gitberthe/BertheVario213/CompZoneAerienne/zones_gnuplot/000.png

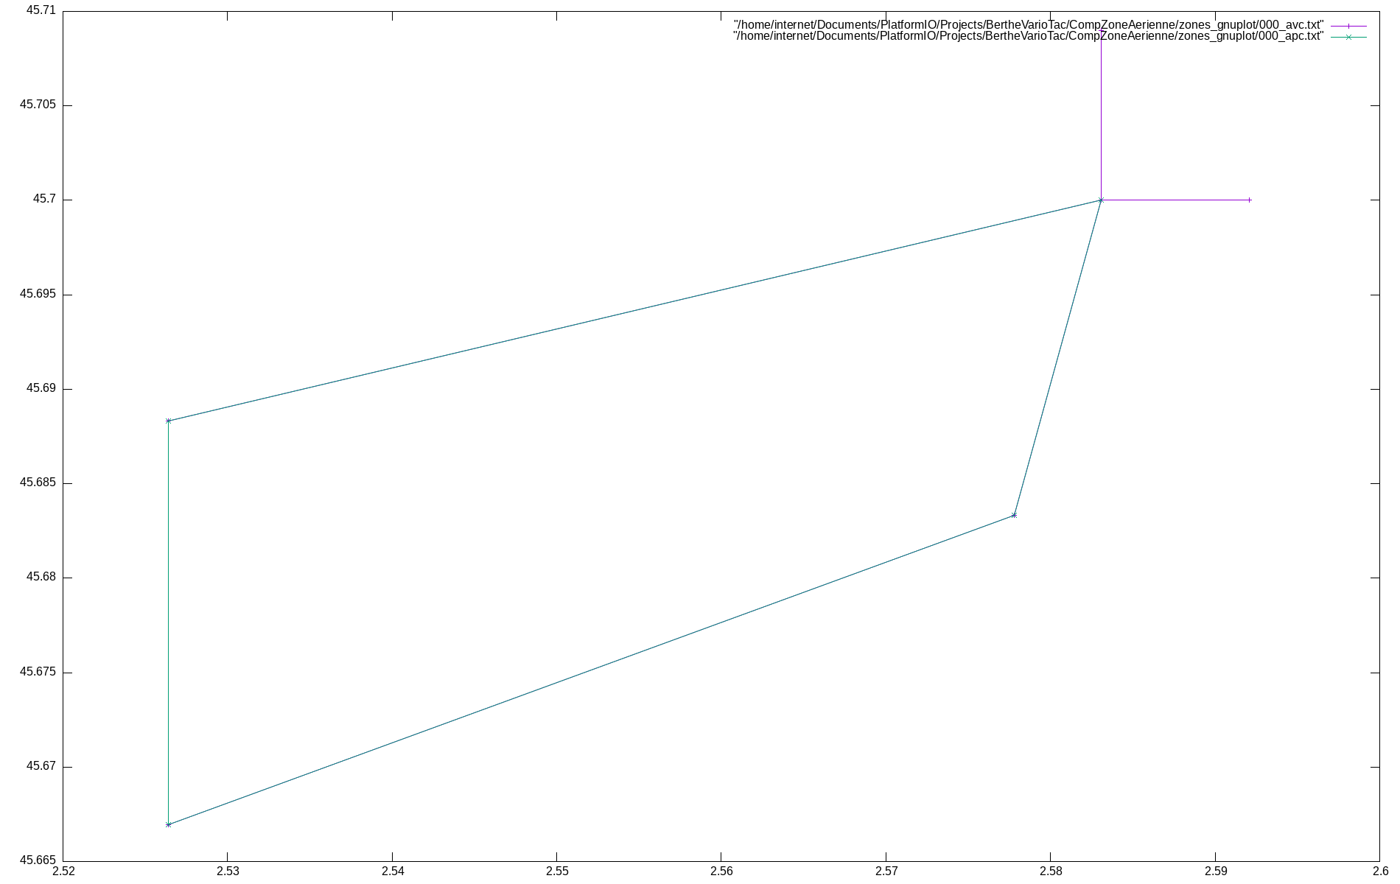
CompZoneAerienne/zones_gnuplot/000.png
