gitberthe/BertheVario213/CompZoneAerienne/zones_gnuplot/001.png

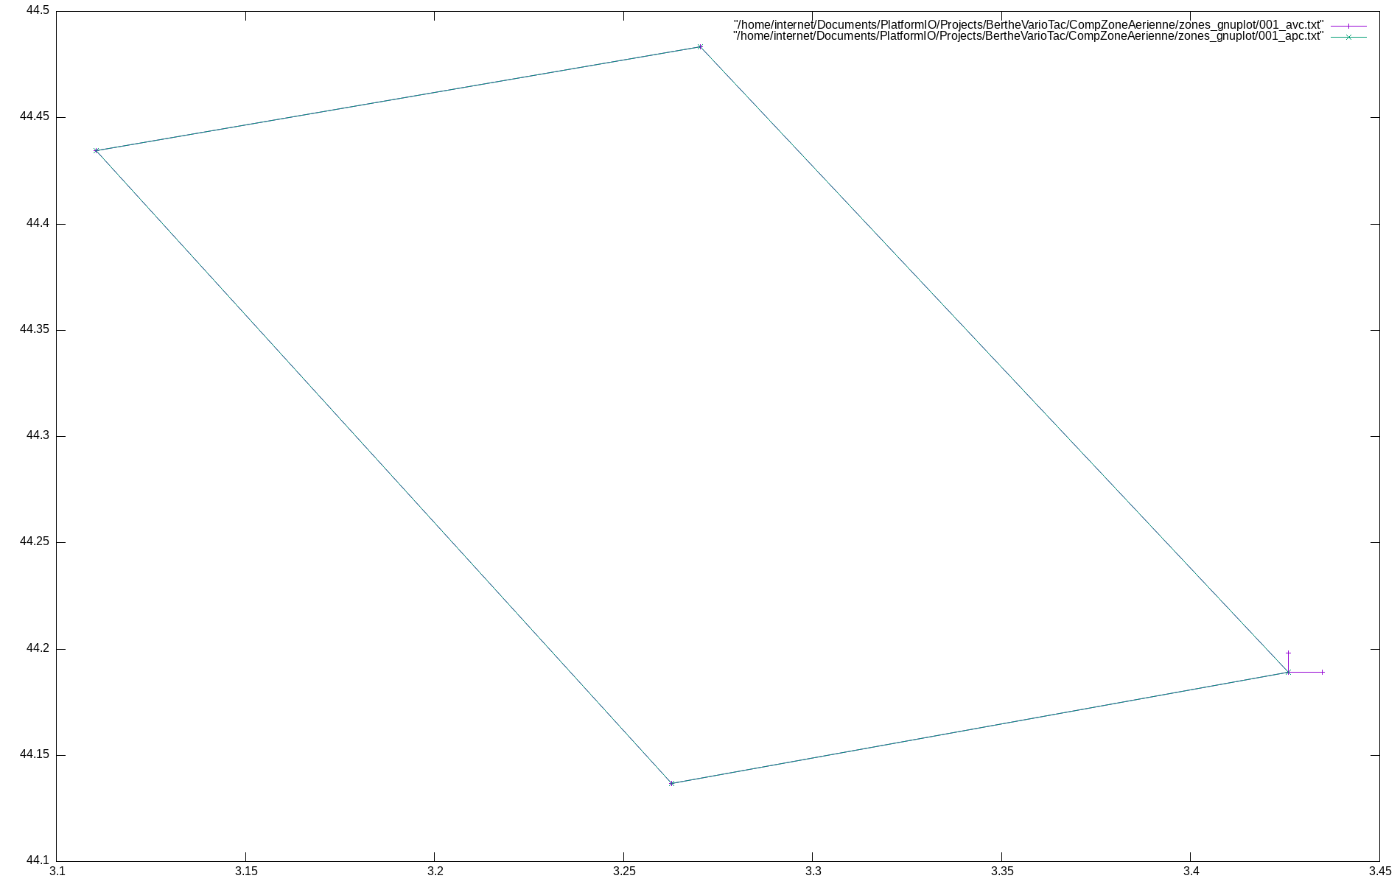
CompZoneAerienne/zones_gnuplot/001.png
