gitberthe/BertheVario213/CompZoneAerienne/zones_gnuplot/002.png

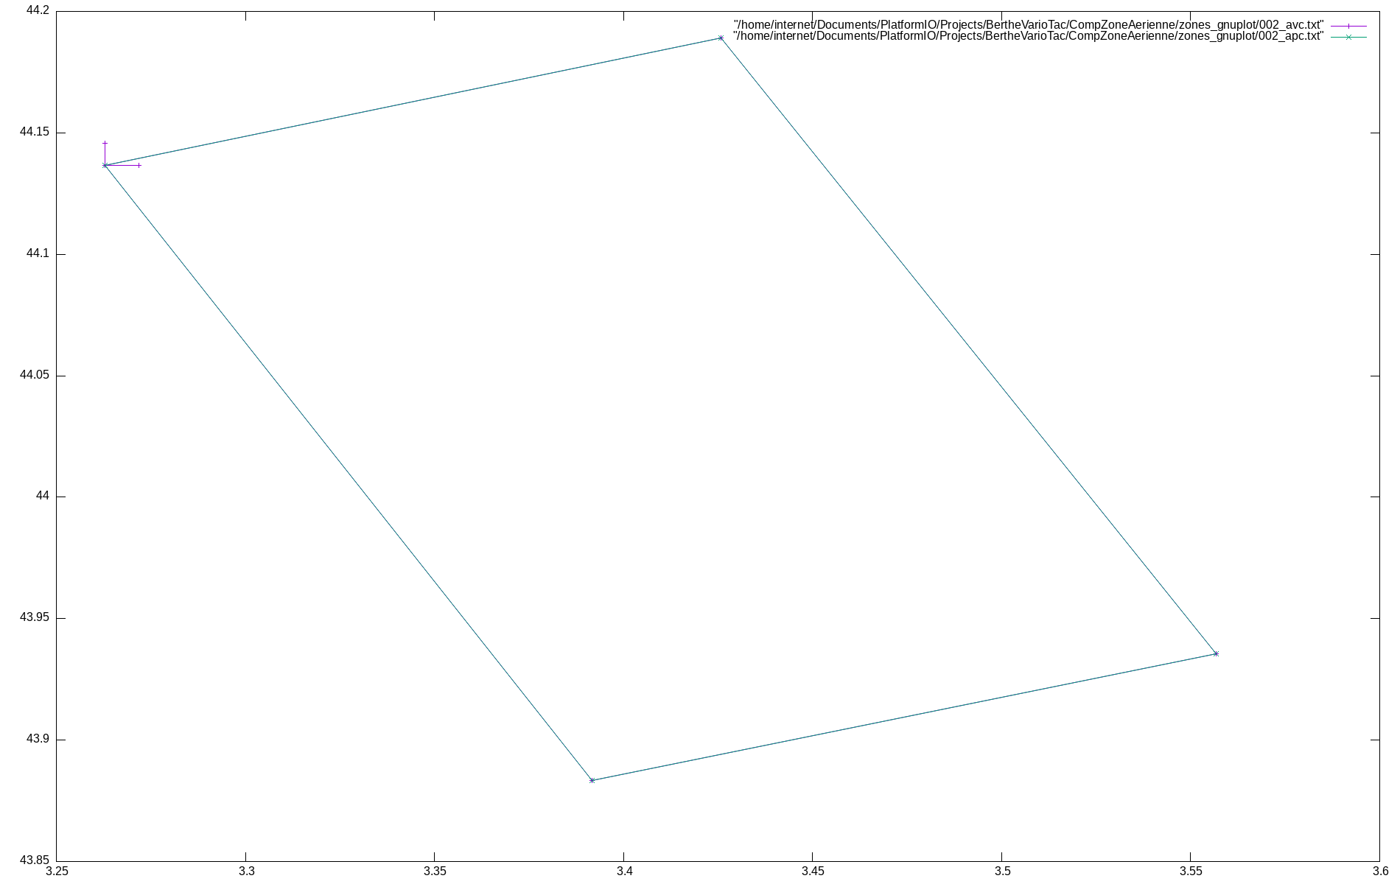
CompZoneAerienne/zones_gnuplot/002.png
