gitberthe/BertheVario213/CompZoneAerienne/zones_gnuplot/004.png

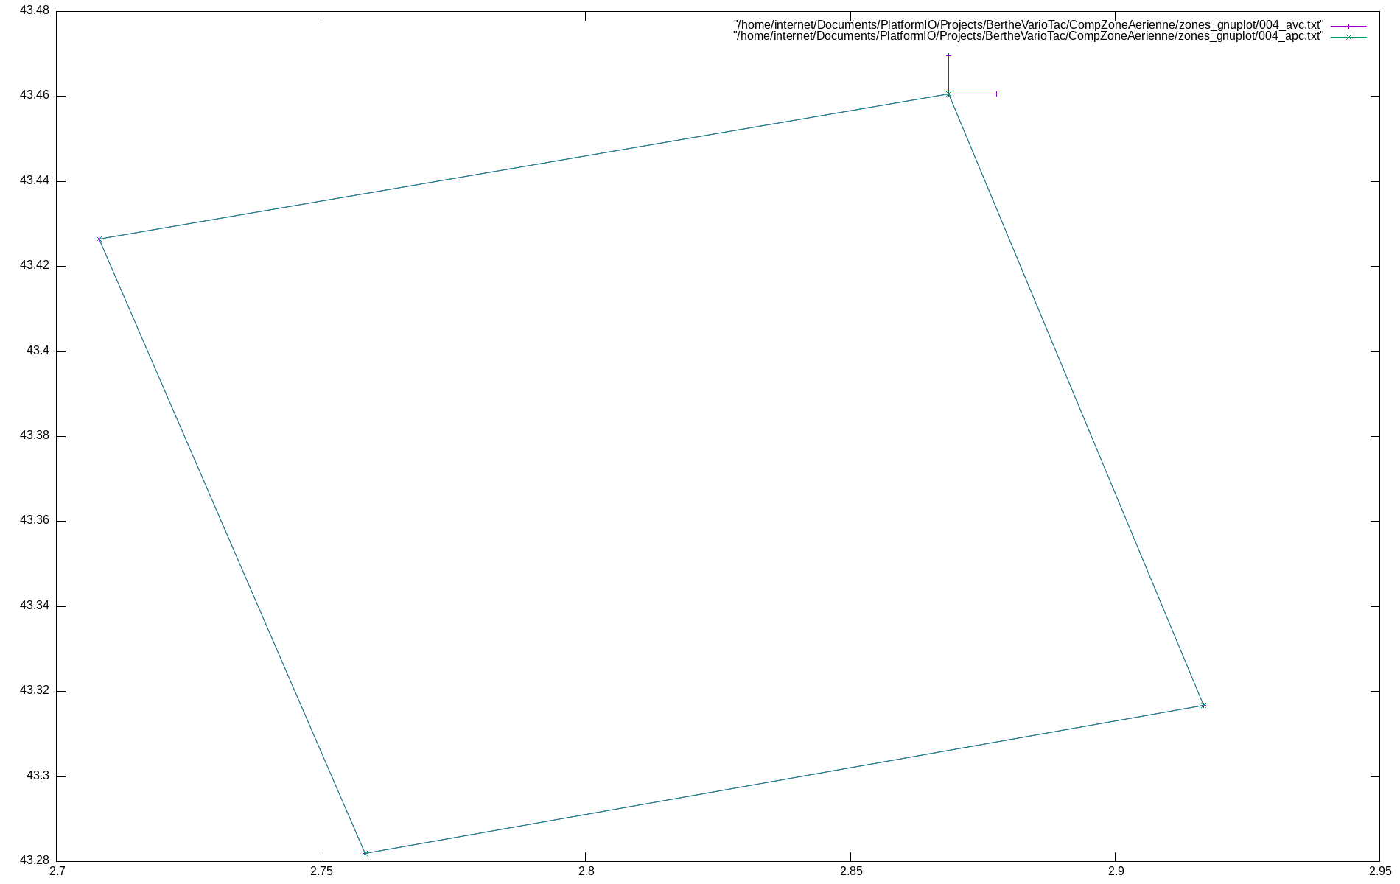
CompZoneAerienne/zones_gnuplot/004.png
