gitberthe/BertheVario213/CompZoneAerienne/zones_gnuplot/006.png

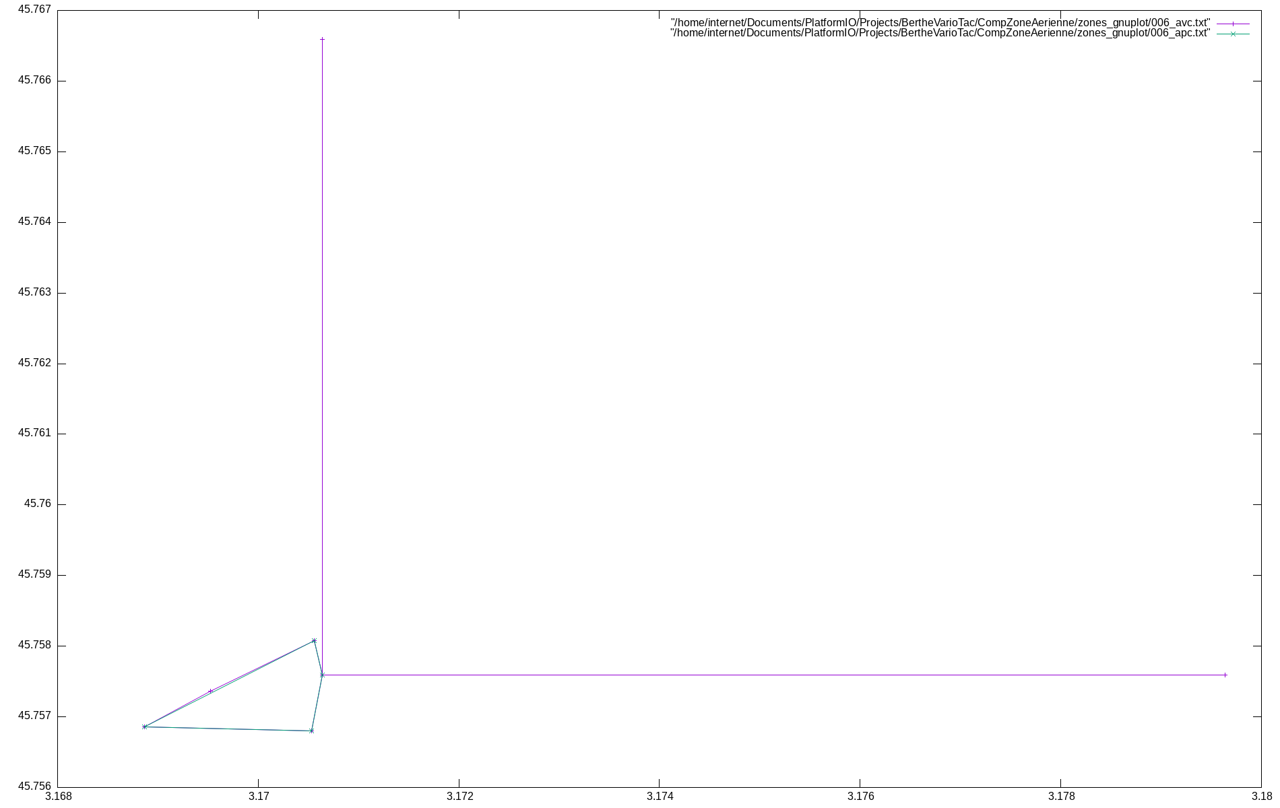
CompZoneAerienne/zones_gnuplot/006.png
