gitberthe/BertheVario213/CompZoneAerienne/zones_gnuplot/007.png

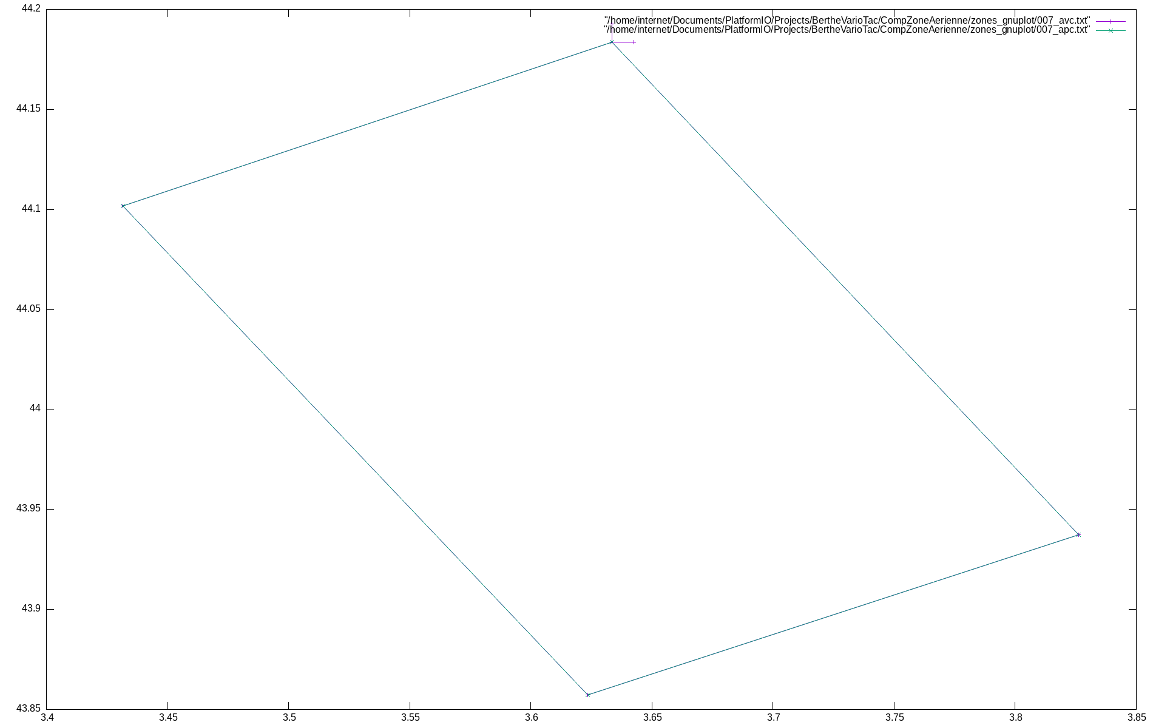
CompZoneAerienne/zones_gnuplot/007.png
