gitberthe/BertheVario213/CompZoneAerienne/zones_gnuplot/009.png

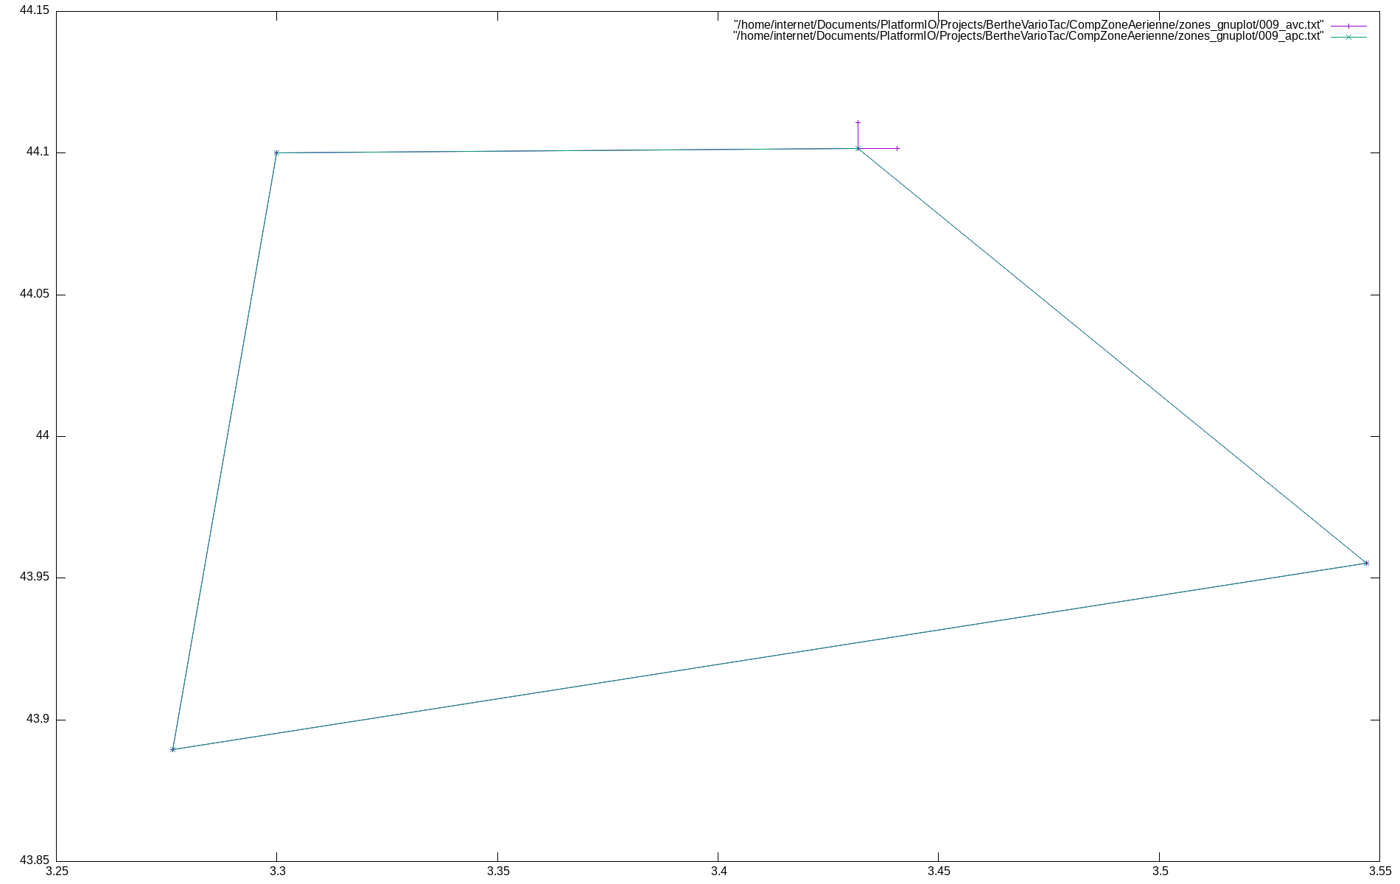
CompZoneAerienne/zones_gnuplot/009.png
