gitberthe/BertheVario213/CompZoneAerienne/zones_gnuplot/010.png

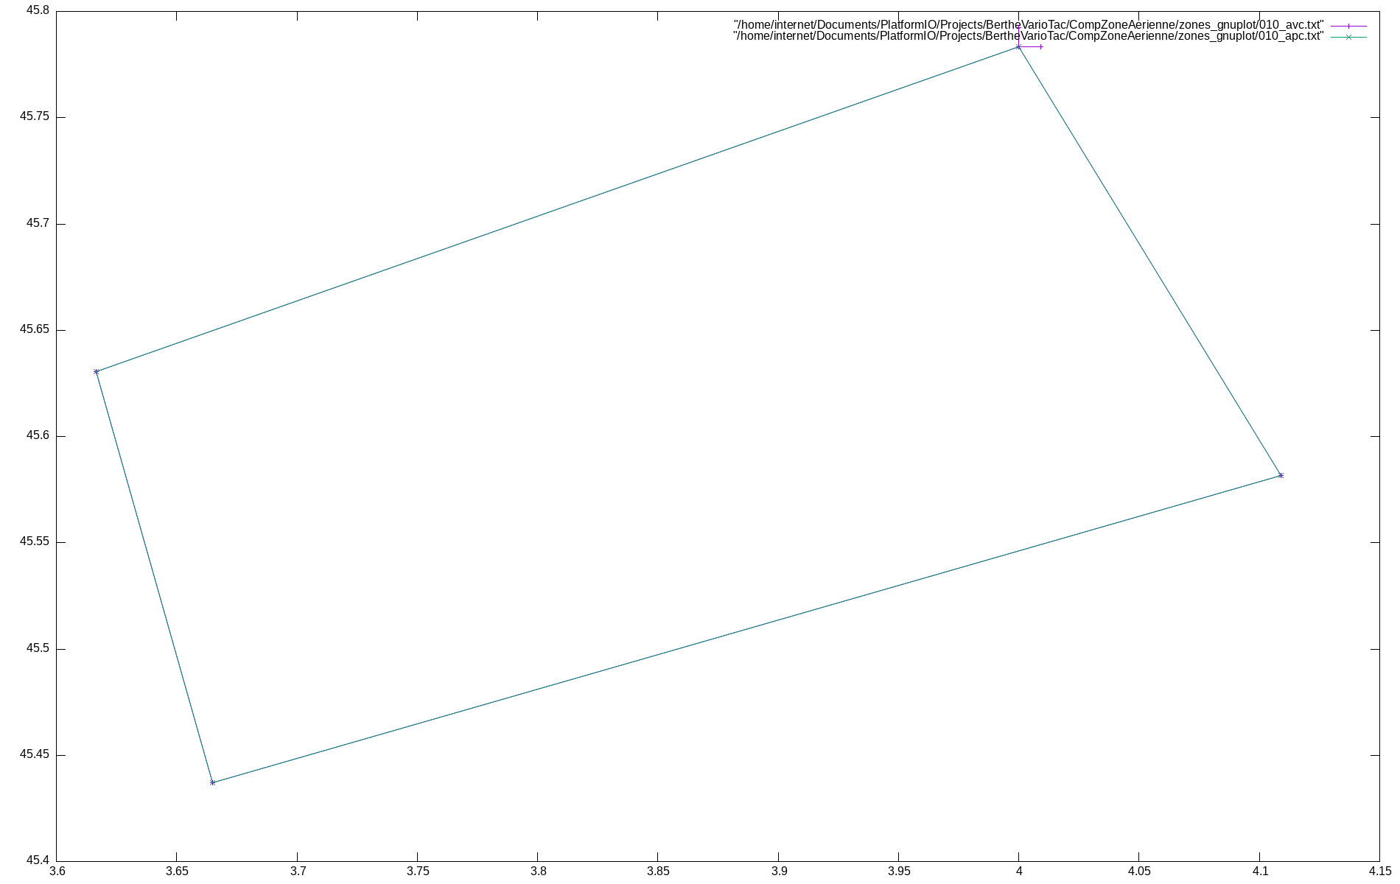
CompZoneAerienne/zones_gnuplot/010.png
