gitberthe/BertheVario213/CompZoneAerienne/zones_gnuplot/012.png

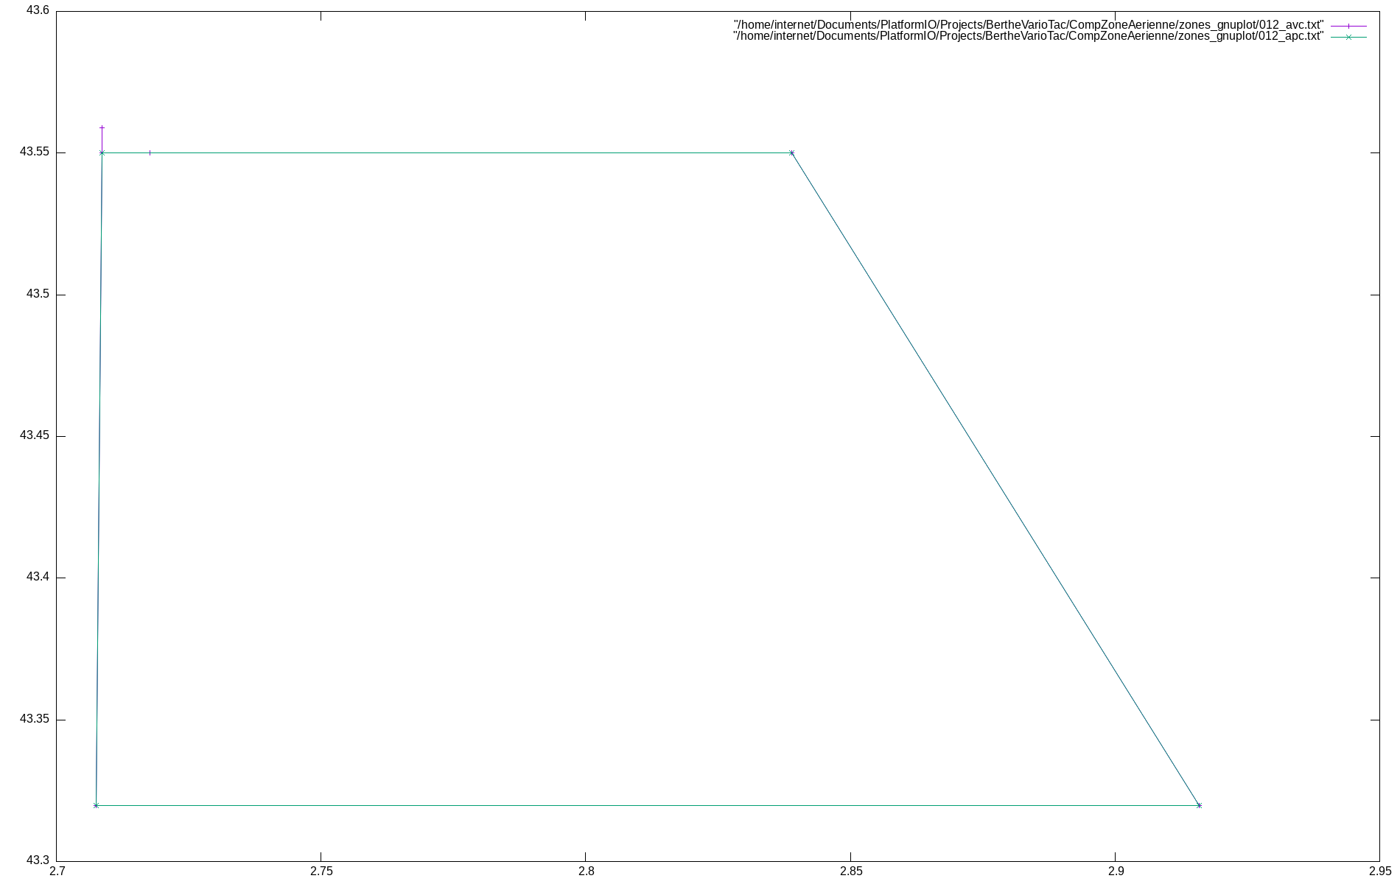
CompZoneAerienne/zones_gnuplot/012.png
