gitberthe/BertheVario213/CompZoneAerienne/zones_gnuplot/013.png

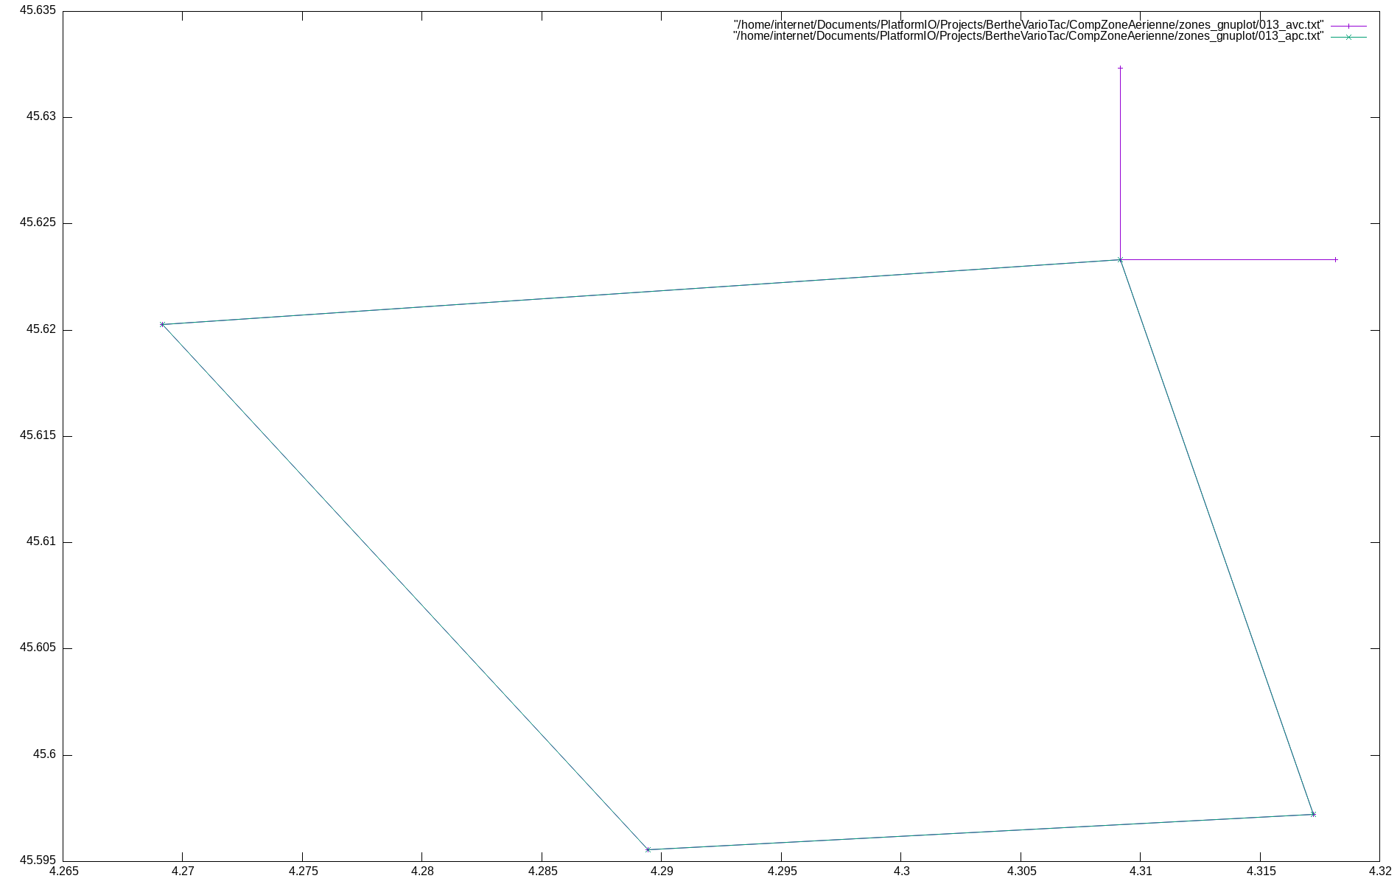
CompZoneAerienne/zones_gnuplot/013.png
