gitberthe/BertheVario213/CompZoneAerienne/zones_gnuplot/014.png

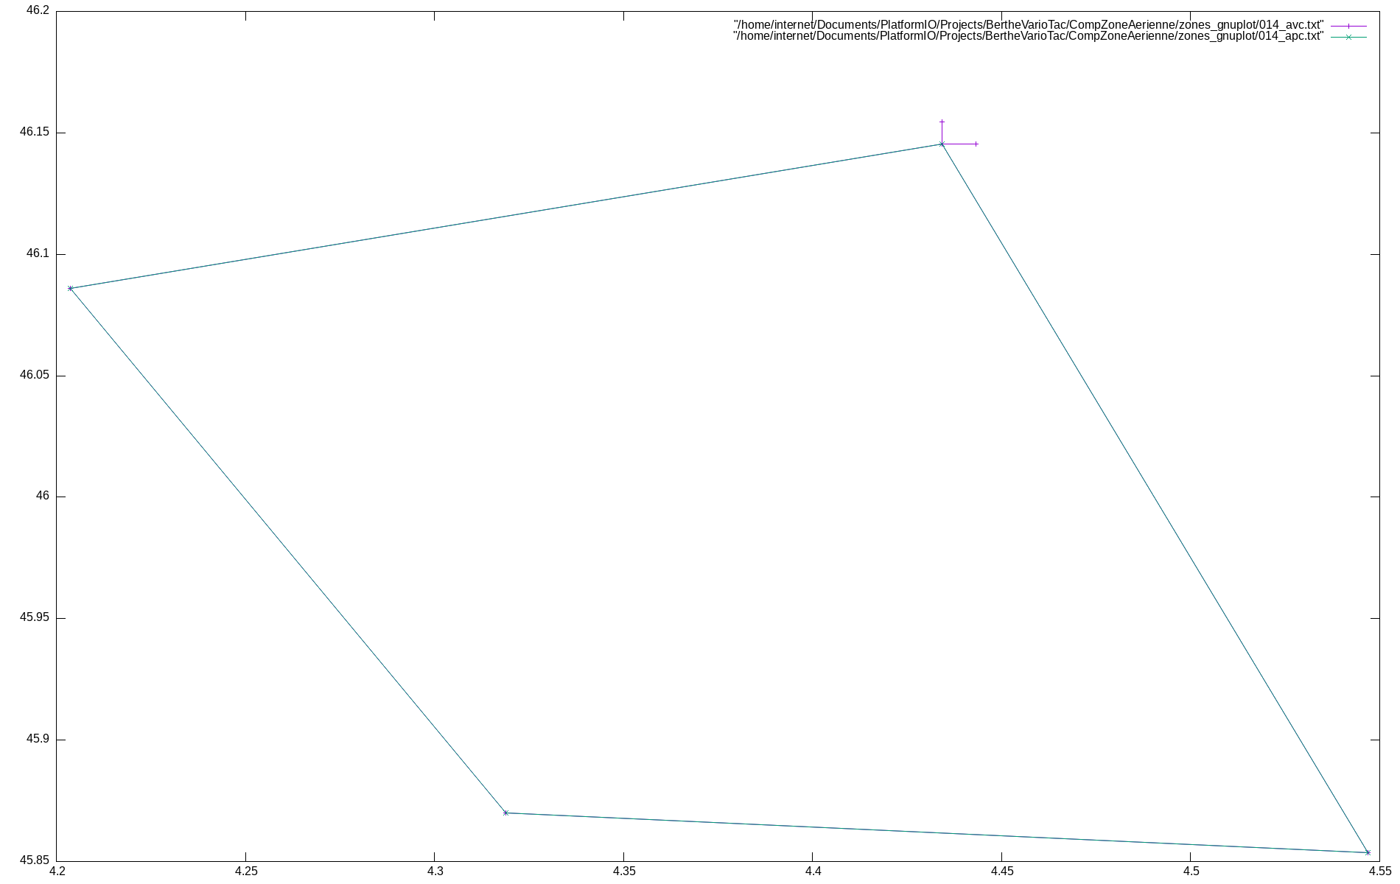
CompZoneAerienne/zones_gnuplot/014.png
