gitberthe/BertheVario213/CompZoneAerienne/zones_gnuplot/015.png

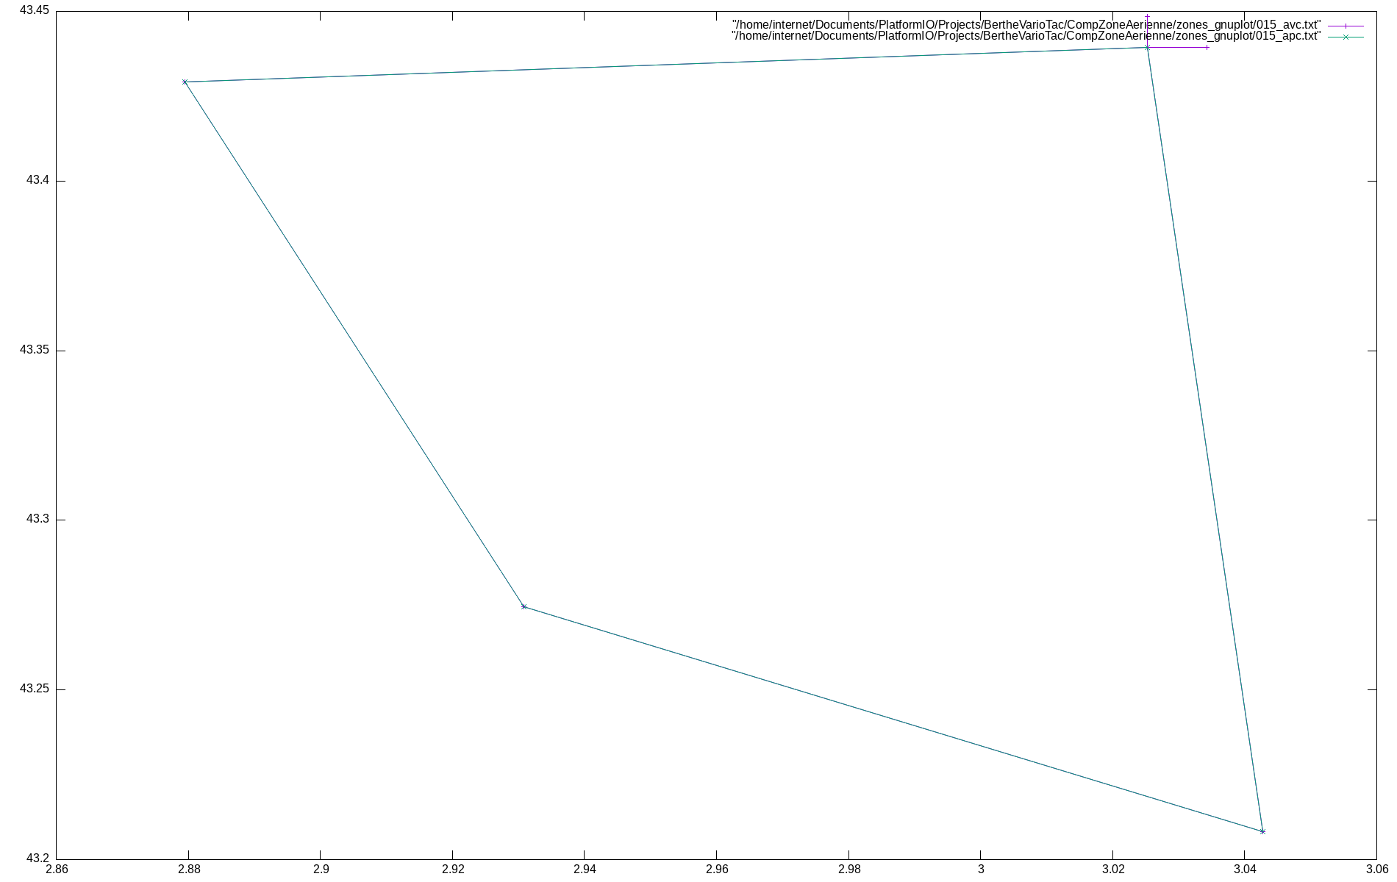
CompZoneAerienne/zones_gnuplot/015.png
