gitberthe/BertheVario213/CompZoneAerienne/zones_gnuplot/016.png

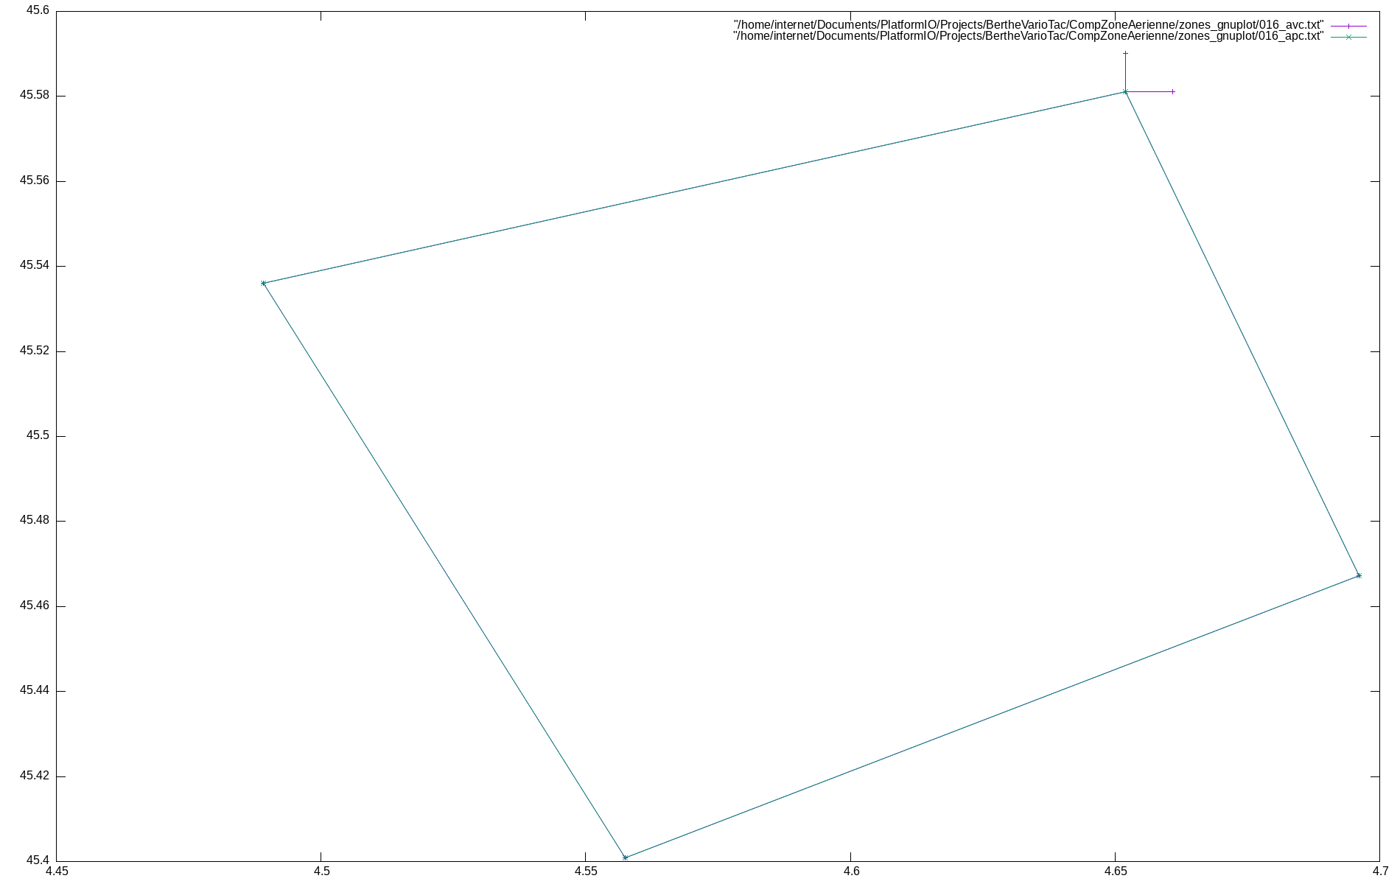
CompZoneAerienne/zones_gnuplot/016.png
