gitberthe/BertheVario213/CompZoneAerienne/zones_gnuplot/017.png

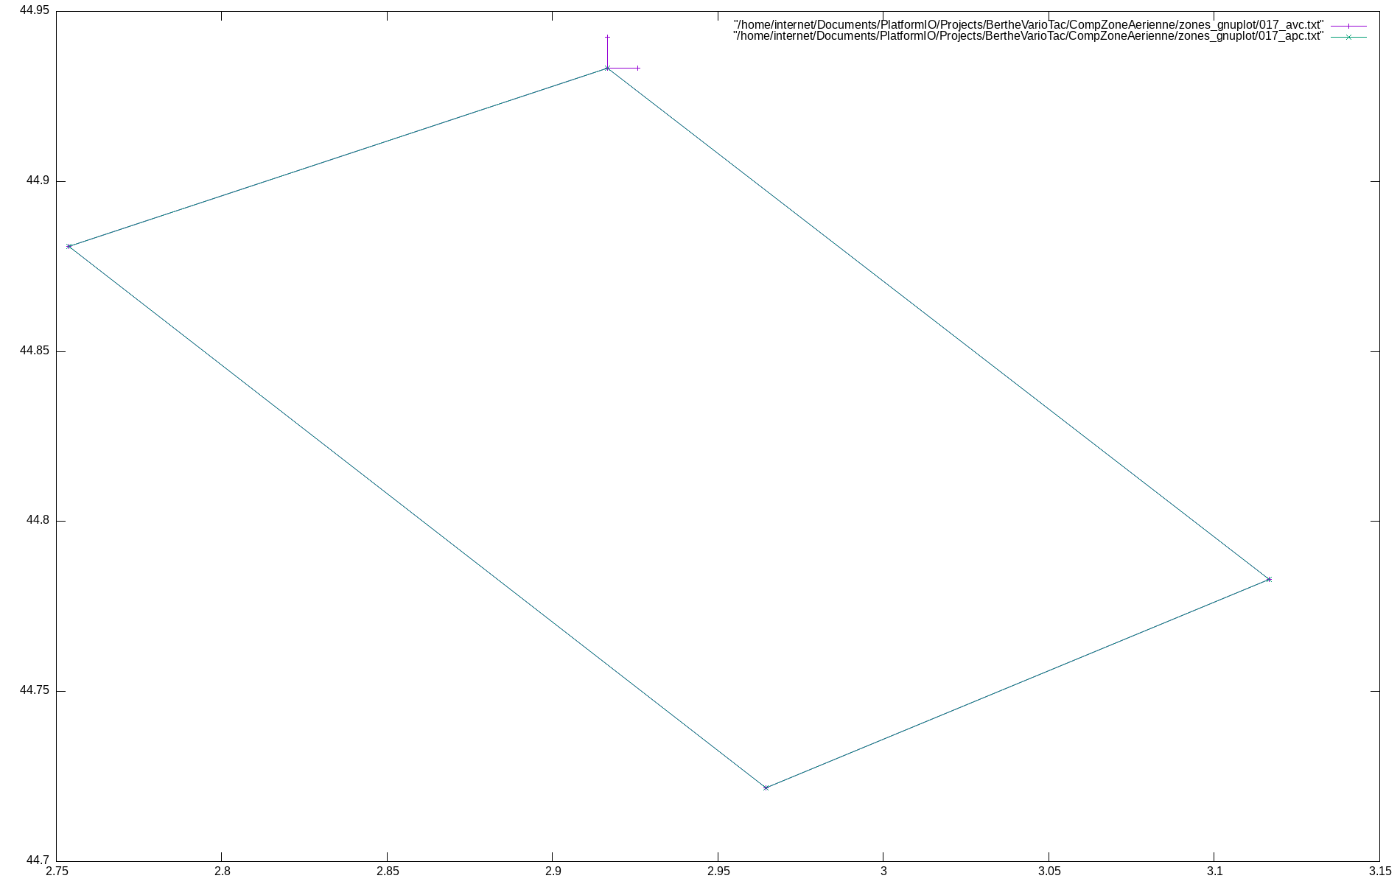
CompZoneAerienne/zones_gnuplot/017.png
