gitberthe/BertheVario213/CompZoneAerienne/zones_gnuplot/019.png

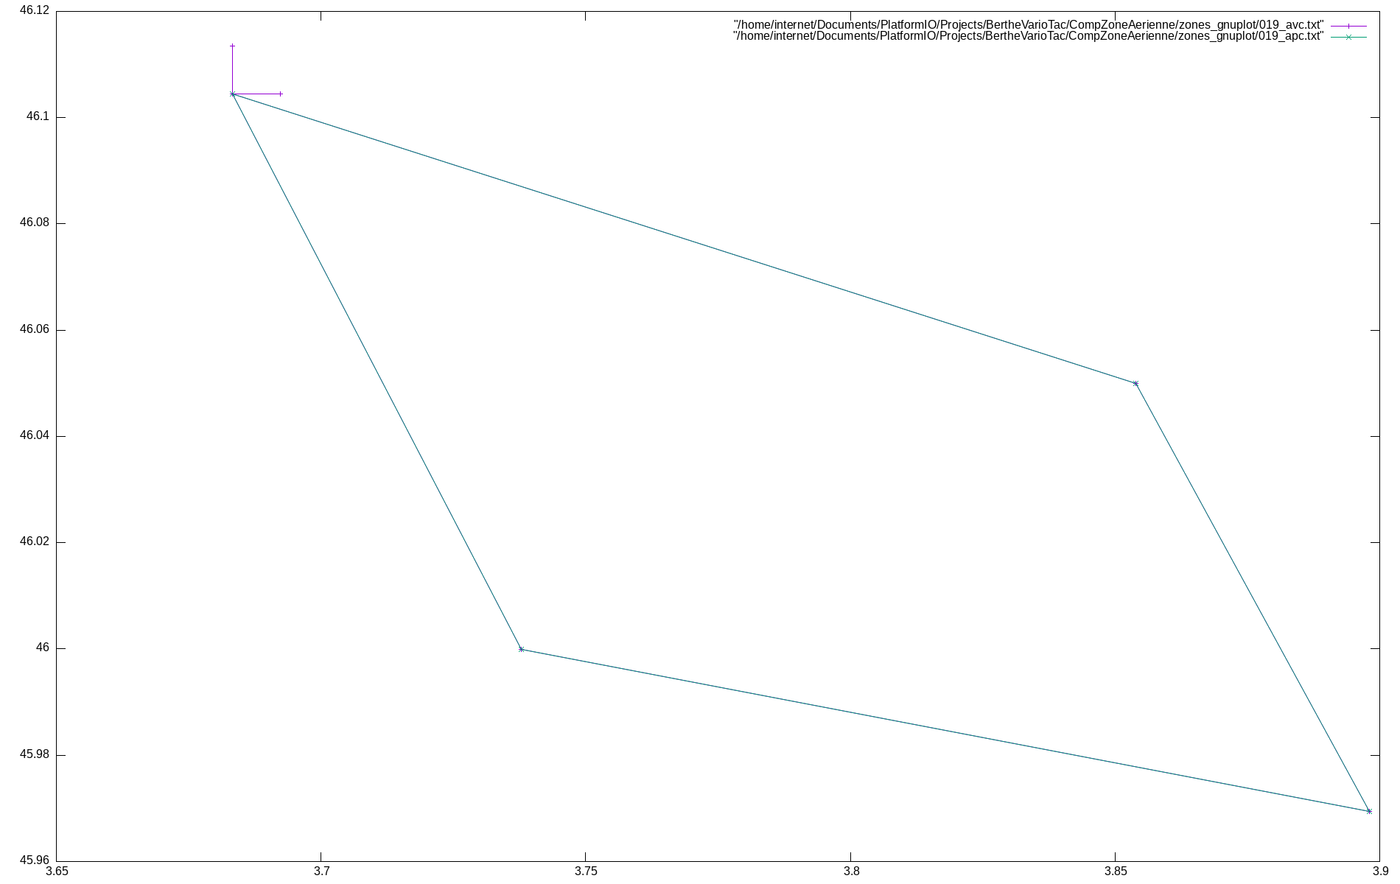
CompZoneAerienne/zones_gnuplot/019.png
