gitberthe/BertheVario213/CompZoneAerienne/zones_gnuplot/020.png

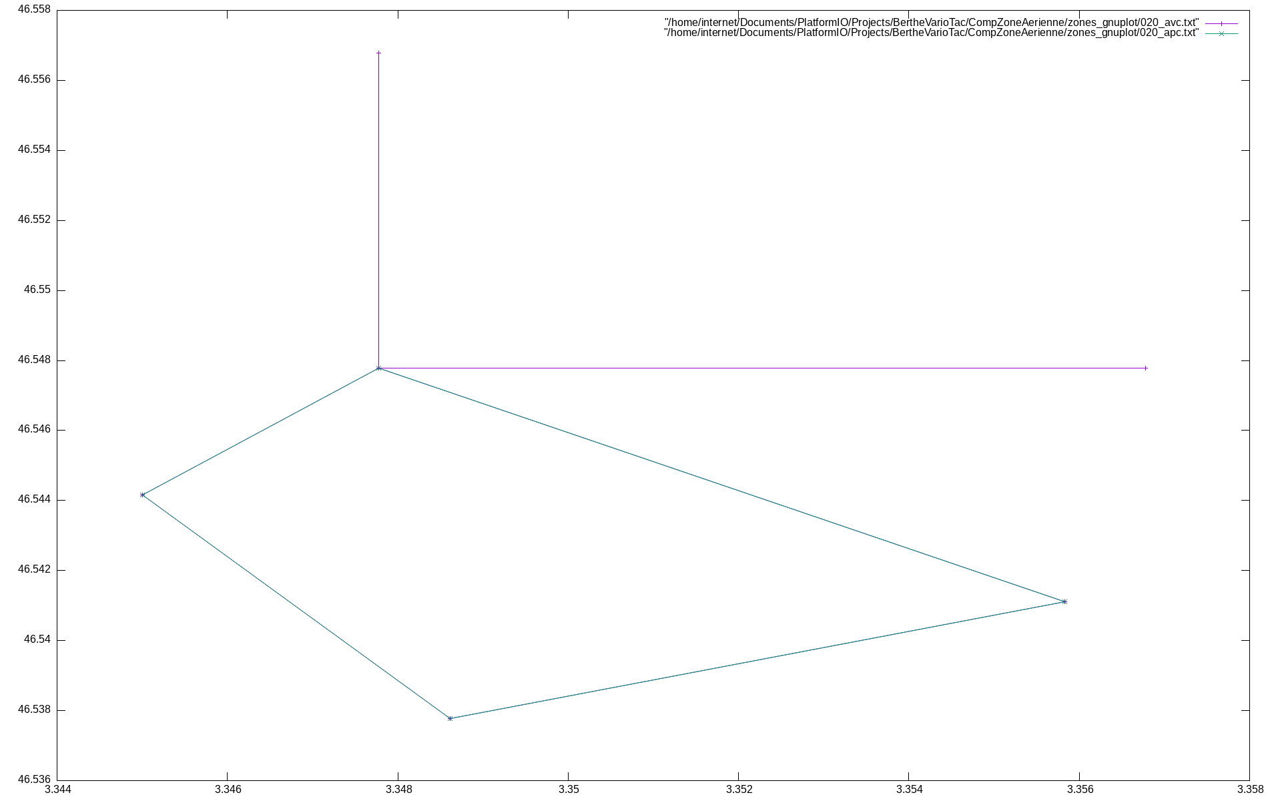
CompZoneAerienne/zones_gnuplot/020.png
