gitberthe/BertheVario213/CompZoneAerienne/zones_gnuplot/022.png

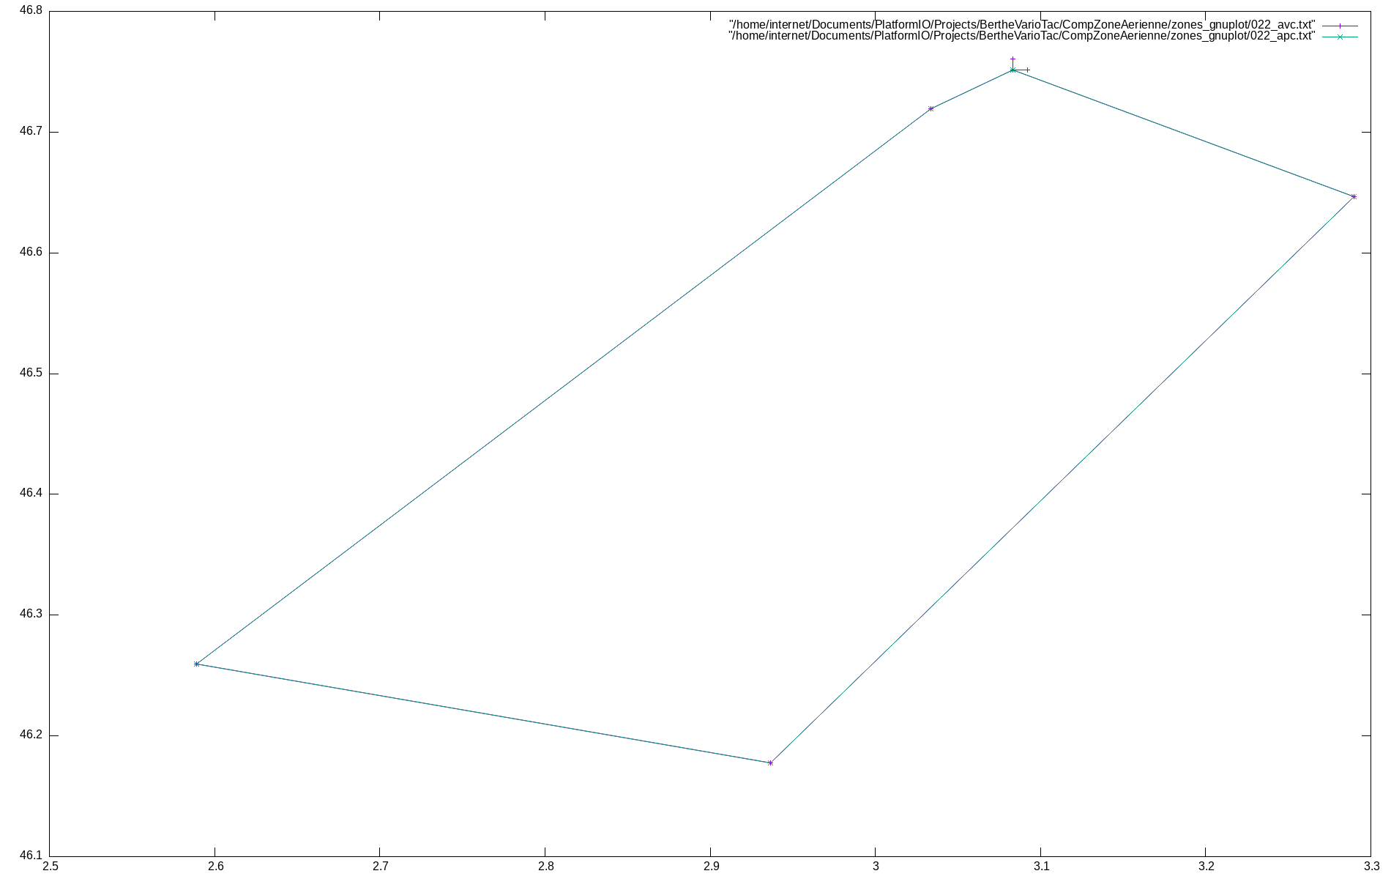
CompZoneAerienne/zones_gnuplot/022.png
