gitberthe/BertheVario213/CompZoneAerienne/zones_gnuplot/023.png

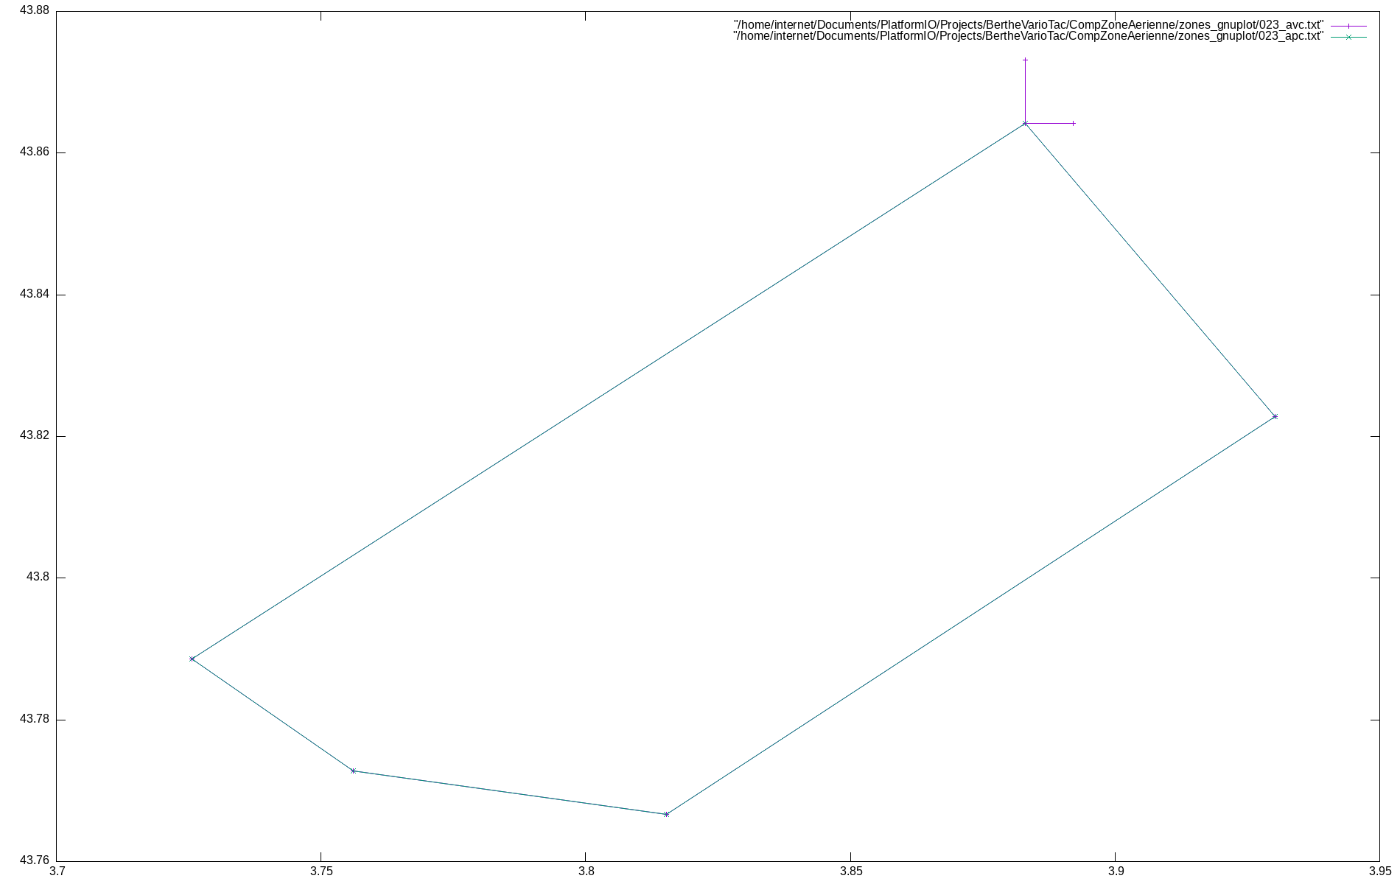
CompZoneAerienne/zones_gnuplot/023.png
