gitberthe/BertheVario213/CompZoneAerienne/zones_gnuplot/025.png

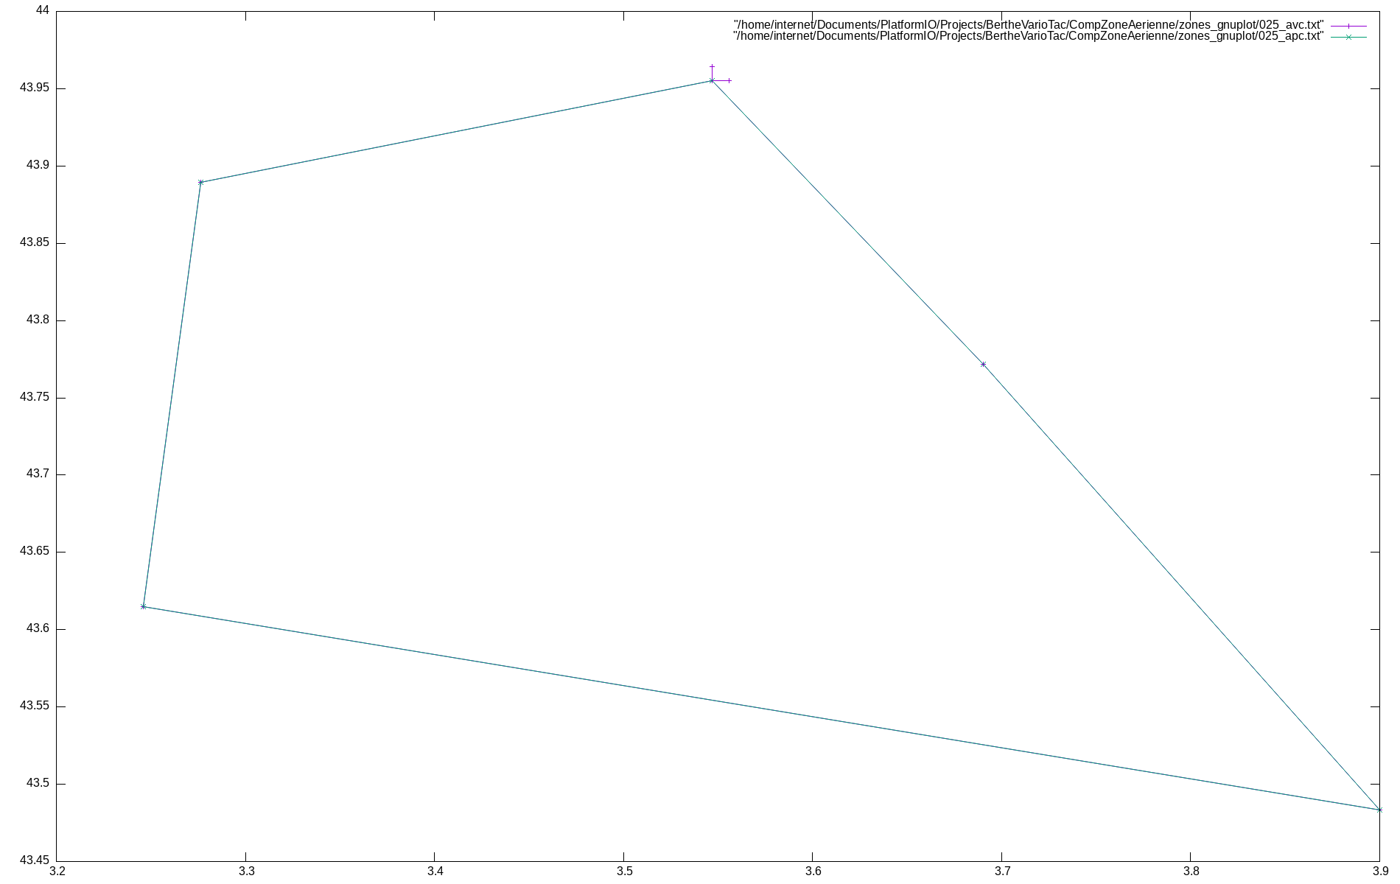
CompZoneAerienne/zones_gnuplot/025.png
