gitberthe/BertheVario213/CompZoneAerienne/zones_gnuplot/026.png

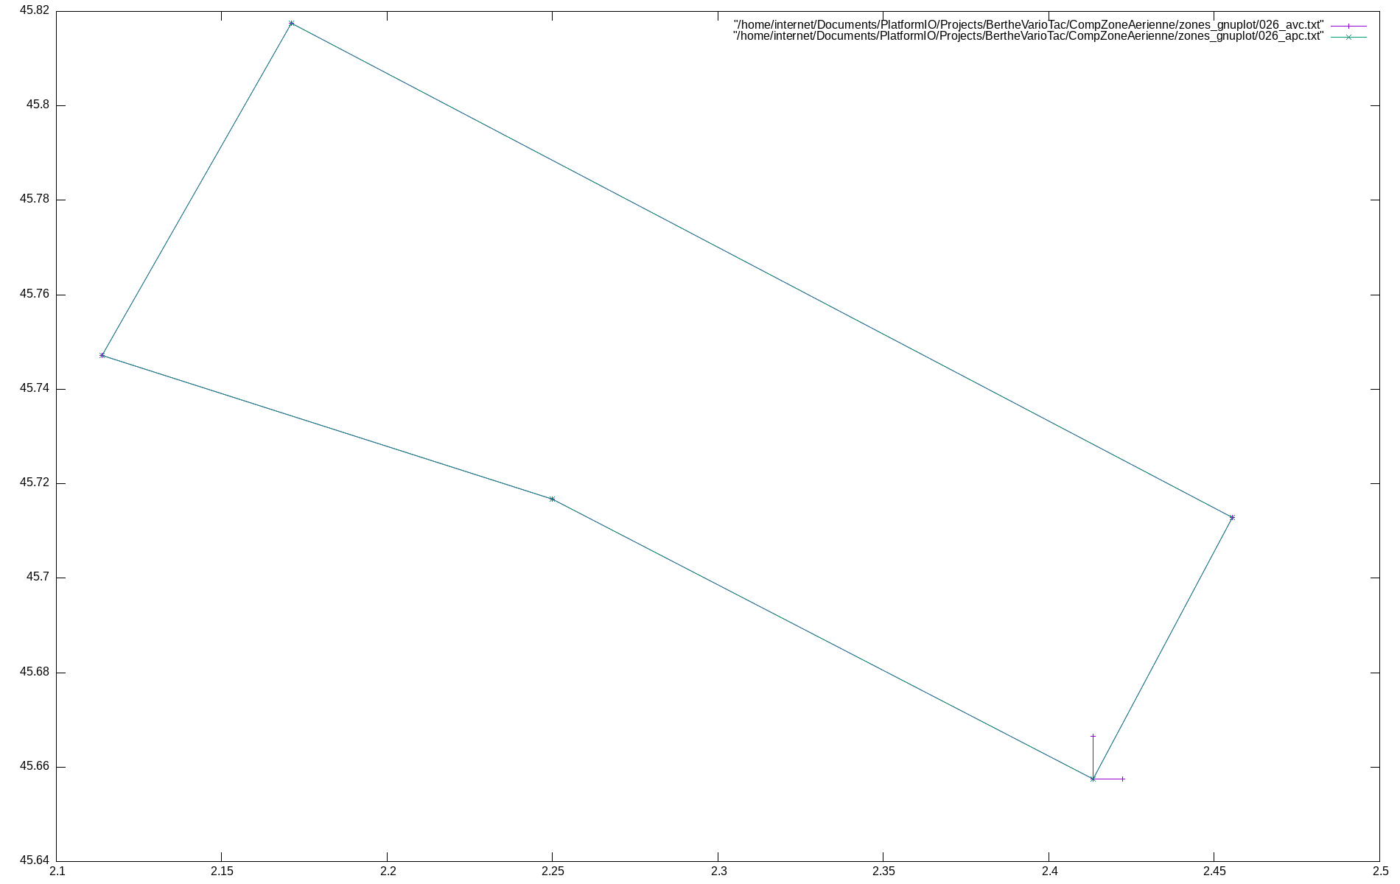
CompZoneAerienne/zones_gnuplot/026.png
