gitberthe/BertheVario213/CompZoneAerienne/zones_gnuplot/030.png

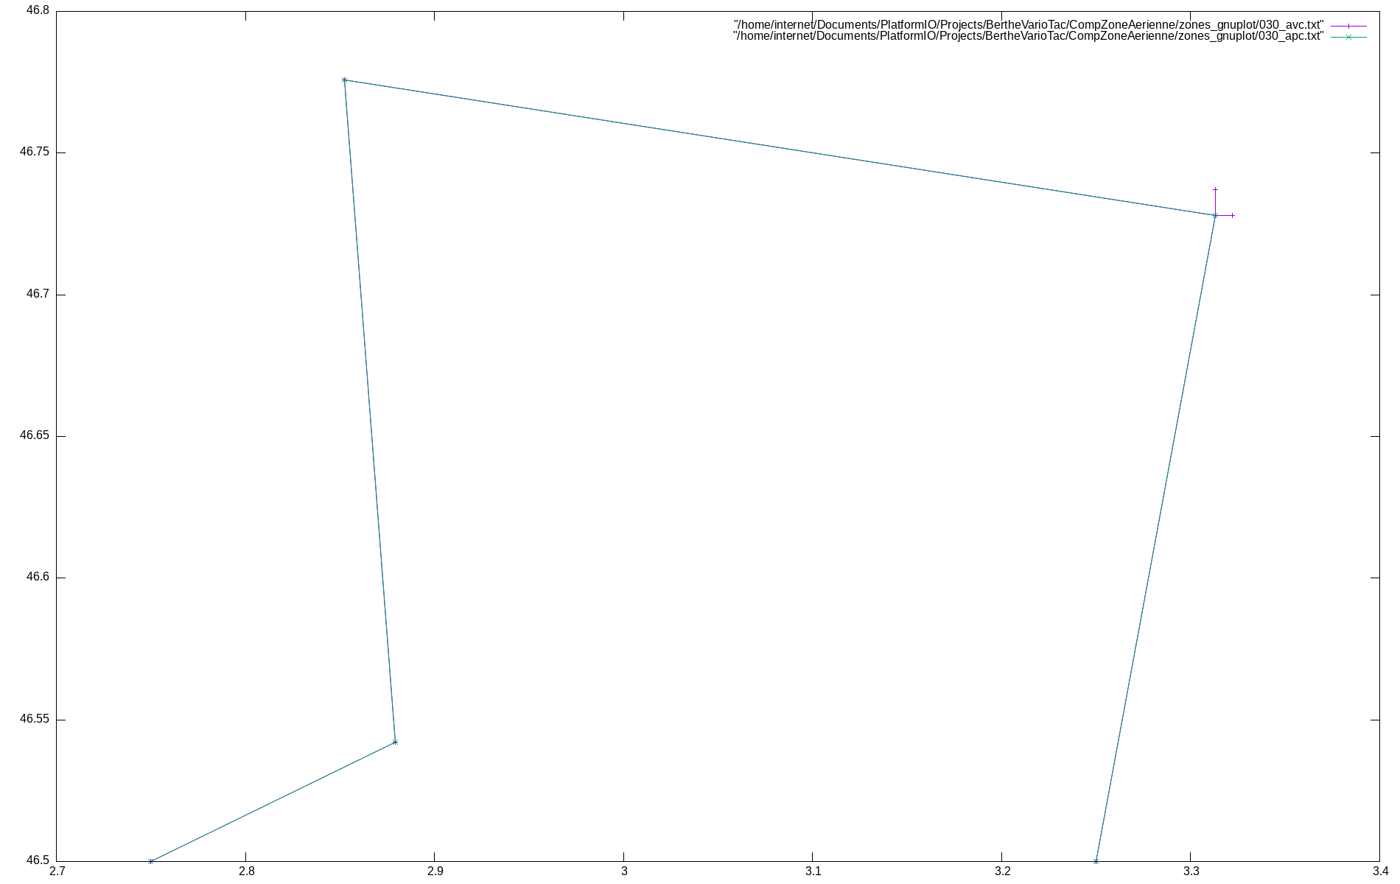
CompZoneAerienne/zones_gnuplot/030.png
