gitberthe/BertheVario213/CompZoneAerienne/zones_gnuplot/033.png

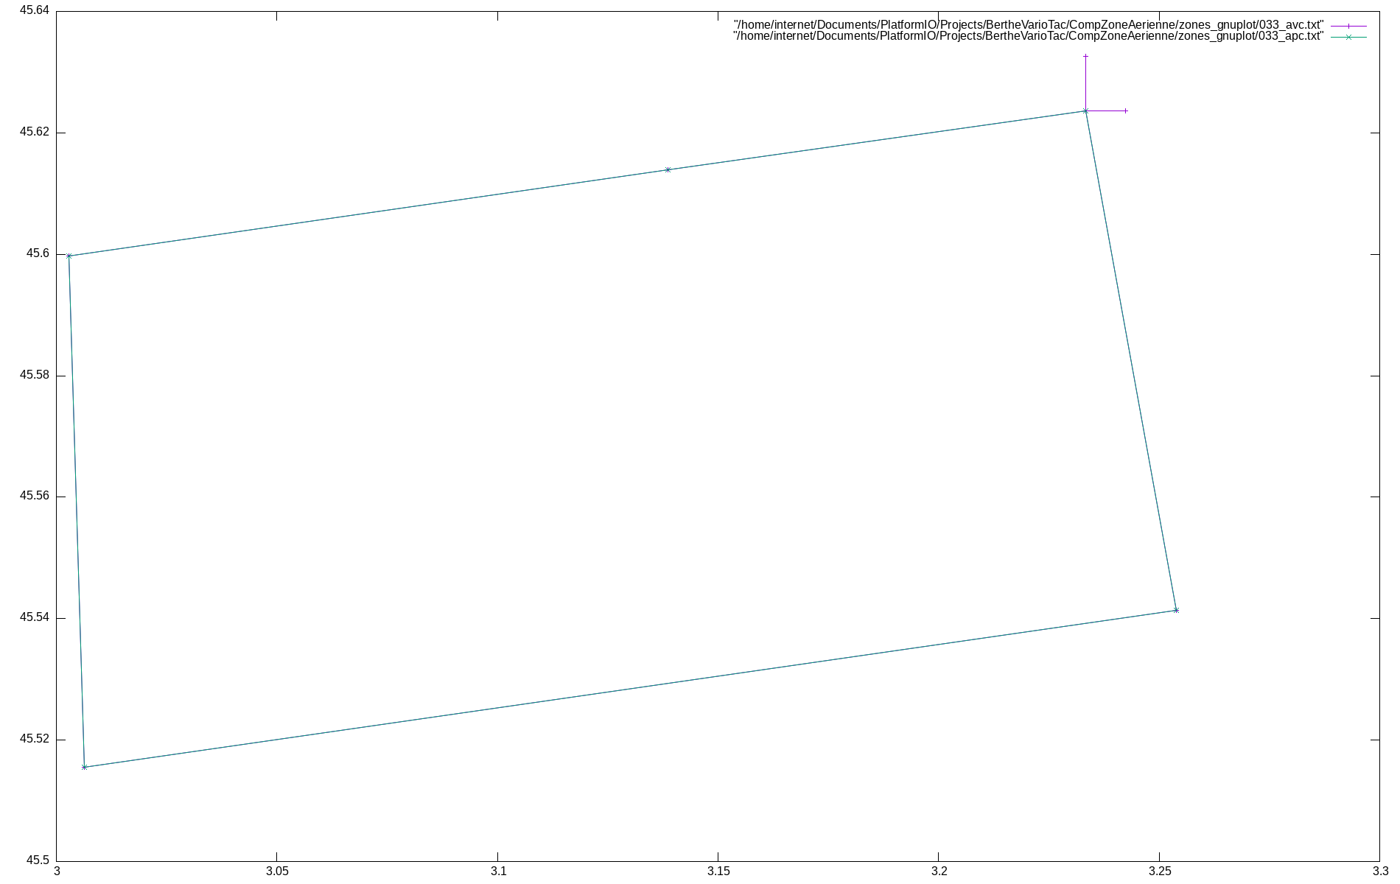
CompZoneAerienne/zones_gnuplot/033.png
