gitberthe/BertheVario213/CompZoneAerienne/zones_gnuplot/034.png

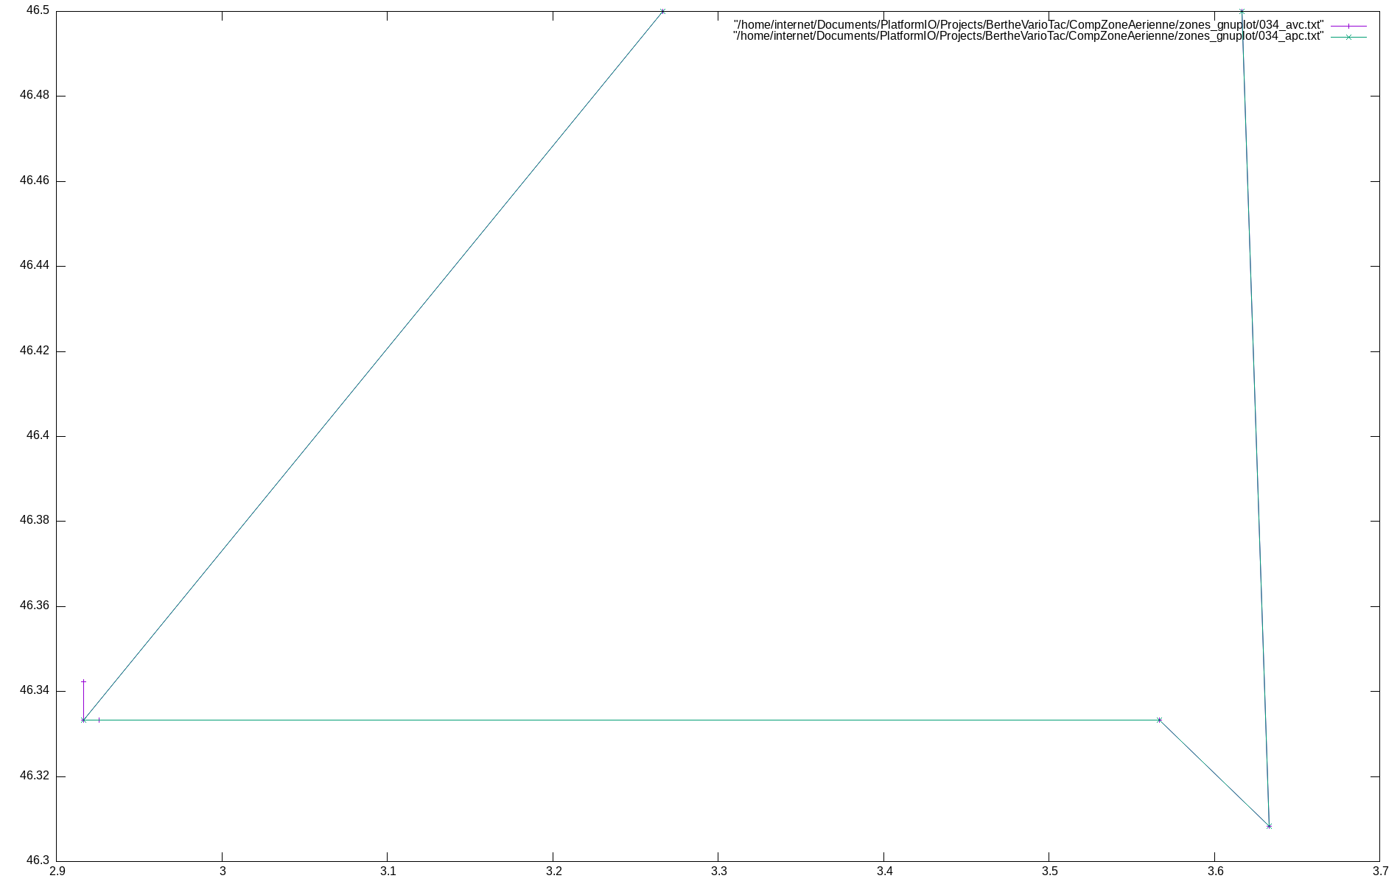
CompZoneAerienne/zones_gnuplot/034.png
