gitberthe/BertheVario213/CompZoneAerienne/zones_gnuplot/036.png

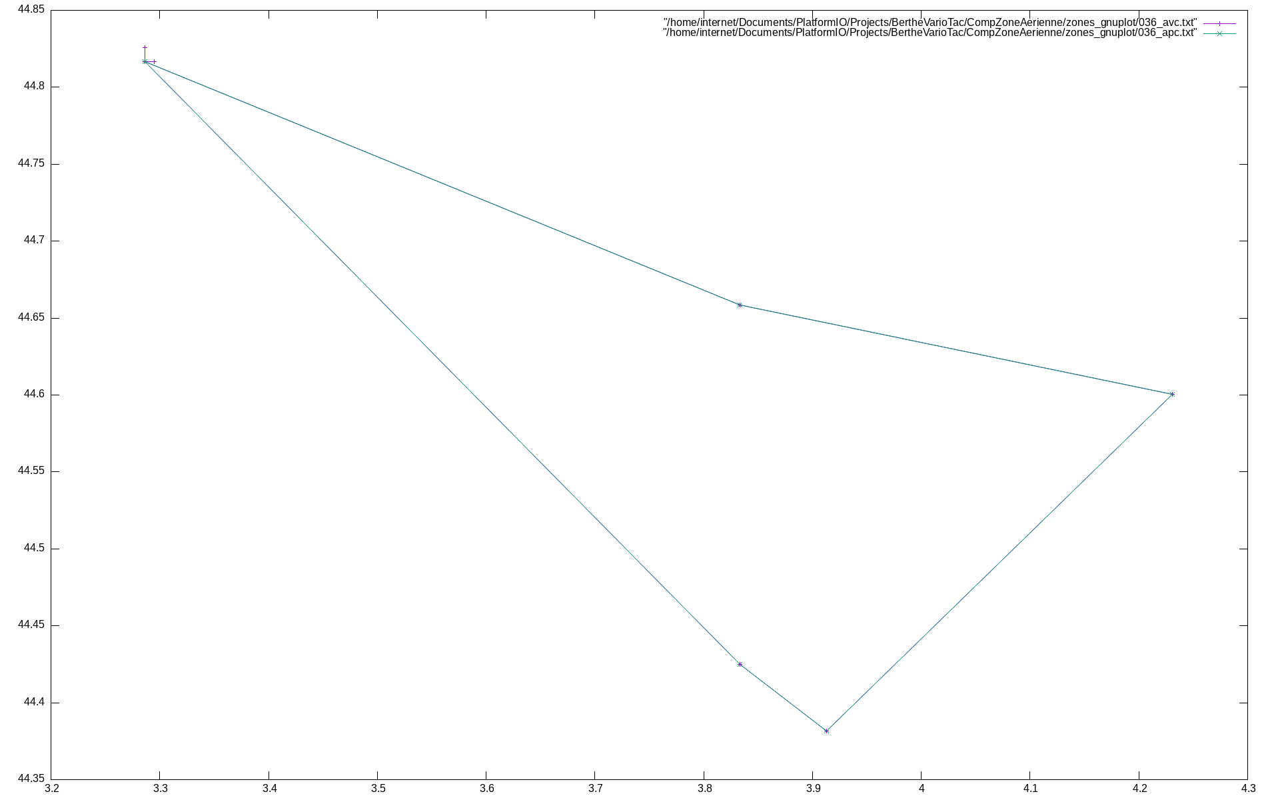
CompZoneAerienne/zones_gnuplot/036.png
