gitberthe/BertheVario213/CompZoneAerienne/zones_gnuplot/037.png

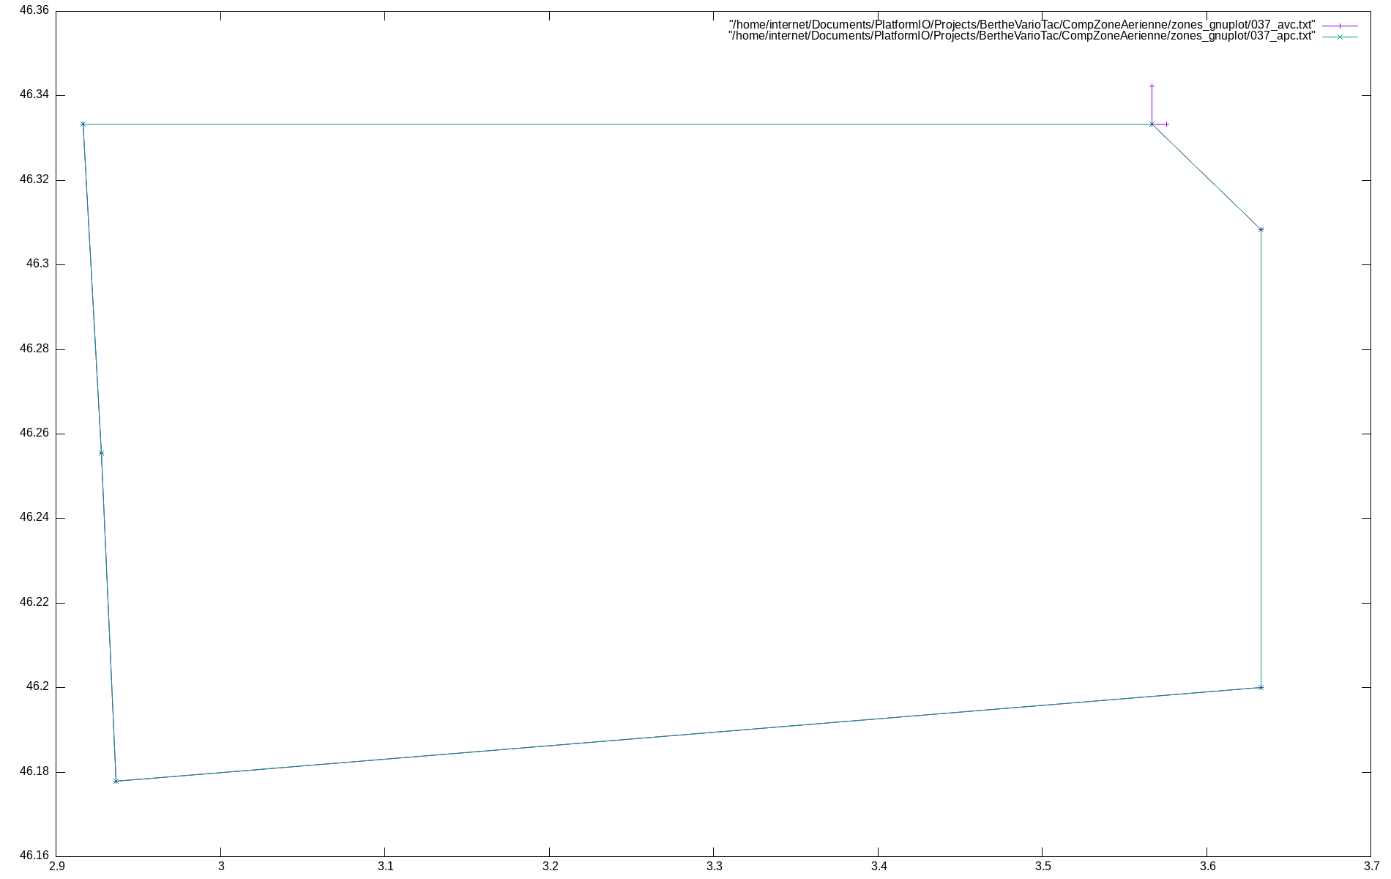
CompZoneAerienne/zones_gnuplot/037.png
