gitberthe/BertheVario213/CompZoneAerienne/zones_gnuplot/038.png

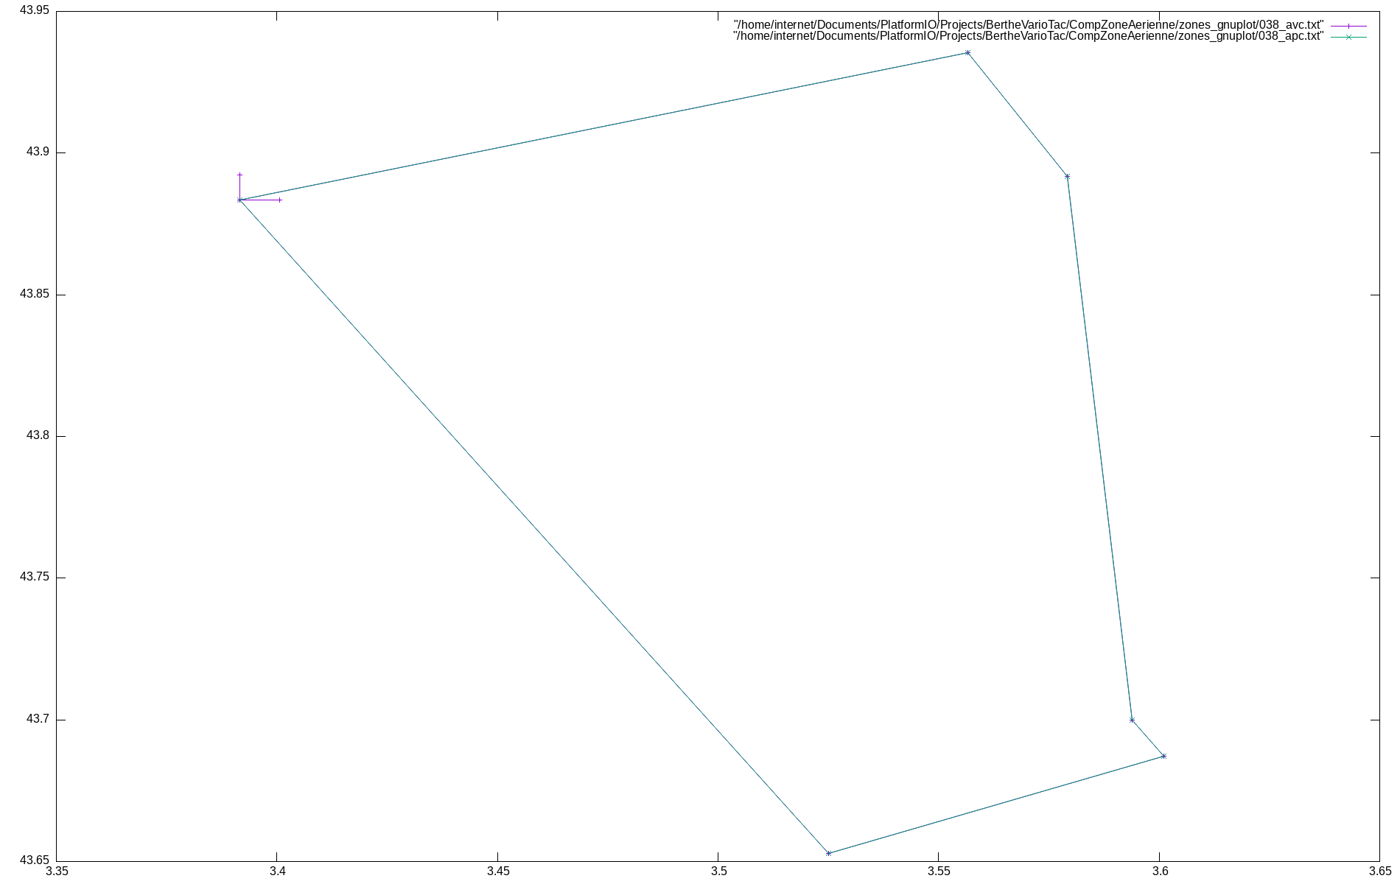
CompZoneAerienne/zones_gnuplot/038.png
