gitberthe/BertheVario213/CompZoneAerienne/zones_gnuplot/039.png

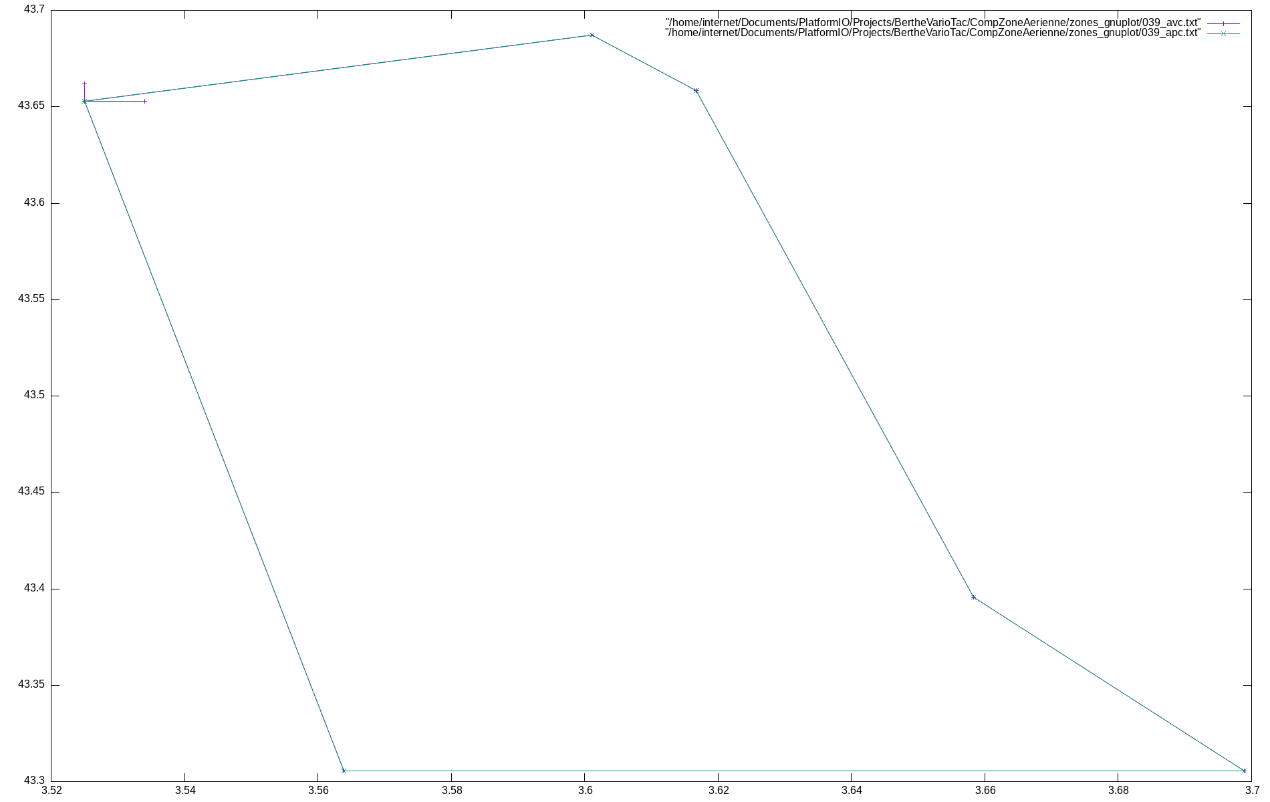
CompZoneAerienne/zones_gnuplot/039.png
