gitberthe/BertheVario213/CompZoneAerienne/zones_gnuplot/040.png

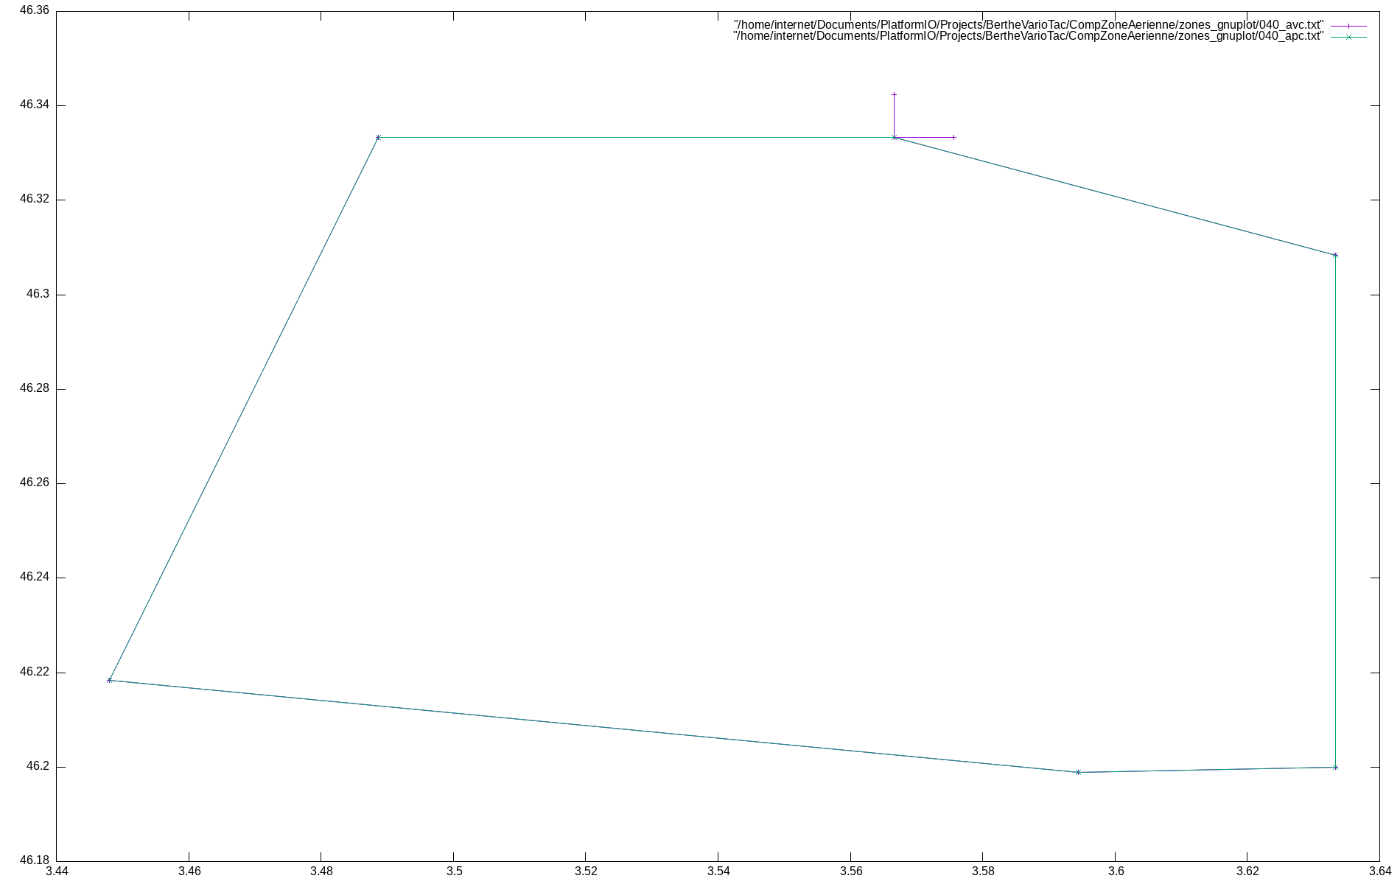
CompZoneAerienne/zones_gnuplot/040.png
