gitberthe/BertheVario213/CompZoneAerienne/zones_gnuplot/041.png

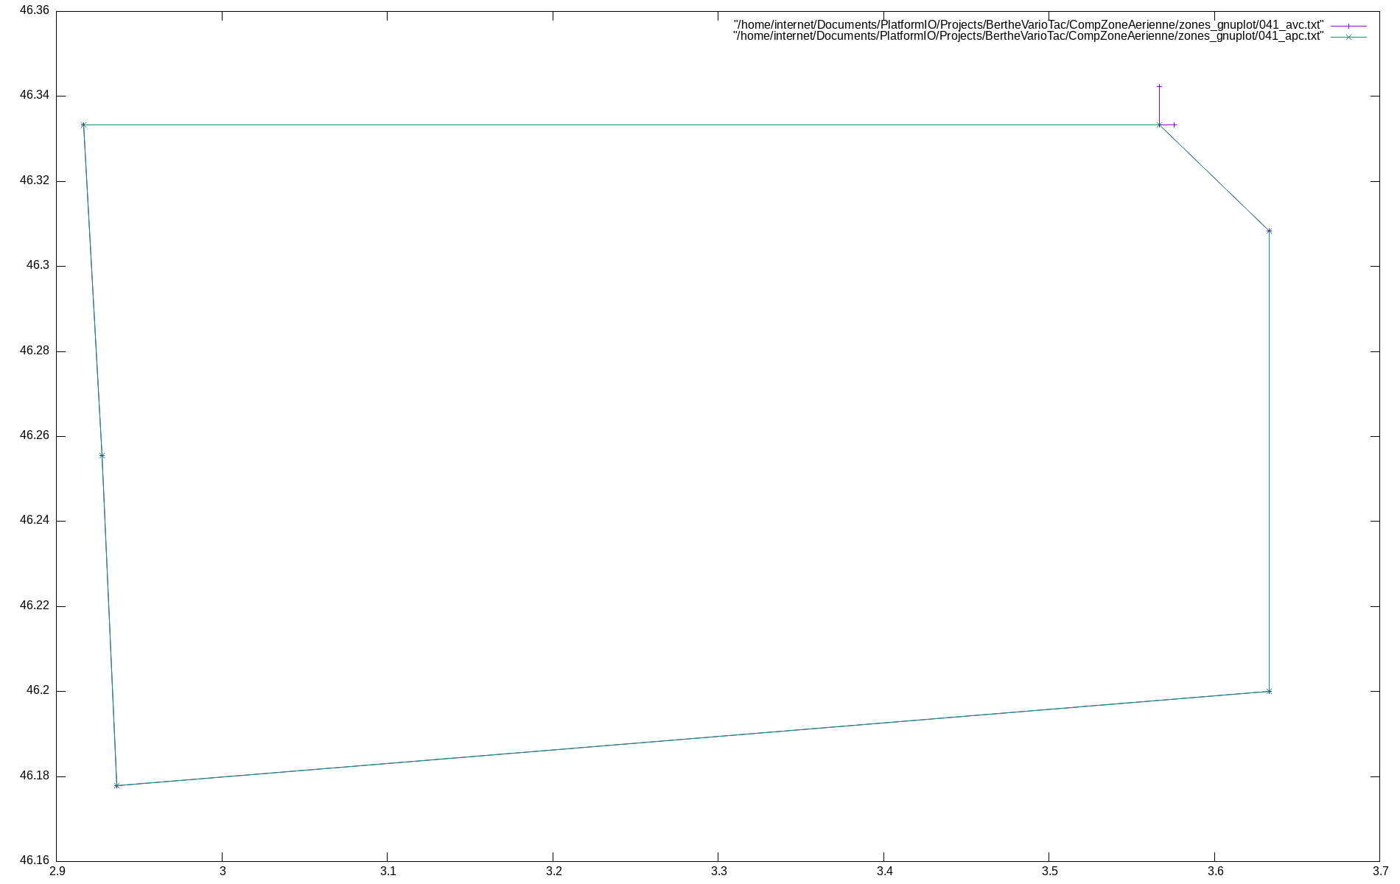
CompZoneAerienne/zones_gnuplot/041.png
