gitberthe/BertheVario213/CompZoneAerienne/zones_gnuplot/042.png

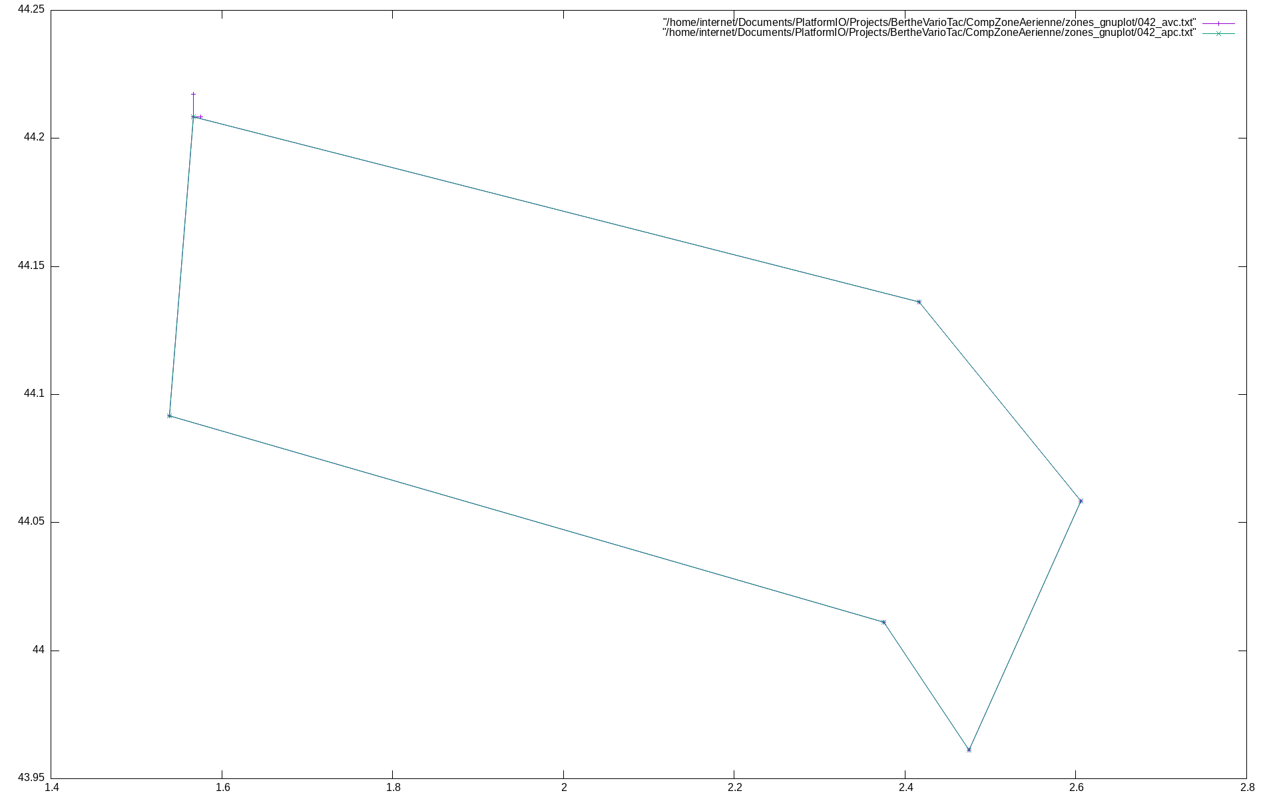
CompZoneAerienne/zones_gnuplot/042.png
