gitberthe/BertheVario213/CompZoneAerienne/zones_gnuplot/043.png

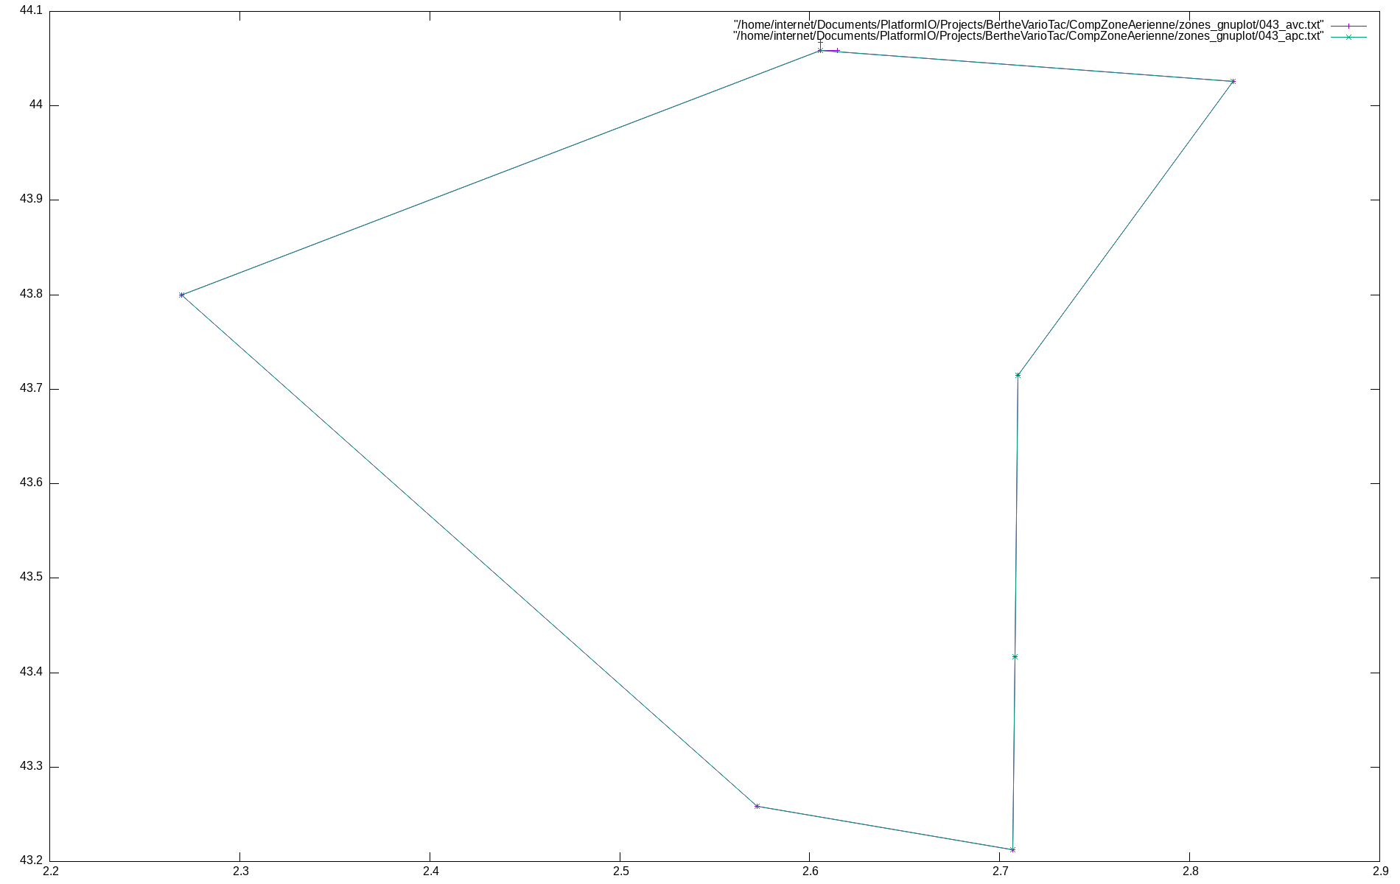
CompZoneAerienne/zones_gnuplot/043.png
