gitberthe/BertheVario213/CompZoneAerienne/zones_gnuplot/044.png

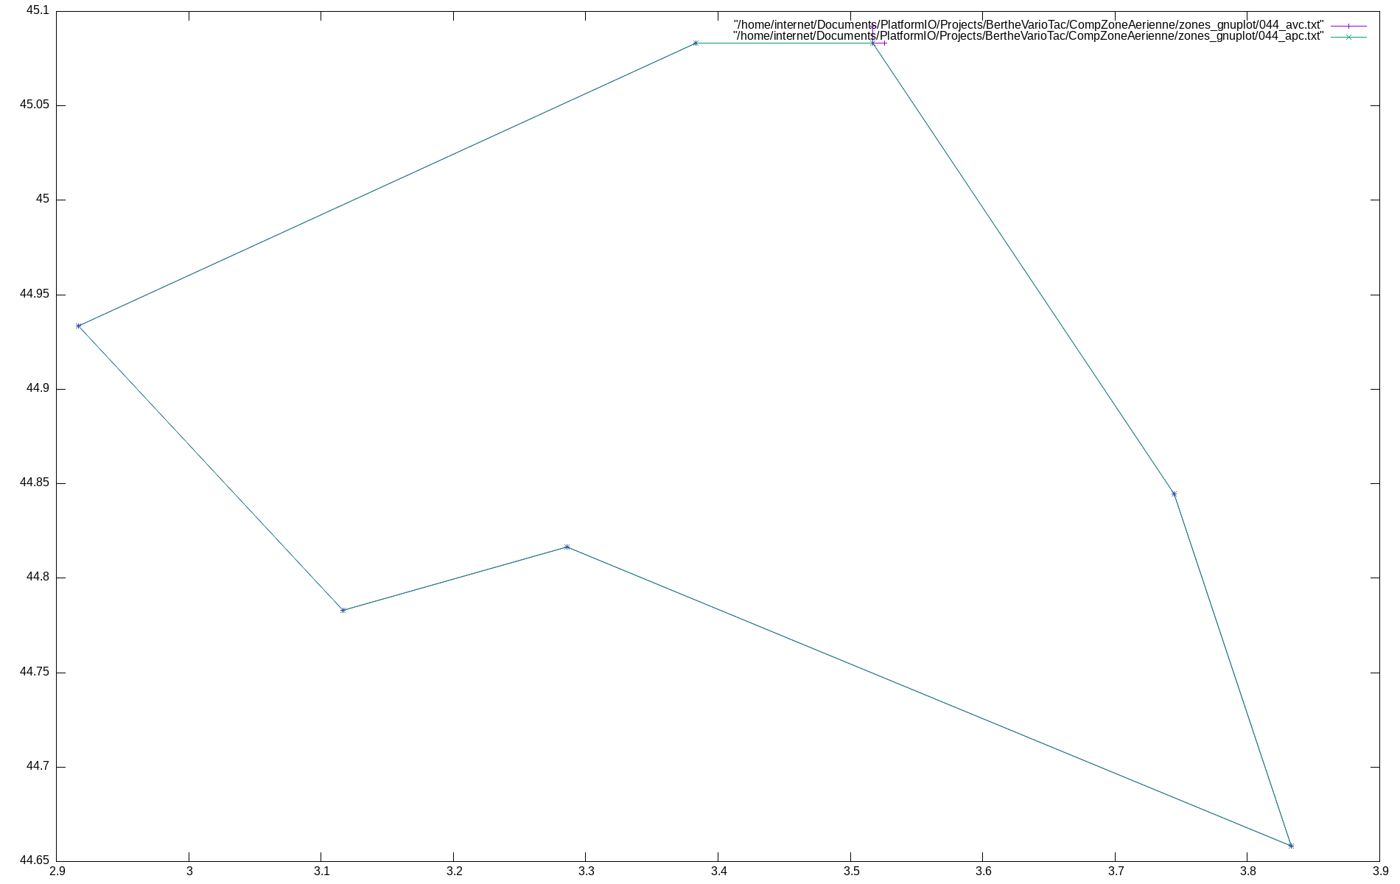
CompZoneAerienne/zones_gnuplot/044.png
