gitberthe/BertheVario213/CompZoneAerienne/zones_gnuplot/045.png

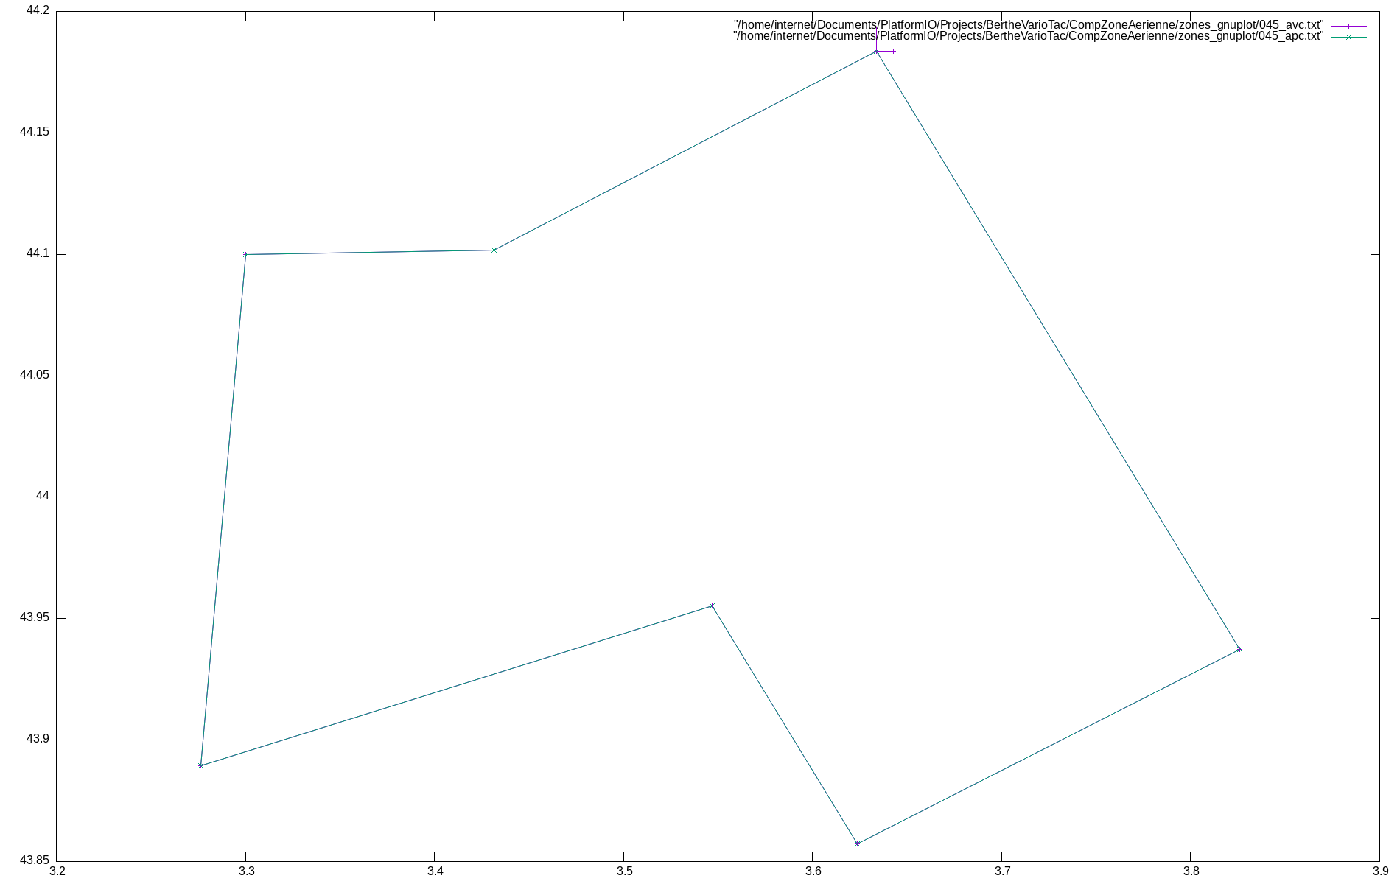
CompZoneAerienne/zones_gnuplot/045.png
