gitberthe/BertheVario213/CompZoneAerienne/zones_gnuplot/046.png

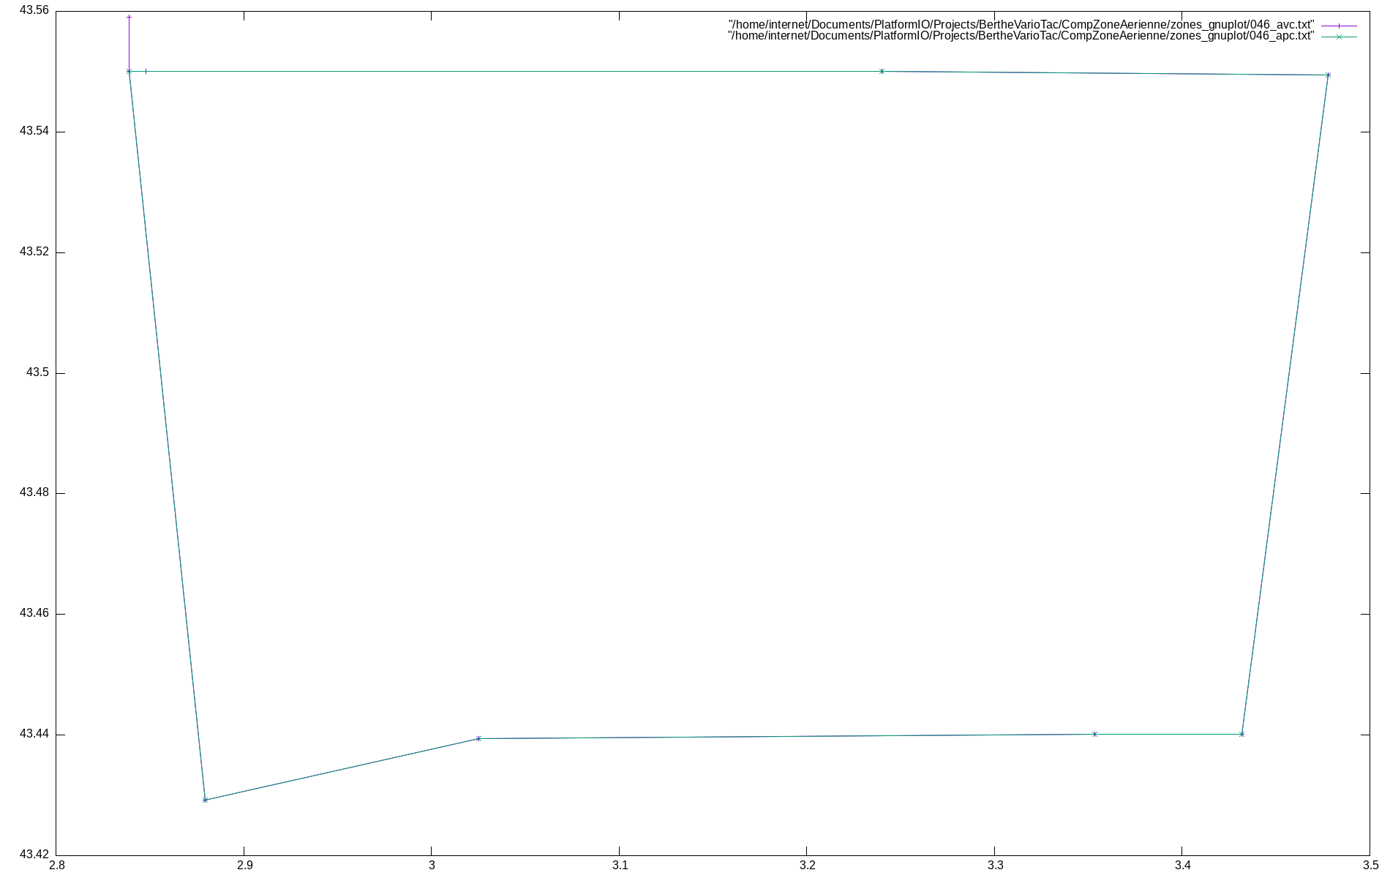
CompZoneAerienne/zones_gnuplot/046.png
