gitberthe/BertheVario213/CompZoneAerienne/zones_gnuplot/047.png

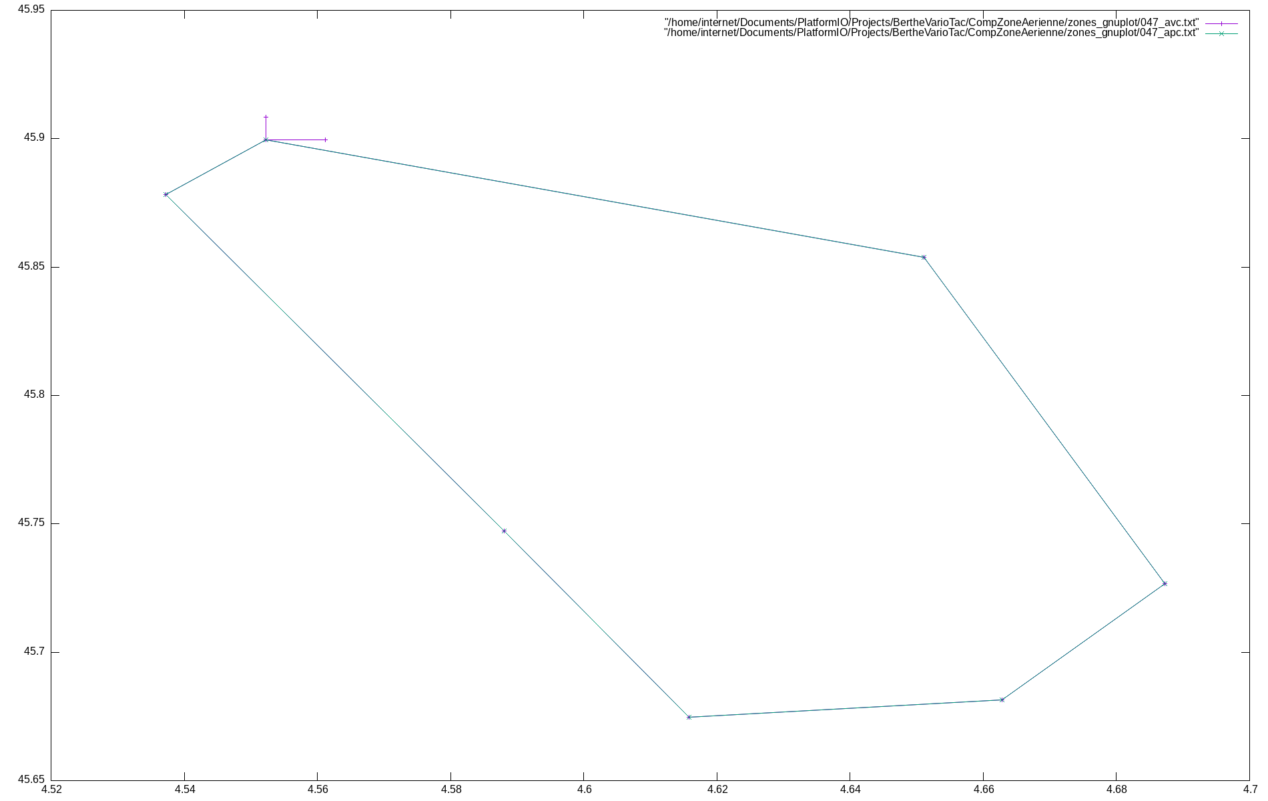
CompZoneAerienne/zones_gnuplot/047.png
