gitberthe/BertheVario213/CompZoneAerienne/zones_gnuplot/048.png

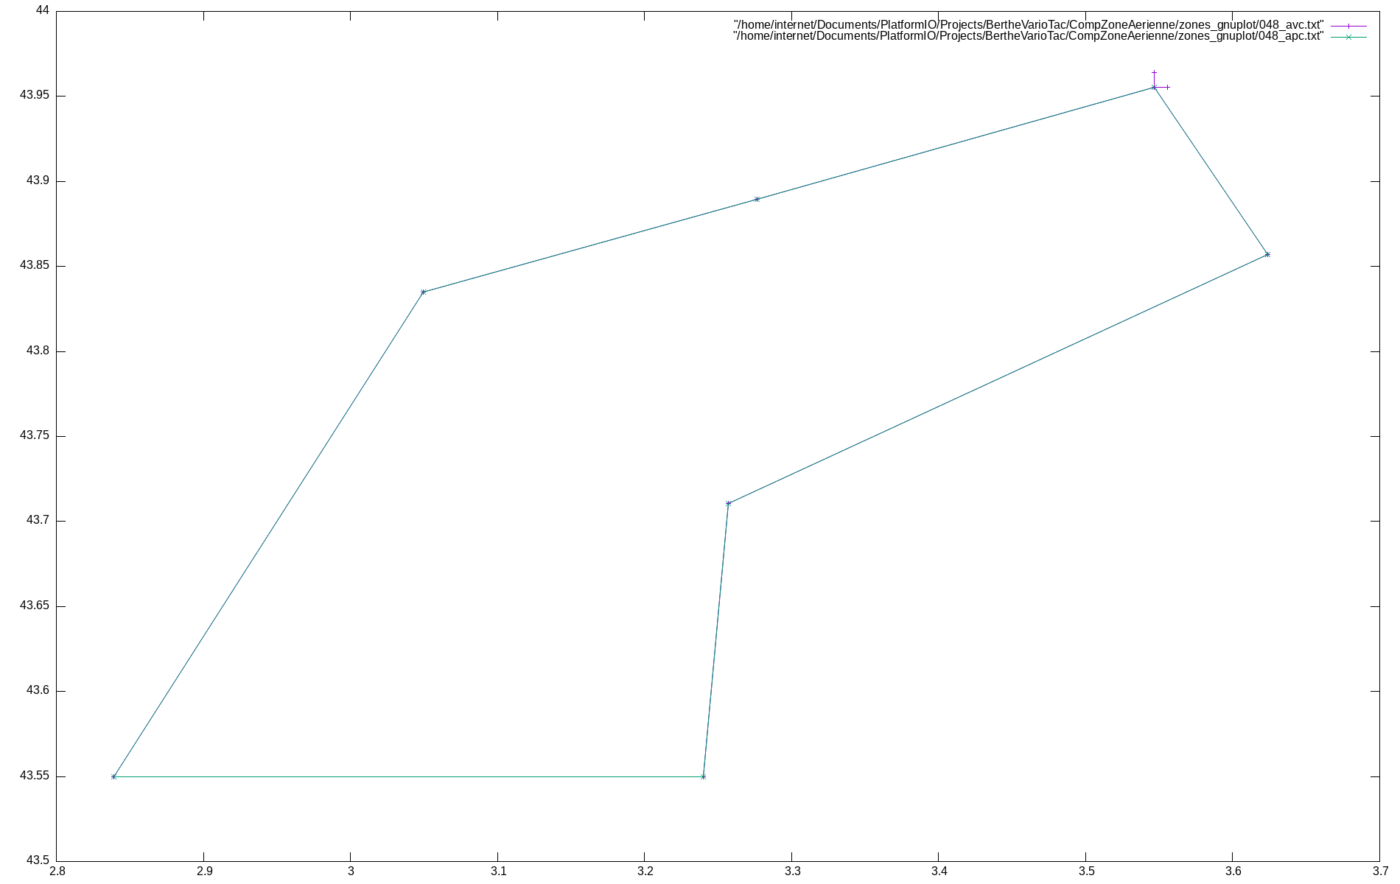
CompZoneAerienne/zones_gnuplot/048.png
