gitberthe/BertheVario213/CompZoneAerienne/zones_gnuplot/049.png

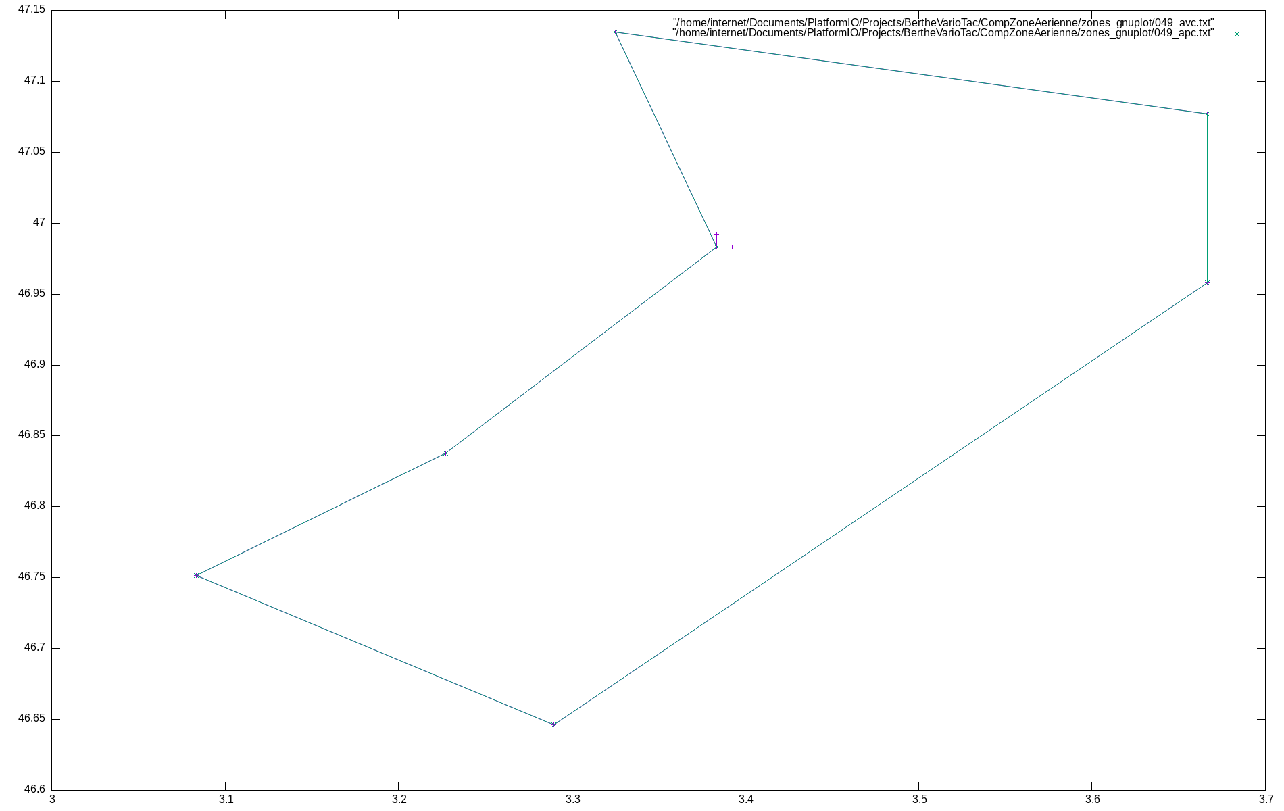
CompZoneAerienne/zones_gnuplot/049.png
