gitberthe/BertheVario213/CompZoneAerienne/zones_gnuplot/050.png

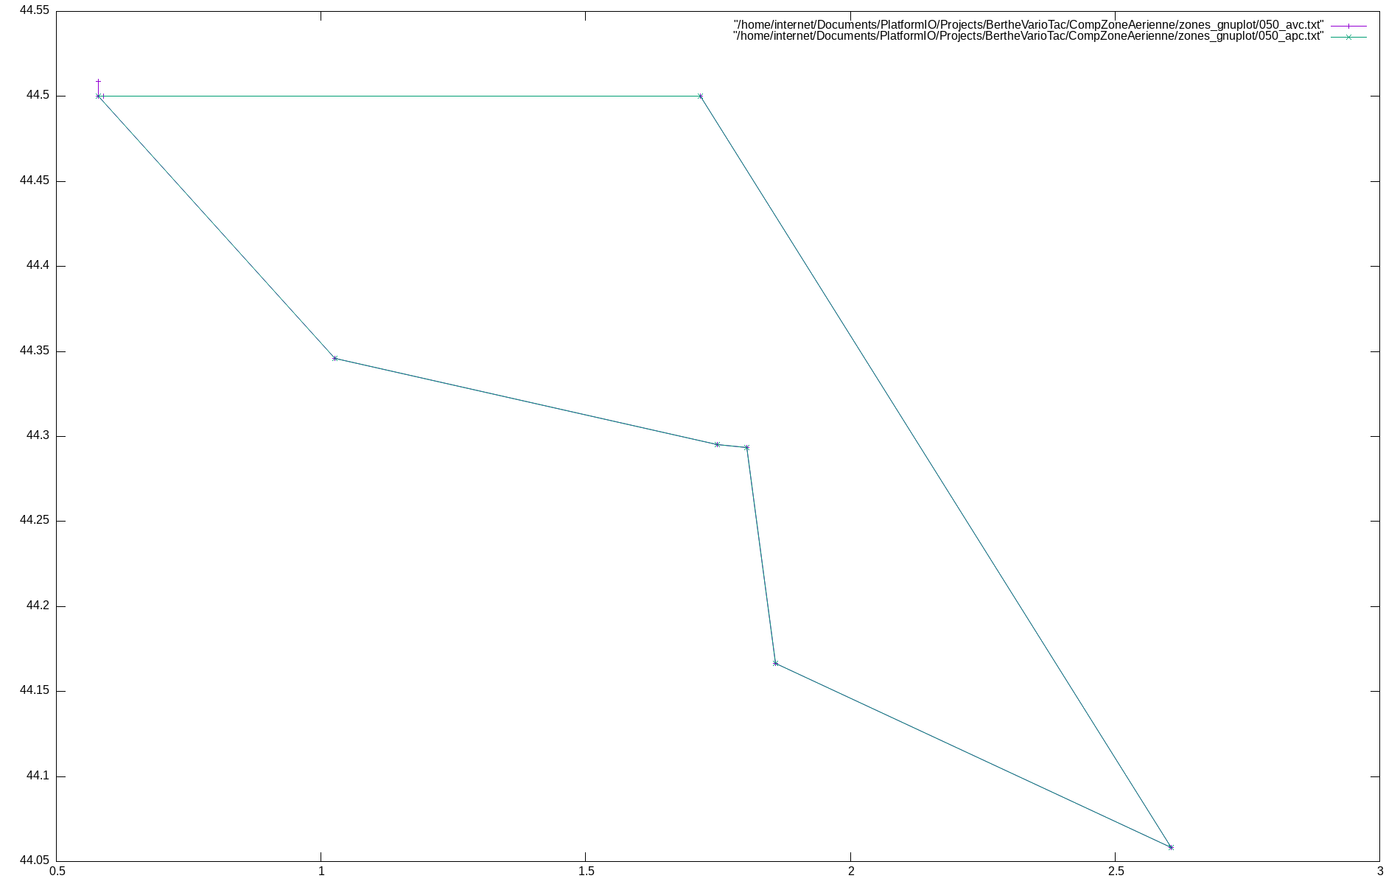
CompZoneAerienne/zones_gnuplot/050.png
