gitberthe/BertheVario213/CompZoneAerienne/zones_gnuplot/051.png

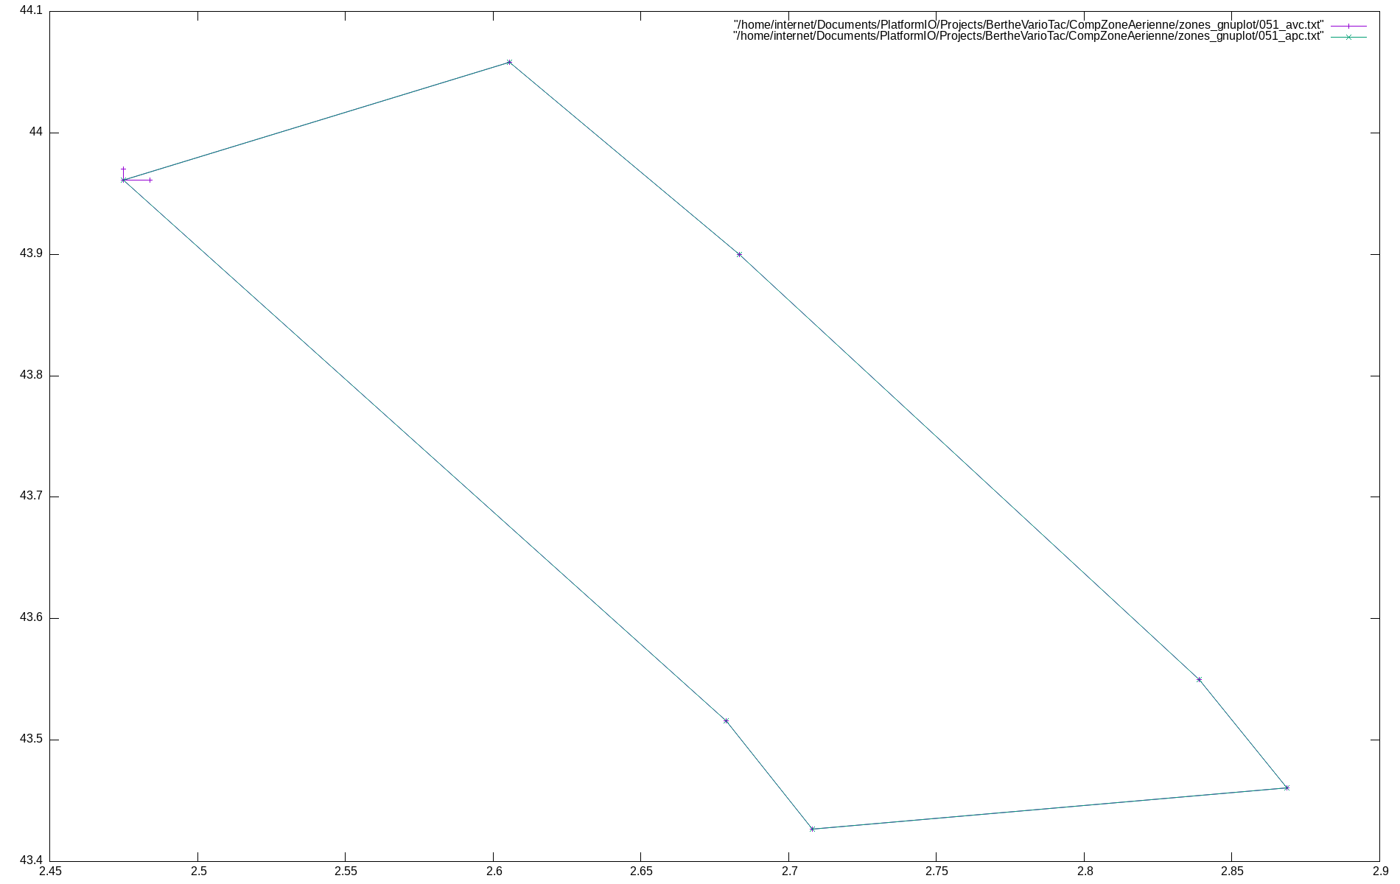
CompZoneAerienne/zones_gnuplot/051.png
