gitberthe/BertheVario213/CompZoneAerienne/zones_gnuplot/052.png

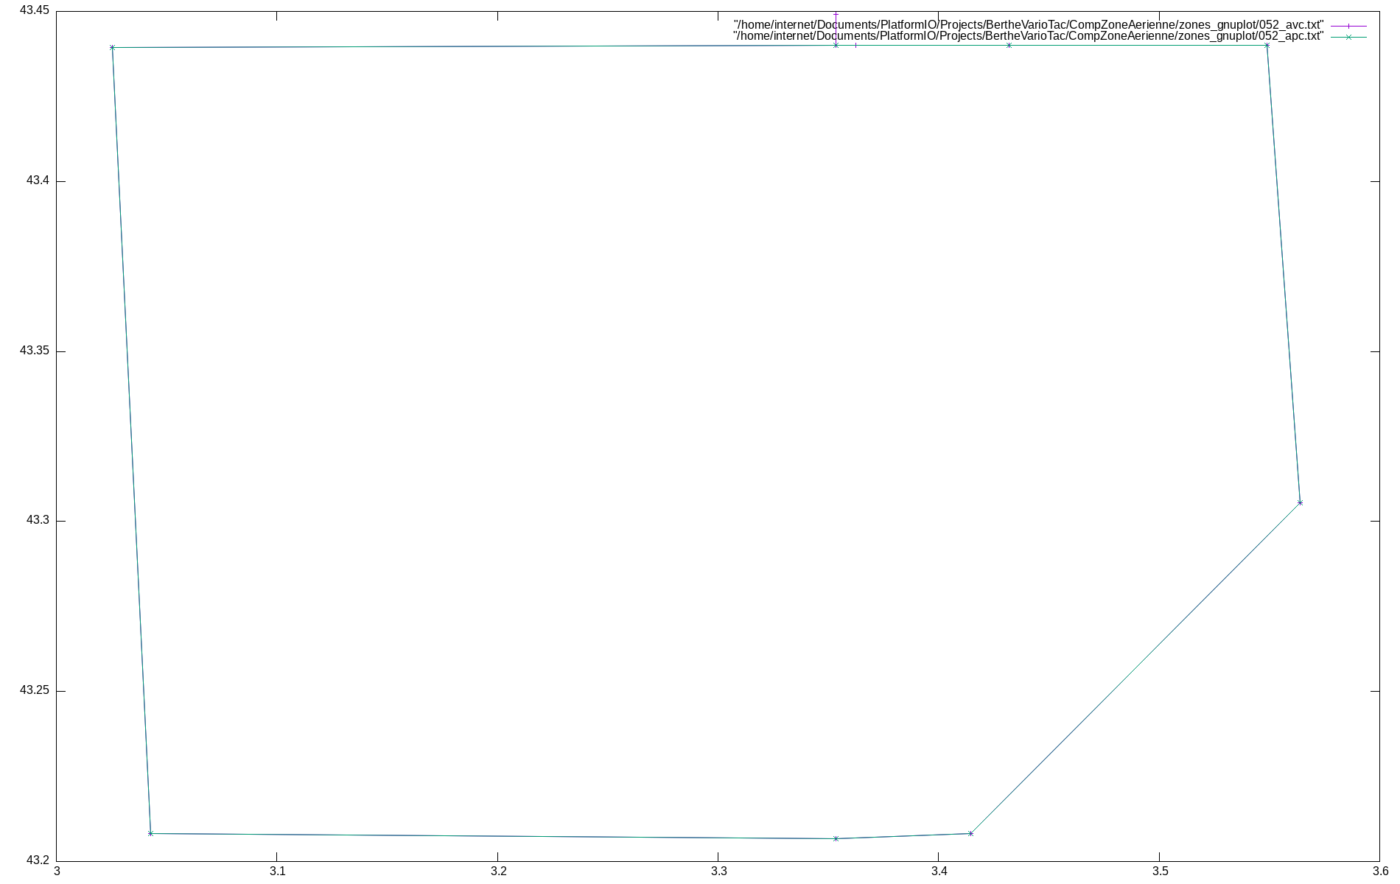
CompZoneAerienne/zones_gnuplot/052.png
