gitberthe/BertheVario213/CompZoneAerienne/zones_gnuplot/053.png

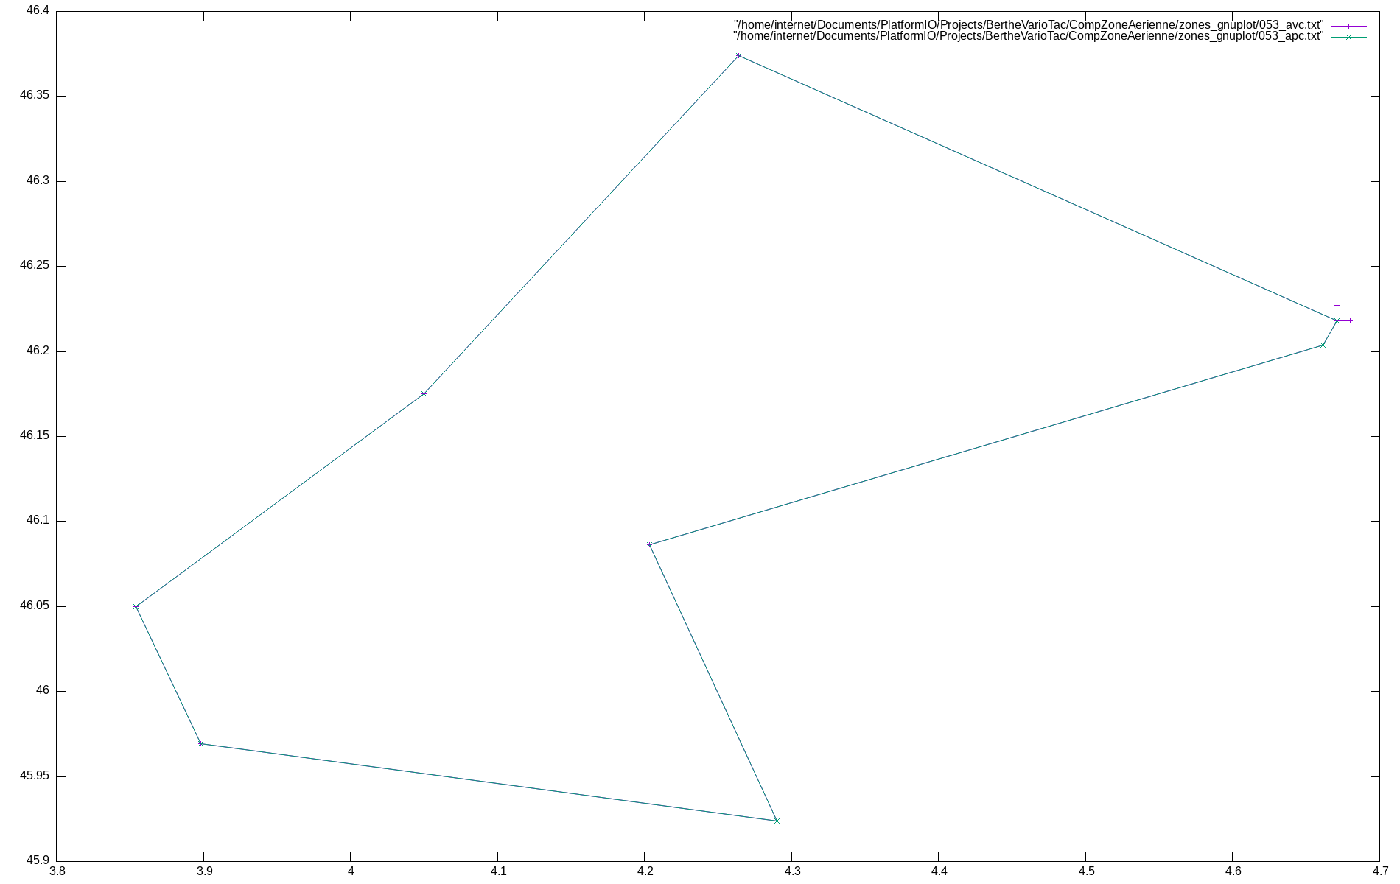
CompZoneAerienne/zones_gnuplot/053.png
