gitberthe/BertheVario213/CompZoneAerienne/zones_gnuplot/054.png

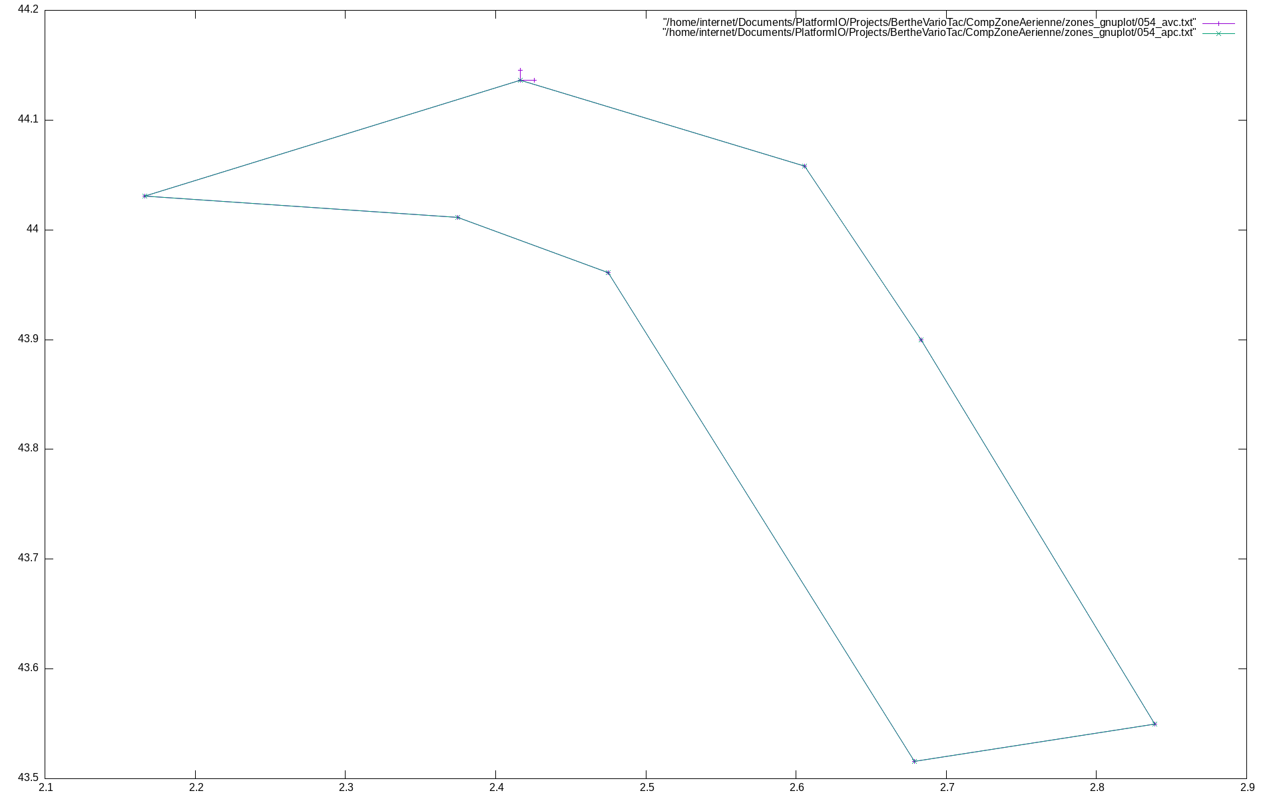
CompZoneAerienne/zones_gnuplot/054.png
