gitberthe/BertheVario213/CompZoneAerienne/zones_gnuplot/055.png

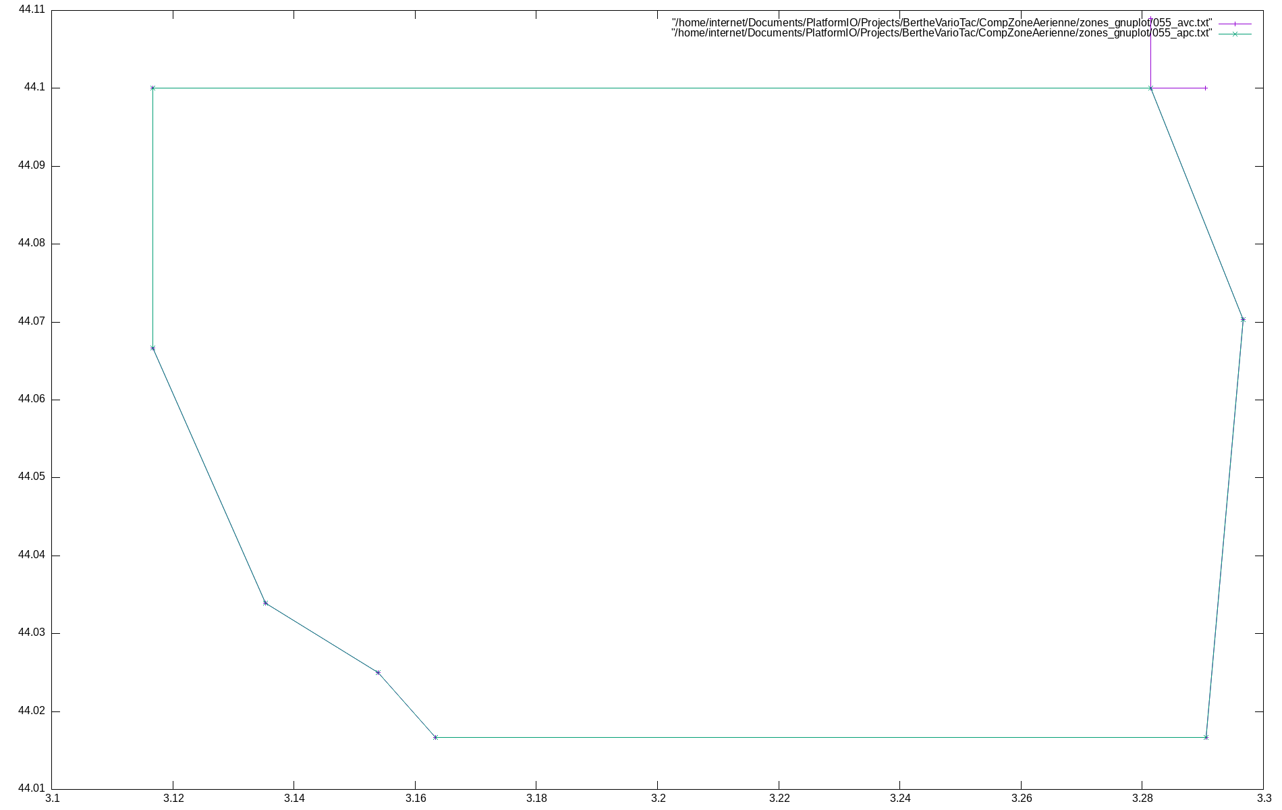
CompZoneAerienne/zones_gnuplot/055.png
