gitberthe/BertheVario213/CompZoneAerienne/zones_gnuplot/056.png

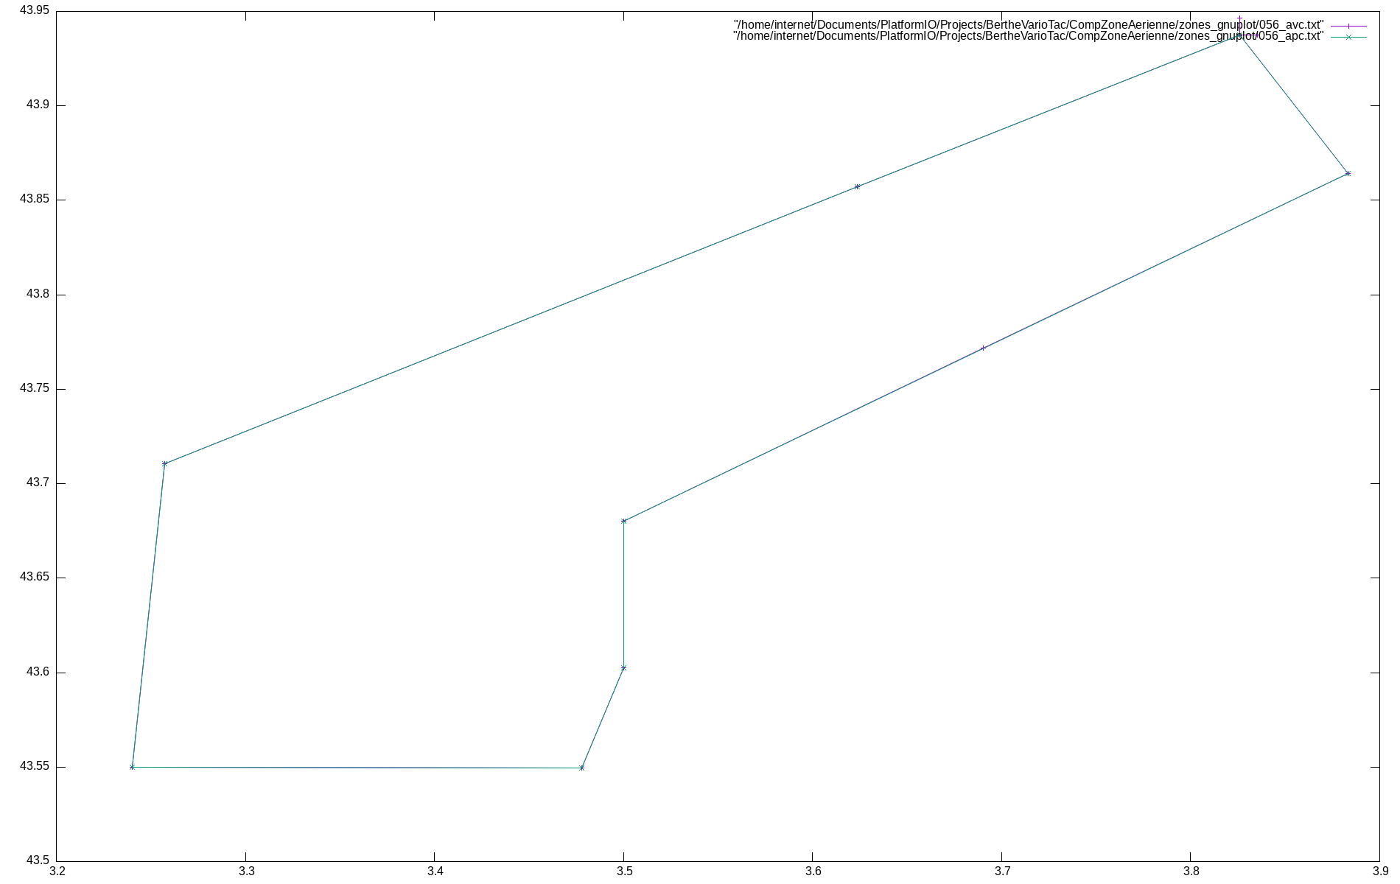
CompZoneAerienne/zones_gnuplot/056.png
