gitberthe/BertheVario213/CompZoneAerienne/zones_gnuplot/058.png

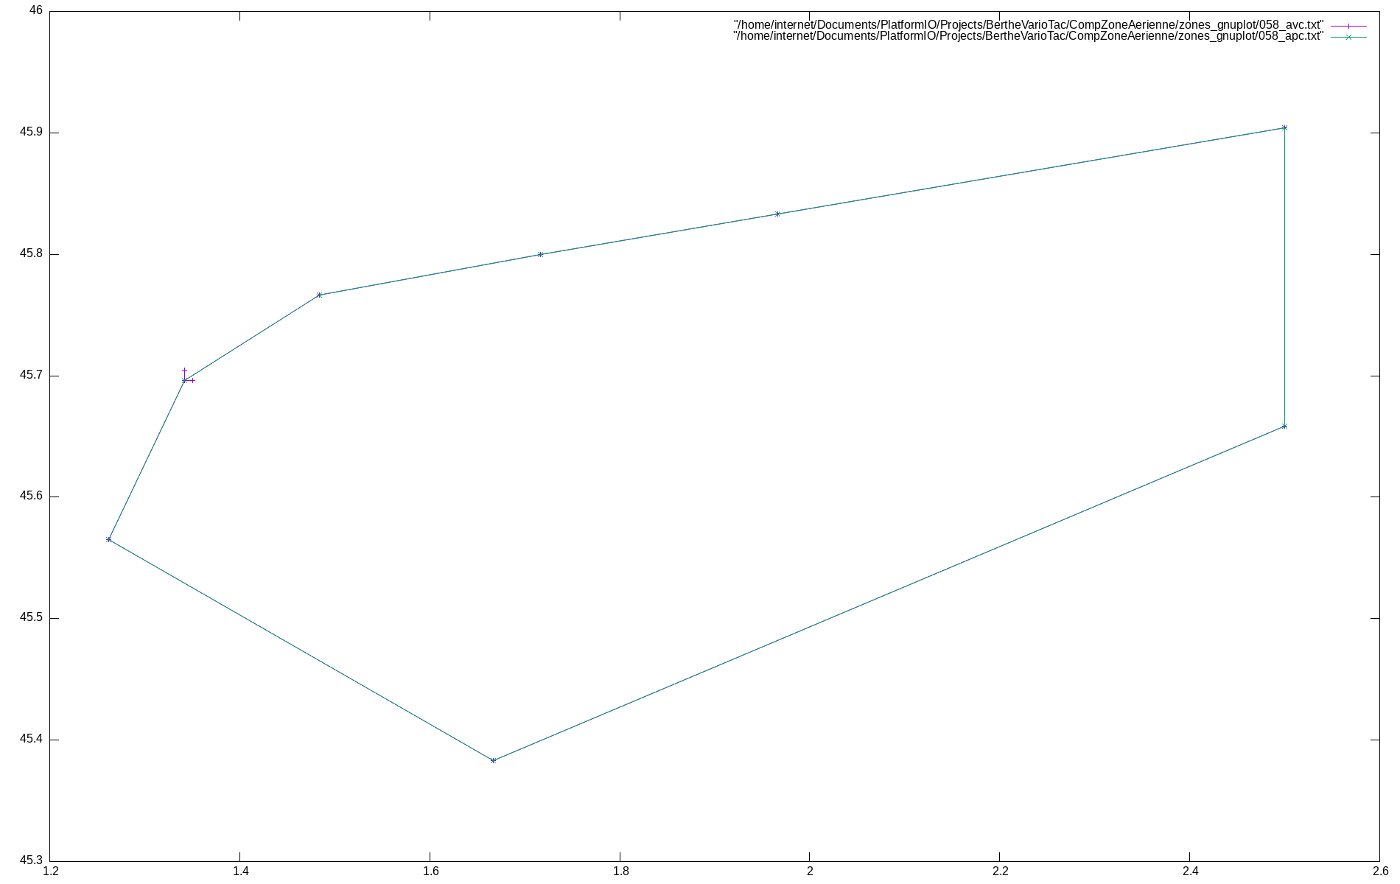
CompZoneAerienne/zones_gnuplot/058.png
