gitberthe/BertheVario213/CompZoneAerienne/zones_gnuplot/059.png

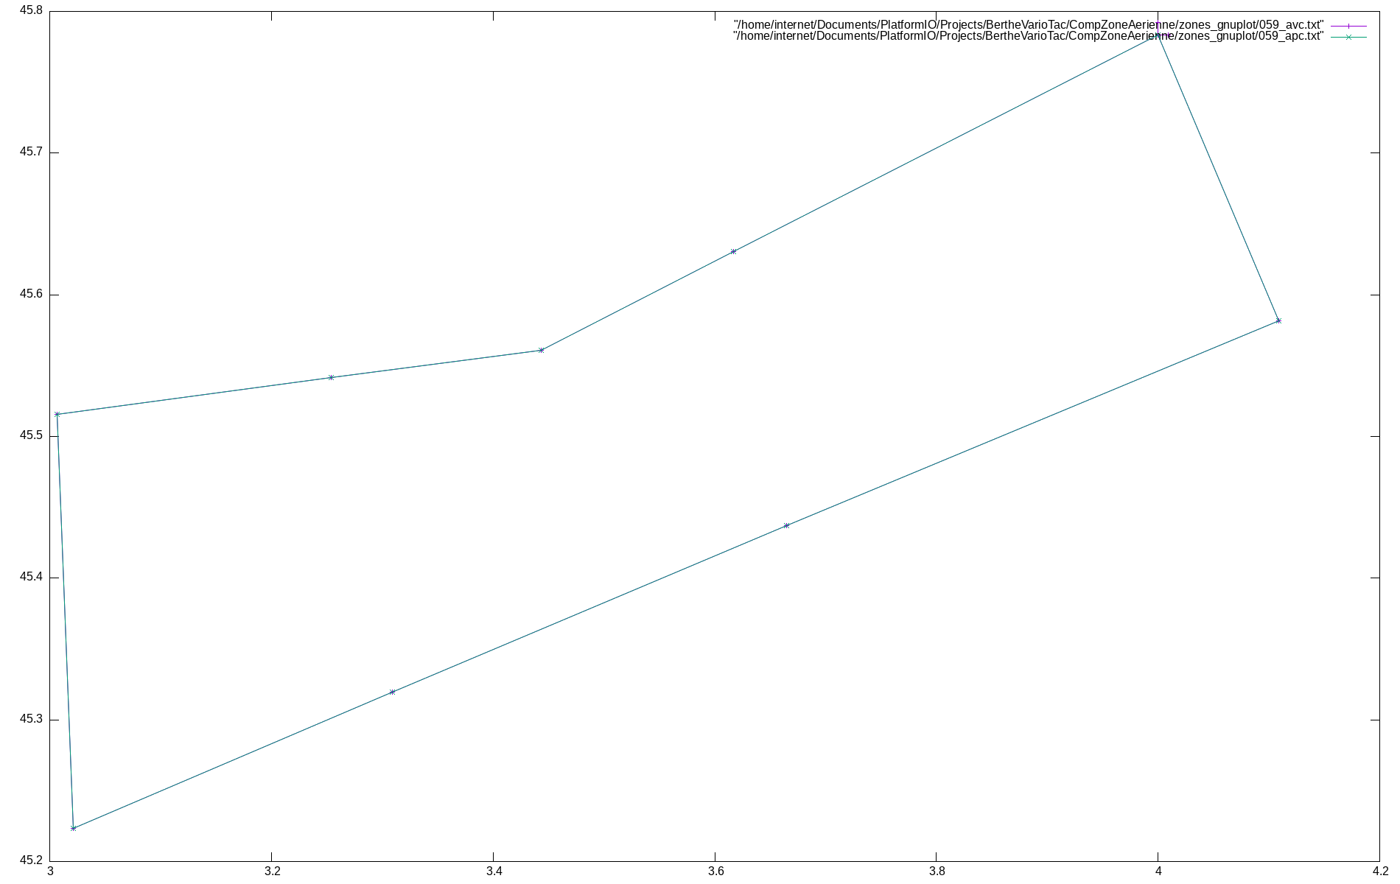
CompZoneAerienne/zones_gnuplot/059.png
