gitberthe/BertheVario213/CompZoneAerienne/zones_gnuplot/060.png

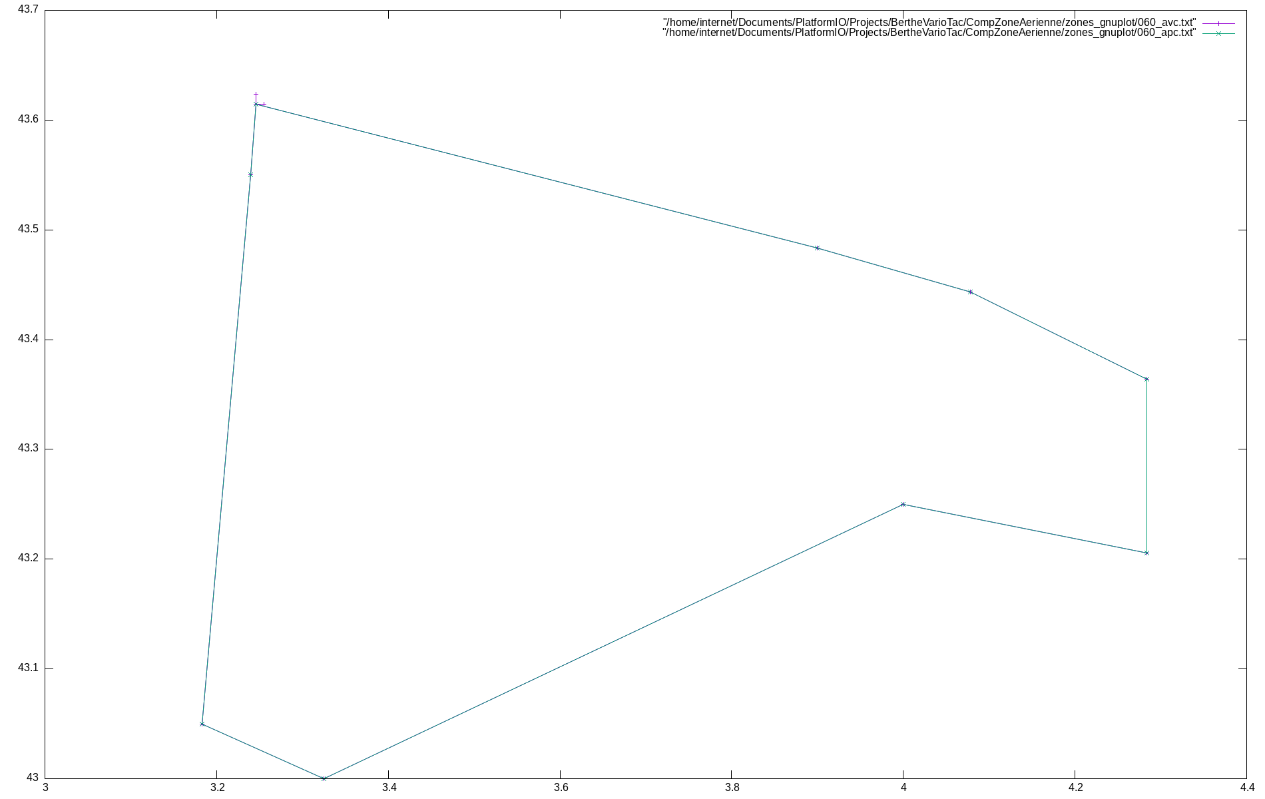
CompZoneAerienne/zones_gnuplot/060.png
