gitberthe/BertheVario213/CompZoneAerienne/zones_gnuplot/062.png

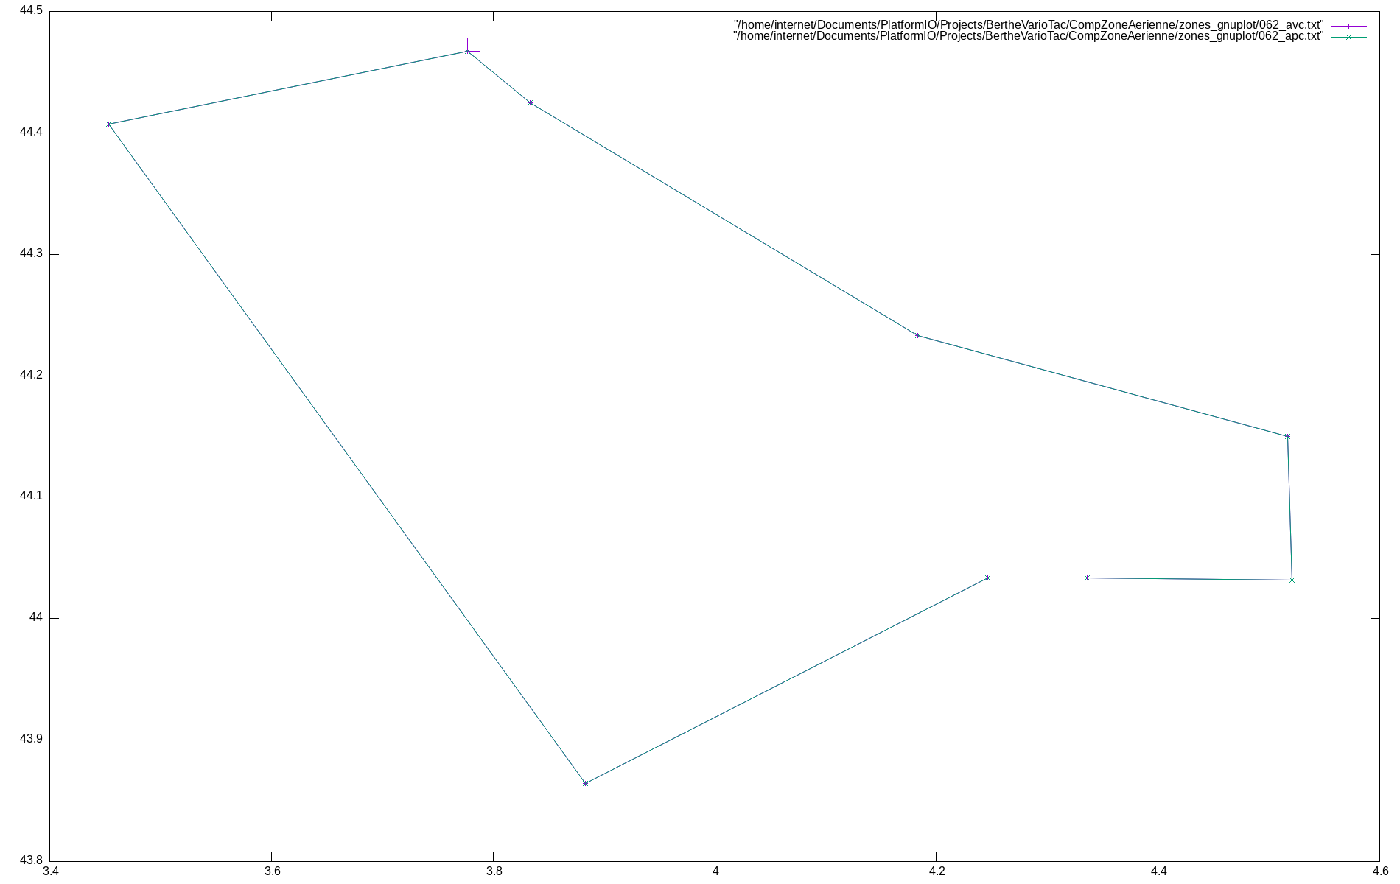
CompZoneAerienne/zones_gnuplot/062.png
