gitberthe/BertheVario213/CompZoneAerienne/zones_gnuplot/064.png

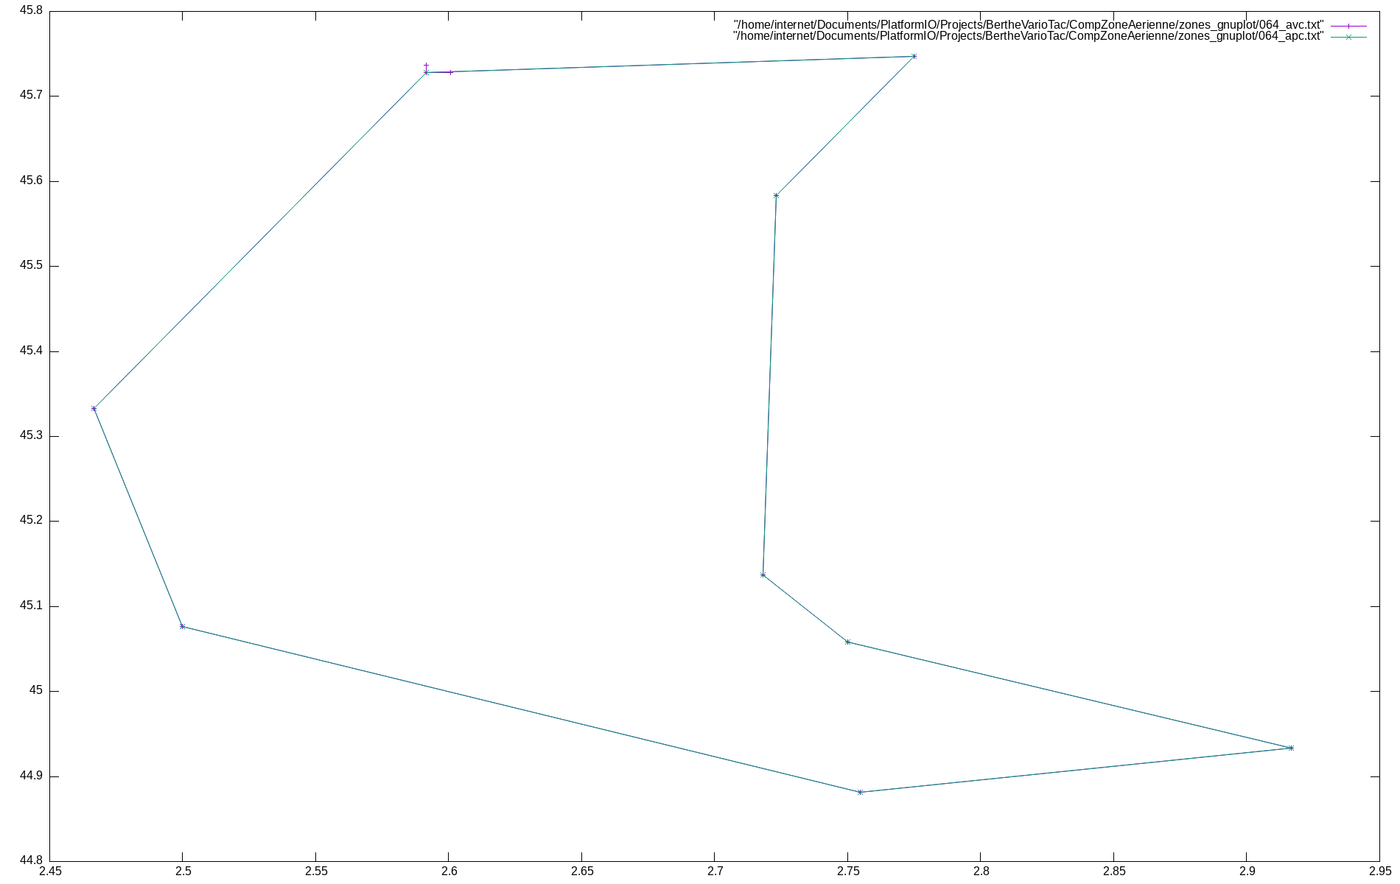
CompZoneAerienne/zones_gnuplot/064.png
