gitberthe/BertheVario213/CompZoneAerienne/zones_gnuplot/066.png

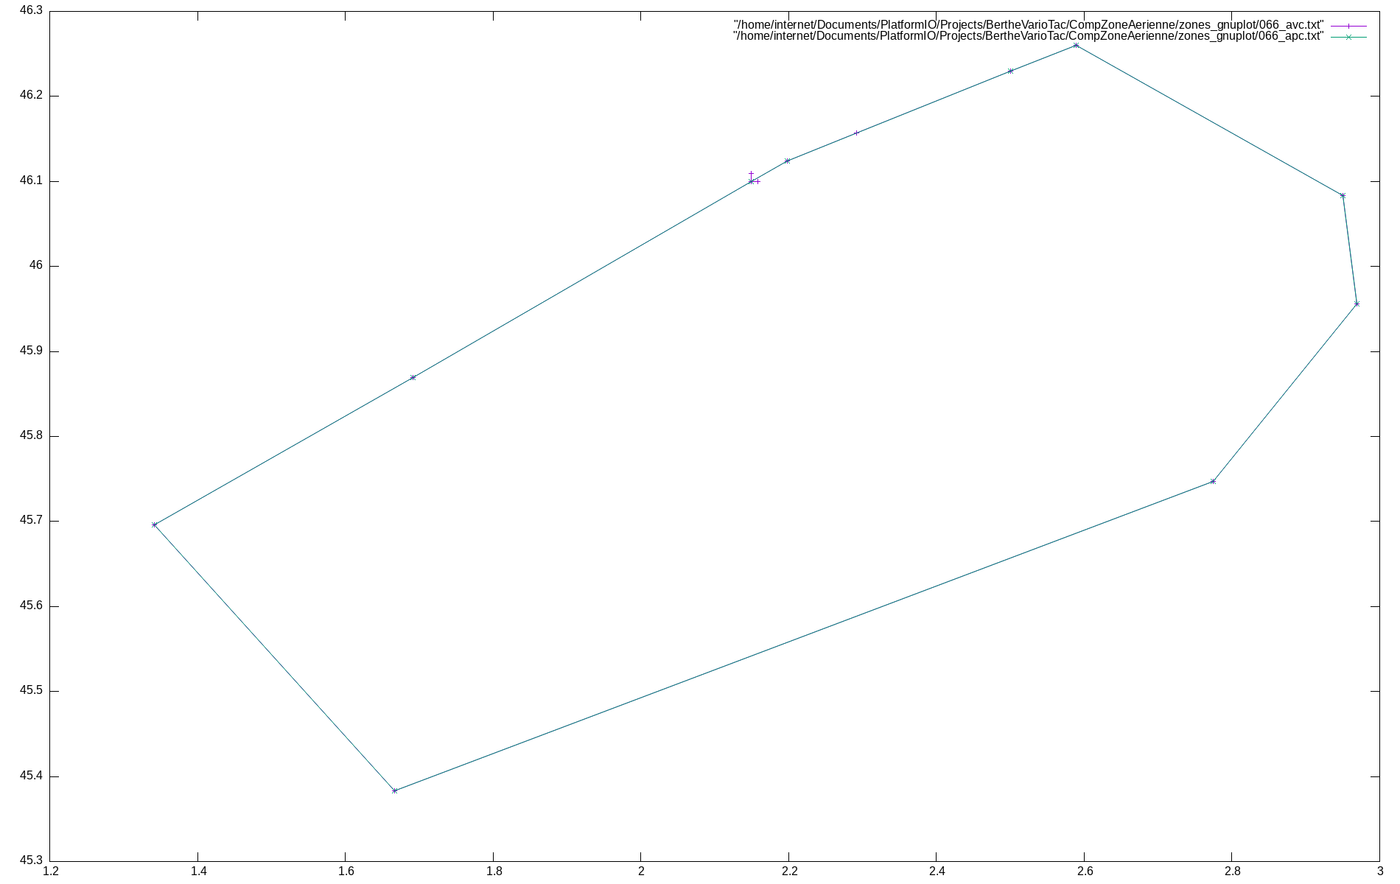
CompZoneAerienne/zones_gnuplot/066.png
