gitberthe/BertheVario213/CompZoneAerienne/zones_gnuplot/067.png

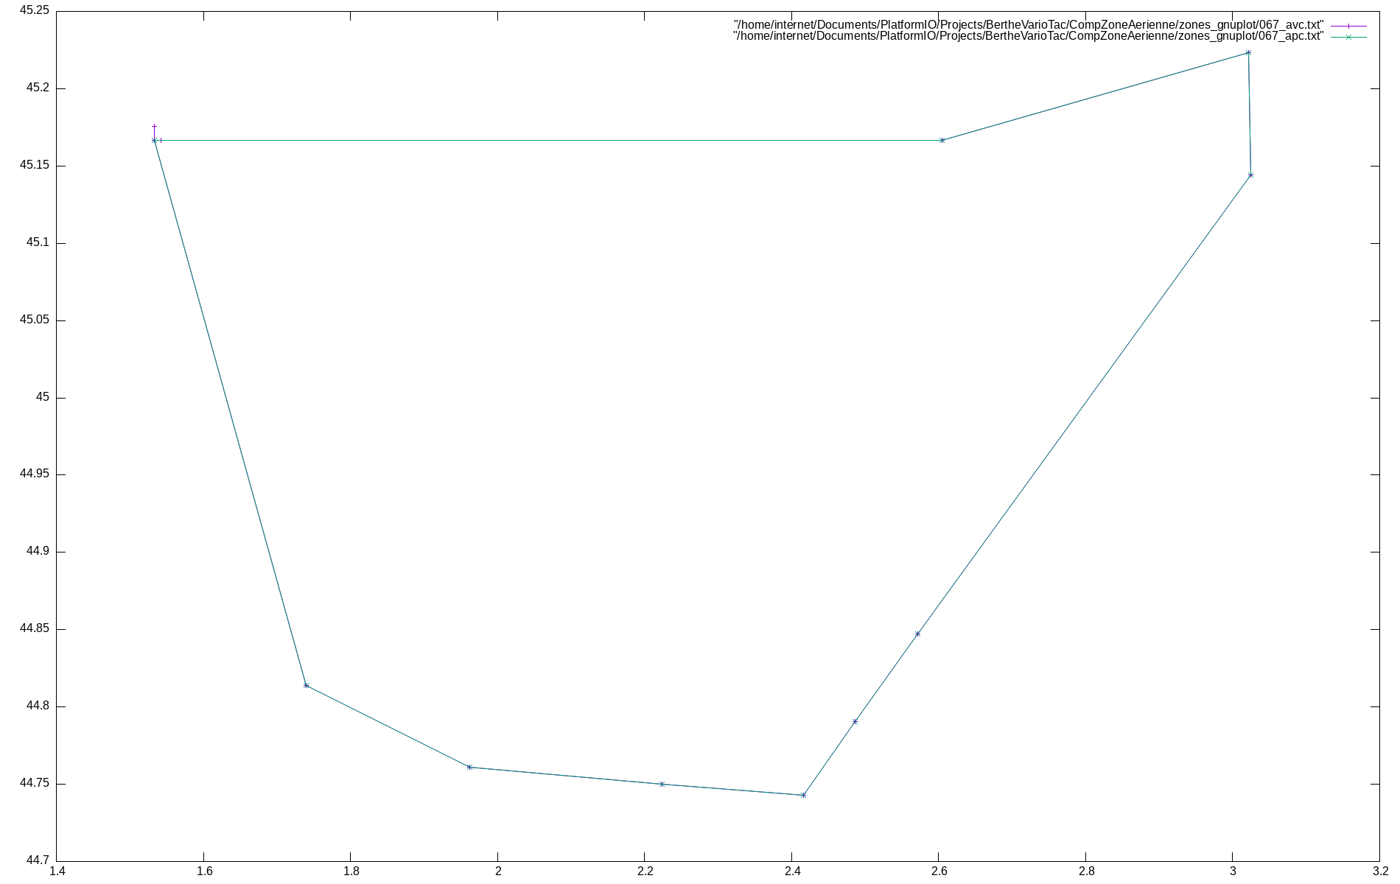
CompZoneAerienne/zones_gnuplot/067.png
