gitberthe/BertheVario213/CompZoneAerienne/zones_gnuplot/069.png

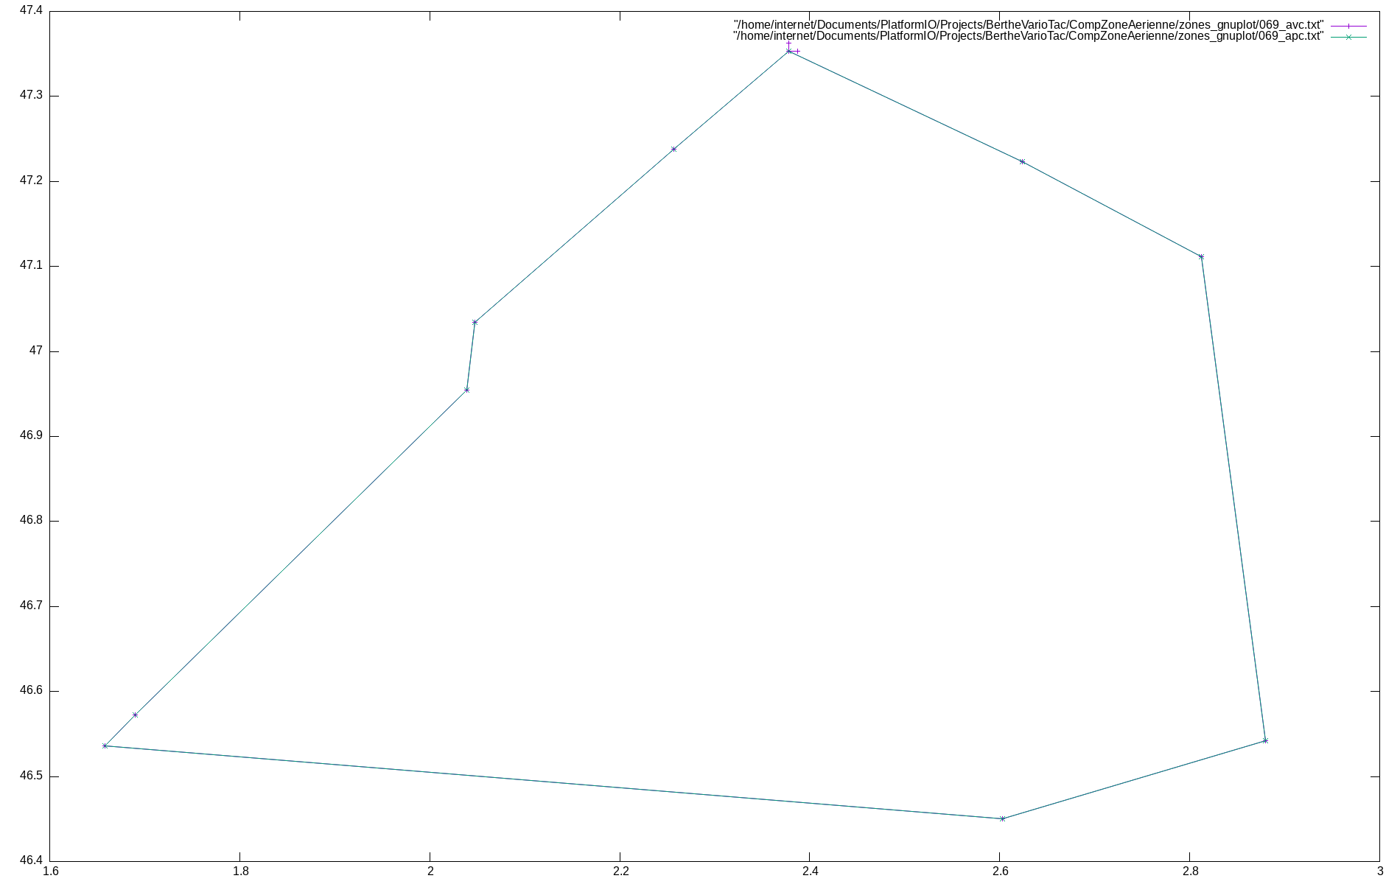
CompZoneAerienne/zones_gnuplot/069.png
