gitberthe/BertheVario213/CompZoneAerienne/zones_gnuplot/070.png

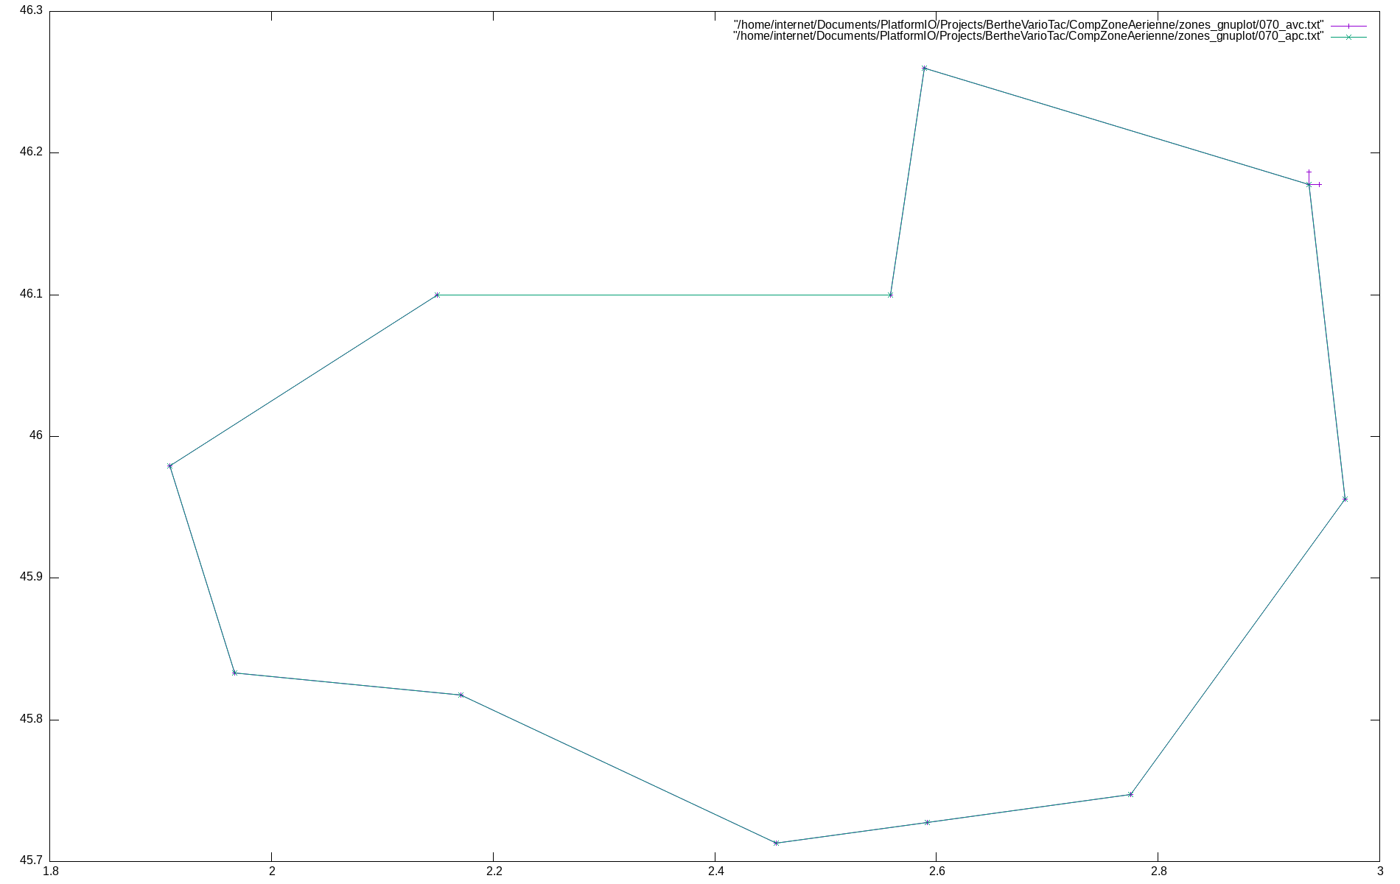
CompZoneAerienne/zones_gnuplot/070.png
