gitberthe/BertheVario213/CompZoneAerienne/zones_gnuplot/071.png

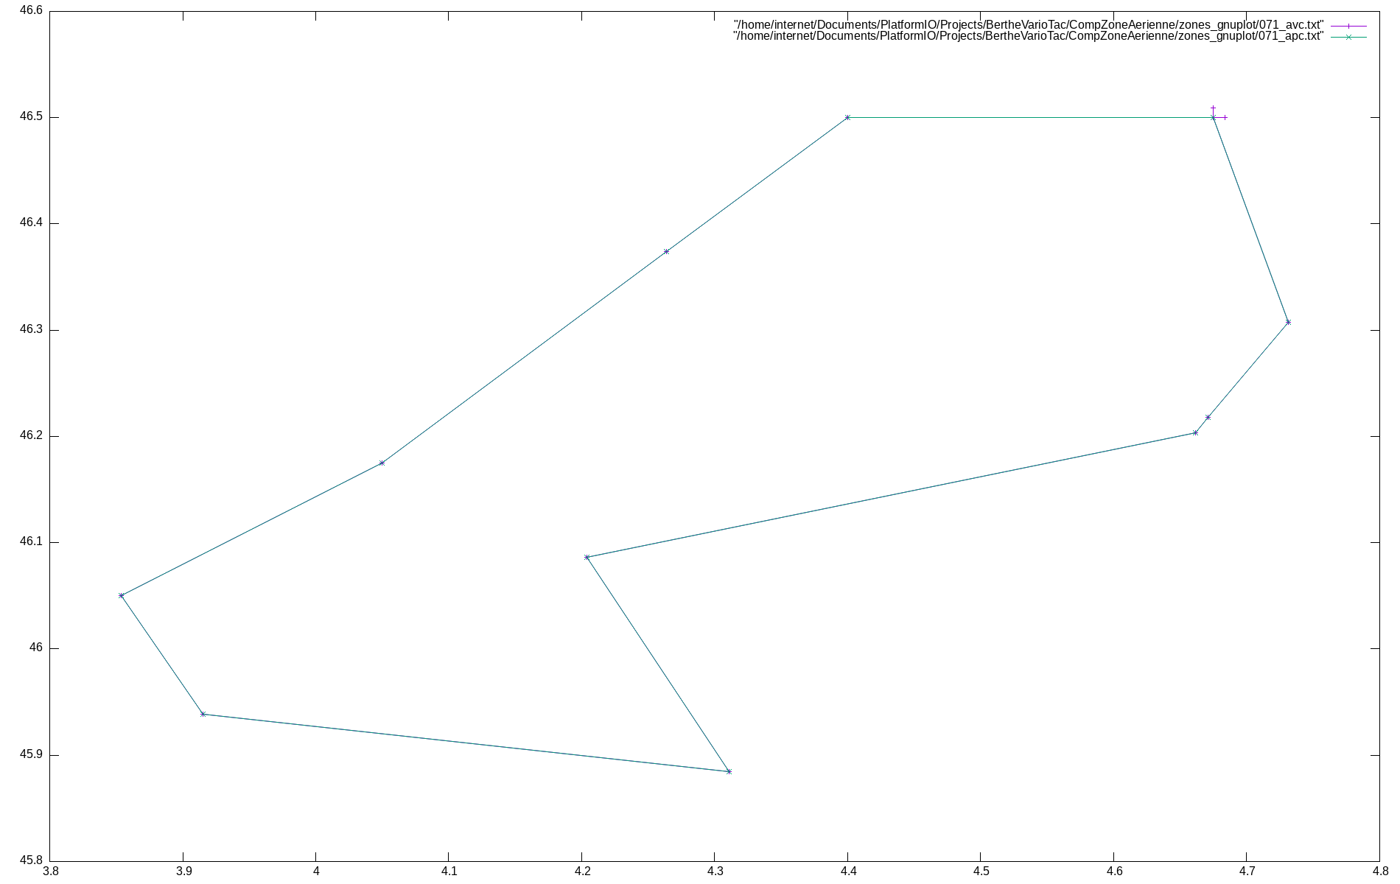
CompZoneAerienne/zones_gnuplot/071.png
