gitberthe/BertheVario213/CompZoneAerienne/zones_gnuplot/072.png

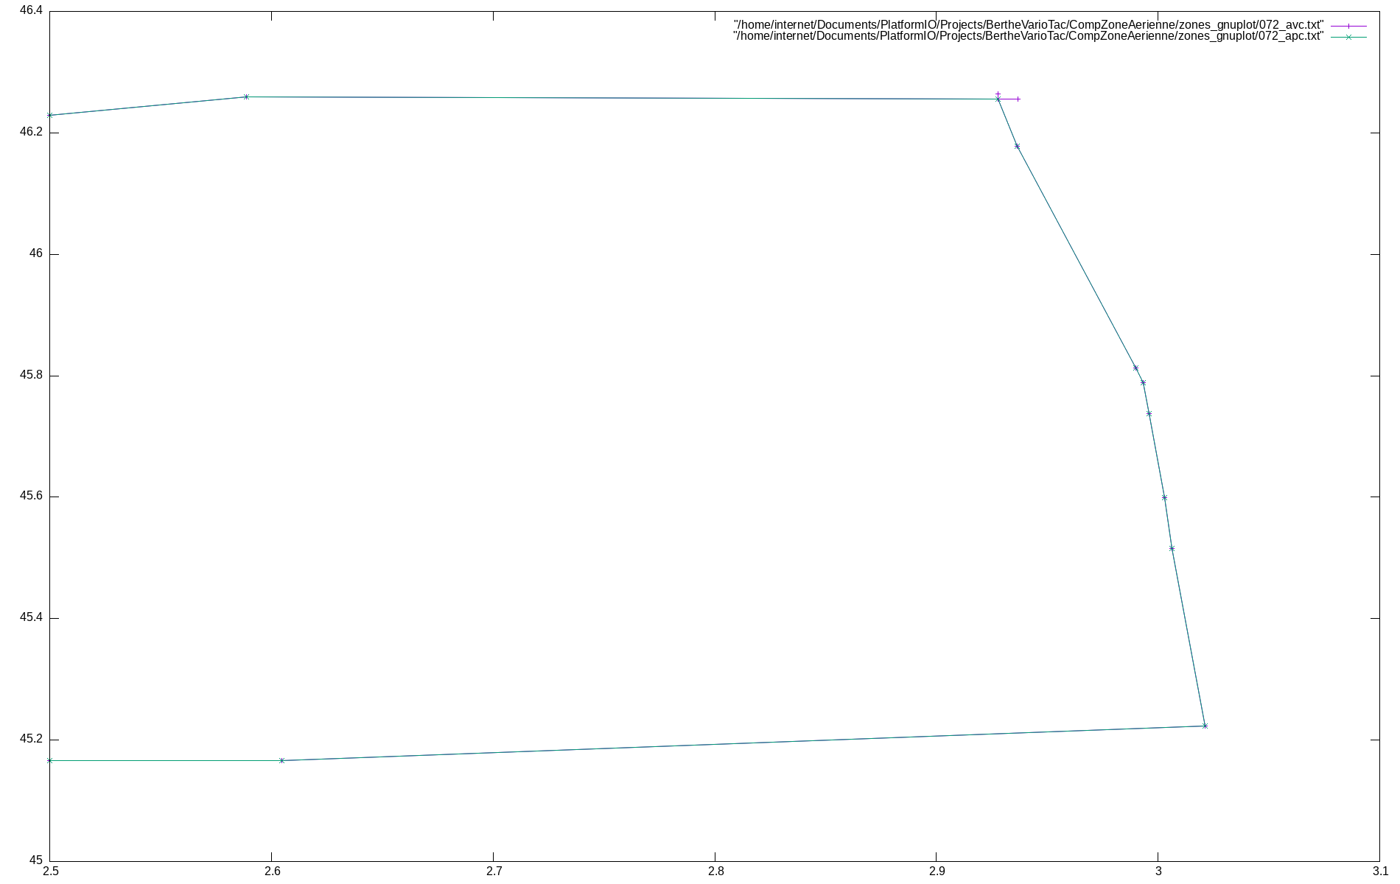
CompZoneAerienne/zones_gnuplot/072.png
