gitberthe/BertheVario213/CompZoneAerienne/zones_gnuplot/074.png

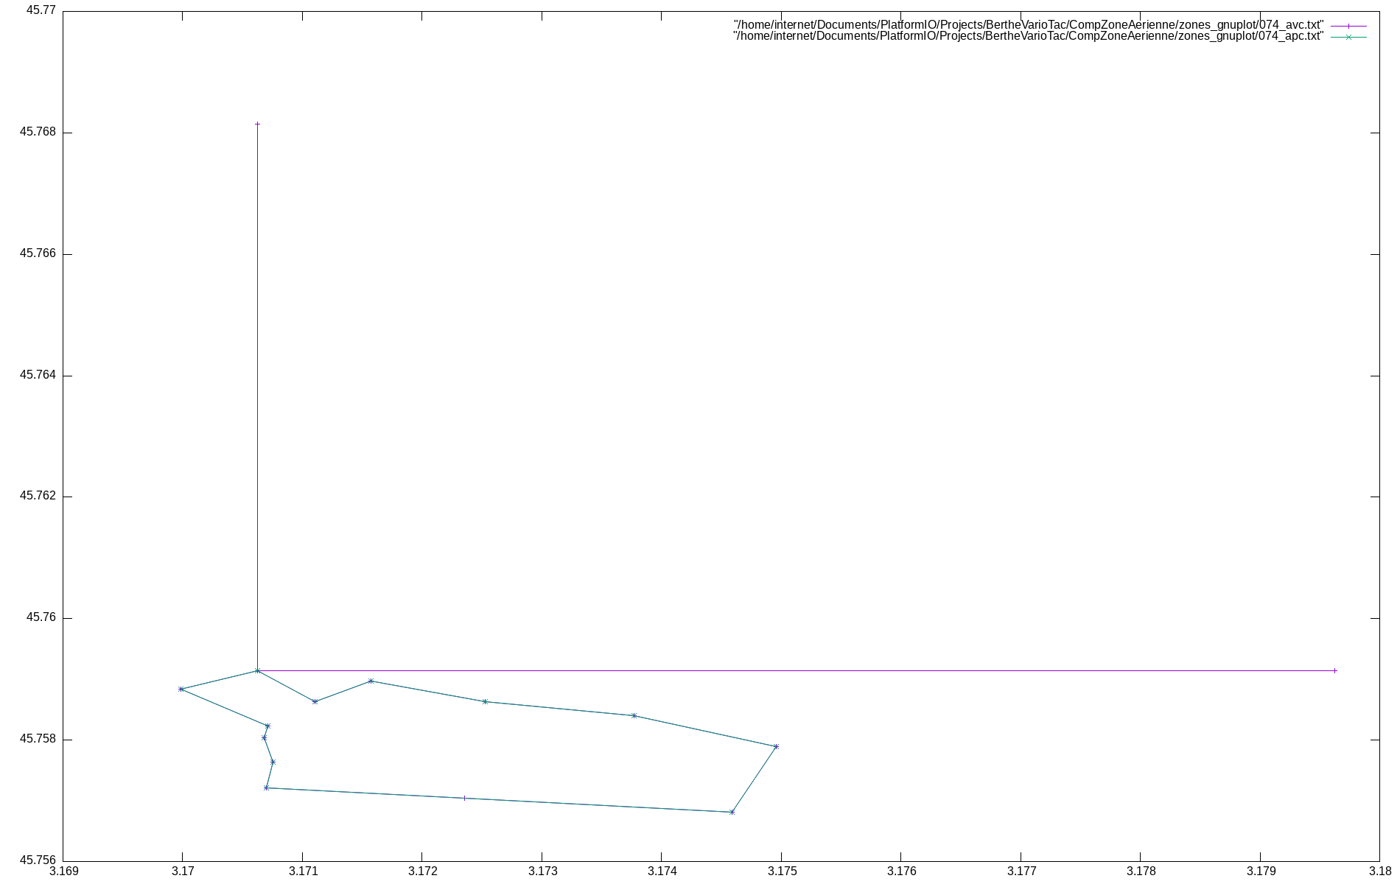
CompZoneAerienne/zones_gnuplot/074.png
