gitberthe/BertheVario213/CompZoneAerienne/zones_gnuplot/076.png

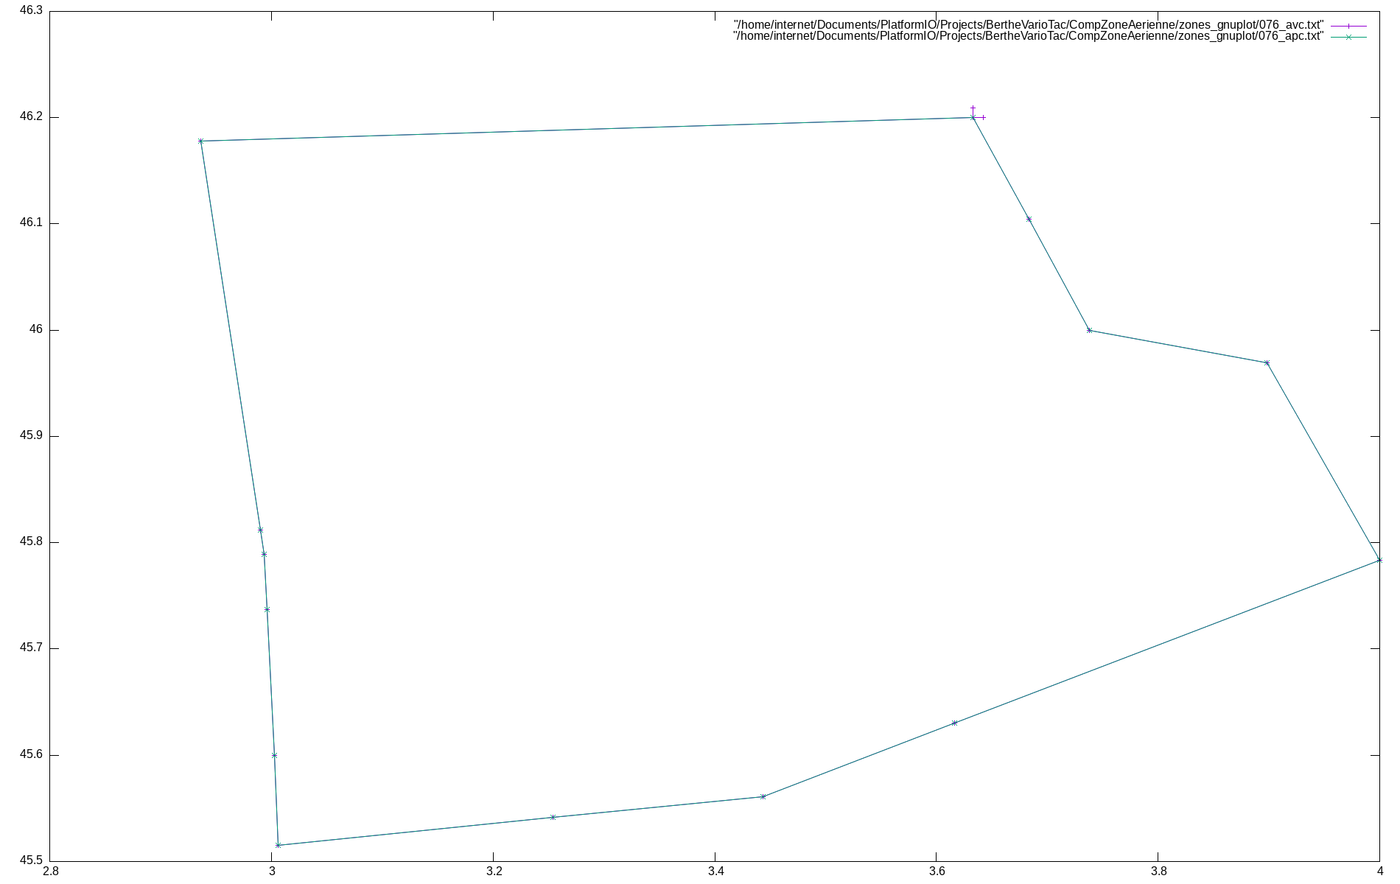
CompZoneAerienne/zones_gnuplot/076.png
