gitberthe/BertheVario213/CompZoneAerienne/zones_gnuplot/079.png

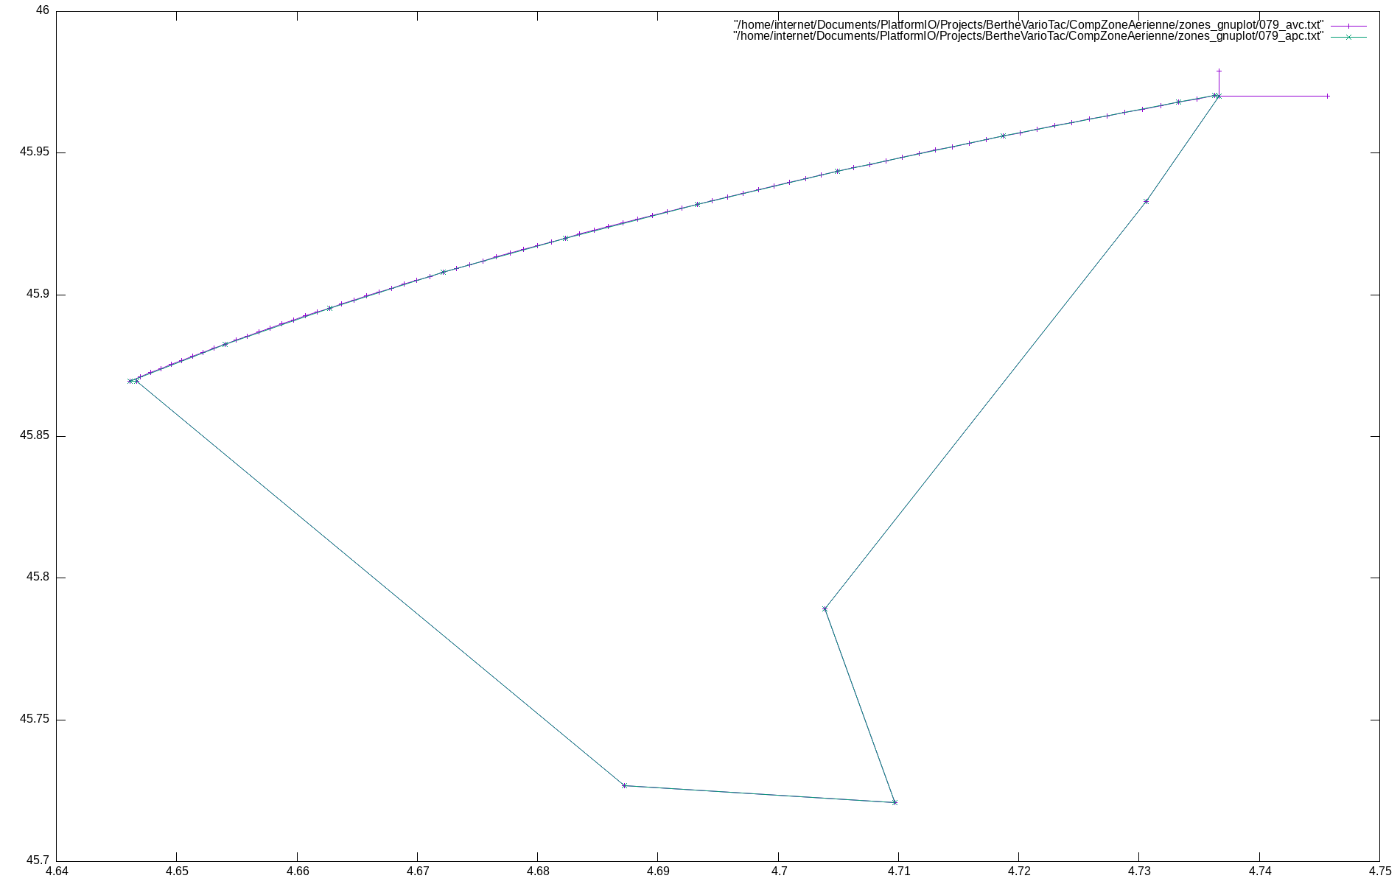
CompZoneAerienne/zones_gnuplot/079.png
