gitberthe/BertheVario213/CompZoneAerienne/zones_gnuplot/080.png

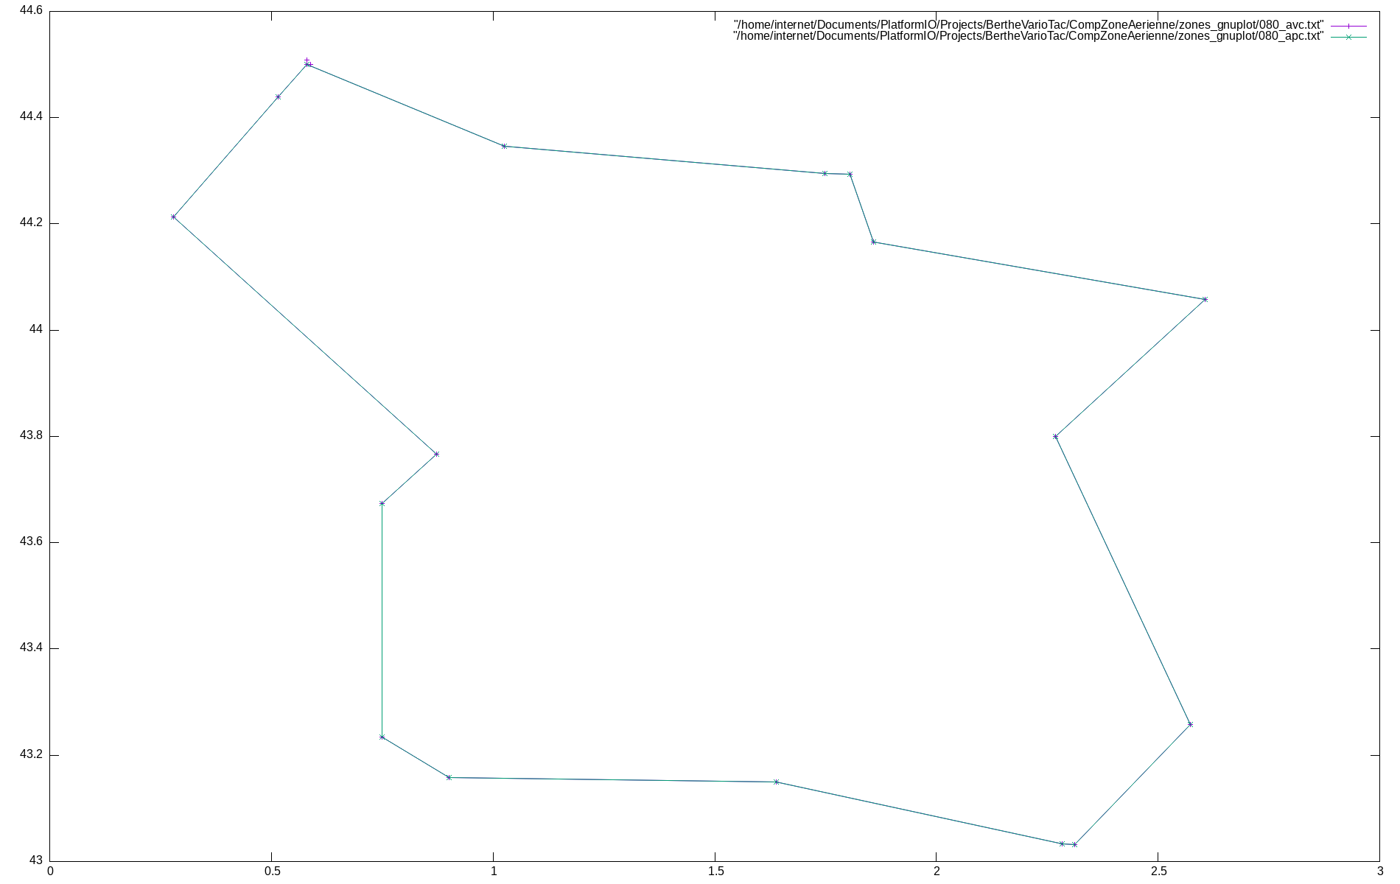
CompZoneAerienne/zones_gnuplot/080.png
