gitberthe/BertheVario213/CompZoneAerienne/zones_gnuplot/082.png

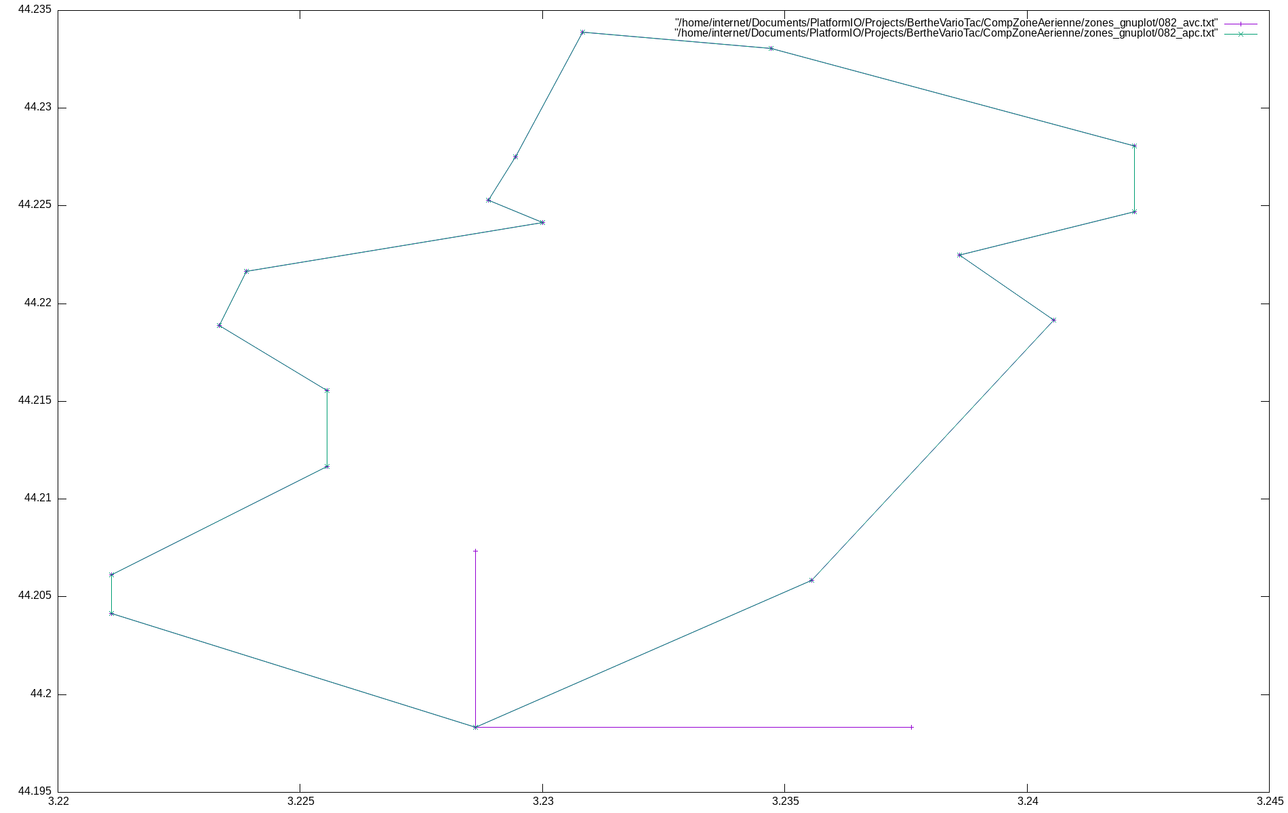
CompZoneAerienne/zones_gnuplot/082.png
