gitberthe/BertheVario213/CompZoneAerienne/zones_gnuplot/083.png

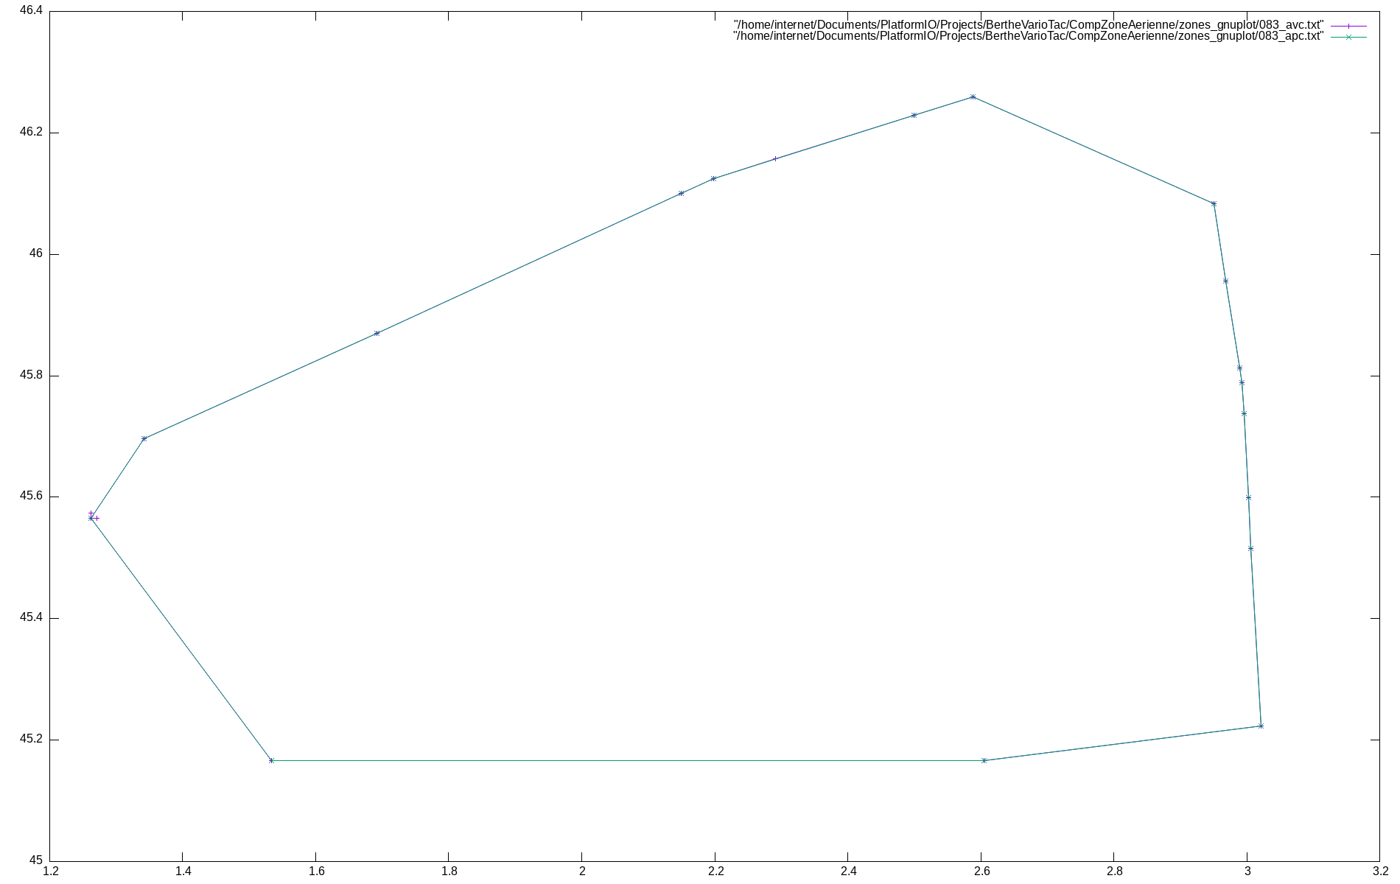
CompZoneAerienne/zones_gnuplot/083.png
