gitberthe/BertheVario213/CompZoneAerienne/zones_gnuplot/085.png

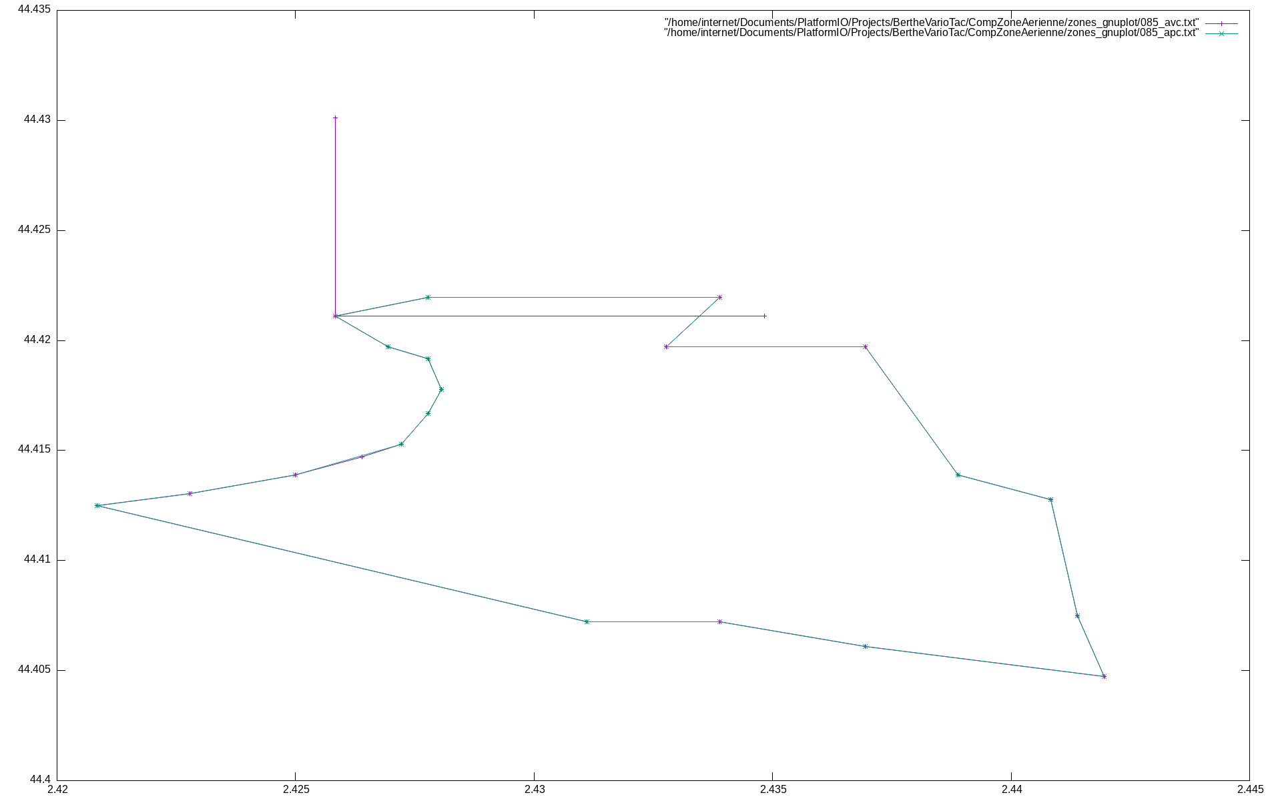
CompZoneAerienne/zones_gnuplot/085.png
