gitberthe/BertheVario213/CompZoneAerienne/zones_gnuplot/086.png

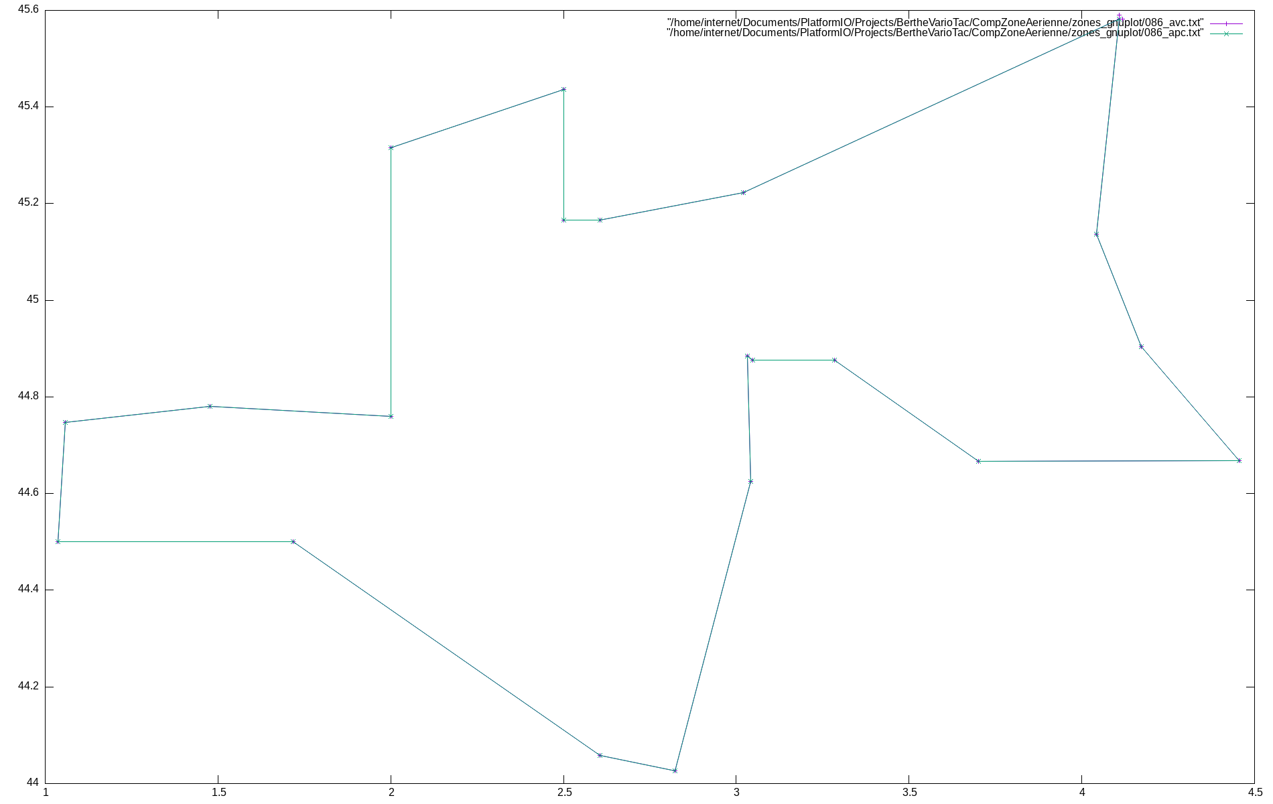
CompZoneAerienne/zones_gnuplot/086.png
