gitberthe/BertheVario213/CompZoneAerienne/zones_gnuplot/088.png

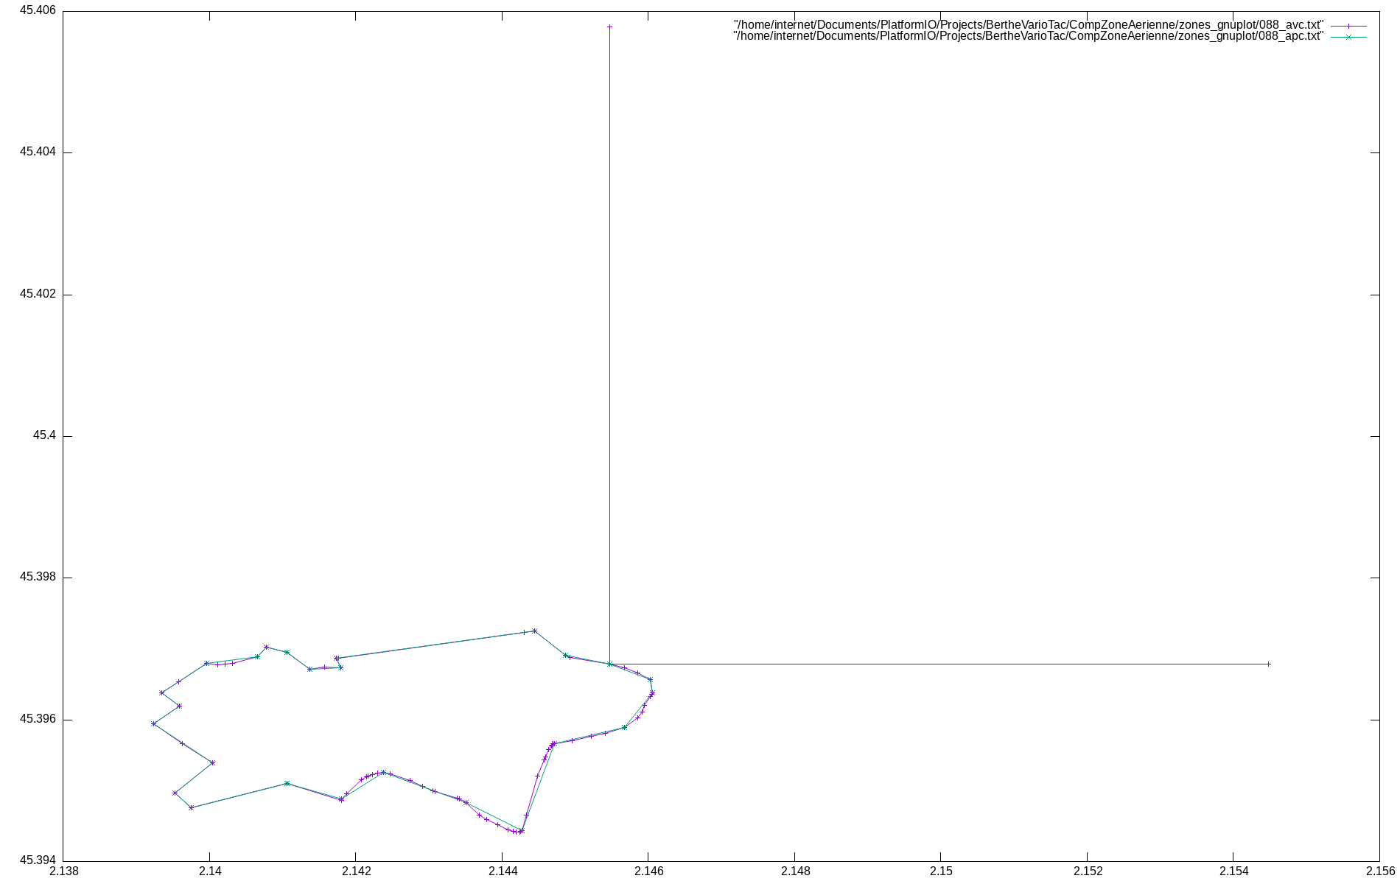
CompZoneAerienne/zones_gnuplot/088.png
