gitberthe/BertheVario213/CompZoneAerienne/zones_gnuplot/089.png

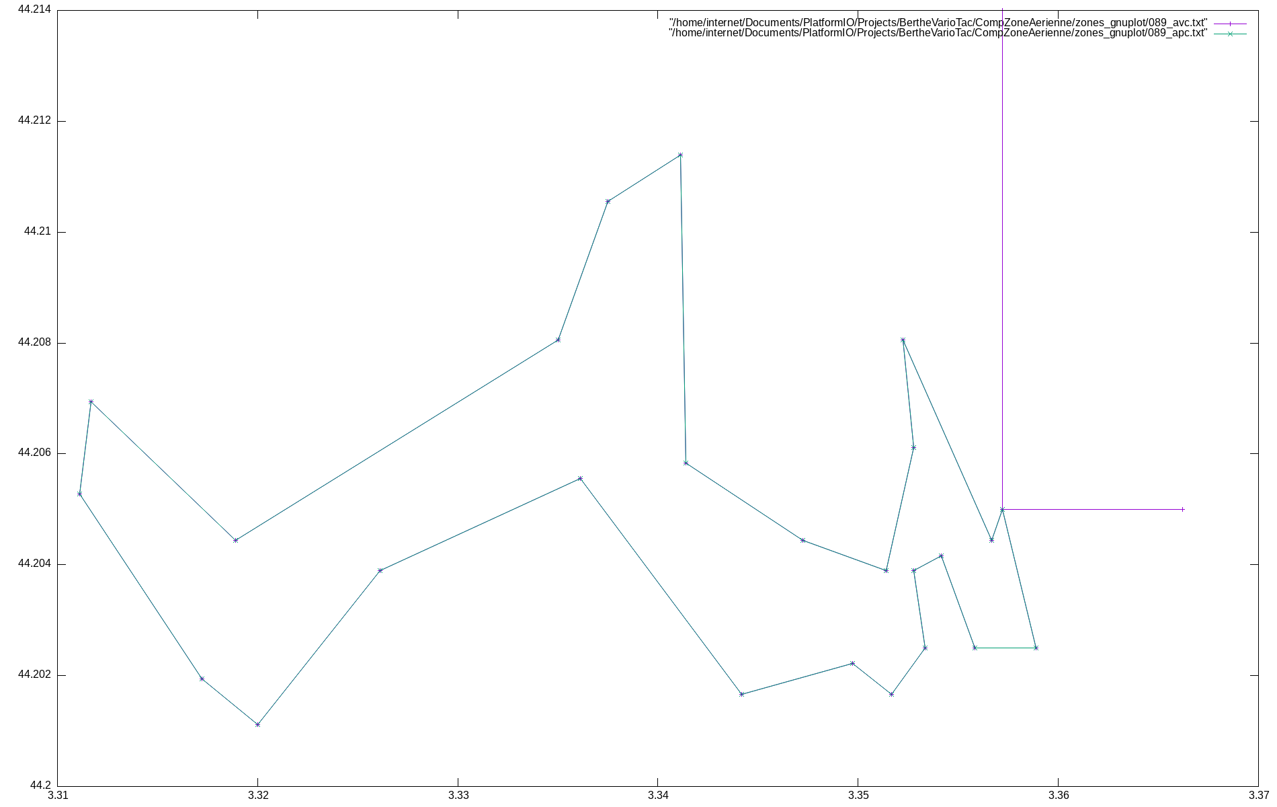
CompZoneAerienne/zones_gnuplot/089.png
