gitberthe/BertheVario213/CompZoneAerienne/zones_gnuplot/091.png

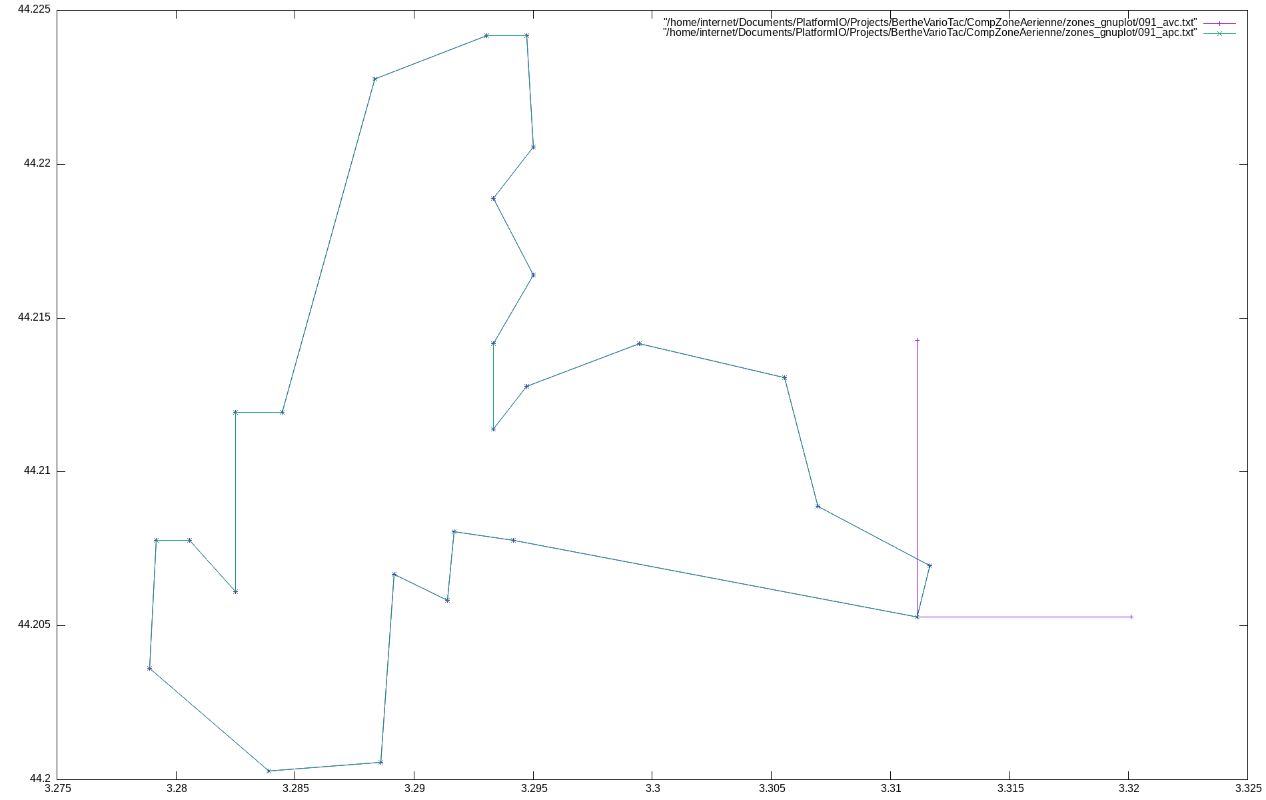
CompZoneAerienne/zones_gnuplot/091.png
