gitberthe/BertheVario213/CompZoneAerienne/zones_gnuplot/093.png

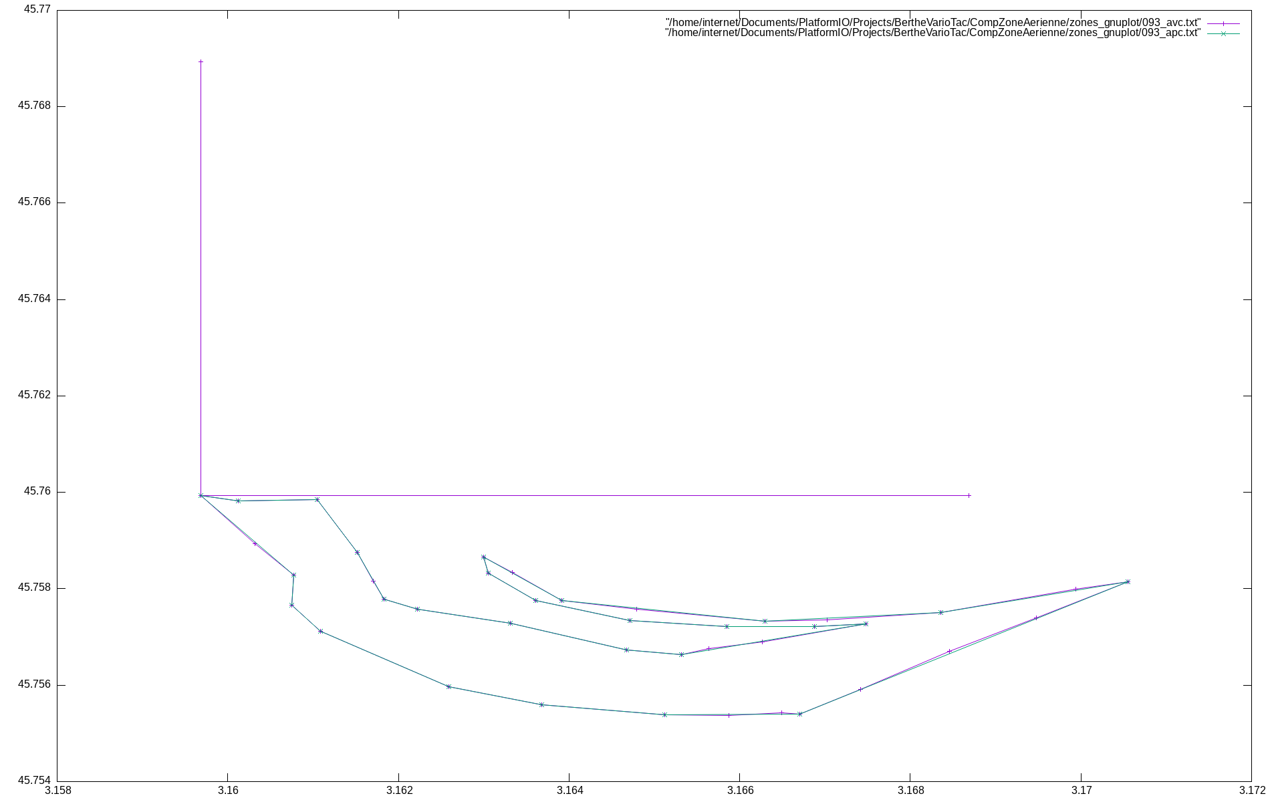
CompZoneAerienne/zones_gnuplot/093.png
