gitberthe/BertheVario213/CompZoneAerienne/zones_gnuplot/094.png

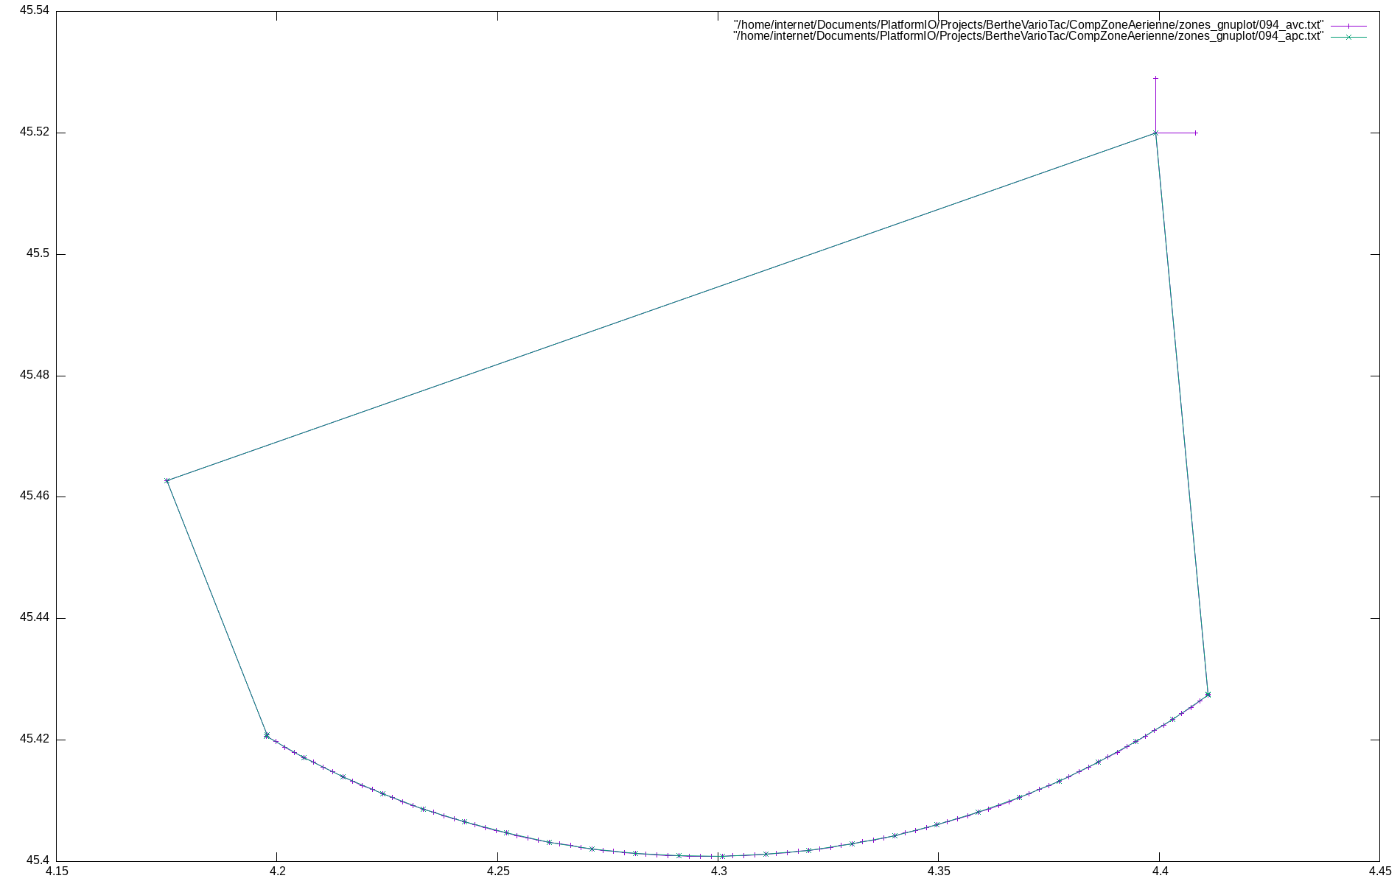
CompZoneAerienne/zones_gnuplot/094.png
