gitberthe/BertheVario213/CompZoneAerienne/zones_gnuplot/095.png

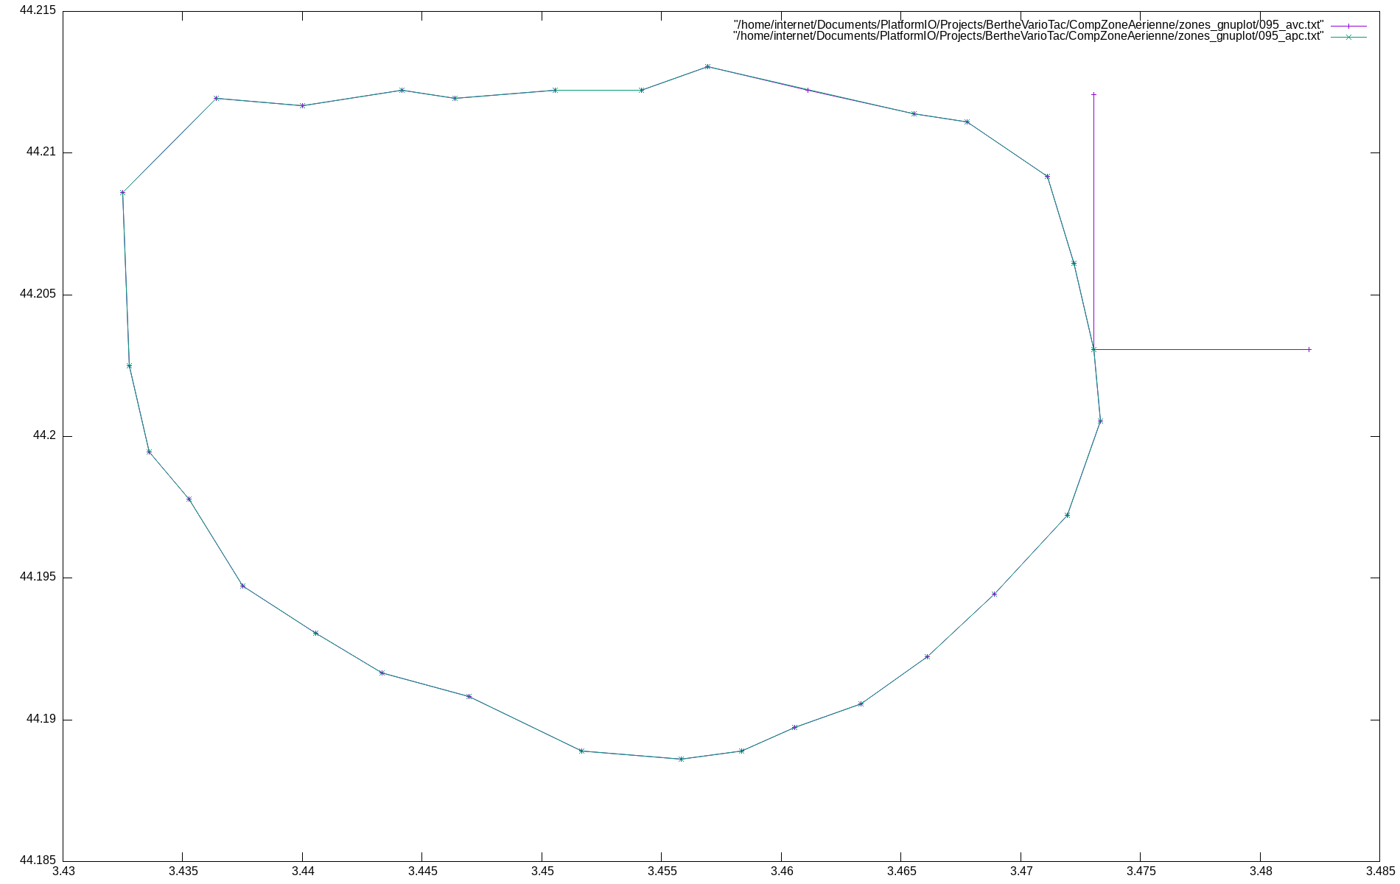
CompZoneAerienne/zones_gnuplot/095.png
