gitberthe/BertheVario213/CompZoneAerienne/zones_gnuplot/096.png

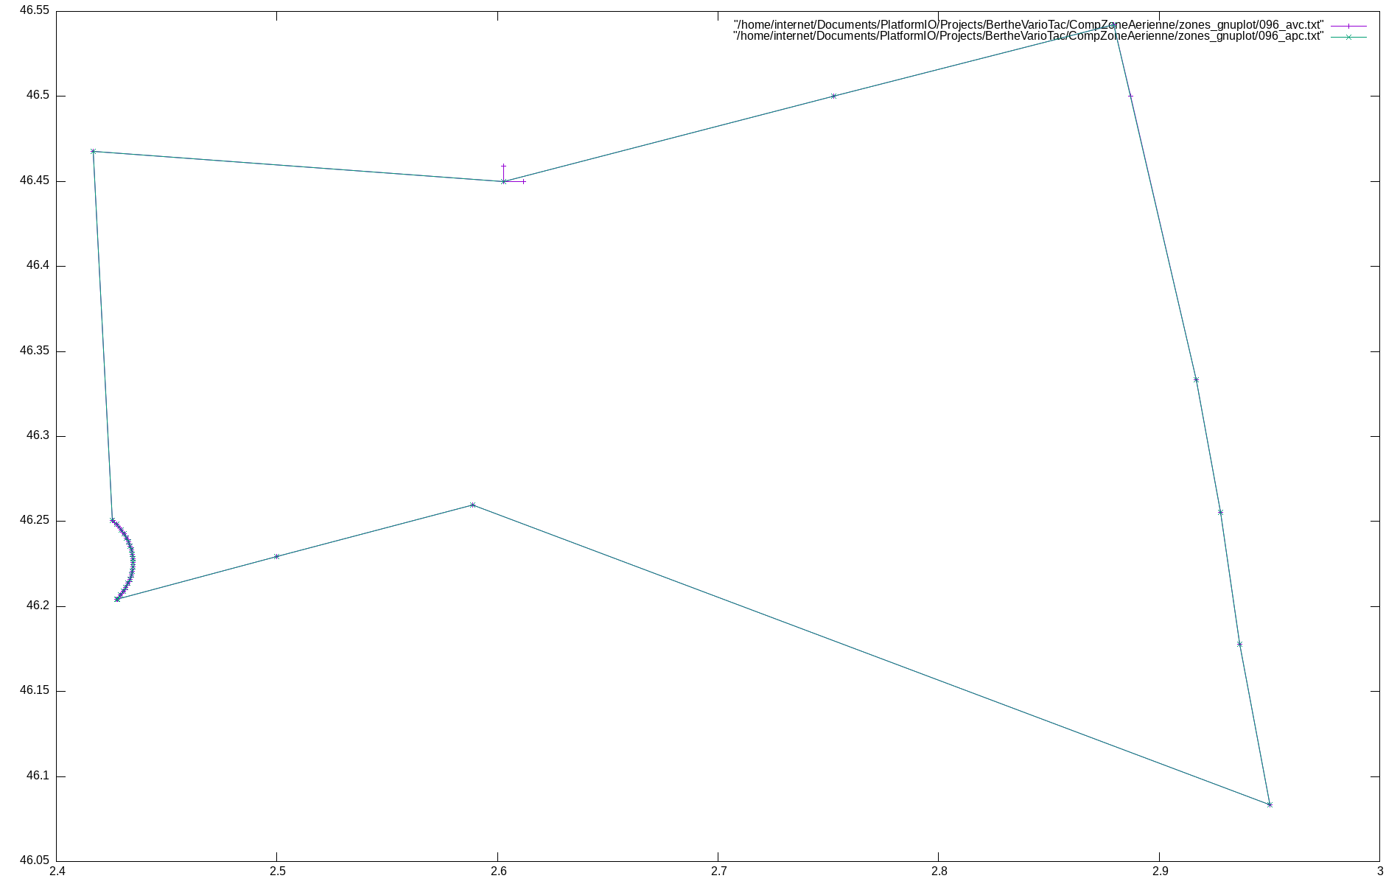
CompZoneAerienne/zones_gnuplot/096.png
