gitberthe/BertheVario213/CompZoneAerienne/zones_gnuplot/097.png

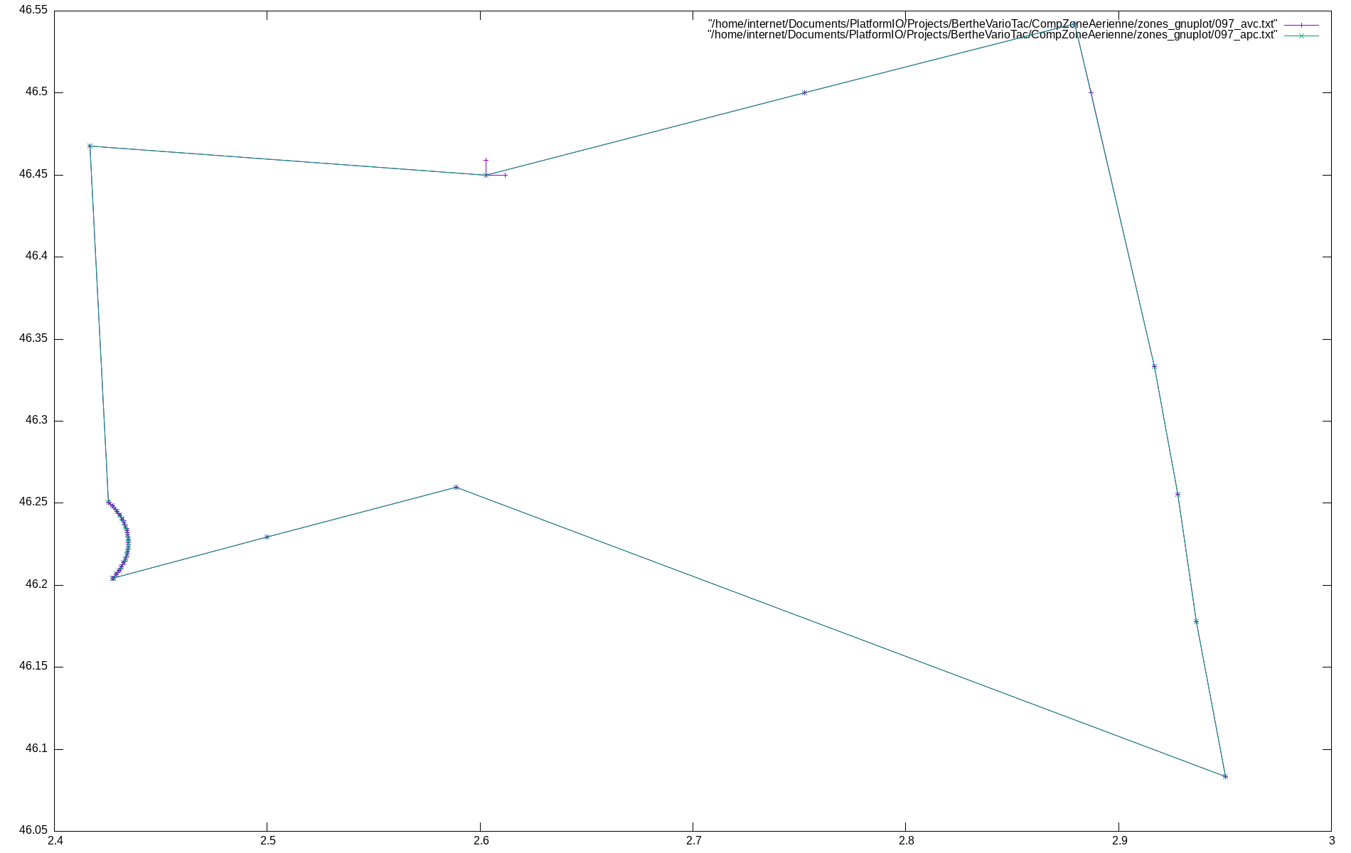
CompZoneAerienne/zones_gnuplot/097.png
