gitberthe/BertheVario213/CompZoneAerienne/zones_gnuplot/098.png

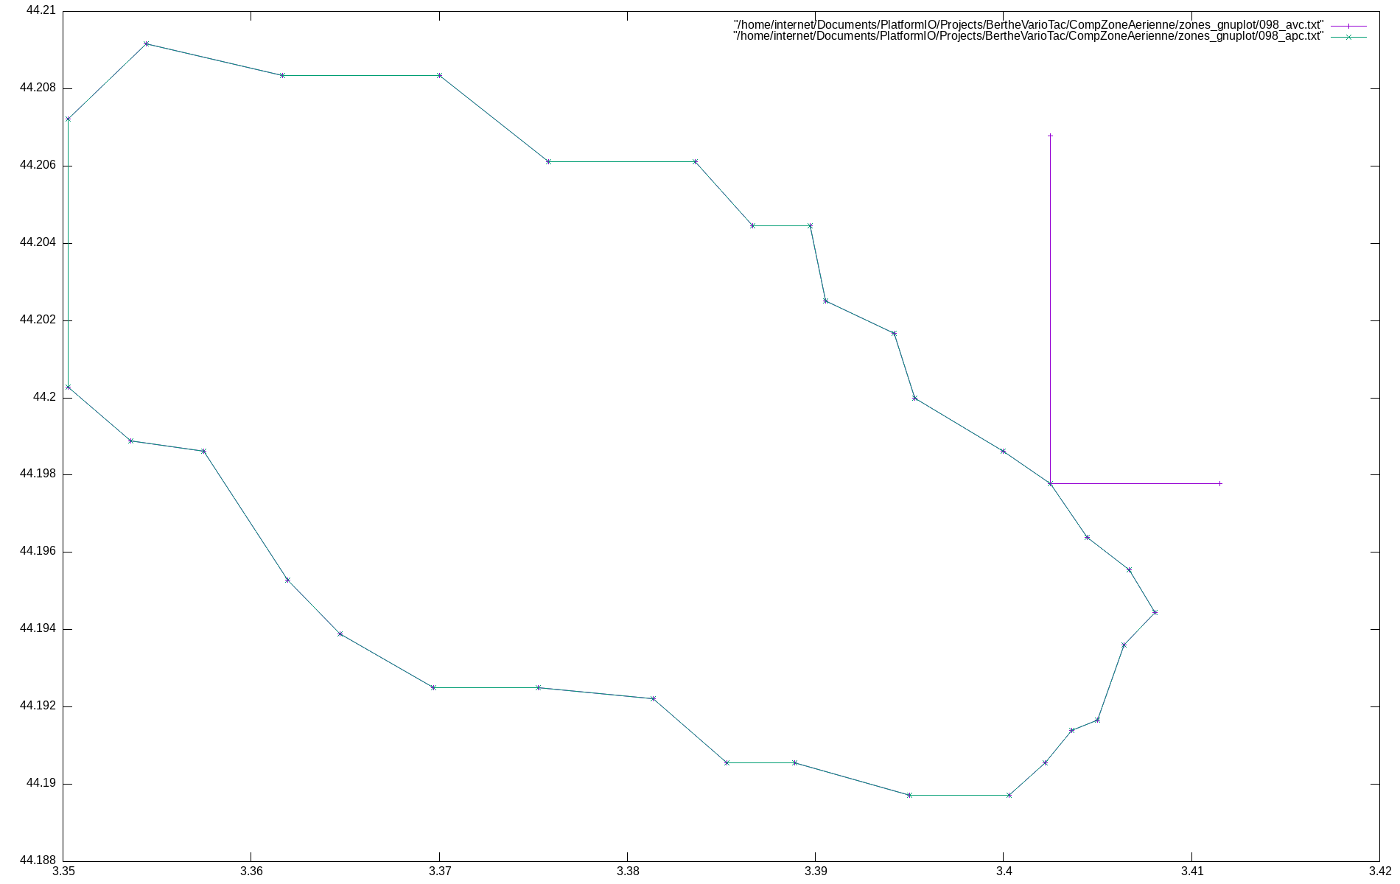
CompZoneAerienne/zones_gnuplot/098.png
