gitberthe/BertheVario213/CompZoneAerienne/zones_gnuplot/099.png

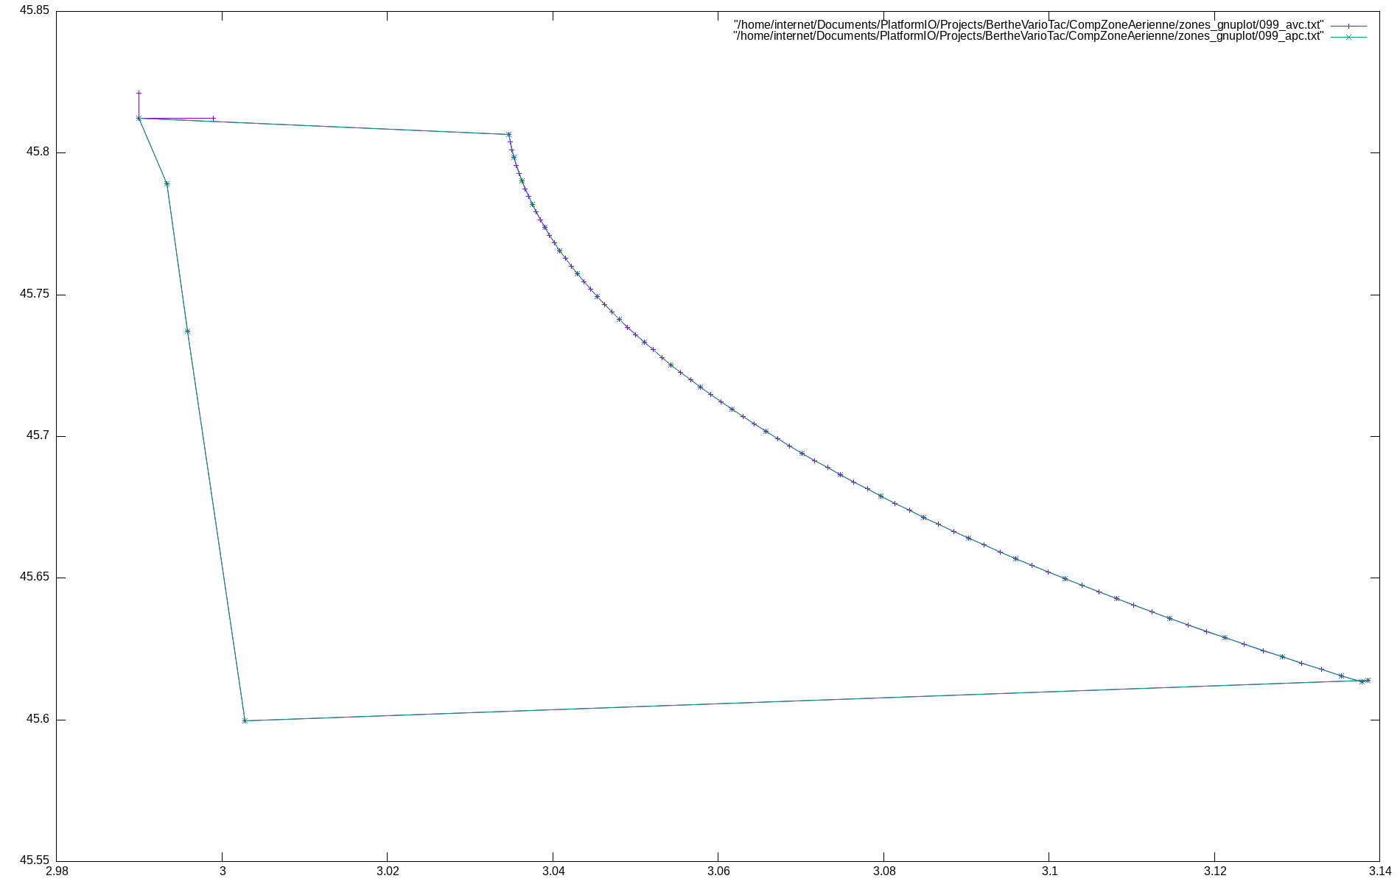
CompZoneAerienne/zones_gnuplot/099.png
