gitberthe/BertheVario213/CompZoneAerienne/zones_gnuplot/100.png

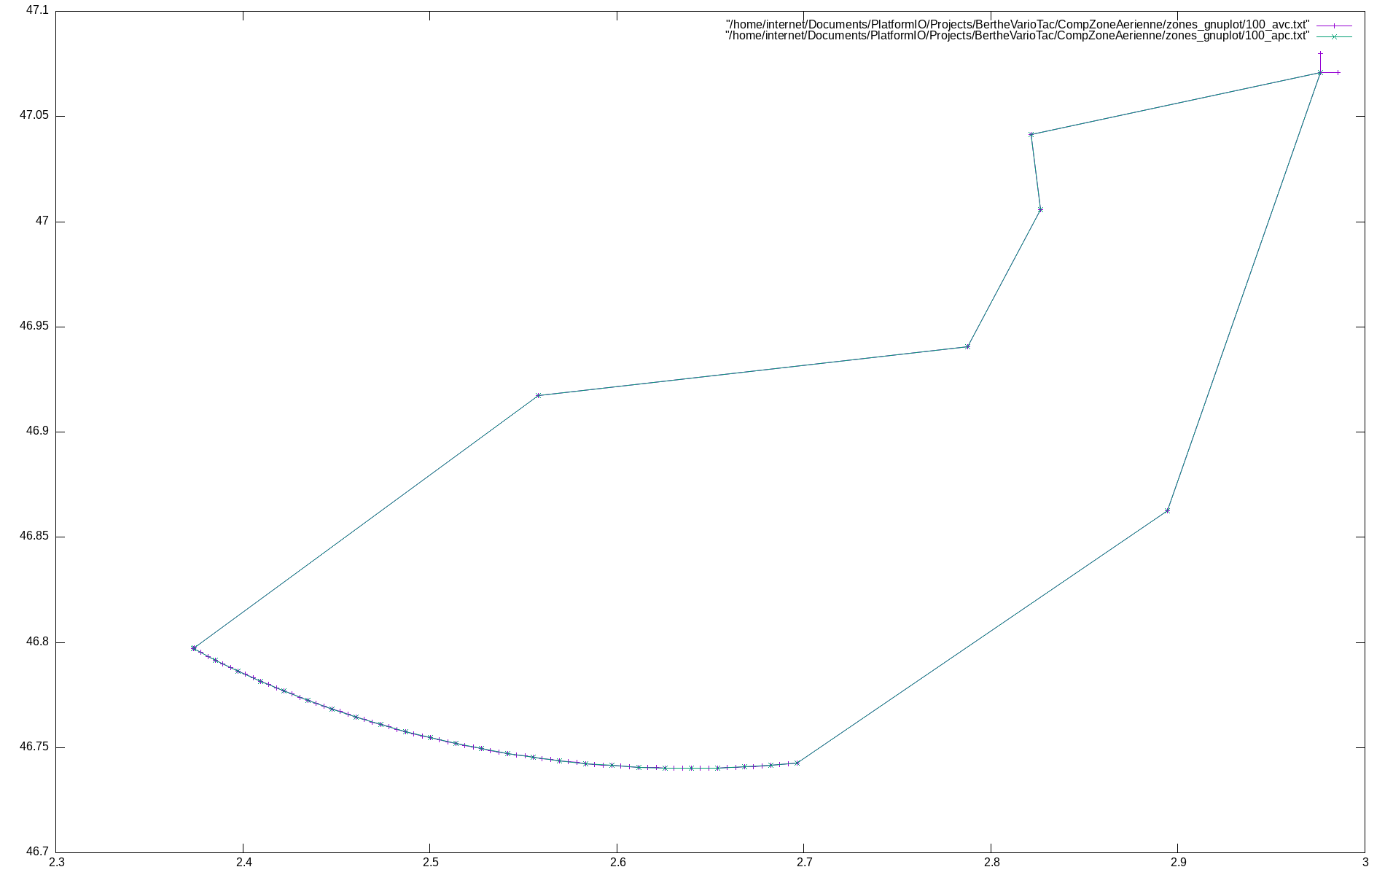
CompZoneAerienne/zones_gnuplot/100.png
