gitberthe/BertheVario213/CompZoneAerienne/zones_gnuplot/101.png

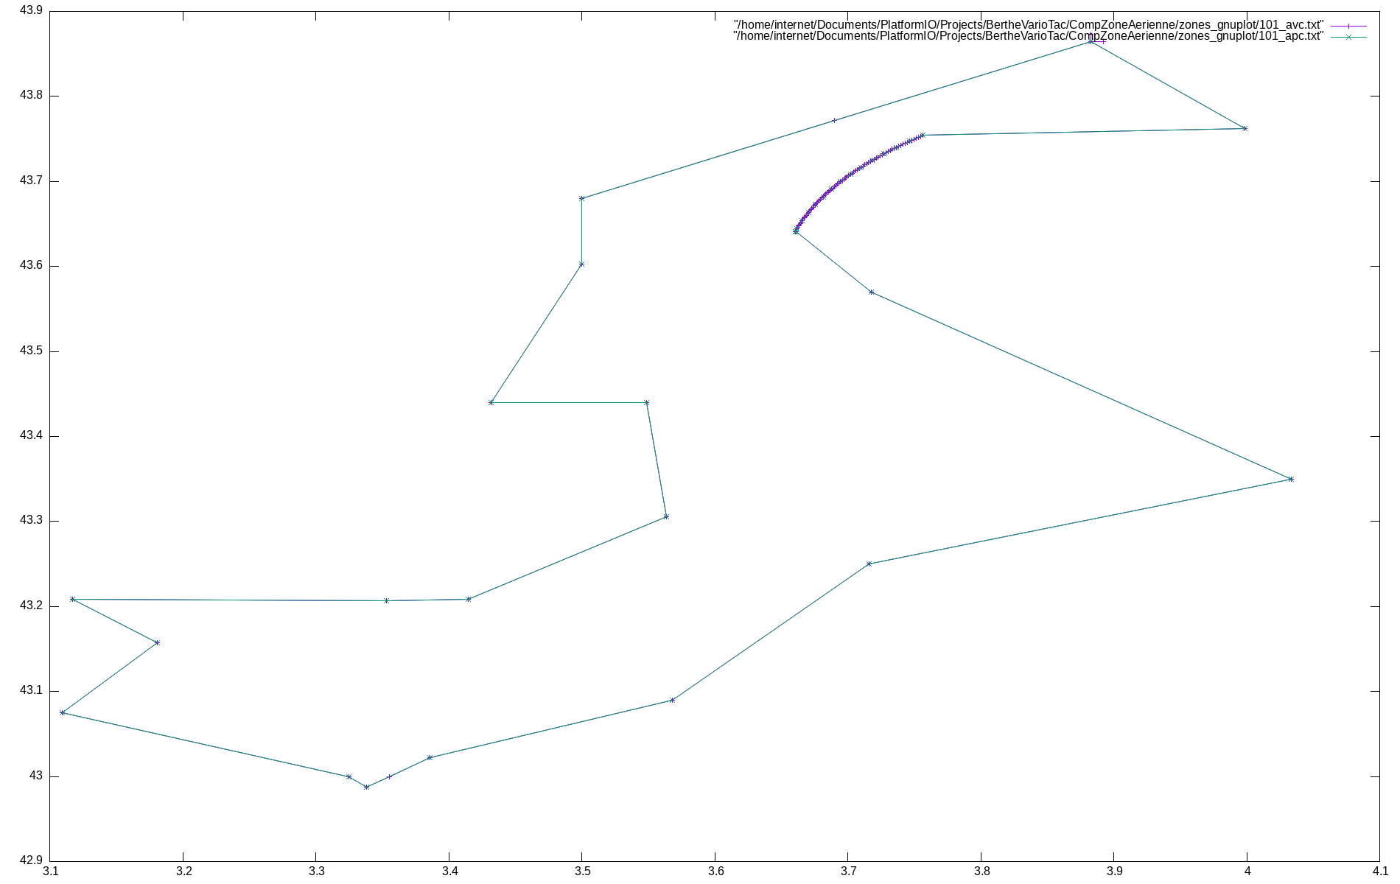
CompZoneAerienne/zones_gnuplot/101.png
