gitberthe/BertheVario213/CompZoneAerienne/zones_gnuplot/102.png

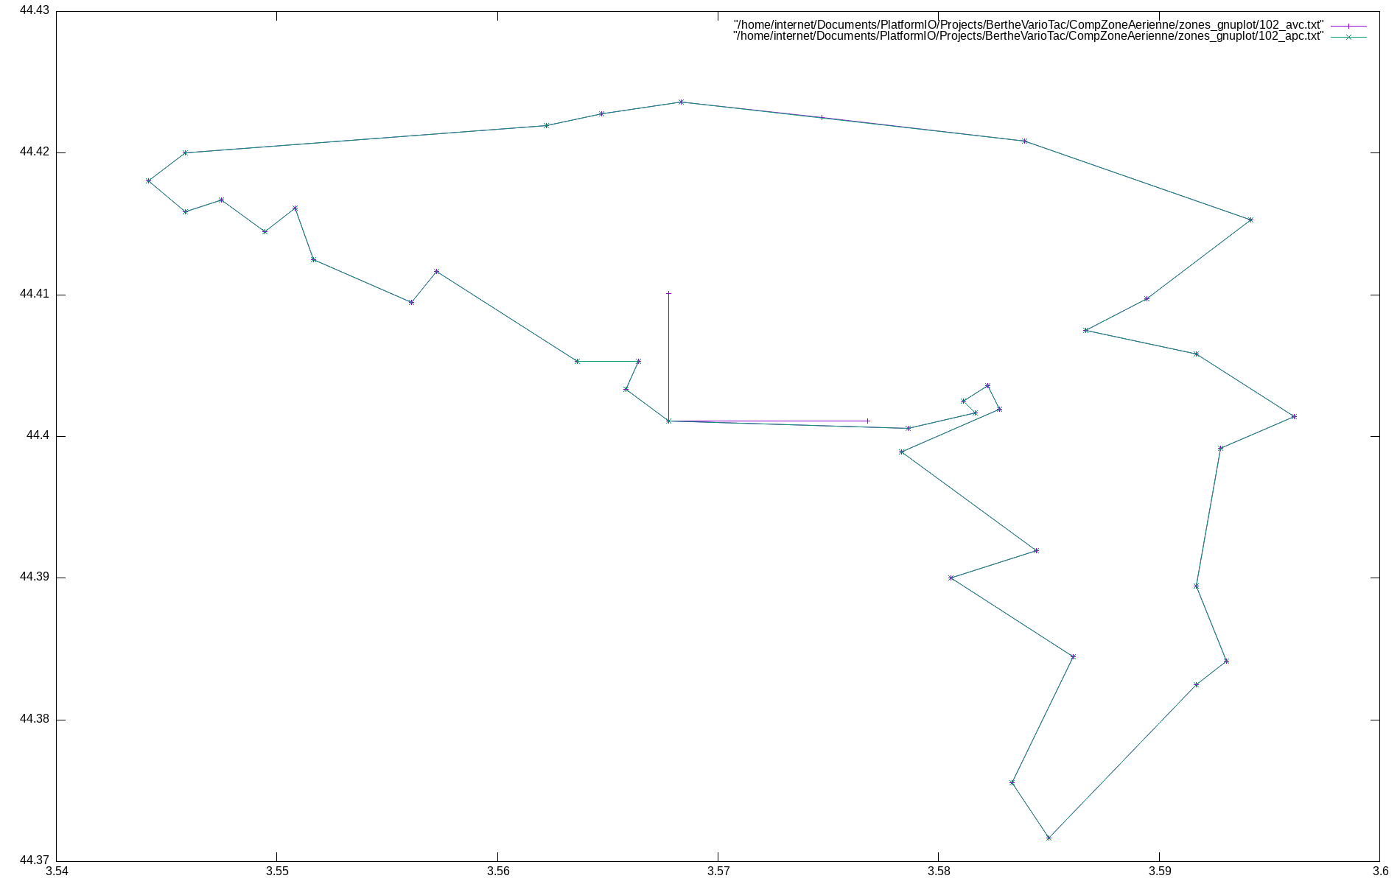
CompZoneAerienne/zones_gnuplot/102.png
