gitberthe/BertheVario213/CompZoneAerienne/zones_gnuplot/103.png

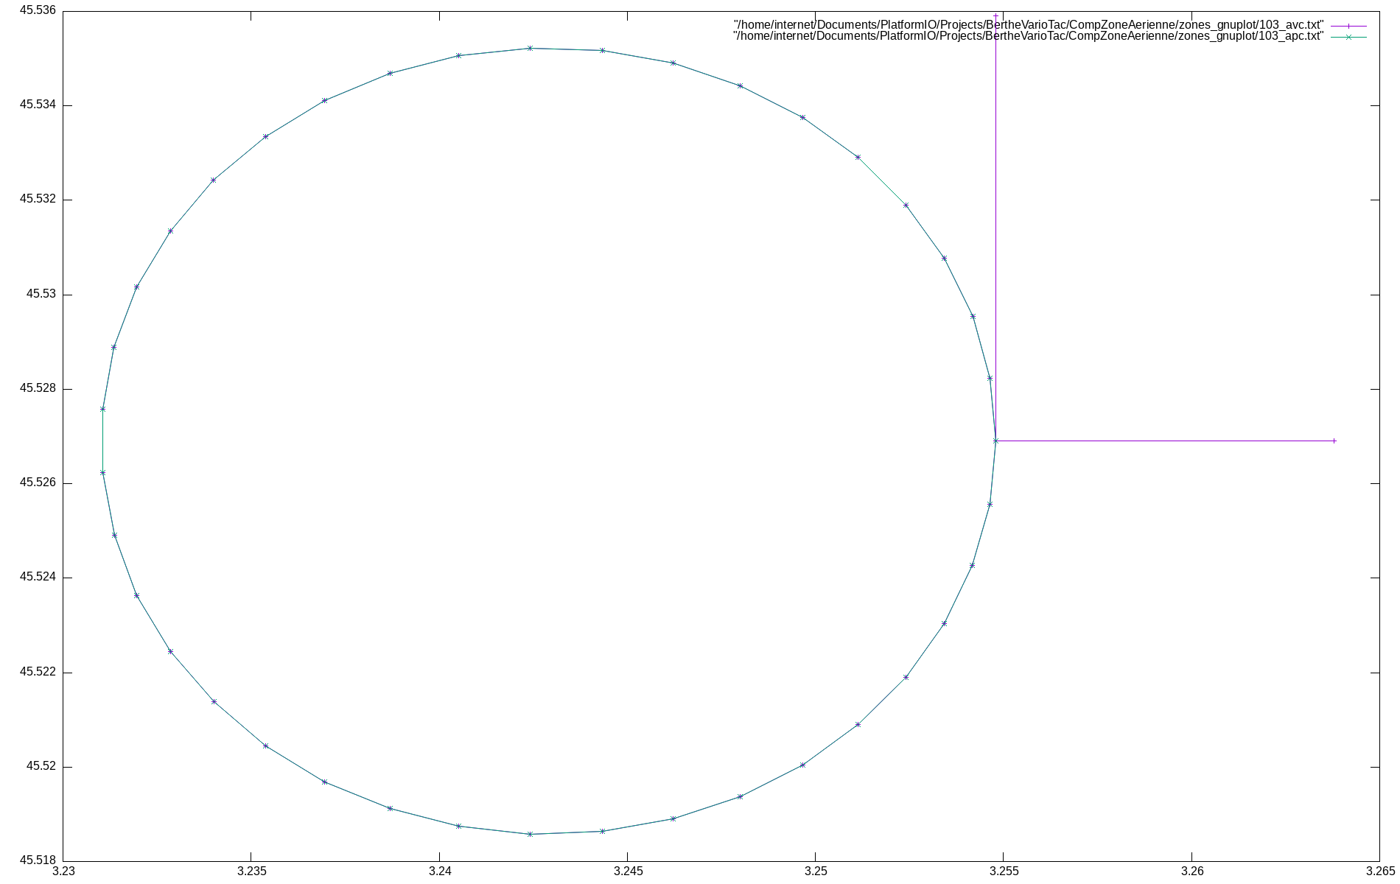
CompZoneAerienne/zones_gnuplot/103.png
