gitberthe/BertheVario213/CompZoneAerienne/zones_gnuplot/104.png

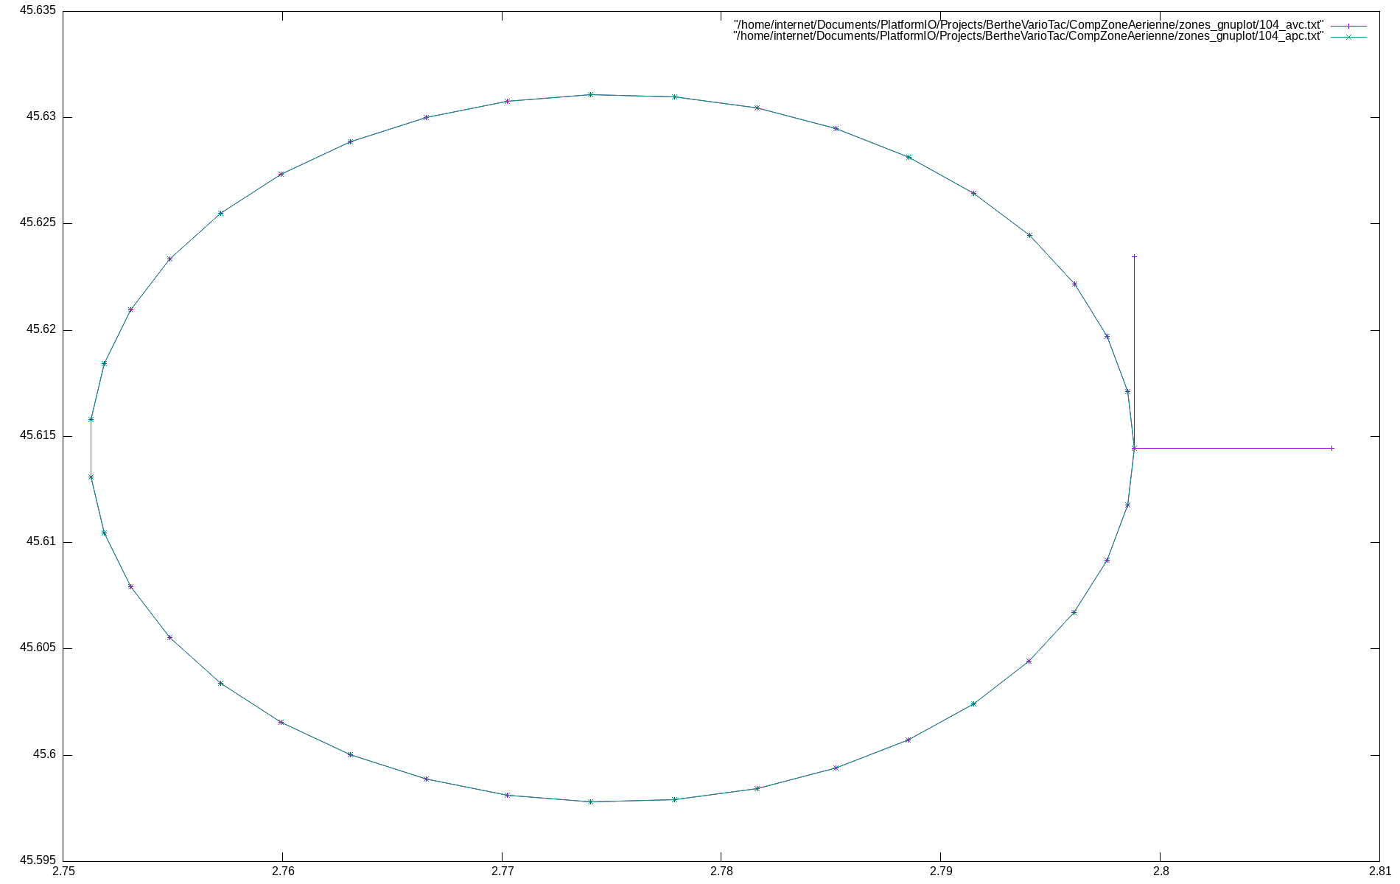
CompZoneAerienne/zones_gnuplot/104.png
