gitberthe/BertheVario213/CompZoneAerienne/zones_gnuplot/106.png

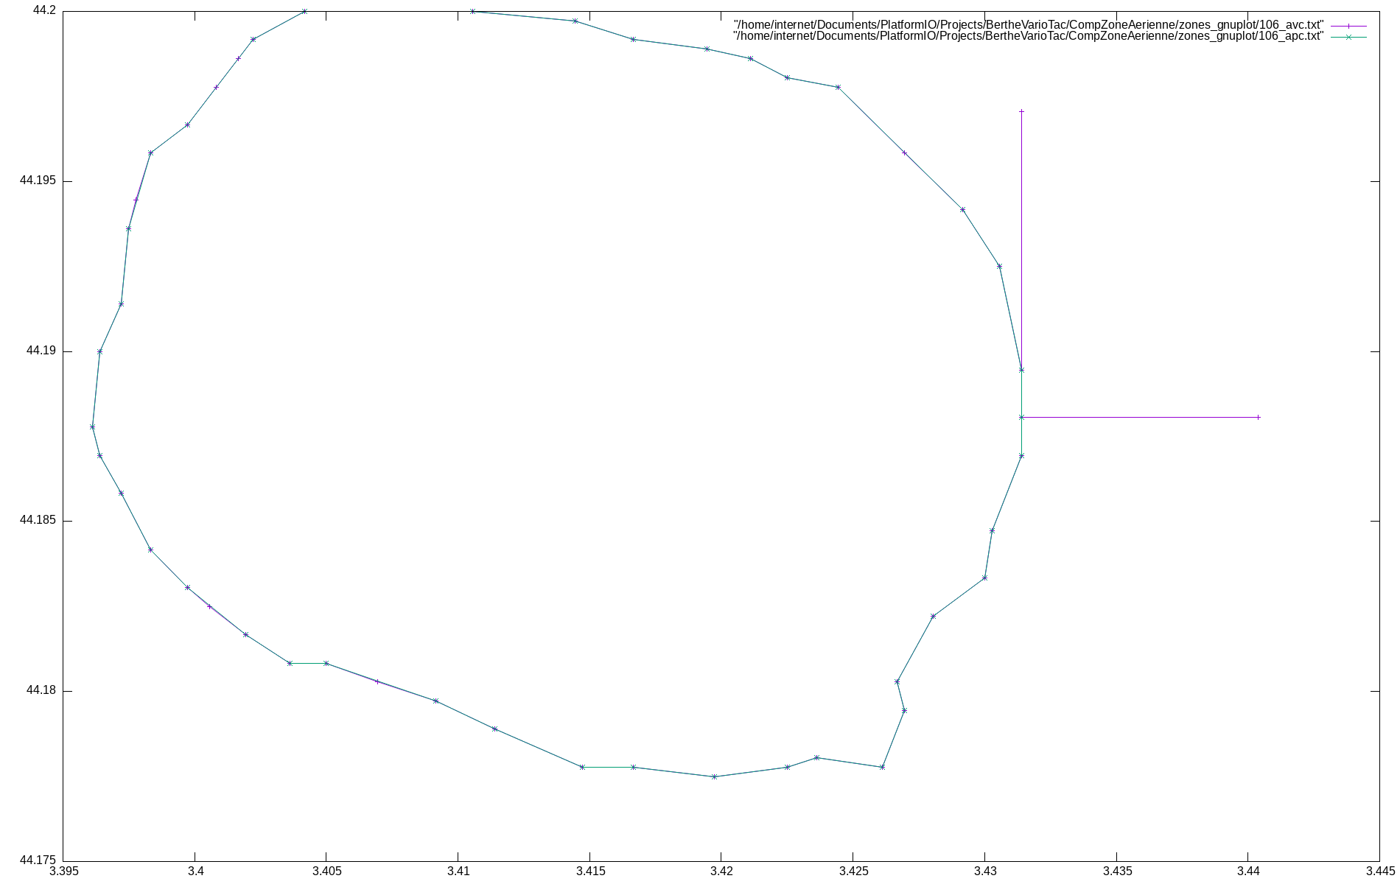
CompZoneAerienne/zones_gnuplot/106.png
