gitberthe/BertheVario213/CompZoneAerienne/zones_gnuplot/107.png

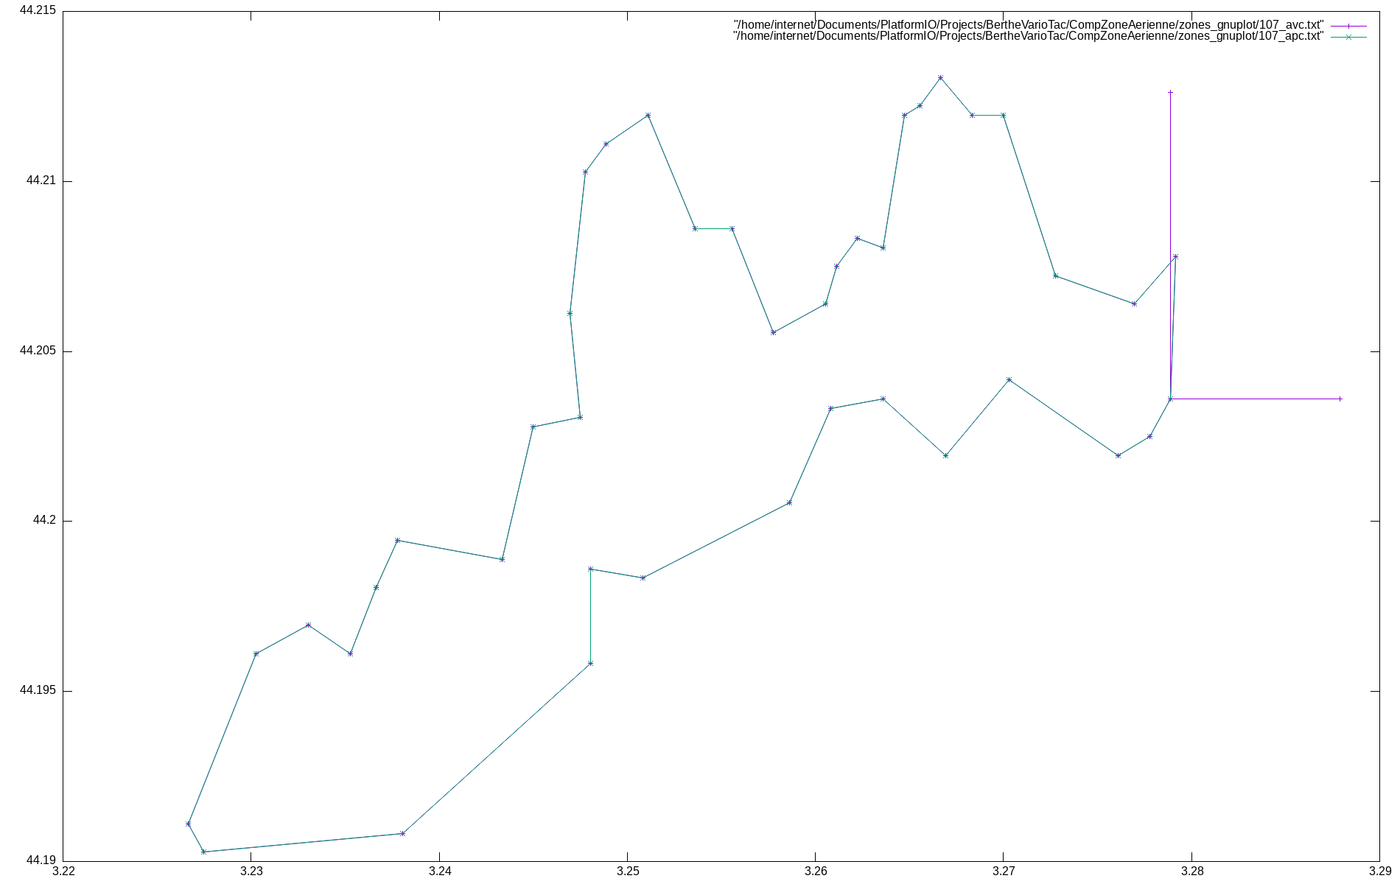
CompZoneAerienne/zones_gnuplot/107.png
