gitberthe/BertheVario213/CompZoneAerienne/zones_gnuplot/108.png

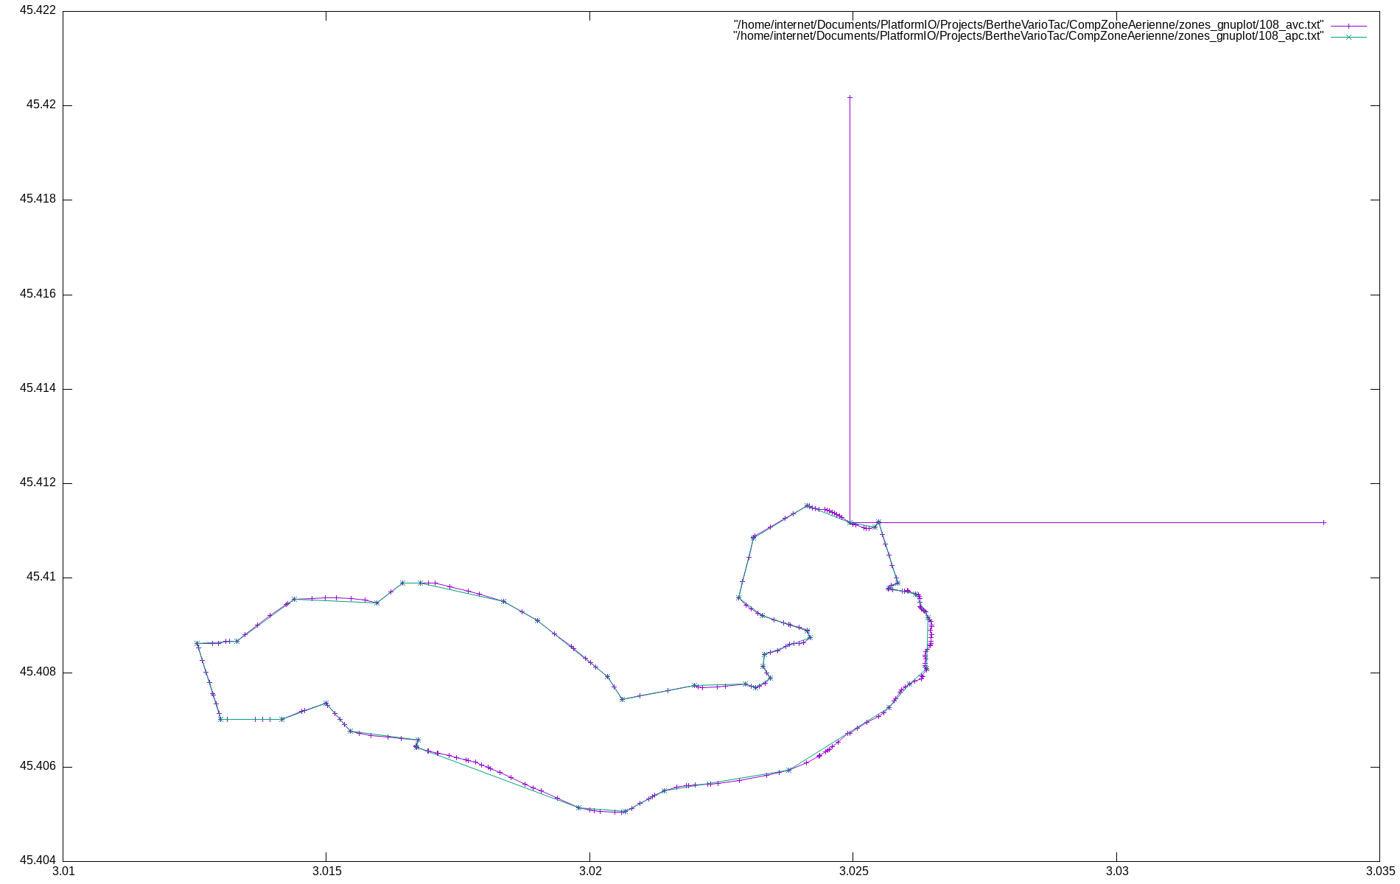
CompZoneAerienne/zones_gnuplot/108.png
