gitberthe/BertheVario213/CompZoneAerienne/zones_gnuplot/110.png

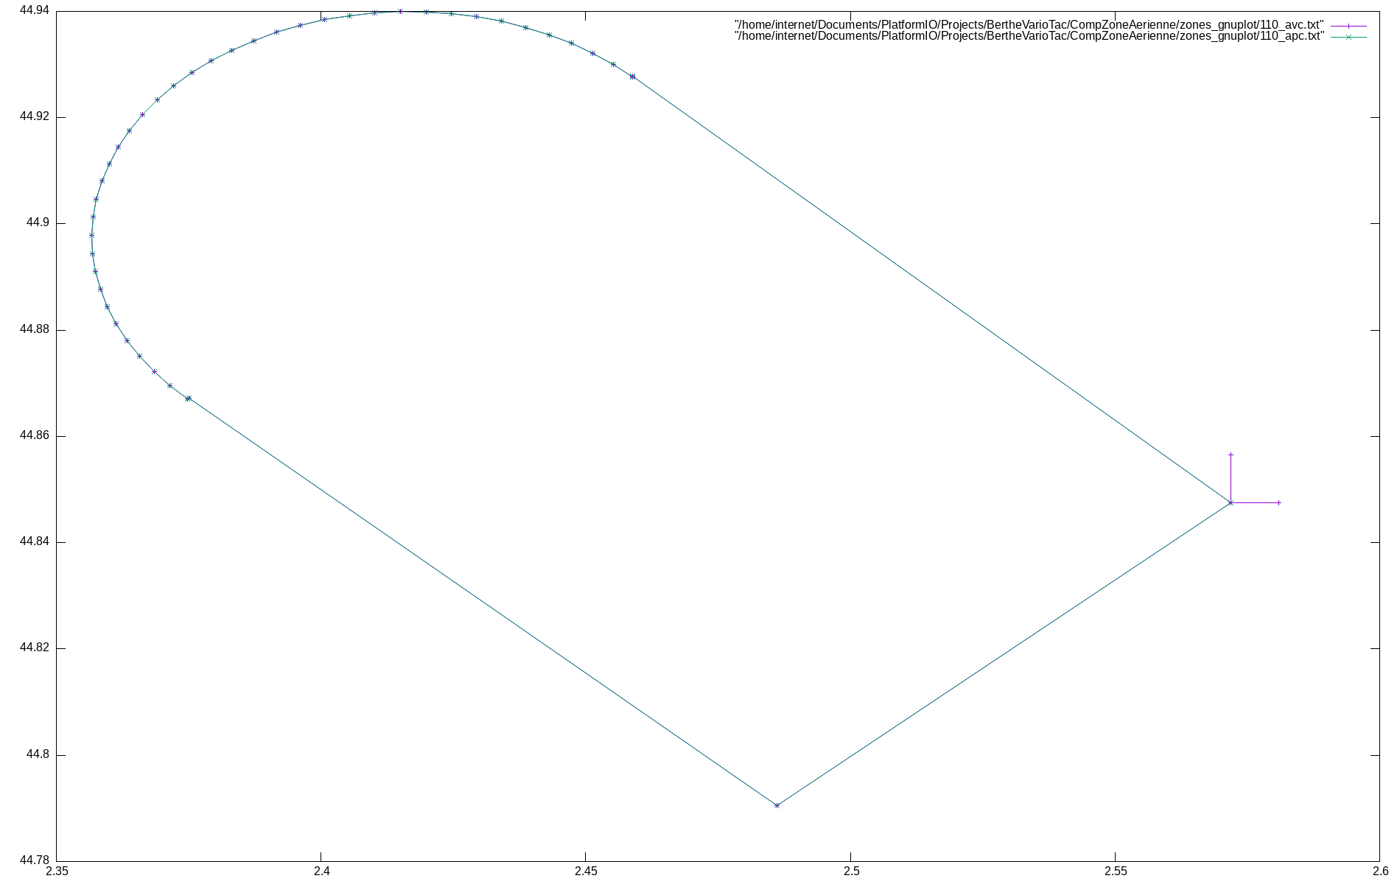
CompZoneAerienne/zones_gnuplot/110.png
