gitberthe/BertheVario213/CompZoneAerienne/zones_gnuplot/111.png

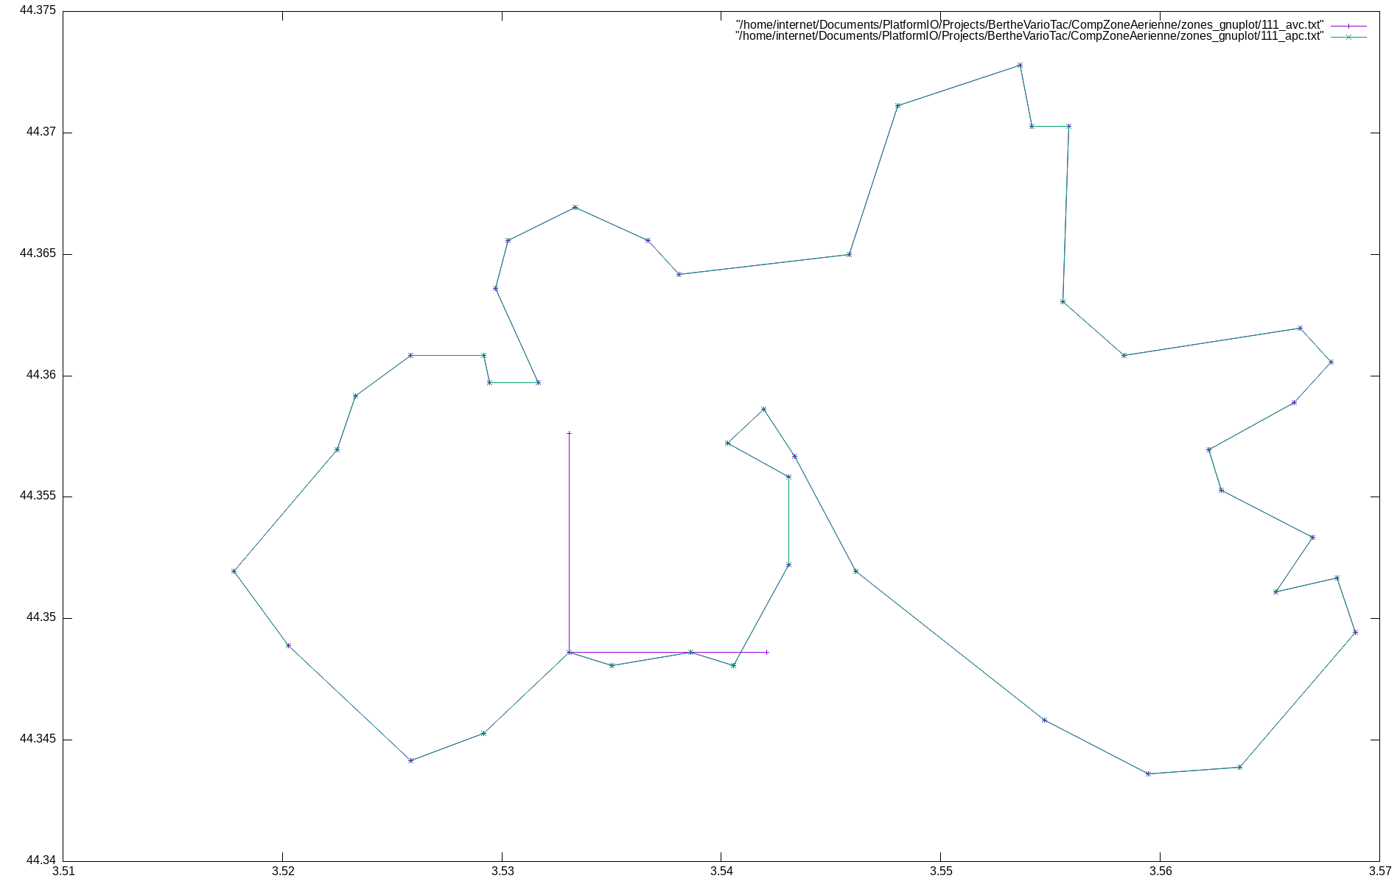
CompZoneAerienne/zones_gnuplot/111.png
