gitberthe/BertheVario213/CompZoneAerienne/zones_gnuplot/112.png

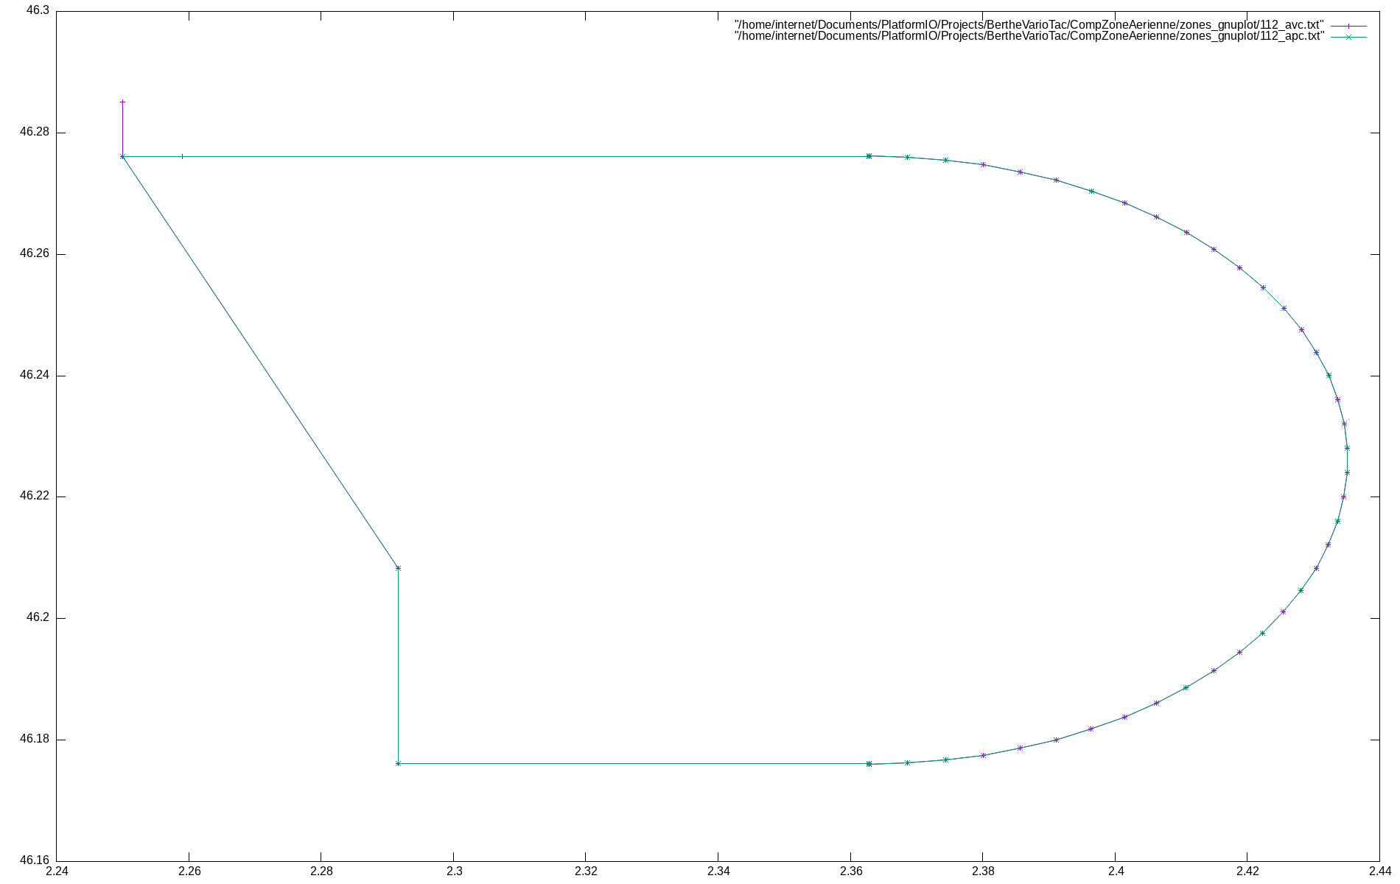
CompZoneAerienne/zones_gnuplot/112.png
