gitberthe/BertheVario213/CompZoneAerienne/zones_gnuplot/113.png

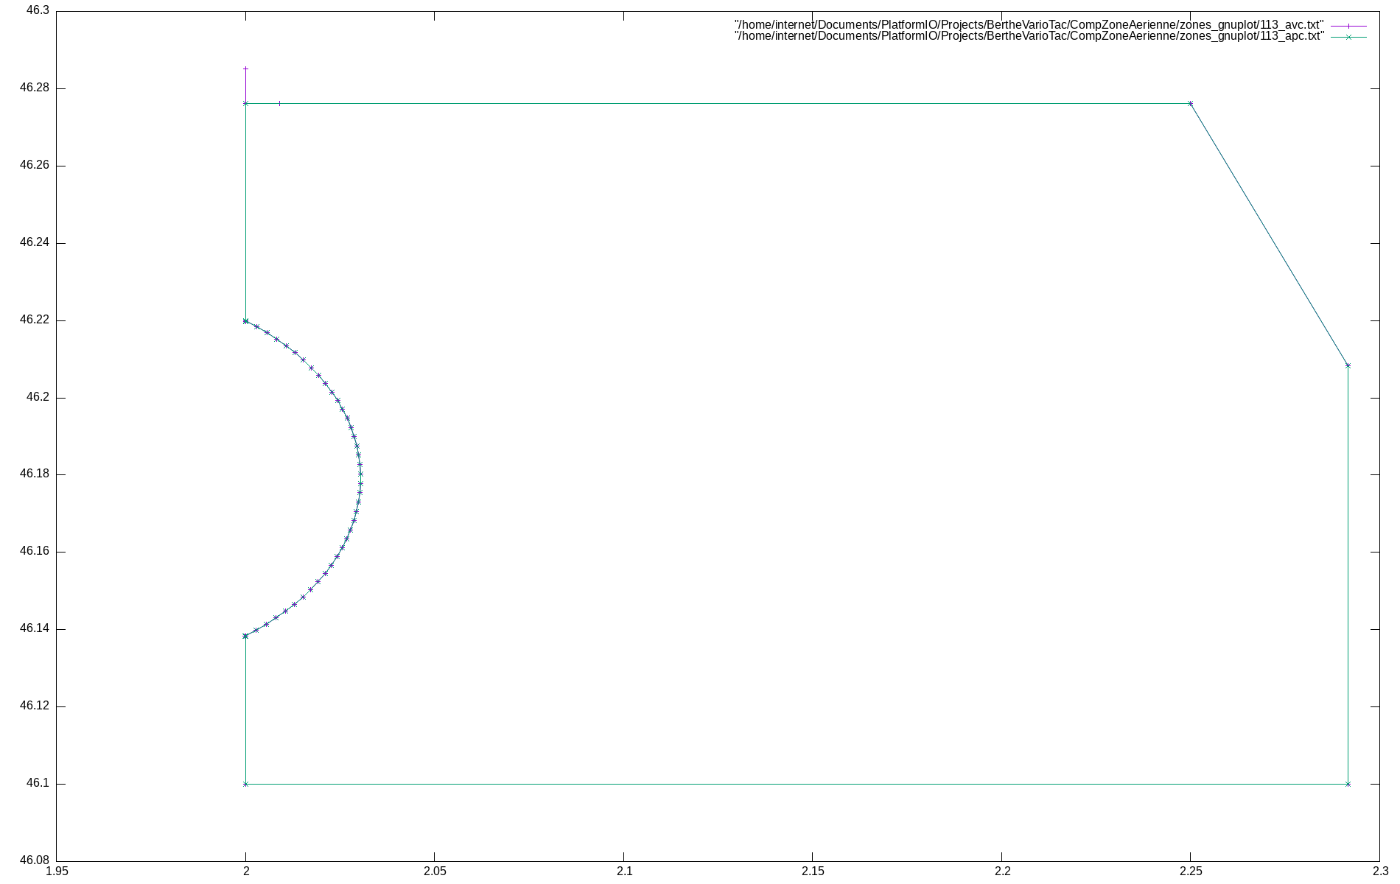
CompZoneAerienne/zones_gnuplot/113.png
