gitberthe/BertheVario213/CompZoneAerienne/zones_gnuplot/114.png

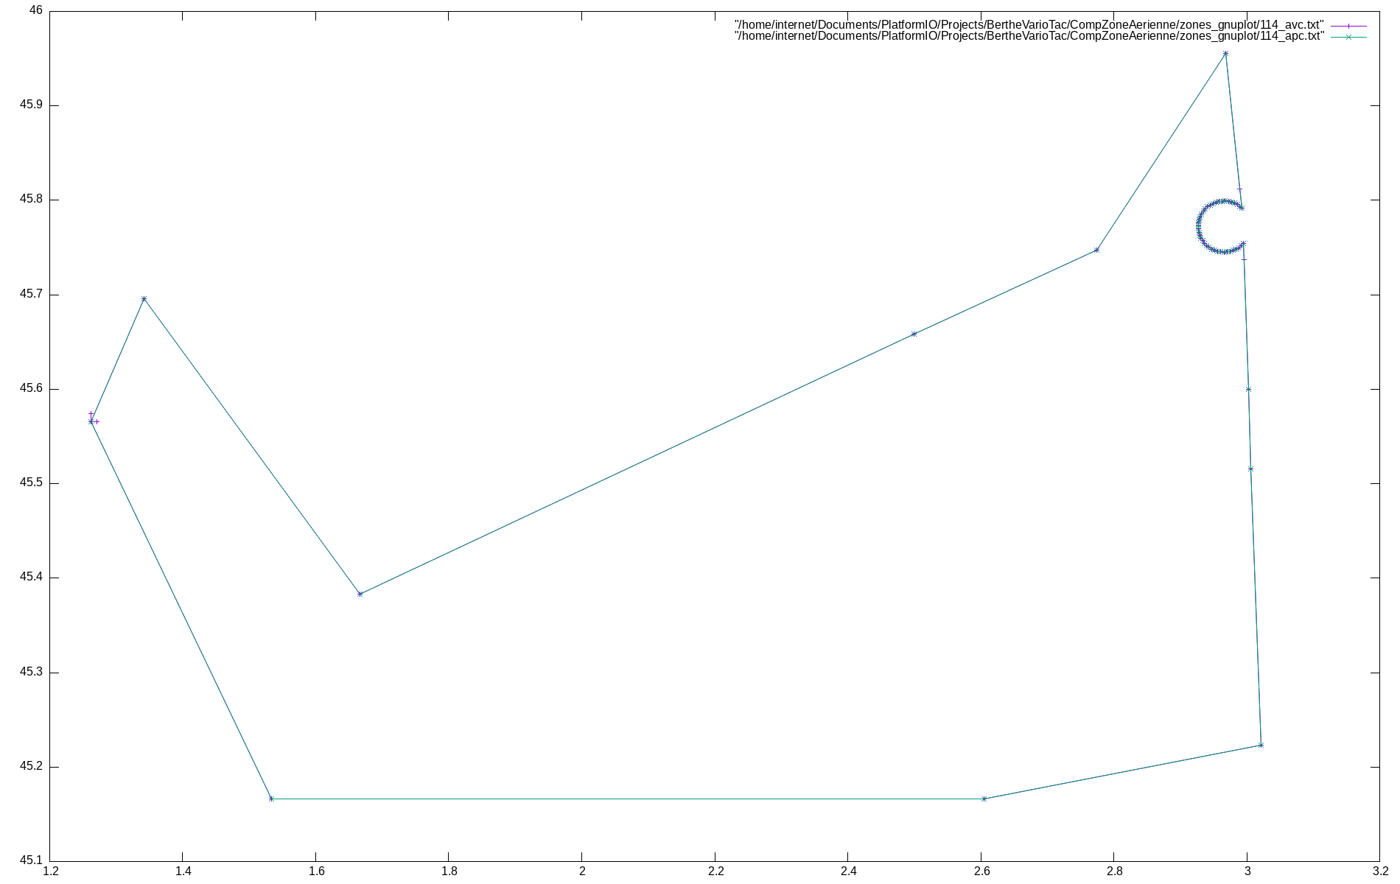
CompZoneAerienne/zones_gnuplot/114.png
