gitberthe/BertheVario213/CompZoneAerienne/zones_gnuplot/116.png

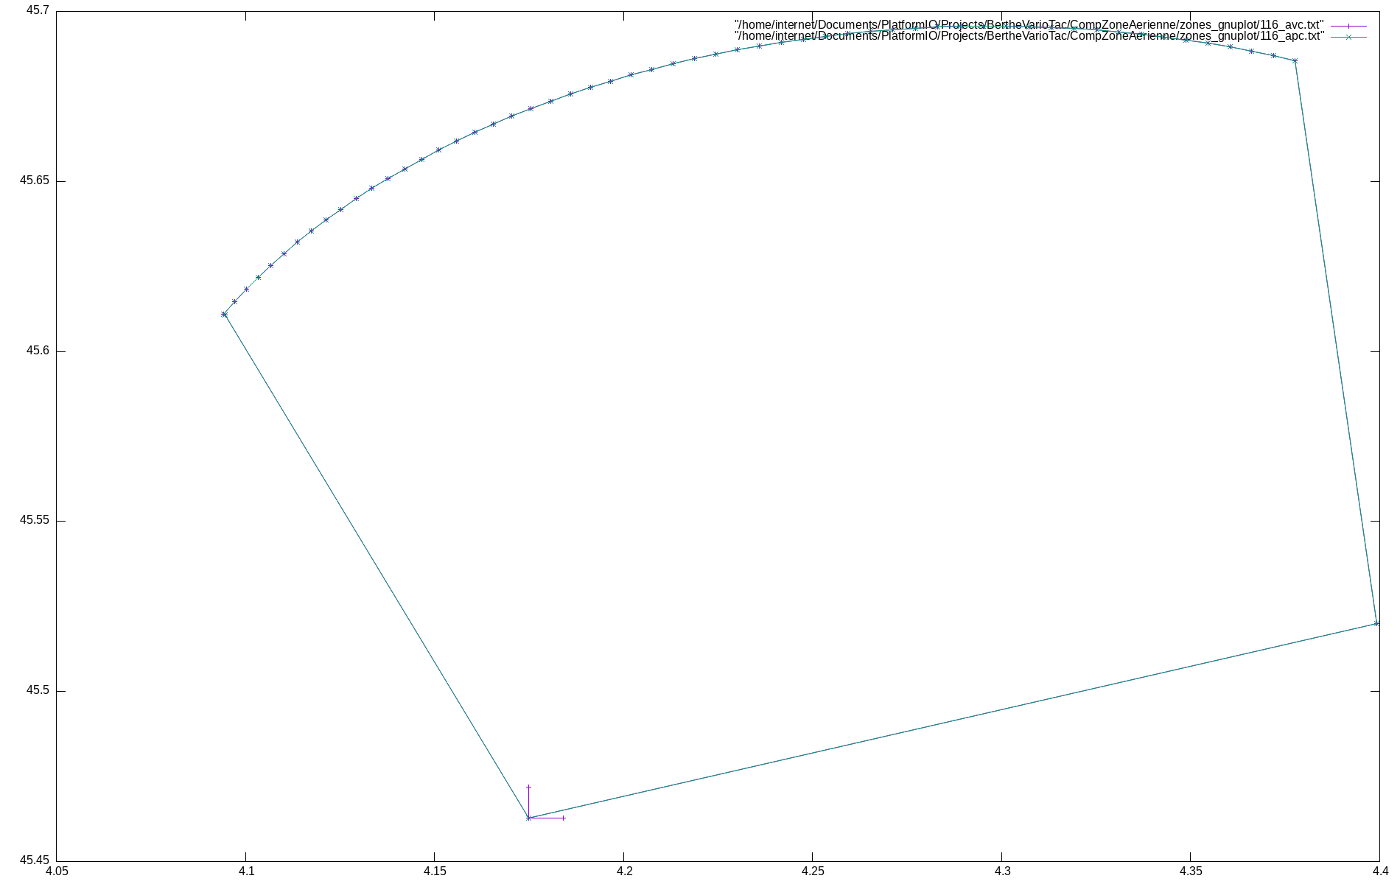
CompZoneAerienne/zones_gnuplot/116.png
