gitberthe/BertheVario213/CompZoneAerienne/zones_gnuplot/118.png

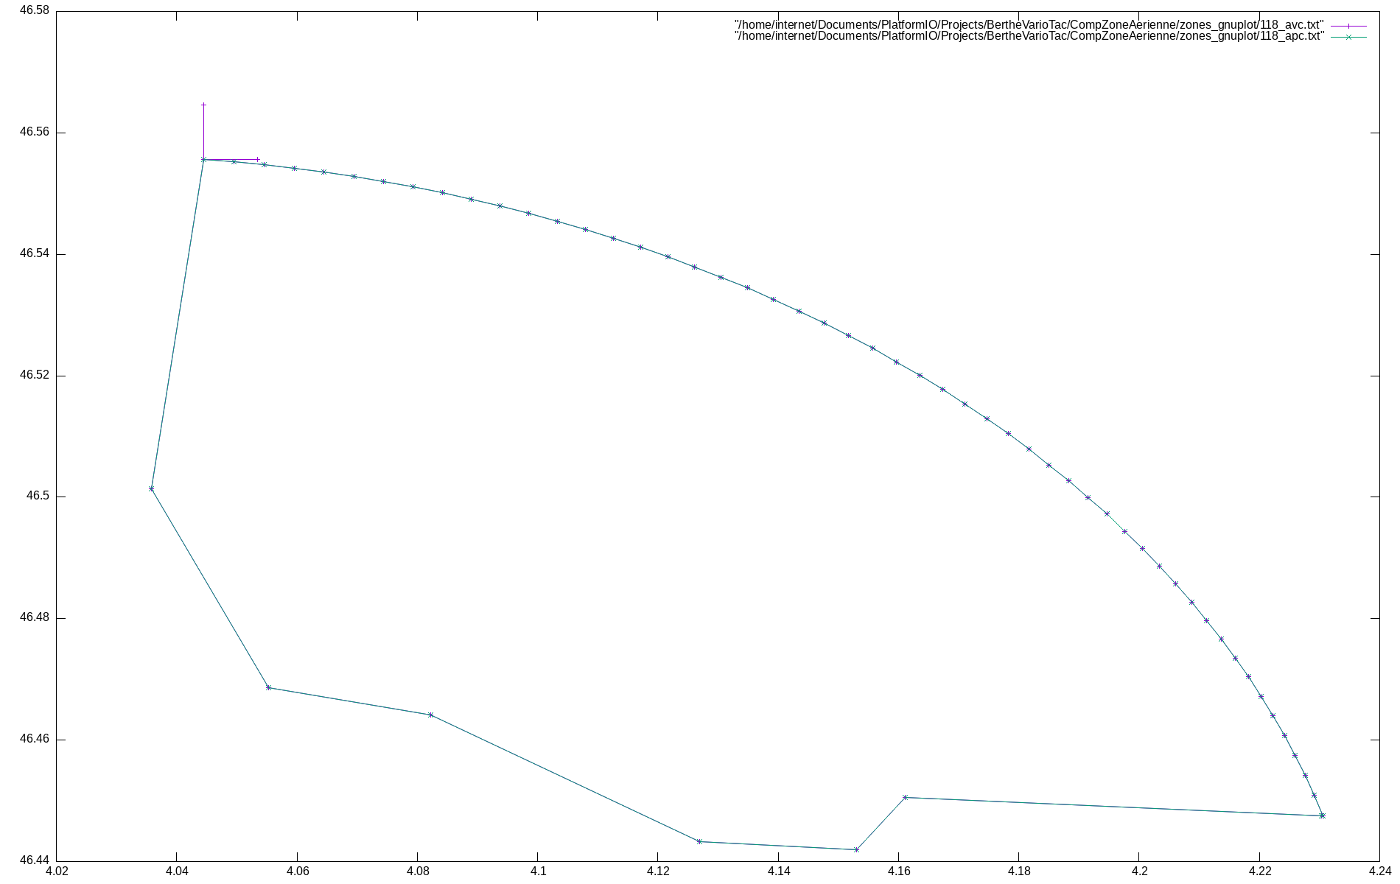
CompZoneAerienne/zones_gnuplot/118.png
