gitberthe/BertheVario213/CompZoneAerienne/zones_gnuplot/119.png

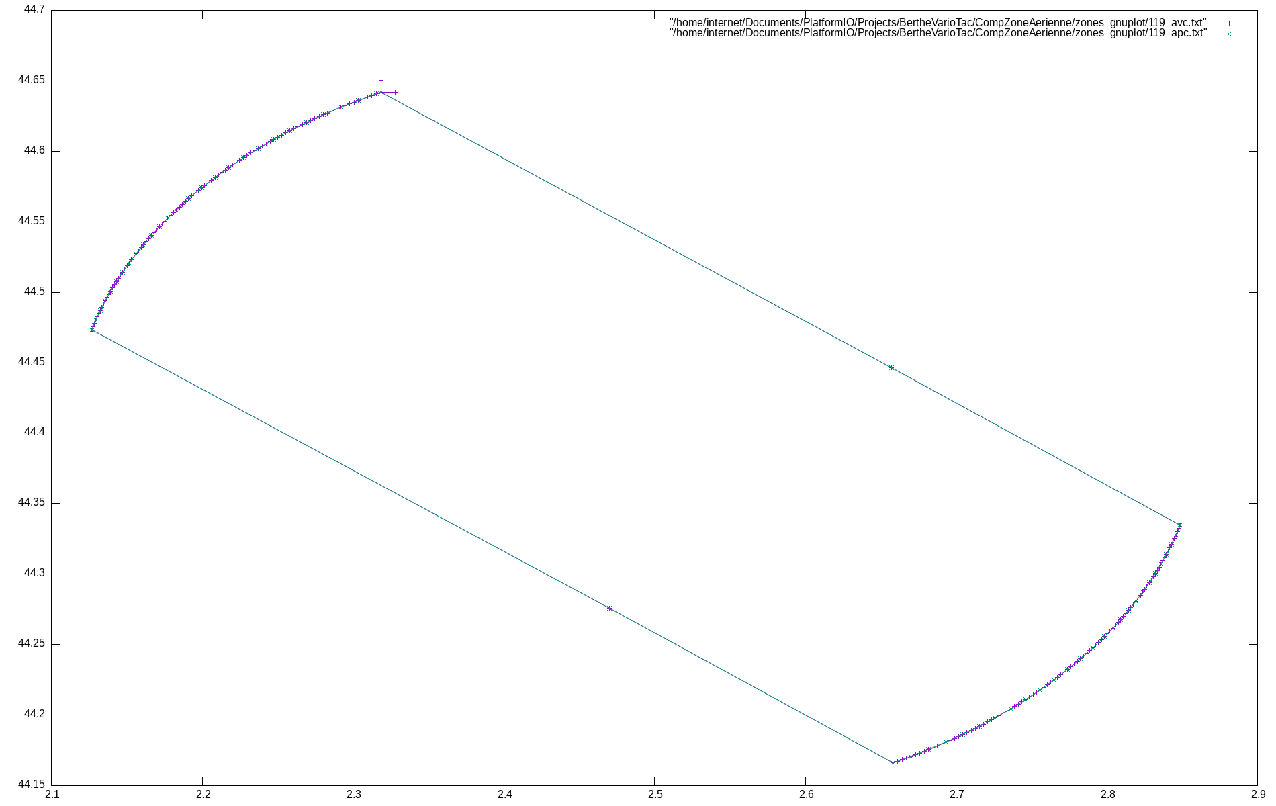
CompZoneAerienne/zones_gnuplot/119.png
