gitberthe/BertheVario213/CompZoneAerienne/zones_gnuplot/120.png

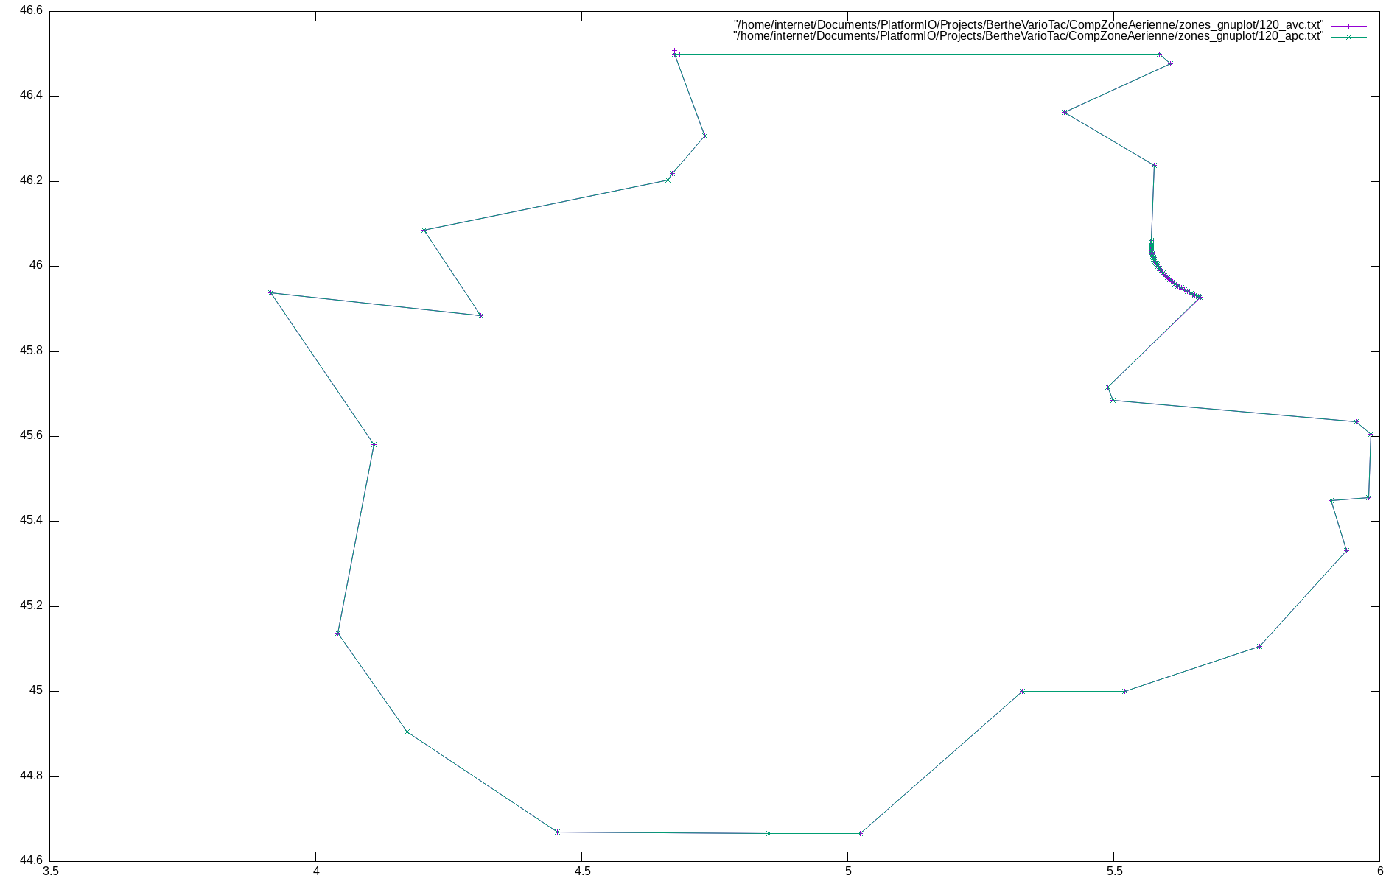
CompZoneAerienne/zones_gnuplot/120.png
