gitberthe/BertheVario213/CompZoneAerienne/zones_gnuplot/121.png

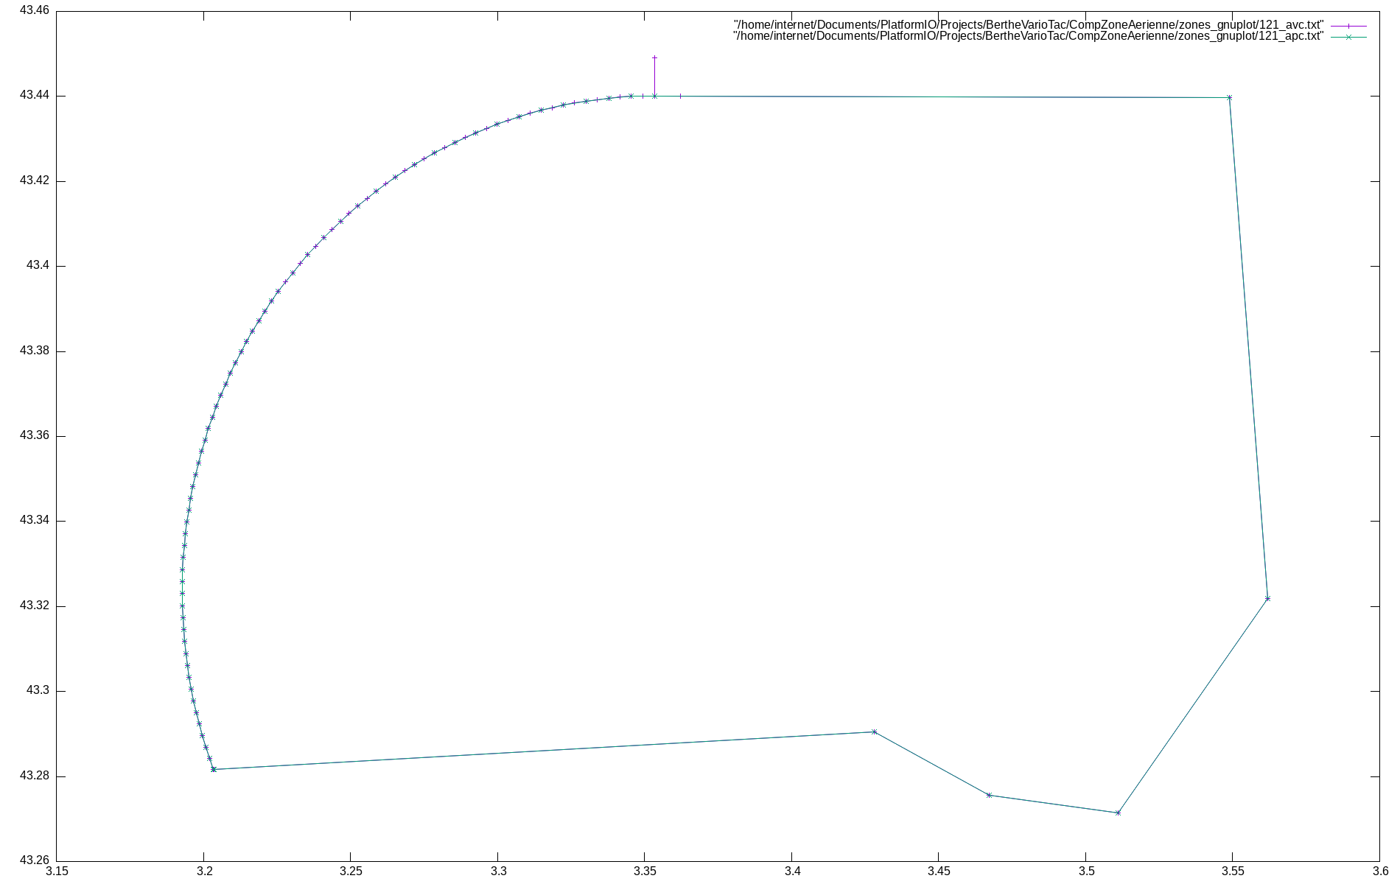
CompZoneAerienne/zones_gnuplot/121.png
