gitberthe/BertheVario213/CompZoneAerienne/zones_gnuplot/122.png

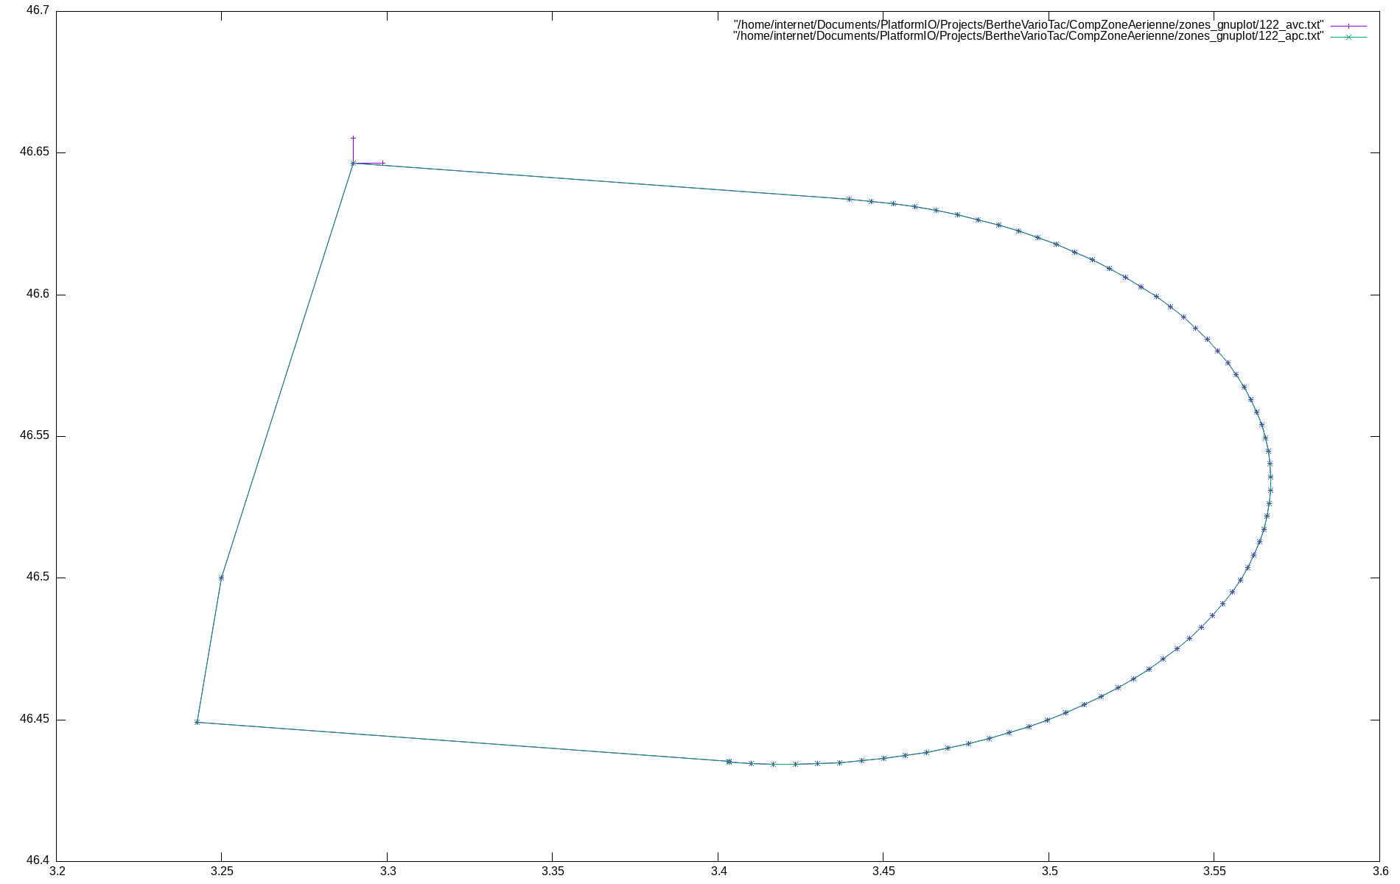
CompZoneAerienne/zones_gnuplot/122.png
