gitberthe/BertheVario213/CompZoneAerienne/zones_gnuplot/123.png

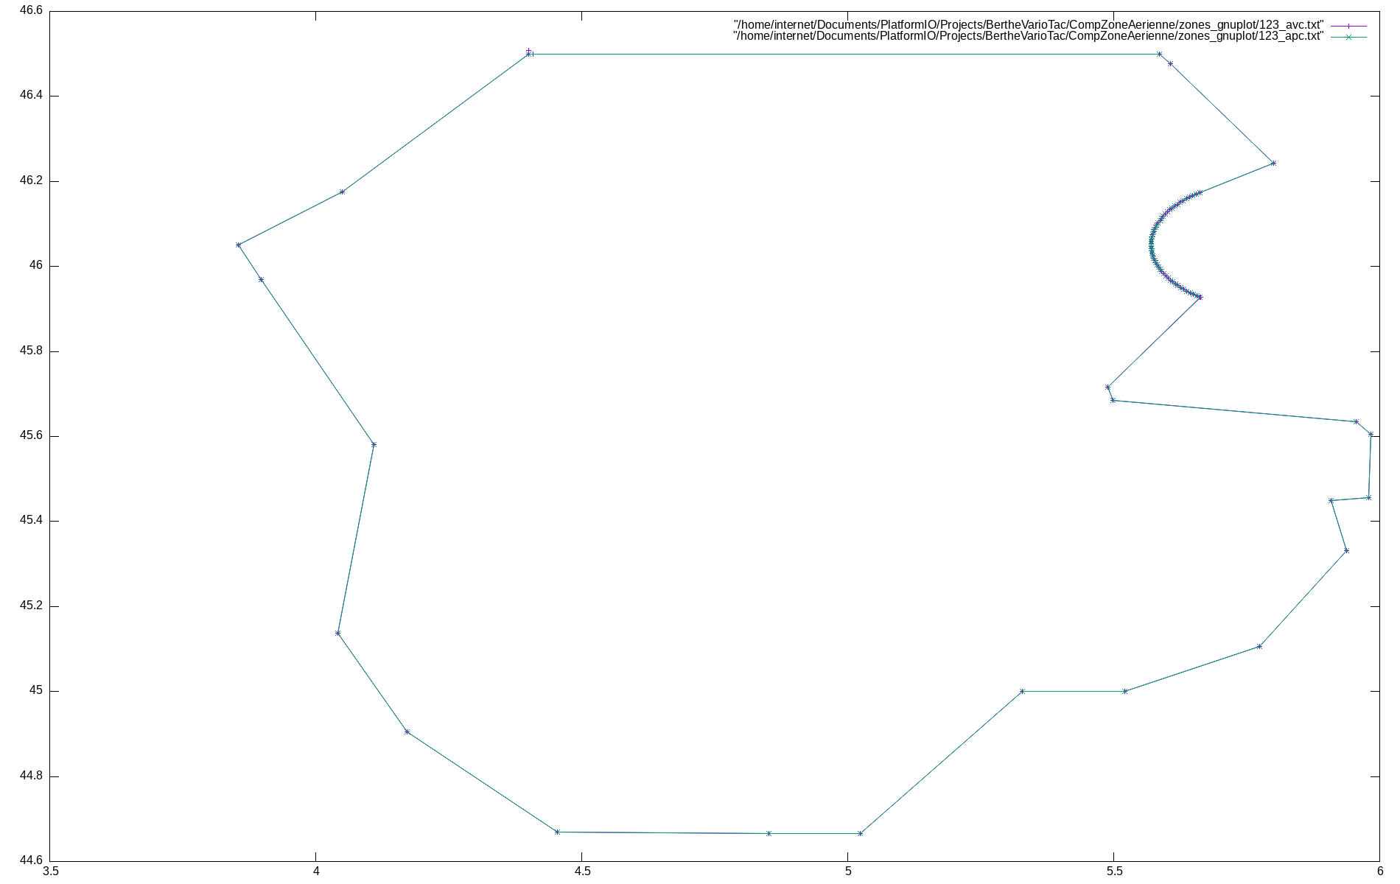
CompZoneAerienne/zones_gnuplot/123.png
