gitberthe/BertheVario213/CompZoneAerienne/zones_gnuplot/124.png

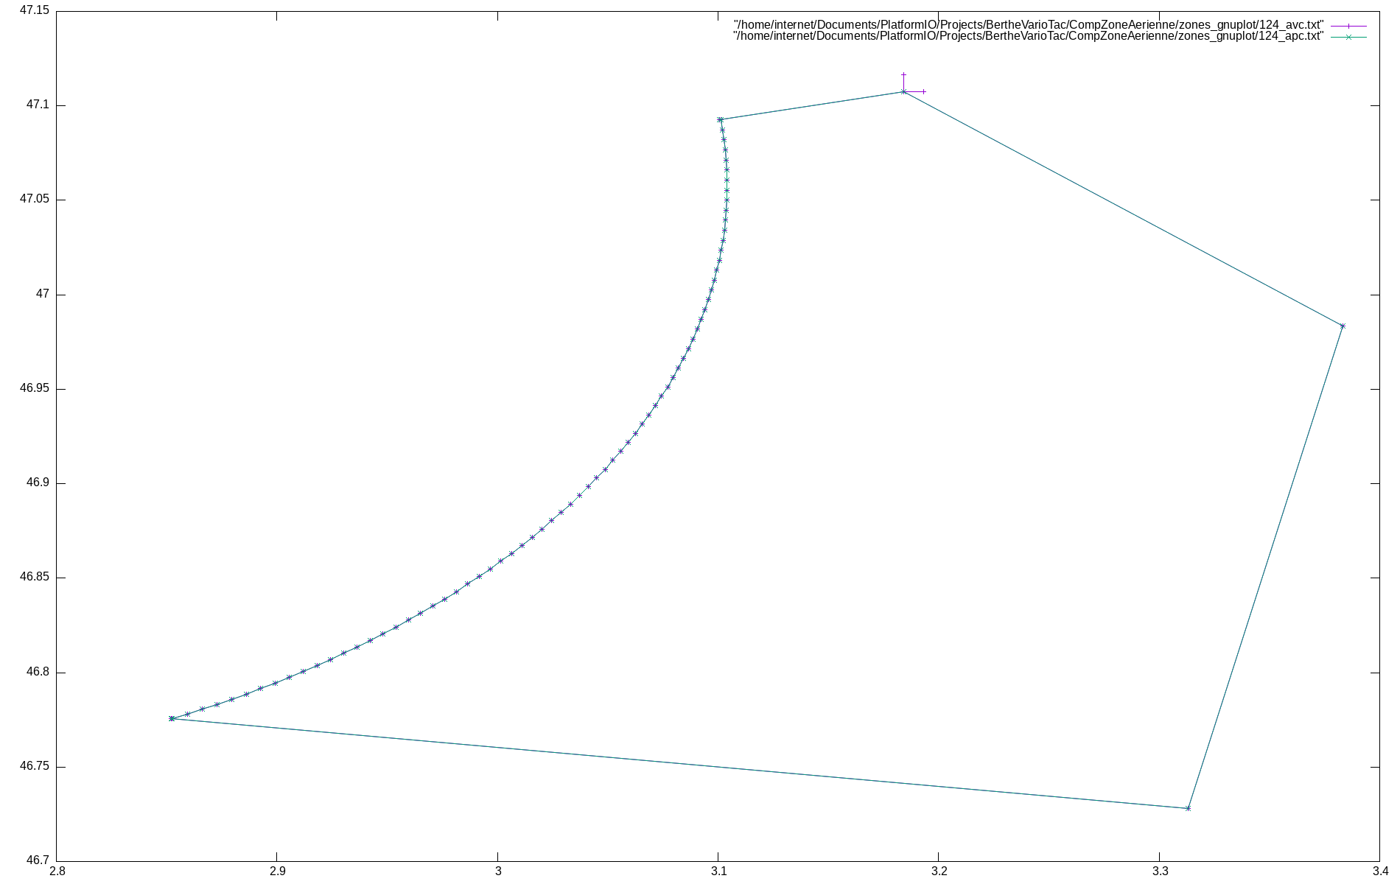
CompZoneAerienne/zones_gnuplot/124.png
