gitberthe/BertheVario213/CompZoneAerienne/zones_gnuplot/125.png

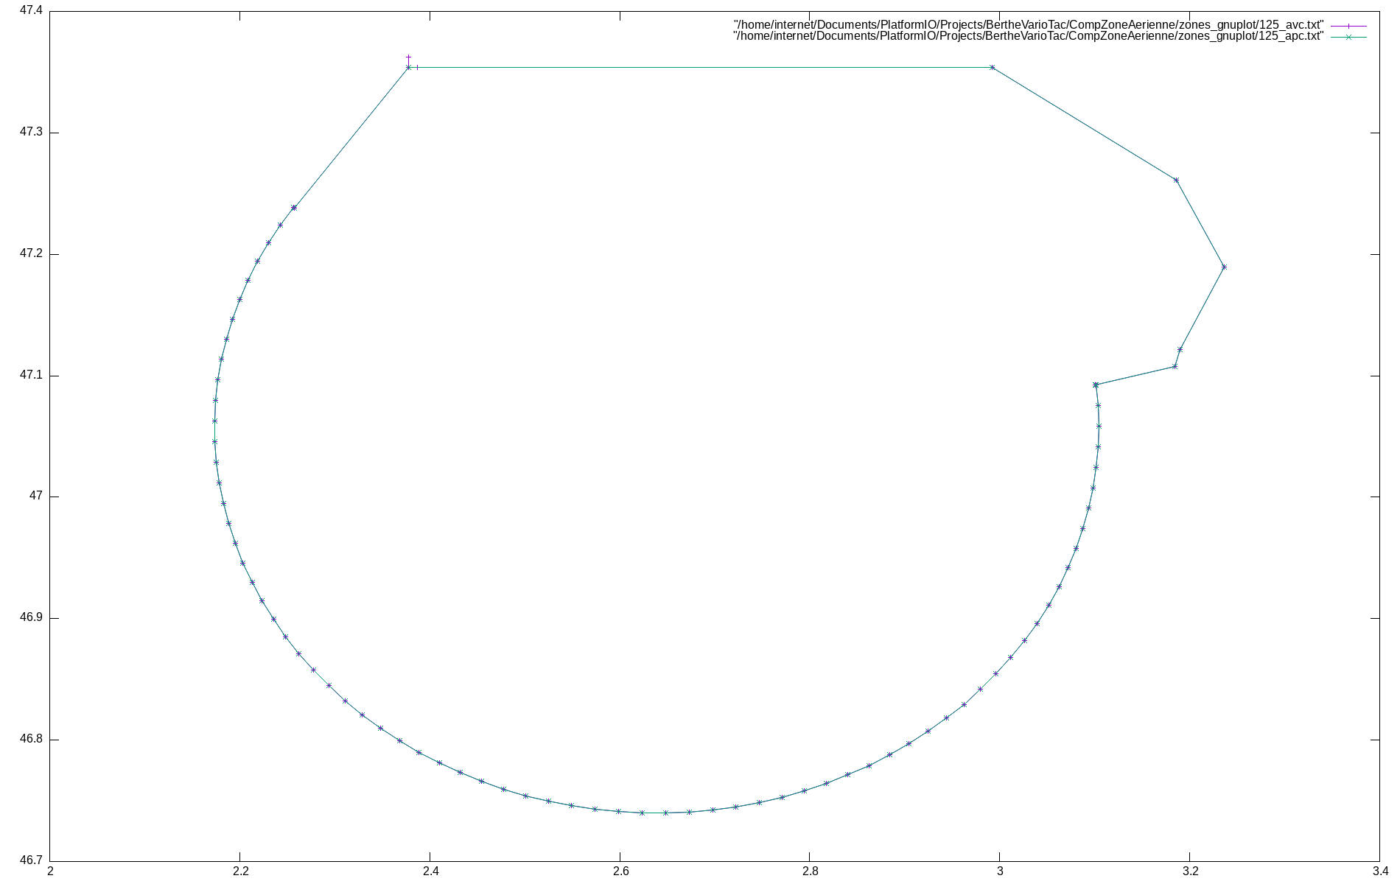
CompZoneAerienne/zones_gnuplot/125.png
