gitberthe/BertheVario213/CompZoneAerienne/zones_gnuplot/126.png

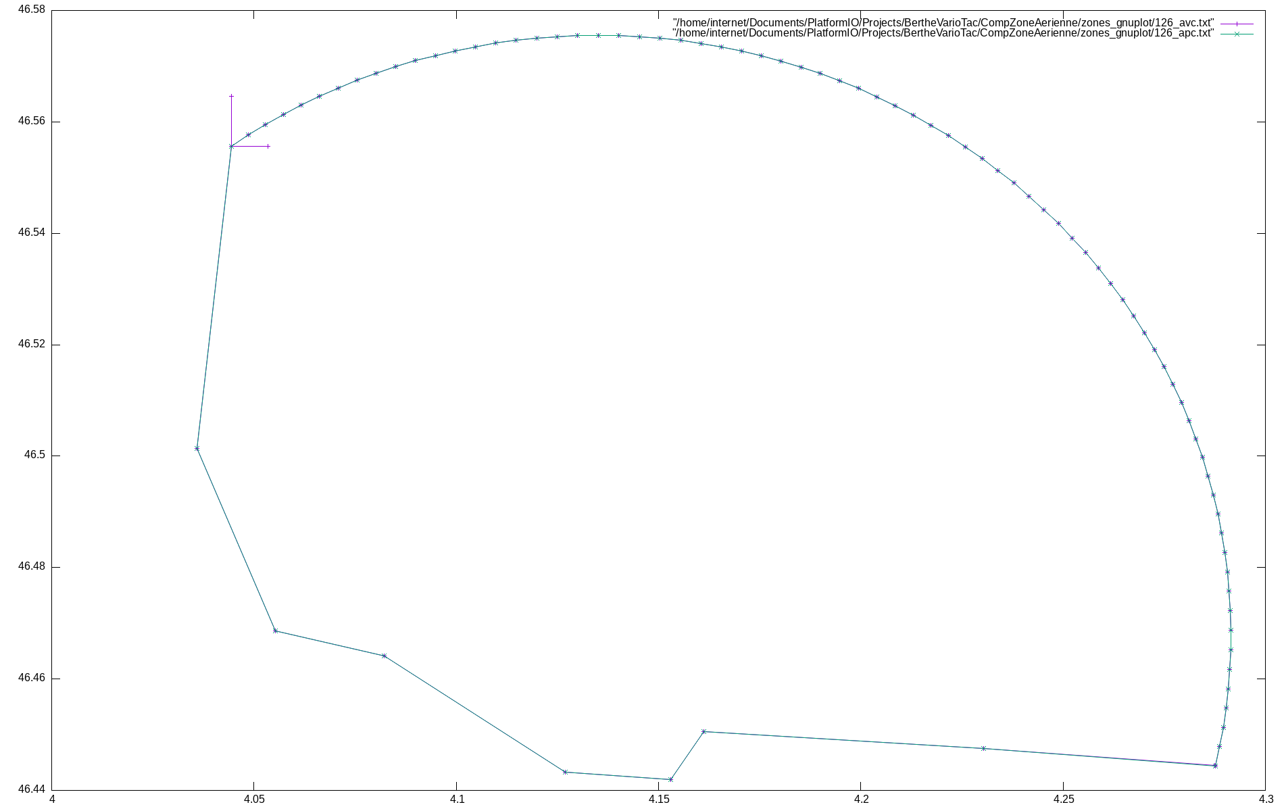
CompZoneAerienne/zones_gnuplot/126.png
