gitberthe/BertheVario213/CompZoneAerienne/zones_gnuplot/127.png

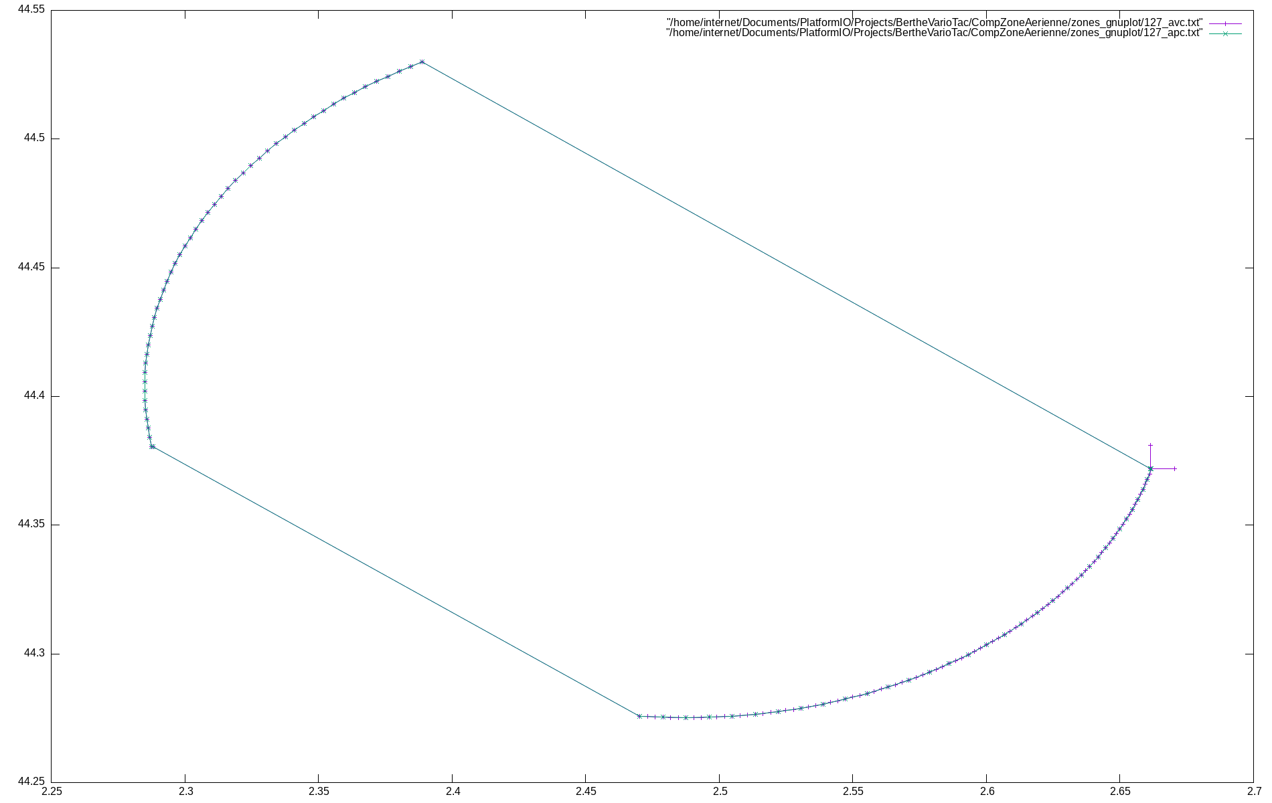
CompZoneAerienne/zones_gnuplot/127.png
