gitberthe/BertheVario213/CompZoneAerienne/zones_gnuplot/128.png

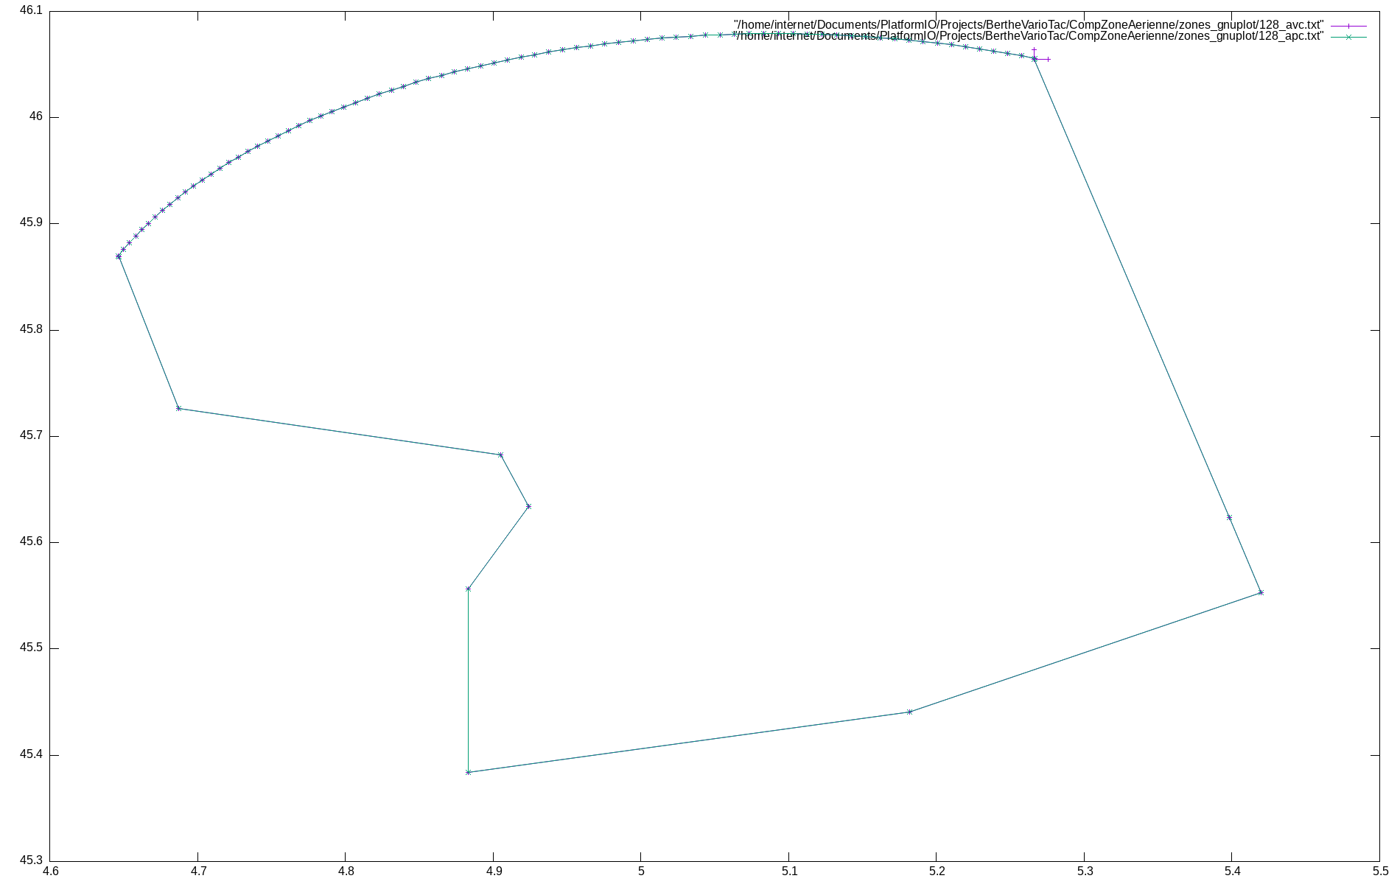
CompZoneAerienne/zones_gnuplot/128.png
