gitberthe/BertheVario213/CompZoneAerienne/zones_gnuplot/129.png

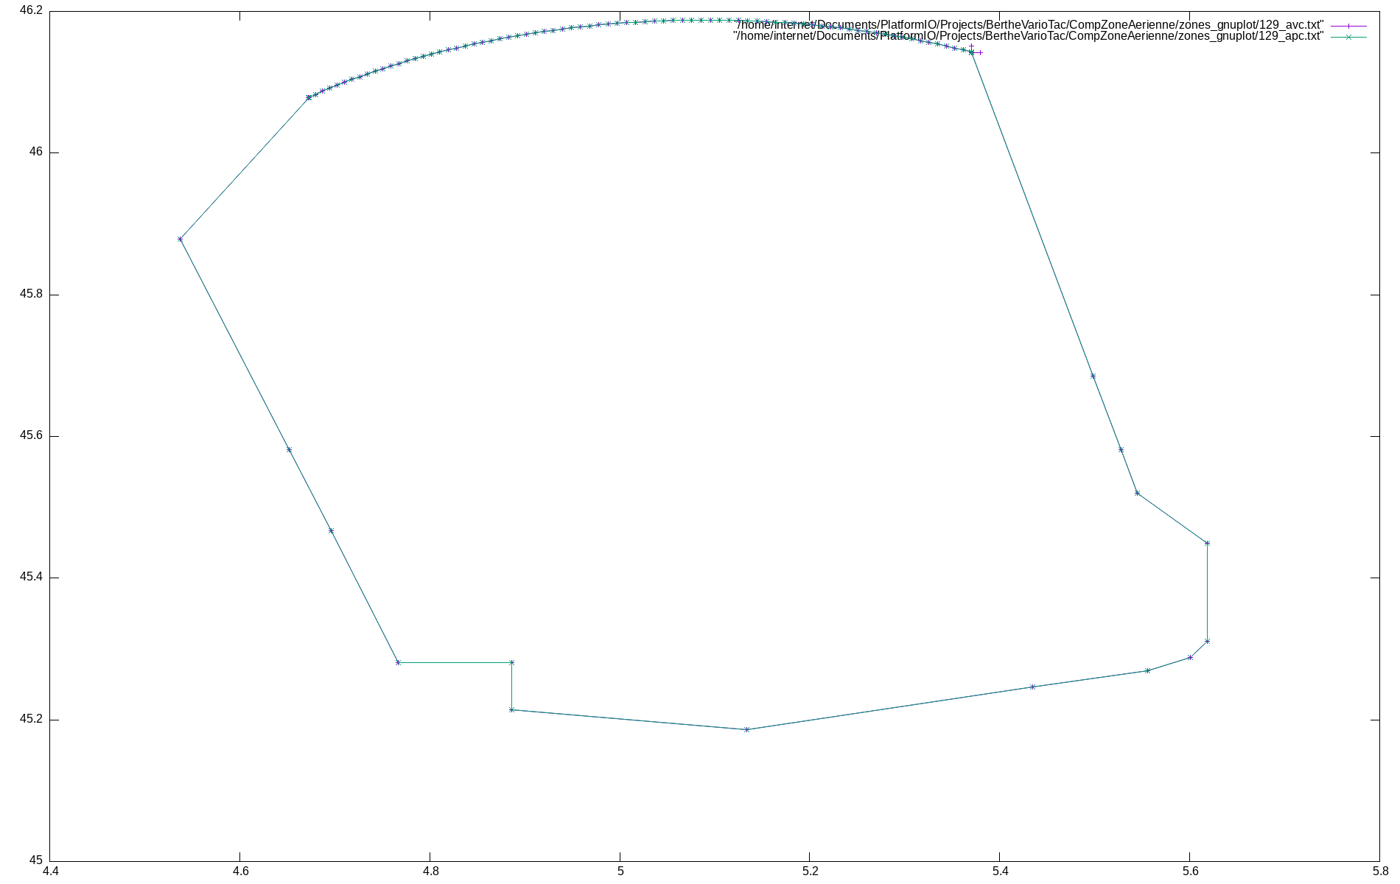
CompZoneAerienne/zones_gnuplot/129.png
