gitberthe/BertheVario213/CompZoneAerienne/zones_gnuplot/130.png

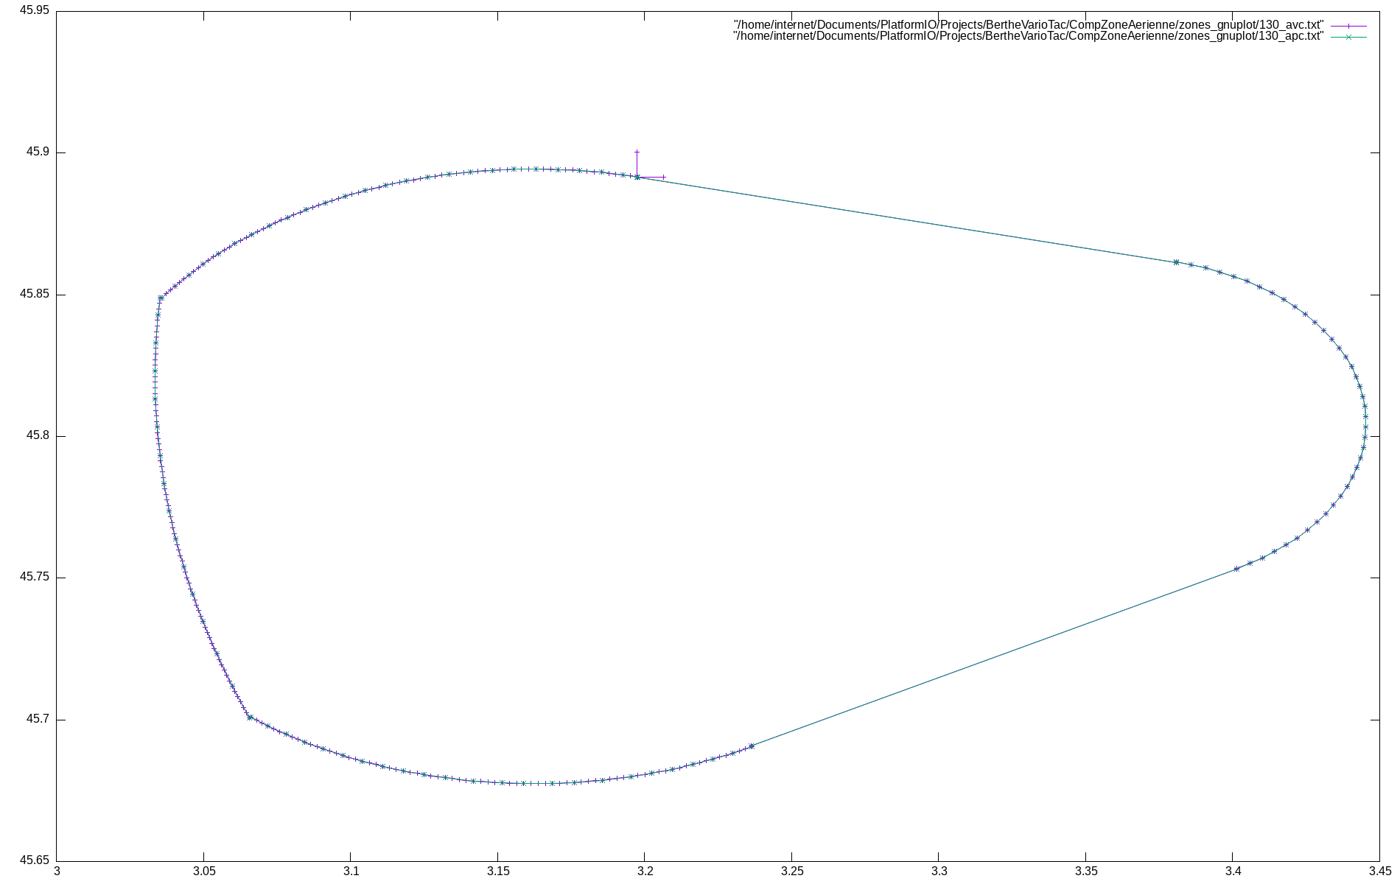
CompZoneAerienne/zones_gnuplot/130.png
