gitberthe/BertheVario213/CompZoneAerienne/zones_gnuplot/132.png

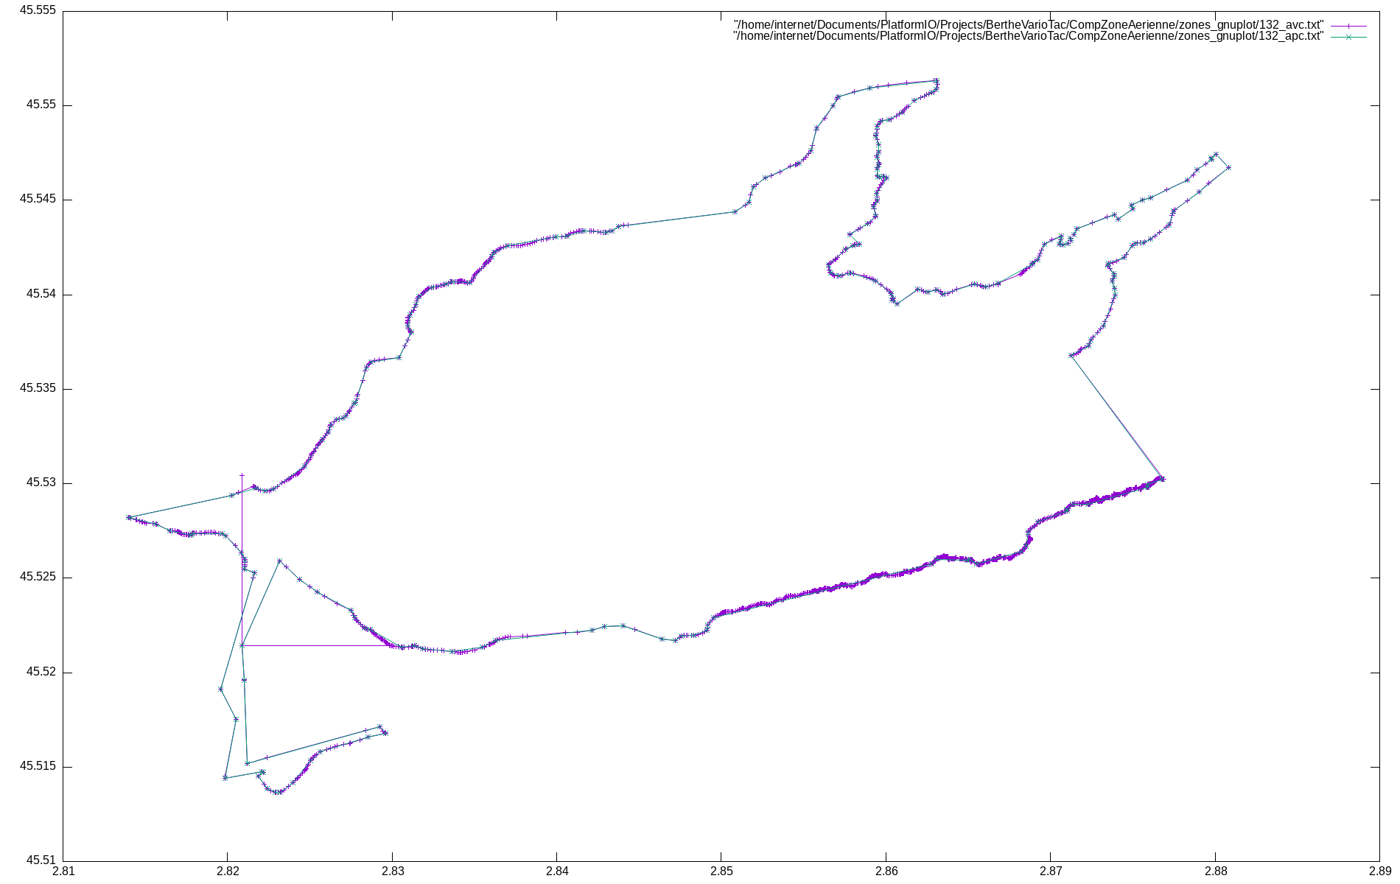
CompZoneAerienne/zones_gnuplot/132.png
