gitberthe/BertheVario213/CompZoneAerienne/zones_gnuplot/133.png

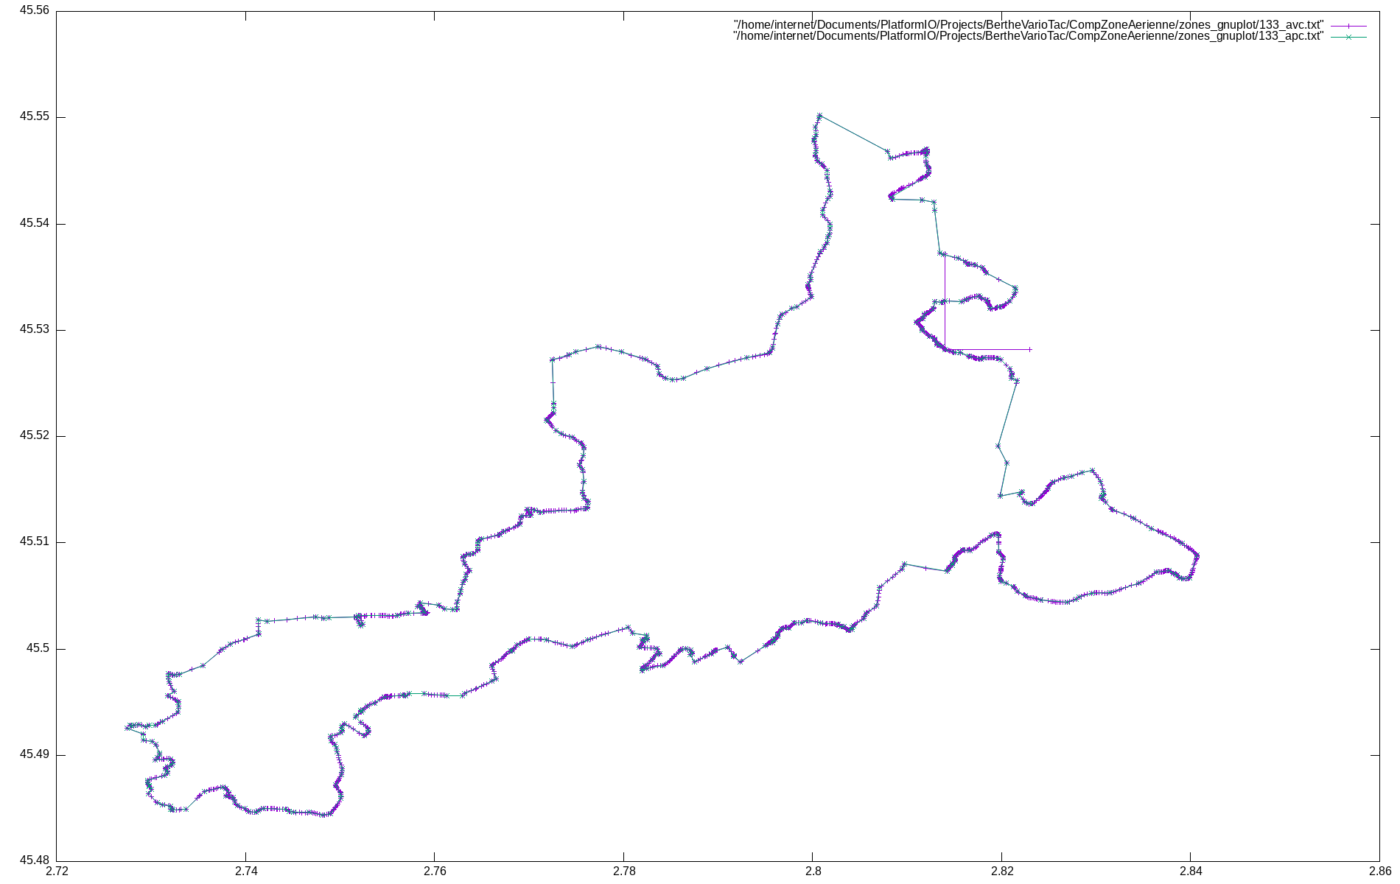
CompZoneAerienne/zones_gnuplot/133.png
