gitberthe/BertheVario213/CompZoneAerienne/zones_gnuplot/134.png

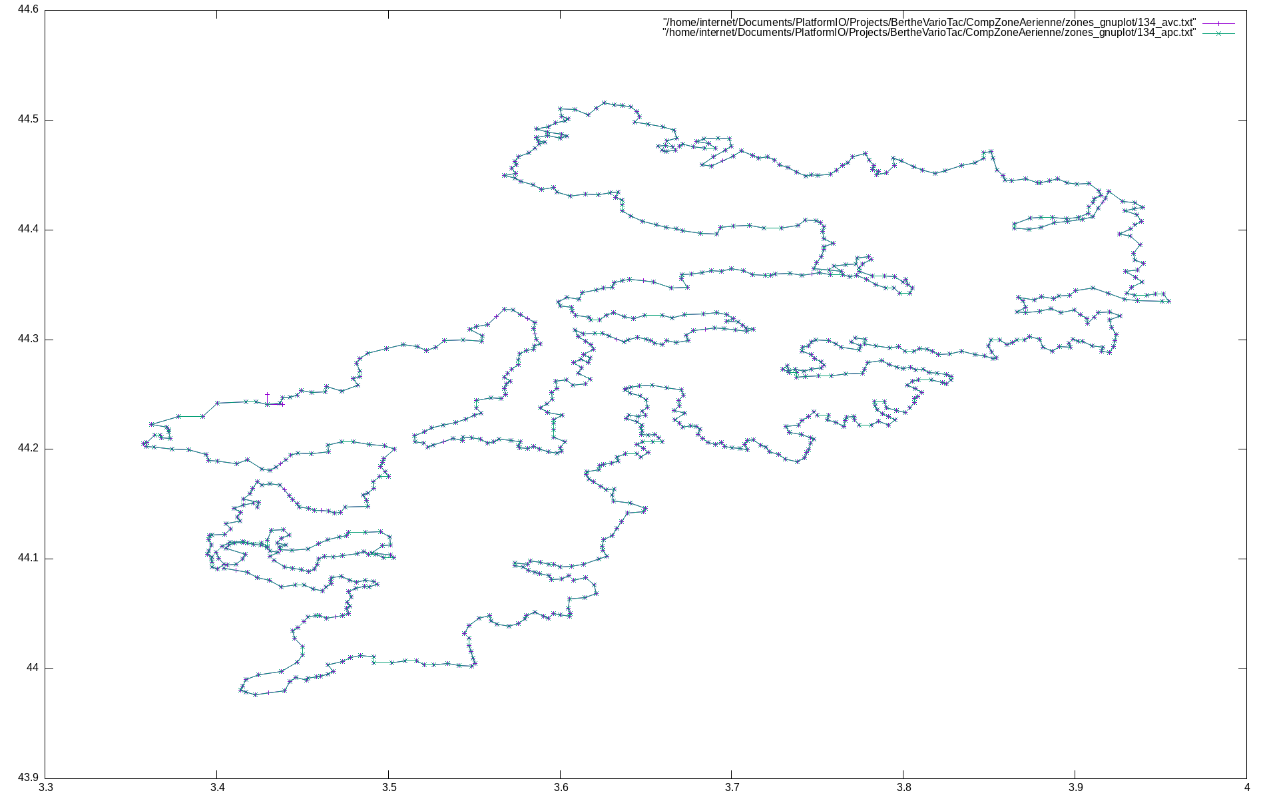
CompZoneAerienne/zones_gnuplot/134.png
