gitberthe/BertheVario213/Documentation/00-photo/T5-V2_18_4g.jpg

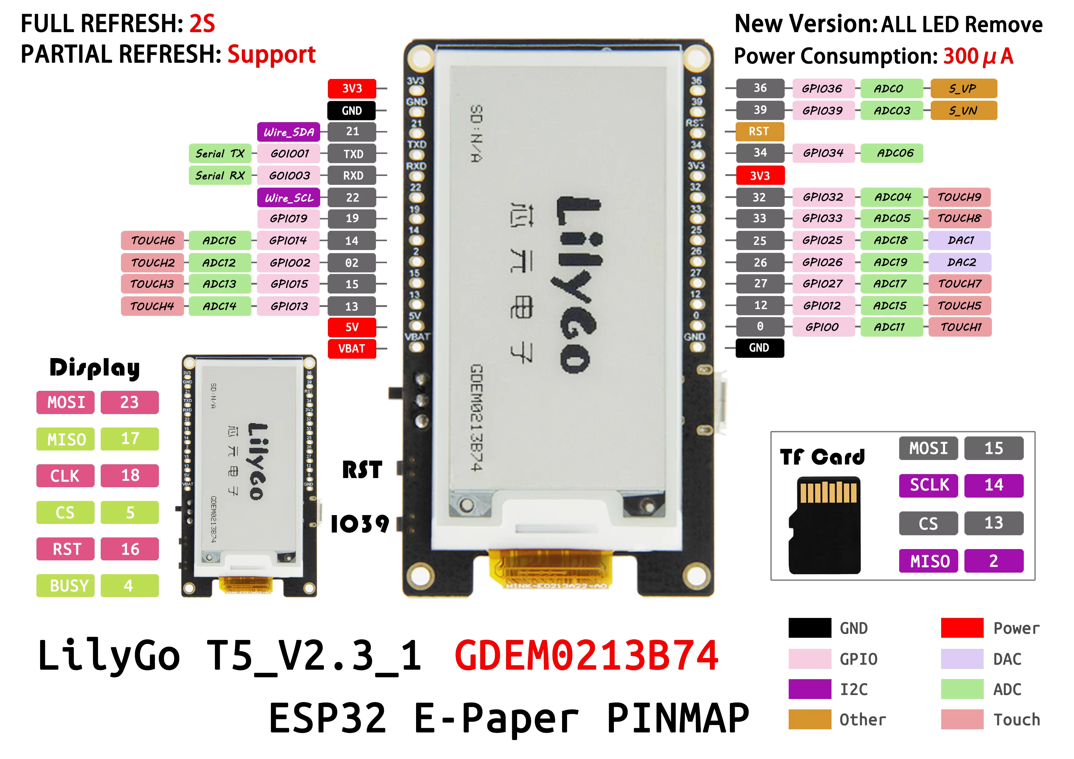
Documentation/00-photo/T5-V2_18_4g.jpg
