gitberthe/BertheVario213/BertheVario213PlatformIO/src/Screen/GxEPD2_display_selection.h

// Display Library example for SPI e-paper panels from Dalian Good Display and boards from Waveshare.
// Requires HW SPI and Adafruit_GFX. Caution: the e-paper panels require 3.3V supply AND data lines!
//
// Display Library based on Demo Example from Good Display: http://www.e-paper-display.com/download_list/downloadcategoryid=34&isMode=false.html
//
// Author: Jean-Marc Zingg
//
// Version: see library.properties
//
// Library: https://github.com/ZinggJM/GxEPD2

// Supporting Arduino Forum Topics:
// Waveshare e-paper displays with SPI: http://forum.arduino.cc/index.php?topic=487007.0
// Good Display ePaper for Arduino: https://forum.arduino.cc/index.php?topic=436411.0

#if defined (ESP8266)
// select one and adapt to your mapping, can use full buffer size (full HEIGHT)
//GxEPD2_BW<GxEPD2_102, GxEPD2_102::HEIGHT> display(GxEPD2_102(/*CS=D8*/ SS, /*DC=D3*/ 0, /*RST=D4*/ 2, /*BUSY=D2*/ 4)); // GDEW0102T4 80x128, UC8175
//GxEPD2_BW<GxEPD2_150_BN, GxEPD2_150_BN::HEIGHT> display(GxEPD2_150_BN(/*CS=D8*/ SS, /*DC=D3*/ 0, /*RST=D4*/ 2, /*BUSY=D2*/ 4)); // DEPG0150BN 200x200, SSD1681, TTGO T5 V2.4.1
//GxEPD2_BW<GxEPD2_154, GxEPD2_154::HEIGHT> display(GxEPD2_154(/*CS=D8*/ SS, /*DC=D3*/ 0, /*RST=D4*/ 2, /*BUSY=D2*/ 4)); // GDEP015OC1 200x200, IL3829, no longer available
//GxEPD2_BW<GxEPD2_154_D67, GxEPD2_154_D67::HEIGHT> display(GxEPD2_154_D67(/*CS=D8*/ SS, /*DC=D3*/ 0, /*RST=D4*/ 2, /*BUSY=D2*/ 4)); // GDEH0154D67 200x200, SSD1681
//GxEPD2_BW<GxEPD2_154_T8, GxEPD2_154_T8::HEIGHT> display(GxEPD2_154_T8(/*CS=D8*/ SS, /*DC=D3*/ 0, /*RST=D4*/ 2, /*BUSY=D2*/ 4)); // GDEW0154T8  152x152, UC8151 (IL0373)
//GxEPD2_BW<GxEPD2_154_M09, GxEPD2_154_M09::HEIGHT> display(GxEPD2_154_M09(/*CS=D8*/ SS, /*DC=D3*/ 0, /*RST=D4*/ 2, /*BUSY=D2*/ 4)); // GDEW0154M09 200x200, JD79653A
//GxEPD2_BW<GxEPD2_154_M10, GxEPD2_154_M10::HEIGHT> display(GxEPD2_154_M10(/*CS=D8*/ SS, /*DC=D3*/ 0, /*RST=D4*/ 2, /*BUSY=D2*/ 4)); // GDEW0154M10 152x152, UC8151D
//GxEPD2_BW<GxEPD2_154_GDEY0154D67, GxEPD2_154_GDEY0154D67::HEIGHT> display(GxEPD2_154_GDEY0154D67(/*CS=D8*/ SS, /*DC=D3*/ 0, /*RST=D4*/ 2, /*BUSY=D2*/ 4)); // GDEY0154D67 200x200, SSD1681, (FPC-B001 20.05.21)
//GxEPD2_BW<GxEPD2_213, GxEPD2_213::HEIGHT> display(GxEPD2_213(/*CS=D8*/ SS, /*DC=D3*/ 0, /*RST=D4*/ 2, /*BUSY=D2*/ 4)); // GDE0213B1 122x250, IL3895, phased out
//GxEPD2_BW<GxEPD2_213_B72, GxEPD2_213_B72::HEIGHT> display(GxEPD2_213_B72(/*CS=D8*/ SS, /*DC=D3*/ 0, /*RST=D4*/ 2, /*BUSY=D2*/ 4)); // GDEH0213B72 122x250, SSD1675A (IL3897)
//GxEPD2_BW<GxEPD2_213_B73, GxEPD2_213_B73::HEIGHT> display(GxEPD2_213_B73(/*CS=D8*/ SS, /*DC=D3*/ 0, /*RST=D4*/ 2, /*BUSY=D2*/ 4)); // GDEH0213B73 122x250, SSD1675B
//GxEPD2_BW<GxEPD2_213_B74, GxEPD2_213_B74::HEIGHT> display(GxEPD2_213_B74(/*CS=D8*/ SS, /*DC=D3*/ 0, /*RST=D4*/ 2, /*BUSY=D2*/ 4)); // GDEM0213B74 122x250, SSD1680
//GxEPD2_BW<GxEPD2_213_flex, GxEPD2_213_flex::HEIGHT> display(GxEPD2_213_flex(/*CS=D8*/ SS, /*DC=D3*/ 0, /*RST=D4*/ 2, /*BUSY=D2*/ 4)); // GDEW0213I5F 104x212, UC8151 (IL0373)
//GxEPD2_BW<GxEPD2_213_M21, GxEPD2_213_M21::HEIGHT> display(GxEPD2_213_M21(/*CS=D8*/ SS, /*DC=D3*/ 0, /*RST=D4*/ 2, /*BUSY=D2*/ 4)); // GDEW0213M21 104x212, UC8151 (IL0373)
//GxEPD2_BW<GxEPD2_213_T5D, GxEPD2_213_T5D::HEIGHT> display(GxEPD2_213_T5D(/*CS=D8*/ SS, /*DC=D3*/ 0, /*RST=D4*/ 2, /*BUSY=D2*/ 4)); // GDEW0213T5D 104x212, UC8151D
//GxEPD2_BW<GxEPD2_213_BN, GxEPD2_213_BN::HEIGHT> display(GxEPD2_213_BN(/*CS=D8*/ SS, /*DC=D3*/ 0, /*RST=D4*/ 2, /*BUSY=D2*/ 4)); // DEPG0213BN 122x250, SSD1680, TTGO T5 V2.4.1, V2.3.1
//GxEPD2_BW<GxEPD2_213_GDEY0213B74, GxEPD2_213_GDEY0213B74::HEIGHT> display(GxEPD2_213_GDEY0213B74(/*CS=D8*/ SS, /*DC=D3*/ 0, /*RST=D4*/ 2, /*BUSY=D2*/ 4)); // GDEY0213B74 122x250, SSD1680, (FPC-A002 20.04.08)
//GxEPD2_BW<GxEPD2_260, GxEPD2_260::HEIGHT> display(GxEPD2_260(/*CS=D8*/ SS, /*DC=D3*/ 0, /*RST=D4*/ 2, /*BUSY=D2*/ 4)); // GDEW026T0 152x296, UC8151 (IL0373)
//GxEPD2_BW<GxEPD2_260_M01, GxEPD2_260_M01::HEIGHT> display(GxEPD2_260_M01(/*CS=D8*/ SS, /*DC=D3*/ 0, /*RST=D4*/ 2, /*BUSY=D2*/ 4)); // GDEW026M01 152x296, UC8151 (IL0373)
//GxEPD2_BW<GxEPD2_266_BN, GxEPD2_266_BN::HEIGHT> display(GxEPD2_266_BN(/*CS=D8*/ SS, /*DC=D3*/ 0, /*RST=D4*/ 2, /*BUSY=D2*/ 4)); // DEPG0266BN 152x296, SSD1680, TTGO T5 V2.66 / T92_V1.0
//GxEPD2_BW<GxEPD2_270, GxEPD2_270::HEIGHT> display(GxEPD2_270(/*CS=D8*/ SS, /*DC=D3*/ 0, /*RST=D4*/ 2, /*BUSY=D2*/ 4)); // GDEW027W3 176x264, EK79652 (IL91874)
//GxEPD2_BW<GxEPD2_270_GDEY027T91, GxEPD2_270_GDEY027T91::HEIGHT> display(GxEPD2_270_GDEY027T91(/*CS=D8*/ SS, /*DC=D3*/ 0, /*RST=D4*/ 2, /*BUSY=D2*/ 4)); // GDEY027T91 176x264, SSD1680
//GxEPD2_BW<GxEPD2_290, GxEPD2_290::HEIGHT> display(GxEPD2_290(/*CS=D8*/ SS, /*DC=D3*/ 0, /*RST=D4*/ 2, /*BUSY=D2*/ 4)); // GDEH029A1 128x296, SSD1608 (IL3820)
//GxEPD2_BW<GxEPD2_290_T5, GxEPD2_290_T5::HEIGHT> display(GxEPD2_290_T5(/*CS=D8*/ SS, /*DC=D3*/ 0, /*RST=D4*/ 2, /*BUSY=D2*/ 4)); // GDEW029T5 128x296, UC8151 (IL0373)
//GxEPD2_BW<GxEPD2_290_T5D, GxEPD2_290_T5D::HEIGHT> display(GxEPD2_290_T5D(/*CS=D8*/ SS, /*DC=D3*/ 0, /*RST=D4*/ 2, /*BUSY=D2*/ 4)); // GDEW029T5D 128x296, UC8151D
//GxEPD2_BW<GxEPD2_290_I6FD, GxEPD2_290_I6FD::HEIGHT> display(GxEPD2_290_I6FD(/*CS=D8*/ SS, /*DC=D3*/ 0, /*RST=D4*/ 2, /*BUSY=D2*/ 4)); // GDEW029I6FD 128x296, UC8151D
//GxEPD2_BW<GxEPD2_290_T94, GxEPD2_290_T94::HEIGHT> display(GxEPD2_290_T94(/*CS=D8*/ SS, /*DC=D3*/ 0, /*RST=D4*/ 2, /*BUSY=D2*/ 4)); // GDEM029T94 128x296, SSD1680
//GxEPD2_BW<GxEPD2_290_T94_V2, GxEPD2_290_T94_V2::HEIGHT> display(GxEPD2_290_T94_V2(/*CS=D8*/ SS, /*DC=D3*/ 0, /*RST=D4*/ 2, /*BUSY=D2*/ 4)); // GDEM029T94 128x296, SSD1680, Waveshare 2.9" V2 variant
//GxEPD2_BW<GxEPD2_290_BS, GxEPD2_290_BS::HEIGHT> display(GxEPD2_290_BS(/*CS=D8*/ SS, /*DC=D3*/ 0, /*RST=D4*/ 2, /*BUSY=D2*/ 4)); // DEPG0290BS 128x296, SSD1680
//GxEPD2_BW<GxEPD2_290_M06, GxEPD2_290_M06::HEIGHT> display(GxEPD2_290_M06(/*CS=D8*/ SS, /*DC=D3*/ 0, /*RST=D4*/ 2, /*BUSY=D2*/ 4)); // GDEW029M06  128x296, UC8151D
//GxEPD2_BW<GxEPD2_290_GDEY029T94, GxEPD2_290_GDEY029T94::HEIGHT> display(GxEPD2_290_GDEY029T94(/*CS=D8*/ SS, /*DC=D3*/ 0, /*RST=D4*/ 2, /*BUSY=D2*/ 4)); // GDEY029T94  128x296, SSD1680, (FPC-A005 20.06.15)
//GxEPD2_BW<GxEPD2_371, GxEPD2_371::HEIGHT> display(GxEPD2_371(/*CS=D8*/ SS, /*DC=D3*/ 0, /*RST=D4*/ 2, /*BUSY=D2*/ 4)); // GDEW0371W7 240x416, UC8171 (IL0324)
//GxEPD2_BW<GxEPD2_370_TC1, GxEPD2_370_TC1::HEIGHT> display(GxEPD2_370_TC1(/*CS=D8*/ SS, /*DC=D3*/ 0, /*RST=D4*/ 2, /*BUSY=D2*/ 4)); // ED037TC1 280x480, SSD1677, Waveshare 3.7"
//GxEPD2_BW<GxEPD2_420, GxEPD2_420::HEIGHT> display(GxEPD2_420(/*CS=D8*/ SS, /*DC=D3*/ 0, /*RST=D4*/ 2, /*BUSY=D2*/ 4)); // GDEW042T2 400x300, UC8176 (IL0398)
//GxEPD2_BW<GxEPD2_420_M01, GxEPD2_420_M01::HEIGHT> display(GxEPD2_420_M01(/*CS=D8*/ SS, /*DC=D3*/ 0, /*RST=D4*/ 2, /*BUSY=D2*/ 4)); // GDEW042M01 400x300, UC8176 (IL0398)
//GxEPD2_BW<GxEPD2_420_GDEY042T81, GxEPD2_420_GDEY042T81::HEIGHT> display(GxEPD2_420_GDEY042T81(/*CS=D8*/ SS, /*DC=D3*/ 0, /*RST=D4*/ 2, /*BUSY=D2*/ 4)); // GDEY042T81, 400x300, SSD1683 (no inking)
//GxEPD2_BW<GxEPD2_426_GDEQ0426T82, GxEPD2_426_GDEQ0426T82::HEIGHT> display(GxEPD2_426_GDEQ0426T82(/*CS=D8*/ SS, /*DC=D3*/ 0, /*RST=D4*/ 2, /*BUSY=D2*/ 4)); // GDEQ0426T82 480x800, SSD1677 (P426010-MF1-A)
// can use only half buffer size
//GxEPD2_BW < GxEPD2_583, GxEPD2_583::HEIGHT / 2 > display(GxEPD2_583(/*CS=D8*/ SS, /*DC=D3*/ 0, /*RST=D4*/ 2, /*BUSY=D2*/ 4)); // GDEW0583T7 600x448, UC8159c (IL0371)
//GxEPD2_BW < GxEPD2_583_T8, GxEPD2_583_T8::HEIGHT / 2 > display(GxEPD2_583_T8(/*CS=D8*/ SS, /*DC=D3*/ 0, /*RST=D4*/ 2, /*BUSY=D2*/ 4)); // GDEW0583T8 648x480, EK79655 (GD7965)
//GxEPD2_BW < GxEPD2_583_GDEQ0583T31, GxEPD2_583_GDEQ0583T31::HEIGHT / 2 > display(GxEPD2_583_GDEQ0583T31(/*CS=D8*/ SS, /*DC=D3*/ 0, /*RST=D4*/ 2, /*BUSY=D2*/ 4)); // GDEQ0583T31 648x480, UC8179, (P583010-MF1-B)
//GxEPD2_BW < GxEPD2_750, GxEPD2_750::HEIGHT / 2 > display(GxEPD2_750(/*CS=D8*/ SS, /*DC=D3*/ 0, /*RST=D4*/ 2, /*BUSY=D2*/ 4)); // GDEW075T8 640x384, UC8159c (IL0371)
//GxEPD2_BW < GxEPD2_750_T7, GxEPD2_750_T7::HEIGHT / 2 > display(GxEPD2_750_T7(/*CS=D8*/ SS, /*DC=D3*/ 0, /*RST=D4*/ 2, /*BUSY=D2*/ 4)); // GDEW075T7 800x480, EK79655 (GD7965)
//GxEPD2_BW < GxEPD2_750_YT7, GxEPD2_750_YT7::HEIGHT / 2 > display(GxEPD2_750_YT7(/*CS=D8*/ SS, /*DC=D3*/ 0, /*RST=D4*/ 2, /*BUSY=D2*/ 4)); // GDEY075T7 800x480, UC8179 (GD7965)
//GxEPD2_BW < GxEPD2_1160_T91, GxEPD2_1160_T91::HEIGHT / 2 > display(GxEPD2_1160_T91(/*CS=D8*/ SS, /*DC=D3*/ 0, /*RST=D4*/ 2, /*BUSY=D2*/ 4)); // GDEH116T91 960x640, SSD1677
// 3-color e-papers
//GxEPD2_3C<GxEPD2_154c, GxEPD2_154c::HEIGHT> display(GxEPD2_154c(/*CS=D8*/ SS, /*DC=D3*/ 0, /*RST=D4*/ 2, /*BUSY=D2*/ 4)); // GDEW0154Z04 200x200, IL0376F, no longer available
//GxEPD2_3C<GxEPD2_154_Z90c, GxEPD2_154_Z90c::HEIGHT> display(GxEPD2_154_Z90c(/*CS=D8*/ SS, /*DC=D3*/ 0, /*RST=D4*/ 2, /*BUSY=D2*/ 4)); // GDEH0154Z90 200x200, SSD1681
//GxEPD2_3C<GxEPD2_213c, GxEPD2_213c::HEIGHT> display(GxEPD2_213c(/*CS=D8*/ SS, /*DC=D3*/ 0, /*RST=D4*/ 2, /*BUSY=D2*/ 4)); // GDEW0213Z16 104x212, UC8151 (IL0373)
//GxEPD2_3C<GxEPD2_213_Z19c, GxEPD2_213_Z19c::HEIGHT> display(GxEPD2_213_Z19c(/*CS=D8*/ SS, /*DC=D3*/ 0, /*RST=D4*/ 2, /*BUSY=D2*/ 4)); // GDEH0213Z19 104x212, UC8151D
//GxEPD2_3C<GxEPD2_213_Z98c, GxEPD2_213_Z98c::HEIGHT> display(GxEPD2_213_Z98c(/*CS=D8*/ SS, /*DC=D3*/ 0, /*RST=D4*/ 2, /*BUSY=D2*/ 4)); // GDEY0213Z98 122x250, SSD1680
//GxEPD2_3C<GxEPD2_266c, GxEPD2_266c::HEIGHT> display(GxEPD2_266c(/*CS=D8*/ SS, /*DC=D3*/ 0, /*RST=D4*/ 2, /*BUSY=D2*/ 4)); // GDEY0266Z90 152x296, SSD1680
//GxEPD2_3C<GxEPD2_270c, GxEPD2_270c::HEIGHT> display(GxEPD2_270c(/*CS=D8*/ SS, /*DC=D3*/ 0, /*RST=D4*/ 2, /*BUSY=D2*/ 4)); // GDEW027C44 176x264, IL91874
//GxEPD2_3C<GxEPD2_290c, GxEPD2_290c::HEIGHT> display(GxEPD2_290c(/*CS=D8*/ SS, /*DC=D3*/ 0, /*RST=D4*/ 2, /*BUSY=D2*/ 4)); // GDEW029Z10 128x296, UC8151 (IL0373)
//GxEPD2_3C<GxEPD2_290_Z13c, GxEPD2_290_Z13c::HEIGHT> display(GxEPD2_290_Z13c(/*CS=D8*/ SS, /*DC=D3*/ 0, /*RST=D4*/ 2, /*BUSY=D2*/ 4)); // GDEH029Z13 128x296, UC8151D
//GxEPD2_3C<GxEPD2_290_C90c, GxEPD2_290_C90c::HEIGHT> display(GxEPD2_290_C90c(/*CS=D8*/ SS, /*DC=D3*/ 0, /*RST=D4*/ 2, /*BUSY=D2*/ 4)); // GDEM029C90 128x296, SSD1680
// can use only half buffer size
//GxEPD2_3C<GxEPD2_420c, GxEPD2_420c::HEIGHT / 2> display(GxEPD2_420c(/*CS=D8*/ SS, /*DC=D3*/ 0, /*RST=D4*/ 2, /*BUSY=D2*/ 4)); // GDEW042Z15 400x300, UC8176 (IL0398)
//GxEPD2_3C<GxEPD2_420c_Z21, GxEPD2_420c_Z21::HEIGHT / 2> display(GxEPD2_420c_Z21(/*CS=D8*/ SS, /*DC=D3*/ 0, /*RST=D4*/ 2, /*BUSY=D2*/ 4)); // GDEQ042Z21 400x300, UC8276
// can use only quarter buffer size
//GxEPD2_3C < GxEPD2_583c, GxEPD2_583c::HEIGHT / 4 > display(GxEPD2_583c(/*CS=D8*/ SS, /*DC=D3*/ 0, /*RST=D4*/ 2, /*BUSY=D2*/ 4)); // GDEW0583Z21 600x448, UC8179 (IL0371)
//GxEPD2_3C < GxEPD2_583c_Z83, GxEPD2_583c_Z83::HEIGHT / 4 > display(GxEPD2_583c_Z83(/*CS=D8*/ SS, /*DC=D3*/ 0, /*RST=D4*/ 2, /*BUSY=D2*/ 4)); // GDEW0583Z83 648x480, GD7965
//GxEPD2_3C<GxEPD2_750c, GxEPD2_750c::HEIGHT / 4> display(GxEPD2_750c(/*CS=D8*/ SS, /*DC=D3*/ 0, /*RST=D4*/ 2, /*BUSY=D2*/ 4)); // GDEW075Z09 640x384, UC8179 (IL0371)
//GxEPD2_3C < GxEPD2_750c_Z08, GxEPD2_750c_Z08::HEIGHT / 4 > display(GxEPD2_750c_Z08(/*CS=D8*/ SS, /*DC=D3*/ 0, /*RST=D4*/ 2, /*BUSY=D2*/ 4)); // GDEW075Z08 800x480, GD7965
//GxEPD2_3C < GxEPD2_750c_Z90, GxEPD2_750c_Z90::HEIGHT / 4 > display(GxEPD2_750c_Z90(/*CS=D8*/ SS, /*DC=D3*/ 0, /*RST=D4*/ 2, /*BUSY=D2*/ 4)); // GDEH075Z90 880x528, SSD1677
// 4-color e-paper
//GxEPD2_4C<GxEPD2_266c_GDEY0266F51H, GxEPD2_266c_GDEY0266F51H::HEIGHT> display(GxEPD2_266c_GDEY0266F51H(/*CS=D8*/ SS, /*DC=D3*/ 0, /*RST=D4*/ 2, /*BUSY=D2*/ 4)); // GDEY0266F51H 184x360, JD79667 (FPC-H006 22.04.02)
//GxEPD2_4C<GxEPD2_290c_GDEY029F51H, GxEPD2_290c_GDEY029F51H::HEIGHT> display(GxEPD2_290c_GDEY029F51H(/*CS=D8*/ SS, /*DC=D3*/ 0, /*RST=D4*/ 2, /*BUSY=D2*/ 4)); // GDEY029F51H 168x384, JD79667 (FPC-H004 22.03.24)
//GxEPD2_4C<GxEPD2_300c, GxEPD2_300c::HEIGHT> display(GxEPD2_300c(/*CS=D8*/ SS, /*DC=D3*/ 0, /*RST=D4*/ 2, /*BUSY=D2*/ 4)); // Waveshare 3.00" 4-color
//GxEPD2_4C<GxEPD2_420c_GDEY0420F51, GxEPD2_420c_GDEY0420F51::HEIGHT> display(GxEPD2_420c_GDEY0420F51(/*CS=D8*/ SS, /*DC=D3*/ 0, /*RST=D4*/ 2, /*BUSY=D2*/ 4)); // GDEY0420F51 400x300, HX8717 (no inking)
//GxEPD2_4C < GxEPD2_437c, GxEPD2_437c::HEIGHT / 4 > display(GxEPD2_437c(/*CS=D8*/ SS, /*DC=D3*/ 0, /*RST=D4*/ 2, /*BUSY=D2*/ 4)); // Waveshare 4.37" 4-color
// 7-color e-paper
//GxEPD2_3C < GxEPD2_565c, GxEPD2_565c::HEIGHT / 4 > display(GxEPD2_565c(/*CS=D8*/ SS, /*DC=D3*/ 0, /*RST=D4*/ 2, /*BUSY=D2*/ 4)); // Waveshare 5.65" 7-color (3C graphics)
//GxEPD2_7C < GxEPD2_565c, GxEPD2_565c::HEIGHT / 4 > display(GxEPD2_565c(/*CS=D8*/ SS, /*DC=D3*/ 0, /*RST=D4*/ 2, /*BUSY=D2*/ 4)); // Waveshare 5.65" 7-color
//GxEPD2_7C < GxEPD2_730c_GDEY073D46, GxEPD2_730c_GDEY073D46::HEIGHT / 6 > display(GxEPD2_730c_GDEY073D46(/*CS=D8*/ SS, /*DC=D3*/ 0, /*RST=D4*/ 2, /*BUSY=D2*/ 4)); // GDEY073D46 800x480 7-color, (N-FPC-001 2021.11.26)
// grey levels parallel IF e-papers on Waveshare e-Paper IT8951 Driver HAT
// HRDY -> 4, RST -> 2, CS -> SS(15), SCK -> SCK(14), MOSI -> MOSI(D7(13)), MISO -> MISO(D6(12)), GND -> GND, 5V -> 5V
// note: 5V supply needs to be exact and strong; 5V pin of USB powered Wemos D1 mini doesn't work!
//GxEPD2_BW<GxEPD2_it60, GxEPD2_it60::HEIGHT / 8> display(GxEPD2_it60(/*CS=5*/ SS, /*DC=*/ 0, /*RST=*/ 2, /*BUSY=*/ 4));
//GxEPD2_BW < GxEPD2_it60_1448x1072, GxEPD2_it60_1448x1072::HEIGHT / 8 > display(GxEPD2_it60_1448x1072(/*CS=5*/ SS, /*DC=*/ 0, /*RST=*/ 2, /*BUSY=*/ 4));
//GxEPD2_BW < GxEPD2_it78_1872x1404, GxEPD2_it78_1872x1404::HEIGHT / 8 > display(GxEPD2_it78_1872x1404(/*CS=5*/ SS, /*DC=*/ 0, /*RST=*/ 2, /*BUSY=*/ 4));
//GxEPD2_BW < GxEPD2_it103_1872x1404, GxEPD2_it103_1872x1404::HEIGHT / 8 > display(GxEPD2_it103_1872x1404(/*CS=5*/ SS, /*DC=*/ 0, /*RST=*/ 2, /*BUSY=*/ 4));

// ***** for mapping of Waveshare e-Paper ESP8266 Driver Board *****
// select one , can use full buffer size (full HEIGHT)
//GxEPD2_BW<GxEPD2_150_BN, GxEPD2_150_BN::HEIGHT> display(GxEPD2_150_BN(/*CS=15*/ SS, /*DC=4*/ 4, /*RST=2*/ 2, /*BUSY=5*/ 5)); // DEPG0150BN 200x200, SSD1681, TTGO T5 V2.4.1
//GxEPD2_BW<GxEPD2_154, GxEPD2_154::HEIGHT> display(GxEPD2_154(/*CS=15*/ SS, /*DC=4*/ 4, /*RST=2*/ 2, /*BUSY=5*/ 5)); // GDEP015OC1 200x200, IL3829, no longer available
//GxEPD2_BW<GxEPD2_154_D67, GxEPD2_154_D67::HEIGHT> display(GxEPD2_154_D67(/*CS=15*/ SS, /*DC=4*/ 4, /*RST=2*/ 2, /*BUSY=5*/ 5)); // GDEH0154D67 200x200, SSD1681
//GxEPD2_BW<GxEPD2_154_T8, GxEPD2_154_T8::HEIGHT> display(GxEPD2_154_T8(/*CS=15*/ SS, /*DC=4*/ 4, /*RST=2*/ 2, /*BUSY=5*/ 5)); // GDEW0154T8  152x152, UC8151 (IL0373)
//GxEPD2_BW<GxEPD2_154_M09, GxEPD2_154_M09::HEIGHT> display(GxEPD2_154_M09(/*CS=15*/ SS, /*DC=4*/ 4, /*RST=2*/ 2, /*BUSY=5*/ 5)); // GDEW0154M09 200x200, JD79653A
//GxEPD2_BW<GxEPD2_154_M10, GxEPD2_154_M10::HEIGHT> display(GxEPD2_154_M10(/*CS=15*/ SS, /*DC=4*/ 4, /*RST=2*/ 2, /*BUSY=5*/ 5)); // GDEW0154M10 152x152, UC8151D
//GxEPD2_BW<GxEPD2_154_GDEY0154D67, GxEPD2_154_GDEY0154D67::HEIGHT> display(GxEPD2_154_GDEY0154D67(/*CS=15*/ SS, /*DC=4*/ 4, /*RST=2*/ 2, /*BUSY=5*/ 5)); // GDEY0154D67 200x200, SSD1681, (FPC-B001 20.05.21)
//GxEPD2_BW<GxEPD2_213, GxEPD2_213::HEIGHT> display(GxEPD2_213(/*CS=15*/ SS, /*DC=4*/ 4, /*RST=2*/ 2, /*BUSY=5*/ 5)); // GDE0213B1 122x250, IL3895, phased out
//GxEPD2_BW<GxEPD2_213_B72, GxEPD2_213_B72::HEIGHT> display(GxEPD2_213_B72(/*CS=15*/ SS, /*DC=4*/ 4, /*RST=2*/ 2, /*BUSY=5*/ 5)); // GDEH0213B72 122x250, SSD1675A (IL3897)
//GxEPD2_BW<GxEPD2_213_B73, GxEPD2_213_B73::HEIGHT> display(GxEPD2_213_B73(/*CS=15*/ SS, /*DC=4*/ 4, /*RST=2*/ 2, /*BUSY=5*/ 5)); // GDEH0213B73 122x250, SSD1675B
//GxEPD2_BW<GxEPD2_213_B74, GxEPD2_213_B74::HEIGHT> display(GxEPD2_213_B74(/*CS=15*/ SS, /*DC=4*/ 4, /*RST=2*/ 2, /*BUSY=5*/ 5)); // GDEM0213B74 122x250, SSD1680
//GxEPD2_BW<GxEPD2_213_flex, GxEPD2_213_flex::HEIGHT> display(GxEPD2_213_flex(/*CS=15*/ SS, /*DC=4*/ 4, /*RST=2*/ 2, /*BUSY=5*/ 5)); // GDEW0213I5F 104x212, UC8151 (IL0373)
//GxEPD2_BW<GxEPD2_213_M21, GxEPD2_213_M21::HEIGHT> display(GxEPD2_213_M21(/*CS=15*/ SS, /*DC=4*/ 4, /*RST=2*/ 2, /*BUSY=5*/ 5)); // GDEW0213M21 104x212, UC8151 (IL0373)
//GxEPD2_BW<GxEPD2_213_T5D, GxEPD2_213_T5D::HEIGHT> display(GxEPD2_213_T5D(/*CS=15*/ SS, /*DC=4*/ 4, /*RST=2*/ 2, /*BUSY=5*/ 5)); // GDEW0213T5D 104x212, UC8151D
//GxEPD2_BW<GxEPD2_213_BN, GxEPD2_213_BN::HEIGHT> display(GxEPD2_213_BN(/*CS=15*/ SS, /*DC=4*/ 4, /*RST=2*/ 2, /*BUSY=5*/ 5)); // DEPG0213BN 122x250, SSD1680, TTGO T5 V2.4.1, V2.3.1
//GxEPD2_BW<GxEPD2_213_GDEY0213B74, GxEPD2_213_GDEY0213B74::HEIGHT> display(GxEPD2_213_GDEY0213B74(/*CS=15*/ SS, /*DC=4*/ 4, /*RST=2*/ 2, /*BUSY=5*/ 5)); // GDEY0213B74 122x250, SSD1680, (FPC-A002 20.04.08)
//GxEPD2_BW<GxEPD2_260, GxEPD2_260::HEIGHT> display(GxEPD2_260(/*CS=15*/ SS, /*DC=4*/ 4, /*RST=2*/ 2, /*BUSY=5*/ 5)); // GDEW026T0 152x296, UC8151 (IL0373)
//GxEPD2_BW<GxEPD2_260_M01, GxEPD2_260_M01::HEIGHT> display(GxEPD2_260_M01(/*CS=15*/ SS, /*DC=4*/ 4, /*RST=2*/ 2, /*BUSY=5*/ 5)); // GDEW026M01 152x296, UC8151 (IL0373)
//GxEPD2_BW<GxEPD2_266_BN, GxEPD2_266_BN::HEIGHT> display(GxEPD2_266_BN(/*CS=15*/ SS, /*DC=4*/ 4, /*RST=2*/ 2, /*BUSY=5*/ 5)); // DEPG0266BN 152x296, SSD1680, TTGO T5 V2.66 / T92_V1.0
//GxEPD2_BW<GxEPD2_270, GxEPD2_270::HEIGHT> display(GxEPD2_270(/*CS=15*/ SS, /*DC=4*/ 4, /*RST=2*/ 2, /*BUSY=5*/ 5)); // GDEW027W3 176x264, EK79652 (IL91874)
//GxEPD2_BW<GxEPD2_270_GDEY027T91, GxEPD2_270_GDEY027T91::HEIGHT> display(GxEPD2_270_GDEY027T91(/*CS=15*/ SS, /*DC=4*/ 4, /*RST=2*/ 2, /*BUSY=5*/ 5)); // GDEY027T91 176x264, SSD1680
//GxEPD2_BW<GxEPD2_290, GxEPD2_290::HEIGHT> display(GxEPD2_290(/*CS=15*/ SS, /*DC=4*/ 4, /*RST=2*/ 2, /*BUSY=5*/ 5)); // GDEH029A1 128x296, SSD1608 (IL3820)
//GxEPD2_BW<GxEPD2_290_T5, GxEPD2_290_T5::HEIGHT> display(GxEPD2_290_T5(/*CS=15*/ SS, /*DC=4*/ 4, /*RST=2*/ 2, /*BUSY=5*/ 5)); // GDEW029T5 128x296, UC8151 (IL0373)
//GxEPD2_BW<GxEPD2_290_T5D, GxEPD2_290_T5D::HEIGHT> display(GxEPD2_290_T5D(/*CS=15*/ SS, /*DC=4*/ 4, /*RST=2*/ 2, /*BUSY=5*/ 5)); // GDEW029T5D 128x296, UC8151D
//GxEPD2_BW<GxEPD2_290_I6FD, GxEPD2_290_I6FD::HEIGHT> display(GxEPD2_290_I6FD(/*CS=15*/ SS, /*DC=4*/ 4, /*RST=2*/ 2, /*BUSY=5*/ 5)); // GDEW029I6FD 128x296, UC8151D
//GxEPD2_BW<GxEPD2_290_T94, GxEPD2_290_T94::HEIGHT> display(GxEPD2_290_T94(/*CS=15*/ SS, /*DC=4*/ 4, /*RST=2*/ 2, /*BUSY=5*/ 5)); // GDEM029T94 128x296, SSD1680
//GxEPD2_BW<GxEPD2_290_T94_V2, GxEPD2_290_T94_V2::HEIGHT> display(GxEPD2_290_T94_V2(/*CS=15*/ SS, /*DC=4*/ 4, /*RST=2*/ 2, /*BUSY=5*/ 5)); // GDEM029T94 128x296, SSD1680, Waveshare 2.9" V2 variant
//GxEPD2_BW<GxEPD2_290_BS, GxEPD2_290_BS::HEIGHT> display(GxEPD2_290_BS(/*CS=15*/ SS, /*DC=4*/ 4, /*RST=2*/ 2, /*BUSY=5*/ 5)); // DEPG0290BS 128x296, SSD1680
//GxEPD2_BW<GxEPD2_290_M06, GxEPD2_290_M06::HEIGHT> display(GxEPD2_290_M06(/*CS=15*/ SS, /*DC=4*/ 4, /*RST=2*/ 2, /*BUSY=5*/ 5)); // GDEW029M06  128x296, UC8151D
//GxEPD2_BW<GxEPD2_290_GDEY029T94, GxEPD2_290_GDEY029T94::HEIGHT> display(GxEPD2_290_GDEY029T94(/*CS=15*/ SS, /*DC=4*/ 4, /*RST=2*/ 2, /*BUSY=5*/ 5)); // GDEY029T94  128x296, SSD1680, (FPC-A005 20.06.15)
//GxEPD2_BW<GxEPD2_371, GxEPD2_371::HEIGHT> display(GxEPD2_371(/*CS=15*/ SS, /*DC=4*/ 4, /*RST=2*/ 2, /*BUSY=5*/ 5)); // GDEW0371W7 240x416, UC8171 (IL0324)
//GxEPD2_BW<GxEPD2_370_TC1, GxEPD2_370_TC1::HEIGHT> display(GxEPD2_370_TC1(/*CS=15*/ SS, /*DC=4*/ 4, /*RST=2*/ 2, /*BUSY=5*/ 5)); // ED037TC1 280x480, SSD1677, Waveshare 3.7"
//GxEPD2_BW<GxEPD2_420, GxEPD2_420::HEIGHT> display(GxEPD2_420(/*CS=15*/ SS, /*DC=4*/ 4, /*RST=2*/ 2, /*BUSY=5*/ 5)); // GDEW042T2 400x300, UC8176 (IL0398)
//GxEPD2_BW<GxEPD2_420_M01, GxEPD2_420_M01::HEIGHT> display(GxEPD2_420_M01(/*CS=15*/ SS, /*DC=4*/ 4, /*RST=2*/ 2, /*BUSY=5*/ 5)); // GDEW042M01 400x300, UC8176 (IL0398)
//GxEPD2_BW<GxEPD2_420_GDEY042T81, GxEPD2_420_GDEY042T81::HEIGHT> display(GxEPD2_420_GDEY042T81(/*CS=15*/ SS, /*DC=4*/ 4, /*RST=2*/ 2, /*BUSY=5*/ 5)); GDEY042T81, 400x300, SSD1683 (no inking)
//GxEPD2_BW<GxEPD2_426_GDEQ0426T82, GxEPD2_426_GDEQ0426T82::HEIGHT> display(GxEPD2_426_GDEQ0426T82(/*CS=15*/ SS, /*DC=4*/ 4, /*RST=2*/ 2, /*BUSY=5*/ 5)); // GDEQ0426T82 480x800, SSD1677 (P426010-MF1-A)
// can use only half buffer size
//GxEPD2_BW < GxEPD2_583, GxEPD2_583::HEIGHT / 2 > display(GxEPD2_583(/*CS=15*/ SS, /*DC=4*/ 4, /*RST=2*/ 2, /*BUSY=5*/ 5)); // GDEW0583T7 600x448, UC8159c (IL0371)
//GxEPD2_BW < GxEPD2_583_T8, GxEPD2_583_T8::HEIGHT / 2 > display(GxEPD2_583_T8(/*CS=15*/ SS, /*DC=4*/ 4, /*RST=2*/ 2, /*BUSY=5*/ 5)); // GDEW0583T8 648x480, EK79655 (GD7965)
//GxEPD2_BW < GxEPD2_583_GDEQ0583T31, GxEPD2_583_GDEQ0583T31::HEIGHT / 2 > display(GxEPD2_583_GDEQ0583T31(/*CS=15*/ SS, /*DC=4*/ 4, /*RST=2*/ 2, /*BUSY=5*/ 5)); // GDEQ0583T31 648x480, UC8179, (P583010-MF1-B)
//GxEPD2_BW < GxEPD2_750, GxEPD2_750::HEIGHT / 2 > display(GxEPD2_750(/*CS=15*/ SS, /*DC=4*/ 4, /*RST=2*/ 2, /*BUSY=5*/ 5)); // GDEW075T8 640x384, UC8159c (IL0371)
//GxEPD2_BW < GxEPD2_750_T7, GxEPD2_750_T7::HEIGHT / 2 > display(GxEPD2_750_T7(/*CS=15*/ SS, /*DC=4*/ 4, /*RST=2*/ 2, /*BUSY=5*/ 5)); // GDEW075T7 800x480, EK79655 (GD7965)
//GxEPD2_BW < GxEPD2_750_YT7, GxEPD2_750_YT7::HEIGHT / 2 > display(GxEPD2_750_YT7(/*CS=15*/ SS, /*DC=4*/ 4, /*RST=2*/ 2, /*BUSY=5*/ 5)); // GDEY075T7 800x480, UC8179 (GD7965)
//GxEPD2_BW < GxEPD2_1160_T91, GxEPD2_1160_T91::HEIGHT / 2 > display(GxEPD2_1160_T91(/*CS=15*/ SS, /*DC=4*/ 4, /*RST=2*/ 2, /*BUSY=5*/ 5)); // GDEH116T91 960x640, SSD1677
// 3-color e-papers
//GxEPD2_3C<GxEPD2_154c, GxEPD2_154c::HEIGHT> display(GxEPD2_154c(/*CS=15*/ SS, /*DC=4*/ 4, /*RST=2*/ 2, /*BUSY=5*/ 5)); // GDEW0154Z04 200x200, IL0376F, no longer available
//GxEPD2_3C<GxEPD2_154_Z90c, GxEPD2_154_Z90c::HEIGHT> display(GxEPD2_154_Z90c(/*CS=15*/ SS, /*DC=4*/ 4, /*RST=2*/ 2, /*BUSY=5*/ 5)); // GDEH0154Z90 200x200, SSD1681
//GxEPD2_3C<GxEPD2_213c, GxEPD2_213c::HEIGHT> display(GxEPD2_213c(/*CS=15*/ SS, /*DC=4*/ 4, /*RST=2*/ 2, /*BUSY=5*/ 5)); // GDEW0213Z16 104x212, UC8151 (IL0373)
//GxEPD2_3C<GxEPD2_213_Z19c, GxEPD2_213_Z19c::HEIGHT> display(GxEPD2_213_Z19c(/*CS=15*/ SS, /*DC=4*/ 4, /*RST=2*/ 2, /*BUSY=5*/ 5)); // GDEH0213Z19 104x212, UC8151D
//GxEPD2_3C<GxEPD2_213_Z98c, GxEPD2_213_Z98c::HEIGHT> display(GxEPD2_213_Z98c(/*CS=15*/ SS, /*DC=4*/ 4, /*RST=2*/ 2, /*BUSY=5*/ 5)); // GDEY0213Z98 122x250, SSD1680
//GxEPD2_3C<GxEPD2_266c, GxEPD2_266c::HEIGHT> display(GxEPD2_266c(/*CS=15*/ SS, /*DC=4*/ 4, /*RST=2*/ 2, /*BUSY=5*/ 5)); // GDEY0266Z90 152x296, SSD1680
//GxEPD2_3C<GxEPD2_270c, GxEPD2_270c::HEIGHT> display(GxEPD2_270c(/*CS=15*/ SS, /*DC=4*/ 4, /*RST=2*/ 2, /*BUSY=5*/ 5)); // GDEW027C44 176x264, IL91874
//GxEPD2_3C<GxEPD2_290c, GxEPD2_290c::HEIGHT> display(GxEPD2_290c(/*CS=15*/ SS, /*DC=4*/ 4, /*RST=2*/ 2, /*BUSY=5*/ 5)); // GDEW029Z10 128x296, UC8151 (IL0373)
//GxEPD2_3C<GxEPD2_290_Z13c, GxEPD2_290_Z13c::HEIGHT> display(GxEPD2_290_Z13c(/*CS=15*/ SS, /*DC=4*/ 4, /*RST=2*/ 2, /*BUSY=5*/ 5)); // GDEH029Z13 128x296, UC8151D
//GxEPD2_3C<GxEPD2_290_C90c, GxEPD2_290_C90c::HEIGHT> display(GxEPD2_290_C90c(/*CS=15*/ SS, /*DC=4*/ 4, /*RST=2*/ 2, /*BUSY=5*/ 5)); // GDEM029C90 128x296, SSD1680
// can use only half buffer size
//GxEPD2_3C<GxEPD2_420c, GxEPD2_420c::HEIGHT / 2> display(GxEPD2_420c(/*CS=15*/ SS, /*DC=4*/ 4, /*RST=2*/ 2, /*BUSY=5*/ 5)); // GDEW042Z15 400x300, UC8176 (IL0398)
//GxEPD2_3C<GxEPD2_420c_Z21, GxEPD2_420c_Z21::HEIGHT / 2> display(GxEPD2_420c_Z21(/*CS=15*/ SS, /*DC=4*/ 4, /*RST=2*/ 2, /*BUSY=5*/ 5)); // GDEQ042Z21 400x300, UC8276
// can use only quarter buffer size
//GxEPD2_3C<GxEPD2_583c, GxEPD2_583c::HEIGHT / 4> display(GxEPD2_583c(/*CS=15*/ SS, /*DC=4*/ 4, /*RST=2*/ 2, /*BUSY=5*/ 5)); // GDEW0583Z21 600x448, UC8179 (IL0371)
//GxEPD2_3C<GxEPD2_583c_Z83, GxEPD2_583c_Z83::HEIGHT / 4> display(GxEPD2_583c_Z83(/*CS=15*/ SS, /*DC=4*/ 4, /*RST=2*/ 2, /*BUSY=5*/ 5)); // GDEW0583Z83 648x480, GD7965
//GxEPD2_3C<GxEPD2_750c, GxEPD2_750c::HEIGHT / 4> display(GxEPD2_750c(/*CS=15*/ SS, /*DC=4*/ 4, /*RST=2*/ 2, /*BUSY=5*/ 5)); // GDEW075Z09 640x384, UC8179 (IL0371)
//GxEPD2_3C<GxEPD2_750c_Z08, GxEPD2_750c_Z08::HEIGHT / 4> display(GxEPD2_750c_Z08(/*CS=15*/ SS, /*DC=4*/ 4, /*RST=2*/ 2, /*BUSY=5*/ 5)); // GDEW075Z08 800x480, GD7965
//GxEPD2_3C<GxEPD2_750c_Z90, GxEPD2_750c_Z90::HEIGHT / 4> display(GxEPD2_750c_Z90(/*CS=15*/ SS, /*DC=4*/ 4, /*RST=2*/ 2, /*BUSY=5*/ 5)); // GDEH075Z90 880x528, SSD1677
// 4-color e-paper
//GxEPD2_4C<GxEPD2_266c_GDEY0266F51H, GxEPD2_266c_GDEY0266F51H::HEIGHT> display(GxEPD2_266c_GDEY0266F51H(/*CS=15*/ SS, /*DC=4*/ 4, /*RST=2*/ 2, /*BUSY=5*/ 5)); // GDEY0266F51H 184x360, JD79667 (FPC-H006 22.04.02)
//GxEPD2_4C<GxEPD2_290c_GDEY029F51H, GxEPD2_290c_GDEY029F51H::HEIGHT> display(GxEPD2_290c_GDEY029F51H(/*CS=15*/ SS, /*DC=4*/ 4, /*RST=2*/ 2, /*BUSY=5*/ 5)); // GDEY029F51H 168x384, JD79667 (FPC-H004 22.03.24)
//GxEPD2_4C<GxEPD2_300c, GxEPD2_300c::HEIGHT> display(GxEPD2_300c(/*CS=15*/ SS, /*DC=4*/ 4, /*RST=2*/ 2, /*BUSY=5*/ 5)); // Waveshare 3.00" 4-color
//GxEPD2_4C<GxEPD2_420c_GDEY0420F51, GxEPD2_420c_GDEY0420F51::HEIGHT> display(GxEPD2_420c_GDEY0420F51(/*CS=15*/ SS, /*DC=4*/ 4, /*RST=2*/ 2, /*BUSY=5*/ 5)); // GDEY0420F51 400x300, HX8717 (no inking)
//GxEPD2_4C < GxEPD2_437c, GxEPD2_437c::HEIGHT / 4 > display(GxEPD2_437c(/*CS=15*/ SS, /*DC=4*/ 4, /*RST=2*/ 2, /*BUSY=5*/ 5)); // Waveshare 4.37" 4-color
// 7-color e-paper
//GxEPD2_7C < GxEPD2_565c, GxEPD2_565c::HEIGHT / 4 > display(GxEPD2_565c(/*CS=15*/ SS, /*DC=4*/ 4, /*RST=2*/ 2, /*BUSY=5*/ 5)); // Waveshare 5.65" 7-color
//GxEPD2_7C < GxEPD2_730c_GDEY073D46, GxEPD2_730c_GDEY073D46::HEIGHT / 6 > display(GxEPD2_730c_GDEY073D46(/*CS=15*/ SS, /*DC=4*/ 4, /*RST=2*/ 2, /*BUSY=5*/ 5)); // GDEY073D46 800x480 7-color, (N-FPC-001 2021.11.26)
#endif

#if defined(ESP32)
// select one and adapt to your mapping, can use full buffer size (full HEIGHT)
//GxEPD2_BW<GxEPD2_102, GxEPD2_102::HEIGHT> display(GxEPD2_102(/*CS=5*/ SS, /*DC=*/ 17, /*RST=*/ 16, /*BUSY=*/ 4)); // GDEW0102T4 80x128, UC8175
//GxEPD2_BW<GxEPD2_150_BN, GxEPD2_150_BN::HEIGHT> display(GxEPD2_150_BN(/*CS=5*/ SS, /*DC=*/ 17, /*RST=*/ 16, /*BUSY=*/ 4)); // DEPG0150BN 200x200, SSD1681, TTGO T5 V2.4.1
//GxEPD2_BW<GxEPD2_154, GxEPD2_154::HEIGHT> display(GxEPD2_154(/*CS=5*/ SS, /*DC=*/ 17, /*RST=*/ 16, /*BUSY=*/ 4)); // GDEP015OC1 200x200, IL3829, no longer available
//GxEPD2_BW<GxEPD2_154_D67, GxEPD2_154_D67::HEIGHT> display(GxEPD2_154_D67(/*CS=5*/ SS, /*DC=*/ 17, /*RST=*/ 16, /*BUSY=*/ 4)); // GDEH0154D67 200x200, SSD1681

//GxEPD2_BW<GxEPD2_154_T8, GxEPD2_154_T8::HEIGHT> display(GxEPD2_154_T8(/*CS=5*/ SS, /*DC=*/ 17, /*RST=*/ 16, /*BUSY=*/ 4)); // GDEW0154T8  152x152, UC8151 (IL0373)
//GxEPD2_BW<GxEPD2_154_M09, GxEPD2_154_M09::HEIGHT> display(GxEPD2_154_M09(/*CS=5*/ SS, /*DC=*/ 17, /*RST=*/ 16, /*BUSY=*/ 4)); // GDEW0154M09 200x200, JD79653A
//GxEPD2_BW<GxEPD2_154_M10, GxEPD2_154_M10::HEIGHT> display(GxEPD2_154_M10(/*CS=5*/ SS, /*DC=*/ 17, /*RST=*/ 16, /*BUSY=*/ 4)); // GDEW0154M10 152x152, UC8151D
//GxEPD2_BW<GxEPD2_154_GDEY0154D67, GxEPD2_154_GDEY0154D67::HEIGHT> display(GxEPD2_154_GDEY0154D67(/*CS=5*/ SS, /*DC=*/ 17, /*RST=*/ 16, /*BUSY=*/ 4)); // GDEY0154D67 200x200, SSD1681, (FPC-B001 20.05.21)
//GxEPD2_BW<GxEPD2_213, GxEPD2_213::HEIGHT> display(GxEPD2_213(/*CS=5*/ SS, /*DC=*/ 17, /*RST=*/ 16, /*BUSY=*/ 4)); // GDE0213B1 122x250, IL3895, phased out
//GxEPD2_BW<GxEPD2_213_B72, GxEPD2_213_B72::HEIGHT> display(GxEPD2_213_B72(/*CS=5*/ SS, /*DC=*/ 17, /*RST=*/ 16, /*BUSY=*/ 4)); // GDEH0213B72 122x250, SSD1675A (IL3897)
//GxEPD2_BW<GxEPD2_213_B73, GxEPD2_213_B73::HEIGHT> display(GxEPD2_213_B73(/*CS=5*/ SS, /*DC=*/ 17, /*RST=*/ 16, /*BUSY=*/ 4)); // GDEH0213B73 122x250, SSD1675B
//GxEPD2_BW<GxEPD2_213_B74, GxEPD2_213_B74::HEIGHT> display(GxEPD2_213_B74(/*CS=5*/ SS, /*DC=*/ 17, /*RST=*/ 16, /*BUSY=*/ 4)); // GDEM0213B74 122x250, SSD1680
//GxEPD2_BW<GxEPD2_213_flex, GxEPD2_213_flex::HEIGHT> display(GxEPD2_213_flex(/*CS=5*/ SS, /*DC=*/ 17, /*RST=*/ 16, /*BUSY=*/ 4)); // GDEW0213I5F 104x212, UC8151 (IL0373)
//GxEPD2_BW<GxEPD2_213_M21, GxEPD2_213_M21::HEIGHT> display(GxEPD2_213_M21(/*CS=5*/ SS, /*DC=*/ 17, /*RST=*/ 16, /*BUSY=*/ 4)); // GDEW0213M21 104x212, UC8151 (IL0373)
//GxEPD2_BW<GxEPD2_213_T5D, GxEPD2_213_T5D::HEIGHT> display(GxEPD2_213_T5D(/*CS=5*/ SS, /*DC=*/ 17, /*RST=*/ 16, /*BUSY=*/ 4)); // GDEW0213T5D 104x212, UC8151D
GxEPD2_BW<GxEPD2_213_BN, GxEPD2_213_BN::HEIGHT> display(GxEPD2_213_BN(/*CS=5*/ SS, /*DC=*/ 17, /*RST=*/ 16, /*BUSY=*/ 4)); // DEPG0213BN 122x250, SSD1680, TTGO T5 V2.4.1, V2.3.1
//GxEPD2_BW<GxEPD2_213_GDEY0213B74, GxEPD2_213_GDEY0213B74::HEIGHT> display(GxEPD2_213_GDEY0213B74(/*CS=5*/ SS, /*DC=*/ 17, /*RST=*/ 16, /*BUSY=*/ 4)); // GDEY0213B74 122x250, SSD1680, (FPC-A002 20.04.08)
//GxEPD2_BW<GxEPD2_260, GxEPD2_260::HEIGHT> display(GxEPD2_260(/*CS=5*/ SS, /*DC=*/ 17, /*RST=*/ 16, /*BUSY=*/ 4)); // GDEW026T0 152x296, UC8151 (IL0373)
//GxEPD2_BW<GxEPD2_260_M01, GxEPD2_260_M01::HEIGHT> display(GxEPD2_260_M01(/*CS=5*/ SS, /*DC=*/ 17, /*RST=*/ 16, /*BUSY=*/ 4)); // GDEW026M01 152x296, UC8151 (IL0373)
//GxEPD2_BW<GxEPD2_266_BN, GxEPD2_266_BN::HEIGHT> display(GxEPD2_266_BN(/*CS=5*/ SS, /*DC=*/ 17, /*RST=*/ 16, /*BUSY=*/ 4)); // DEPG0266BN 152x296, SSD1680, TTGO T5 V2.4.1
//GxEPD2_BW<GxEPD2_270, GxEPD2_270::HEIGHT> display(GxEPD2_270(/*CS=5*/ SS, /*DC=*/ 17, /*RST=*/ 16, /*BUSY=*/ 4)); // GDEW027W3 176x264, EK79652 (IL91874)
//GxEPD2_BW<GxEPD2_270_GDEY027T91, GxEPD2_270_GDEY027T91::HEIGHT> display(GxEPD2_270_GDEY027T91(/*CS=5*/ SS, /*DC=*/ 17, /*RST=*/ 16, /*BUSY=*/ 4)); // GDEY027T91 176x264, SSD1680
//GxEPD2_BW<GxEPD2_290, GxEPD2_290::HEIGHT> display(GxEPD2_290(/*CS=5*/ SS, /*DC=*/ 17, /*RST=*/ 16, /*BUSY=*/ 4)); // GDEH029A1 128x296, SSD1608 (IL3820)
//GxEPD2_BW<GxEPD2_290_T5, GxEPD2_290_T5::HEIGHT> display(GxEPD2_290_T5(/*CS=5*/ SS, /*DC=*/ 17, /*RST=*/ 16, /*BUSY=*/ 4)); // GDEW029T5 128x296, UC8151 (IL0373)
//GxEPD2_BW<GxEPD2_290_T5D, GxEPD2_290_T5D::HEIGHT> display(GxEPD2_290_T5D(/*CS=5*/ SS, /*DC=*/ 17, /*RST=*/ 16, /*BUSY=*/ 4)); // GDEW029T5D 128x296, UC8151D
//GxEPD2_BW<GxEPD2_290_I6FD, GxEPD2_290_I6FD::HEIGHT> display(GxEPD2_290_I6FD(/*CS=5*/ SS, /*DC=*/ 17, /*RST=*/ 16, /*BUSY=*/ 4)); // GDEW029I6FD 128x296, UC8151D
//GxEPD2_BW<GxEPD2_290_T94, GxEPD2_290_T94::HEIGHT> display(GxEPD2_290_T94(/*CS=5*/ SS, /*DC=*/ 17, /*RST=*/ 16, /*BUSY=*/ 4)); // GDEM029T94 128x296, SSD1680
//GxEPD2_BW<GxEPD2_290_T94_V2, GxEPD2_290_T94_V2::HEIGHT> display(GxEPD2_290_T94_V2(/*CS=5*/ SS, /*DC=*/ 17, /*RST=*/ 16, /*BUSY=*/ 4)); // GDEM029T94 128x296, SSD1680, Waveshare 2.9" V2 variant
//GxEPD2_BW<GxEPD2_290_BS, GxEPD2_290_BS::HEIGHT> display(GxEPD2_290_BS(/*CS=5*/ SS, /*DC=*/ 17, /*RST=*/ 16, /*BUSY=*/ 4)); // DEPG0290BS 128x296, SSD1680
//GxEPD2_BW<GxEPD2_290_M06, GxEPD2_290_M06::HEIGHT> display(GxEPD2_290_M06(/*CS=5*/ SS, /*DC=*/ 17, /*RST=*/ 16, /*BUSY=*/ 4)); // GDEW029M06  128x296, UC8151D
//GxEPD2_BW<GxEPD2_290_GDEY029T94, GxEPD2_290_GDEY029T94::HEIGHT> display(GxEPD2_290_GDEY029T94(/*CS=5*/ SS, /*DC=*/ 17, /*RST=*/ 16, /*BUSY=*/ 4)); // GDEY029T94  128x296, SSD1680, (FPC-A005 20.06.15)
//GxEPD2_BW<GxEPD2_371, GxEPD2_371::HEIGHT> display(GxEPD2_371(/*CS=5*/ SS, /*DC=*/ 17, /*RST=*/ 16, /*BUSY=*/ 4)); // GDEW0371W7 240x416, UC8171 (IL0324)
//GxEPD2_BW<GxEPD2_370_TC1, GxEPD2_370_TC1::HEIGHT> display(GxEPD2_370_TC1(/*CS=5*/ SS, /*DC=*/ 17, /*RST=*/ 16, /*BUSY=*/ 4)); // ED037TC1 280x480, SSD1677, Waveshare 3.7"
//GxEPD2_BW<GxEPD2_420, GxEPD2_420::HEIGHT> display(GxEPD2_420(/*CS=5*/ SS, /*DC=*/ 17, /*RST=*/ 16, /*BUSY=*/ 4)); // GDEW042T2 400x300, UC8176 (IL0398)
//GxEPD2_BW<GxEPD2_420_M01, GxEPD2_420_M01::HEIGHT> display(GxEPD2_420_M01(/*CS=5*/ SS, /*DC=*/ 17, /*RST=*/ 16, /*BUSY=*/ 4)); // GDEW042M01 400x300, UC8176 (IL0398)
//GxEPD2_BW<GxEPD2_420_GDEY042T81, GxEPD2_420_GDEY042T81::HEIGHT> display(GxEPD2_420_GDEY042T81(/*CS=5*/ SS, /*DC=*/ 17, /*RST=*/ 16, /*BUSY=*/ 4)); GDEY042T81, 400x300, SSD1683 (no inking)
//GxEPD2_BW<GxEPD2_426_GDEQ0426T82, GxEPD2_426_GDEQ0426T82::HEIGHT> display(GxEPD2_426_GDEQ0426T82(/*CS=5*/ SS, /*DC=*/ 17, /*RST=*/ 16, /*BUSY=*/ 4)); // GDEQ0426T82 480x800, SSD1677 (P426010-MF1-A)
//GxEPD2_BW<GxEPD2_583, GxEPD2_583::HEIGHT> display(GxEPD2_583(/*CS=5*/ SS, /*DC=*/ 17, /*RST=*/ 16, /*BUSY=*/ 4)); // GDEW0583T7 600x448, UC8159c (IL0371)
//GxEPD2_BW<GxEPD2_583_T8, GxEPD2_583_T8::HEIGHT> display(GxEPD2_583_T8(/*CS=5*/ SS, /*DC=*/ 17, /*RST=*/ 16, /*BUSY=*/ 4)); // GDEW0583T8 648x480, EK79655 (GD7965)
//GxEPD2_BW<GxEPD2_583_GDEQ0583T31, GxEPD2_583_GDEQ0583T31::HEIGHT> display(GxEPD2_583_GDEQ0583T31(/*CS=5*/ SS, /*DC=*/ 17, /*RST=*/ 16, /*BUSY=*/ 4)); // GDEQ0583T31 648x480, UC8179, (P583010-MF1-B)
//GxEPD2_BW<GxEPD2_750, GxEPD2_750::HEIGHT> display(GxEPD2_750(/*CS=5*/ SS, /*DC=*/ 17, /*RST=*/ 16, /*BUSY=*/ 4)); // GDEW075T8 640x384, UC8159c (IL0371)
//GxEPD2_BW<GxEPD2_750_T7, GxEPD2_750_T7::HEIGHT> display(GxEPD2_750_T7(/*CS=5*/ SS, /*DC=*/ 17, /*RST=*/ 16, /*BUSY=*/ 4)); // GDEW075T7 800x480, EK79655 (GD7965)
//GxEPD2_BW<GxEPD2_750_YT7, GxEPD2_750_YT7::HEIGHT> display(GxEPD2_750_YT7(/*CS=5*/ SS, /*DC=*/ 17, /*RST=*/ 16, /*BUSY=*/ 4)); // GDEY075T7 800x480, UC8179 (GD7965)
//GxEPD2_BW < GxEPD2_1160_T91, GxEPD2_1160_T91::HEIGHT / 2> display(GxEPD2_1160_T91(/*CS=5*/ SS, /*DC=*/ 17, /*RST=*/ 16, /*BUSY=*/ 4)); // GDEH116T91 960x640, SSD1677
// 3-color e-papers
//GxEPD2_3C<GxEPD2_154c, GxEPD2_154c::HEIGHT> display(GxEPD2_154c(/*CS=5*/ SS, /*DC=*/ 17, /*RST=*/ 16, /*BUSY=*/ 4)); // GDEW0154Z04 200x200, IL0376F, no longer available
//GxEPD2_3C<GxEPD2_154_Z90c, GxEPD2_154_Z90c::HEIGHT> display(GxEPD2_154_Z90c(/*CS=5*/ SS, /*DC=*/ 17, /*RST=*/ 16, /*BUSY=*/ 4)); // GDEH0154Z90 200x200, SSD1681
//GxEPD2_3C<GxEPD2_213c, GxEPD2_213c::HEIGHT> display(GxEPD2_213c(/*CS=5*/ SS, /*DC=*/ 17, /*RST=*/ 16, /*BUSY=*/ 4)); // GDEW0213Z16 104x212, UC8151 (IL0373)
//GxEPD2_3C<GxEPD2_213_Z19c, GxEPD2_213_Z19c::HEIGHT> display(GxEPD2_213_Z19c(/*CS=5*/ SS, /*DC=*/ 17, /*RST=*/ 16, /*BUSY=*/ 4)); // GDEH0213Z19 104x212, UC8151D
//GxEPD2_3C<GxEPD2_213_Z98c, GxEPD2_213_Z98c::HEIGHT> display(GxEPD2_213_Z98c(/*CS=5*/ SS, /*DC=*/ 17, /*RST=*/ 16, /*BUSY=*/ 4)); // GDEY0213Z98 122x250, SSD1680
//GxEPD2_3C<GxEPD2_266c, GxEPD2_266c::HEIGHT> display(GxEPD2_266c(/*CS=5*/ SS, /*DC=*/ 17, /*RST=*/ 16, /*BUSY=*/ 4)); // GDEY0266Z90 152x296, SSD1680
//GxEPD2_3C<GxEPD2_270c, GxEPD2_270c::HEIGHT> display(GxEPD2_270c(/*CS=5*/ SS, /*DC=*/ 17, /*RST=*/ 16, /*BUSY=*/ 4)); // GDEW027C44 176x264, IL91874
//GxEPD2_3C<GxEPD2_290c, GxEPD2_290c::HEIGHT> display(GxEPD2_290c(/*CS=5*/ SS, /*DC=*/ 17, /*RST=*/ 16, /*BUSY=*/ 4)); // GDEW029Z10 128x296, UC8151 (IL0373)
//GxEPD2_3C<GxEPD2_290_Z13c, GxEPD2_290_Z13c::HEIGHT> display(GxEPD2_290_Z13c(/*CS=5*/ SS, /*DC=*/ 17, /*RST=*/ 16, /*BUSY=*/ 4)); // GDEH029Z13 128x296, UC8151D
//GxEPD2_3C<GxEPD2_290_C90c, GxEPD2_290_C90c::HEIGHT> display(GxEPD2_290_C90c(/*CS=5*/ SS, /*DC=*/ 17, /*RST=*/ 16, /*BUSY=*/ 4)); // GDEM029C90 128x296, SSD1680
//GxEPD2_3C<GxEPD2_420c, GxEPD2_420c::HEIGHT> display(GxEPD2_420c(/*CS=5*/ SS, /*DC=*/ 17, /*RST=*/ 16, /*BUSY=*/ 4)); // GDEW042Z15 400x300, UC8176 (IL0398)
//GxEPD2_3C<GxEPD2_420c_Z21, GxEPD2_420c_Z21::HEIGHT> display(GxEPD2_420c_Z21(/*CS=5*/ SS, /*DC=*/ 17, /*RST=*/ 16, /*BUSY=*/ 4)); // GDEQ042Z21 400x300, UC8276
//GxEPD2_3C<GxEPD2_583c, GxEPD2_583c::HEIGHT> display(GxEPD2_583c(/*CS=5*/ SS, /*DC=*/ 17, /*RST=*/ 16, /*BUSY=*/ 4)); // GDEW0583Z21 600x448, UC8179 (IL0371)
//GxEPD2_3C<GxEPD2_583c_Z83, GxEPD2_583c_Z83::HEIGHT> display(GxEPD2_583c_Z83(/*CS=5*/ SS, /*DC=*/ 17, /*RST=*/ 16, /*BUSY=*/ 4)); // GDEW0583Z83 648x480, GD7965
//GxEPD2_3C<GxEPD2_750c, GxEPD2_750c::HEIGHT> display(GxEPD2_750c(/*CS=5*/ SS, /*DC=*/ 17, /*RST=*/ 16, /*BUSY=*/ 4)); // GDEW075Z09 640x384, UC8179 (IL0371)
//GxEPD2_3C<GxEPD2_750c_Z08, GxEPD2_750c_Z08::HEIGHT> display(GxEPD2_750c_Z08(/*CS=5*/ SS, /*DC=*/ 17, /*RST=*/ 16, /*BUSY=*/ 4)); // GDEW075Z08 800x480, GD7965
//GxEPD2_3C<GxEPD2_750c_Z90, GxEPD2_750c_Z90::HEIGHT / 2> display(GxEPD2_750c_Z90(/*CS=5*/ SS, /*DC=*/ 17, /*RST=*/ 16, /*BUSY=*/ 4)); // GDEH075Z90 880x528, SSD1677
// 4-color e-paper
//GxEPD2_4C<GxEPD2_266c_GDEY0266F51H, GxEPD2_266c_GDEY0266F51H::HEIGHT> display(GxEPD2_266c_GDEY0266F51H(/*CS=5*/ SS, /*DC=*/ 17, /*RST=*/ 16, /*BUSY=*/ 4)); // GDEY0266F51H 184x360, JD79667 (FPC-H006 22.04.02)
//GxEPD2_4C<GxEPD2_290c_GDEY029F51H, GxEPD2_290c_GDEY029F51H::HEIGHT> display(GxEPD2_290c_GDEY029F51H(/*CS=5*/ SS, /*DC=*/ 17, /*RST=*/ 16, /*BUSY=*/ 4)); // GDEY029F51H 168x384, JD79667 (FPC-H004 22.03.24)
//GxEPD2_4C<GxEPD2_300c, GxEPD2_300c::HEIGHT> display(GxEPD2_300c(/*CS=5*/ SS, /*DC=*/ 17, /*RST=*/ 16, /*BUSY=*/ 4)); // Waveshare 3.00" 4-color
//GxEPD2_4C<GxEPD2_420c_GDEY0420F51, GxEPD2_420c_GDEY0420F51::HEIGHT> display(GxEPD2_420c_GDEY0420F51(/*CS=5*/ SS, /*DC=*/ 17, /*RST=*/ 16, /*BUSY=*/ 4)); // GDEY0420F51 400x300, HX8717 (no inking)
//GxEPD2_4C<GxEPD2_437c, GxEPD2_437c::HEIGHT> display(GxEPD2_437c(/*CS=5*/ SS, /*DC=*/ 17, /*RST=*/ 16, /*BUSY=*/ 4)); // Waveshare 4.37" 4-color
// 7-color e-paper
//GxEPD2_3C < GxEPD2_565c, GxEPD2_565c::HEIGHT / 2 > display(GxEPD2_565c(/*CS=5*/ SS, /*DC=*/ 17, /*RST=*/ 16, /*BUSY=*/ 4)); // Waveshare 5.65" 7-color (3C graphics)
//GxEPD2_7C < GxEPD2_565c, GxEPD2_565c::HEIGHT / 2 > display(GxEPD2_565c(/*CS=5*/ SS, /*DC=*/ 17, /*RST=*/ 16, /*BUSY=*/ 4)); // Waveshare 5.65" 7-color
//GxEPD2_7C < GxEPD2_730c_GDEY073D46, GxEPD2_730c_GDEY073D46::HEIGHT / 4 > display(GxEPD2_730c_GDEY073D46(/*CS=5*/ SS, /*DC=*/ 17, /*RST=*/ 16, /*BUSY=*/ 4)); // GDEY073D46 800x480 7-color, (N-FPC-001 2021.11.26)

// grey levels parallel IF e-papers on Waveshare e-Paper IT8951 Driver HAT
// HRDY -> 4, RST -> 16, CS -> SS(5), SCK -> SCK(18), MOSI -> MOSI(23), MISO -> MISO(19), GND -> GND, 5V -> 5V
// note: 5V supply needs to be exact and strong; 5V over diode from USB (e.g. Wemos D1 mini) doesn't work!
//GxEPD2_BW<GxEPD2_it60, GxEPD2_it60::HEIGHT> display(GxEPD2_it60(/*CS=5*/ SS, /*DC=*/ 17, /*RST=*/ 16, /*BUSY=*/ 4));
//GxEPD2_BW < GxEPD2_it60_1448x1072, GxEPD2_it60_1448x1072::HEIGHT / 4 > display(GxEPD2_it60_1448x1072(/*CS=5*/ SS, /*DC=*/ 17, /*RST=*/ 16, /*BUSY=*/ 4));
//GxEPD2_BW < GxEPD2_it78_1872x1404, GxEPD2_it78_1872x1404::HEIGHT / 8 > display(GxEPD2_it78_1872x1404(/*CS=5*/ SS, /*DC=*/ 17, /*RST=*/ 16, /*BUSY=*/ 4));
//GxEPD2_BW < GxEPD2_it103_1872x1404, GxEPD2_it103_1872x1404::HEIGHT / 8 > display(GxEPD2_it103_1872x1404(/*CS=5*/ SS, /*DC=*/ 17, /*RST=*/ 16, /*BUSY=*/ 4));

// Waveshare 12.48 b/w SPI display board and frame or Good Display 12.48 b/w panel GDEW1248T3
// general constructor for use with all parameters, e.g. for Waveshare ESP32 driver board mounted on connection board
//GxEPD2_BW < GxEPD2_1248, GxEPD2_1248::HEIGHT / 4 >
//display(GxEPD2_1248(/*sck=*/ 13, /*miso=*/ 12, /*mosi=*/ 14, /*cs_m1=*/ 23, /*cs_s1=*/ 22, /*cs_m2=*/ 16, /*cs_s2=*/ 19,
//                             /*dc1=*/ 25, /*dc2=*/ 17, /*rst1=*/ 33, /*rst2=*/ 5, /*busy_m1=*/ 32, /*busy_s1=*/ 26, /*busy_m2=*/ 18, /*busy_s2=*/ 4));
// Waveshare 12.48 b/w/r SPI display board and frame or Good Display 12.48 b/w/r panel GDEY1248Z51
// general constructor for use with all parameters, e.g. for Waveshare ESP32 driver board mounted on connection board
//GxEPD2_3C < GxEPD2_1248c, GxEPD2_1248c::HEIGHT / 4 >
//display(GxEPD2_1248c(/*sck=*/ 13, /*miso=*/ 12, /*mosi=*/ 14, /*cs_m1=*/ 23, /*cs_s1=*/ 22, /*cs_m2=*/ 16, /*cs_s2=*/ 19,
//                             /*dc1=*/ 25, /*dc2=*/ 17, /*rst1=*/ 33, /*rst2=*/ 5, /*busy_m1=*/ 32, /*busy_s1=*/ 26, /*busy_m2=*/ 18, /*busy_s2=*/ 4));

// ***** for mapping of Waveshare ESP32 Driver Board *****
// use Board "ESP32 Dev Module" to build with Arduino IDE
// uncomment next line to use HSPI for EPD (and e.g VSPI for SD), e.g. with Waveshare ESP32 Driver Board
//#define USE_HSPI_FOR_EPD
// select one, can use full buffer size (full HEIGHT)
//GxEPD2_BW<GxEPD2_102, GxEPD2_102::HEIGHT> display(GxEPD2_102(/*CS=*/ 15, /*DC=*/ 27, /*RST=*/ 26, /*BUSY=*/ 25)); // GDEW0102T4 80x128, UC8175
//GxEPD2_BW<GxEPD2_150_BN, GxEPD2_150_BN::HEIGHT> display(GxEPD2_150_BN(/*CS=*/ 15, /*DC=*/ 27, /*RST=*/ 26, /*BUSY=*/ 25)); // DEPG0150BN 200x200, SSD1681, TTGO T5 V2.4.1
//GxEPD2_BW<GxEPD2_154, GxEPD2_154::HEIGHT> display(GxEPD2_154(/*CS=*/ 15, /*DC=*/ 27, /*RST=*/ 26, /*BUSY=*/ 25)); // GDEP015OC1 200x200, IL3829, no longer available
//GxEPD2_BW<GxEPD2_154_D67, GxEPD2_154_D67::HEIGHT> display(GxEPD2_154_D67(/*CS=*/ 15, /*DC=*/ 27, /*RST=*/ 26, /*BUSY=*/ 25)); // GDEH0154D67 200x200, SSD1681
//GxEPD2_BW<GxEPD2_154_T8, GxEPD2_154_T8::HEIGHT> display(GxEPD2_154_T8(/*CS=*/ 15, /*DC=*/ 27, /*RST=*/ 26, /*BUSY=*/ 25)); // GDEW0154T8  152x152, UC8151 (IL0373)
//GxEPD2_BW<GxEPD2_154_M09, GxEPD2_154_M09::HEIGHT> display(GxEPD2_154_M09(/*CS=*/ 15, /*DC=*/ 27, /*RST=*/ 26, /*BUSY=*/ 25)); // GDEW0154M09 200x200, JD79653A
//GxEPD2_BW<GxEPD2_154_M10, GxEPD2_154_M10::HEIGHT> display(GxEPD2_154_M10(/*CS=*/ 15, /*DC=*/ 27, /*RST=*/ 26, /*BUSY=*/ 25)); // GDEW0154M10 152x152, UC8151D
//GxEPD2_BW<GxEPD2_154_GDEY0154D67, GxEPD2_154_GDEY0154D67::HEIGHT> display(GxEPD2_154_GDEY0154D67(/*CS=*/ 15, /*DC=*/ 27, /*RST=*/ 26, /*BUSY=*/ 25)); // GDEY0154D67 200x200, SSD1681, (FPC-B001 20.05.21)
//GxEPD2_BW<GxEPD2_213, GxEPD2_213::HEIGHT> display(GxEPD2_213(/*CS=*/ 15, /*DC=*/ 27, /*RST=*/ 26, /*BUSY=*/ 25)); // GDE0213B1 122x250, IL3895, phased out
//GxEPD2_BW<GxEPD2_213_B72, GxEPD2_213_B72::HEIGHT> display(GxEPD2_213_B72(/*CS=*/ 15, /*DC=*/ 27, /*RST=*/ 26, /*BUSY=*/ 25)); // GDEH0213B72 122x250, SSD1675A (IL3897)
//GxEPD2_BW<GxEPD2_213_B73, GxEPD2_213_B73::HEIGHT> display(GxEPD2_213_B73(/*CS=*/ 15, /*DC=*/ 27, /*RST=*/ 26, /*BUSY=*/ 25)); // GDEH0213B73 122x250, SSD1675B
//GxEPD2_BW<GxEPD2_213_B74, GxEPD2_213_B74::HEIGHT> display(GxEPD2_213_B74(/*CS=*/ 15, /*DC=*/ 27, /*RST=*/ 26, /*BUSY=*/ 25)); // GDEM0213B74 122x250, SSD1680
//GxEPD2_BW<GxEPD2_213_flex, GxEPD2_213_flex::HEIGHT> display(GxEPD2_213_flex(/*CS=*/ 15, /*DC=*/ 27, /*RST=*/ 26, /*BUSY=*/ 25)); // GDEW0213I5F 104x212, UC8151 (IL0373)
//GxEPD2_BW<GxEPD2_213_M21, GxEPD2_213_M21::HEIGHT> display(GxEPD2_213_M21(/*CS=*/ 15, /*DC=*/ 27, /*RST=*/ 26, /*BUSY=*/ 25)); // GDEW0213M21 104x212, UC8151 (IL0373)
//GxEPD2_BW<GxEPD2_213_T5D, GxEPD2_213_T5D::HEIGHT> display(GxEPD2_213_T5D(/*CS=*/ 15, /*DC=*/ 27, /*RST=*/ 26, /*BUSY=*/ 25)); // GDEW0213T5D 104x212, UC8151D
//GxEPD2_BW<GxEPD2_213_BN, GxEPD2_213_BN::HEIGHT> display(GxEPD2_213_BN(/*CS=*/ 15, /*DC=*/ 27, /*RST=*/ 26, /*BUSY=*/ 25)); // DEPG0213BN 122x250, SSD1680, TTGO T5 V2.4.1, V2.3.1
//GxEPD2_BW<GxEPD2_213_GDEY0213B74, GxEPD2_213_GDEY0213B74::HEIGHT> display(GxEPD2_213_GDEY0213B74(/*CS=*/ 15, /*DC=*/ 27, /*RST=*/ 26, /*BUSY=*/ 25)); // GDEY0213B74 122x250, SSD1680, (FPC-A002 20.04.08)
//GxEPD2_BW<GxEPD2_260, GxEPD2_260::HEIGHT> display(GxEPD2_260(/*CS=*/ 15, /*DC=*/ 27, /*RST=*/ 26, /*BUSY=*/ 25)); // GDEW026T0 152x296, UC8151 (IL0373)
//GxEPD2_BW<GxEPD2_260_M01, GxEPD2_260_M01::HEIGHT> display(GxEPD2_260_M01(/*CS=*/ 15, /*DC=*/ 27, /*RST=*/ 26, /*BUSY=*/ 25)); // GDEW026M01 152x296, UC8151 (IL0373)
//GxEPD2_BW<GxEPD2_266_BN, GxEPD2_266_BN::HEIGHT> display(GxEPD2_266_BN(/*CS=*/ 15, /*DC=*/ 27, /*RST=*/ 26, /*BUSY=*/ 25)); // DEPG0266BN 152x296, SSD1680, TTGO T5 V2.4.1
//GxEPD2_BW<GxEPD2_270, GxEPD2_270::HEIGHT> display(GxEPD2_270(/*CS=*/ 15, /*DC=*/ 27, /*RST=*/ 26, /*BUSY=*/ 25)); // GDEW027W3 176x264, EK79652 (IL91874)
//GxEPD2_BW<GxEPD2_270_GDEY027T91, GxEPD2_270_GDEY027T91::HEIGHT> display(GxEPD2_270_GDEY027T91(/*CS=*/ 15, /*DC=*/ 27, /*RST=*/ 26, /*BUSY=*/ 25)); // GDEY027T91 176x264, SSD1680
//GxEPD2_BW<GxEPD2_290, GxEPD2_290::HEIGHT> display(GxEPD2_290(/*CS=*/ 15, /*DC=*/ 27, /*RST=*/ 26, /*BUSY=*/ 25)); // GDEH029A1 128x296, SSD1608 (IL3820)
//GxEPD2_BW<GxEPD2_290_T5, GxEPD2_290_T5::HEIGHT> display(GxEPD2_290_T5(/*CS=*/ 15, /*DC=*/ 27, /*RST=*/ 26, /*BUSY=*/ 25)); // GDEW029T5 128x296, UC8151 (IL0373)
//GxEPD2_BW<GxEPD2_290_T5D, GxEPD2_290_T5D::HEIGHT> display(GxEPD2_290_T5D(/*CS=*/ 15, /*DC=*/ 27, /*RST=*/ 26, /*BUSY=*/ 25)); // GDEW029T5D 128x296, UC8151D
//GxEPD2_BW<GxEPD2_290_I6FD, GxEPD2_290_I6FD::HEIGHT> display(GxEPD2_290_I6FD(/*CS=*/ 15, /*DC=*/ 27, /*RST=*/ 26, /*BUSY=*/ 25)); // GDEW029I6FD 128x296, UC8151D
//GxEPD2_BW<GxEPD2_290_T94, GxEPD2_290_T94::HEIGHT> display(GxEPD2_290_T94(/*CS=*/ 15, /*DC=*/ 27, /*RST=*/ 26, /*BUSY=*/ 25)); // GDEM029T94 128x296, SSD1680
//GxEPD2_BW<GxEPD2_290_T94_V2, GxEPD2_290_T94_V2::HEIGHT> display(GxEPD2_290_T94_V2(/*CS=*/ 15, /*DC=*/ 27, /*RST=*/ 26, /*BUSY=*/ 25)); // GDEM029T94 128x296, SSD1680, Waveshare 2.9" V2 variant
//GxEPD2_BW<GxEPD2_290_BS, GxEPD2_290_BS::HEIGHT> display(GxEPD2_290_BS(/*CS=*/ 15, /*DC=*/ 27, /*RST=*/ 26, /*BUSY=*/ 25)); // DEPG0290BS 128x296, SSD1680
//GxEPD2_BW<GxEPD2_290_M06, GxEPD2_290_M06::HEIGHT> display(GxEPD2_290_M06(/*CS=*/ 15, /*DC=*/ 27, /*RST=*/ 26, /*BUSY=*/ 25)); // GDEW029M06  128x296, UC8151D
//GxEPD2_BW<GxEPD2_290_GDEY029T94, GxEPD2_290_GDEY029T94::HEIGHT> display(GxEPD2_290_GDEY029T94(/*CS=*/ 15, /*DC=*/ 27, /*RST=*/ 26, /*BUSY=*/ 25)); // GDEY029T94  128x296, SSD1680, (FPC-A005 20.06.15)
//GxEPD2_BW<GxEPD2_371, GxEPD2_371::HEIGHT> display(GxEPD2_371(/*CS=*/ 15, /*DC=*/ 27, /*RST=*/ 26, /*BUSY=*/ 25)); // GDEW0371W7 240x416, UC8171 (IL0324)
//GxEPD2_BW<GxEPD2_370_TC1, GxEPD2_370_TC1::HEIGHT> display(GxEPD2_370_TC1(/*CS=*/ 15, /*DC=*/ 27, /*RST=*/ 26, /*BUSY=*/ 25)); // ED037TC1 280x480, SSD1677, Waveshare 3.7"
//GxEPD2_BW<GxEPD2_420, GxEPD2_420::HEIGHT> display(GxEPD2_420(/*CS=*/ 15, /*DC=*/ 27, /*RST=*/ 26, /*BUSY=*/ 25)); // GDEW042T2 400x300, UC8176 (IL0398)
//GxEPD2_BW<GxEPD2_420_M01, GxEPD2_420_M01::HEIGHT> display(GxEPD2_420_M01(/*CS=*/ 15, /*DC=*/ 27, /*RST=*/ 26, /*BUSY=*/ 25)); // GDEW042M01 400x300, UC8176 (IL0398)
//GxEPD2_BW<GxEPD2_420_GDEY042T81, GxEPD2_420_GDEY042T81::HEIGHT> display(GxEPD2_420_GDEY042T81(/*CS=*/ 15, /*DC=*/ 27, /*RST=*/ 26, /*BUSY=*/ 25)); GDEY042T81, 400x300, SSD1683 (no inking)
//GxEPD2_BW<GxEPD2_426_GDEQ0426T82, GxEPD2_426_GDEQ0426T82::HEIGHT> display(GxEPD2_426_GDEQ0426T82(/*CS=*/ 15, /*DC=*/ 27, /*RST=*/ 26, /*BUSY=*/ 25)); // GDEQ0426T82 480x800, SSD1677 (P426010-MF1-A)
//GxEPD2_BW<GxEPD2_583, GxEPD2_583::HEIGHT> display(GxEPD2_583(/*CS=*/ 15, /*DC=*/ 27, /*RST=*/ 26, /*BUSY=*/ 25)); // GDEW0583T7 600x448, UC8159c (IL0371)
//GxEPD2_BW<GxEPD2_583_T8, GxEPD2_583_T8::HEIGHT> display(GxEPD2_583_T8(/*CS=*/ 15, /*DC=*/ 27, /*RST=*/ 26, /*BUSY=*/ 25)); // GDEW0583T8 648x480, EK79655 (GD7965)
//GxEPD2_BW<GxEPD2_583_GDEQ0583T31, GxEPD2_583_GDEQ0583T31::HEIGHT> display(GxEPD2_583_GDEQ0583T31(/*CS=*/ 15, /*DC=*/ 27, /*RST=*/ 26, /*BUSY=*/ 25)); // GDEQ0583T31 648x480, UC8179, (P583010-MF1-B)
//GxEPD2_BW<GxEPD2_750, GxEPD2_750::HEIGHT> display(GxEPD2_750(/*CS=*/ 15, /*DC=*/ 27, /*RST=*/ 26, /*BUSY=*/ 25)); // GDEW075T8 640x384, UC8159c (IL0371)
//GxEPD2_BW<GxEPD2_750_T7, GxEPD2_750_T7::HEIGHT> display(GxEPD2_750_T7(/*CS=*/ 15, /*DC=*/ 27, /*RST=*/ 26, /*BUSY=*/ 25)); // GDEW075T7 800x480, EK79655 (GD7965)
//GxEPD2_BW<GxEPD2_750_YT7, GxEPD2_750_YT7::HEIGHT> display(GxEPD2_750_YT7(/*CS=*/ 15, /*DC=*/ 27, /*RST=*/ 26, /*BUSY=*/ 25)); // GDEY075T7 800x480, UC8179 (GD7965)
//GxEPD2_BW < GxEPD2_1160_T91, GxEPD2_1160_T91::HEIGHT / 2> display(GxEPD2_1160_T91(/*CS=*/ 15, /*DC=*/ 27, /*RST=*/ 26, /*BUSY=*/ 25)); // GDEH116T91 960x640, SSD1677
// 3-color e-papers
//GxEPD2_3C<GxEPD2_154c, GxEPD2_154c::HEIGHT> display(GxEPD2_154c(/*CS=*/ 15, /*DC=*/ 27, /*RST=*/ 26, /*BUSY=*/ 25)); // GDEW0154Z04 200x200, IL0376F, no longer available
//GxEPD2_3C<GxEPD2_154_Z90c, GxEPD2_154_Z90c::HEIGHT> display(GxEPD2_154_Z90c(/*CS=*/ 15, /*DC=*/ 27, /*RST=*/ 26, /*BUSY=*/ 25)); // GDEH0154Z90 200x200, SSD1681
//GxEPD2_3C<GxEPD2_213c, GxEPD2_213c::HEIGHT> display(GxEPD2_213c(/*CS=*/ 15, /*DC=*/ 27, /*RST=*/ 26, /*BUSY=*/ 25)); // GDEW0213Z16 104x212, UC8151 (IL0373)
//GxEPD2_3C<GxEPD2_213_Z19c, GxEPD2_213_Z19c::HEIGHT> display(GxEPD2_213_Z19c(/*CS=*/ 15, /*DC=*/ 27, /*RST=*/ 26, /*BUSY=*/ 25)); // GDEH0213Z19 104x212, UC8151D
//GxEPD2_3C<GxEPD2_213_Z98c, GxEPD2_213_Z98c::HEIGHT> display(GxEPD2_213_Z98c(/*CS=*/ 15, /*DC=*/ 27, /*RST=*/ 26, /*BUSY=*/ 25)); // GDEY0213Z98 122x250, SSD1680
//GxEPD2_3C<GxEPD2_266c, GxEPD2_266c::HEIGHT> display(GxEPD2_266c(/*CS=*/ 15, /*DC=*/ 27, /*RST=*/ 26, /*BUSY=*/ 25)); // GDEY0266Z90 152x296, SSD1680
//GxEPD2_3C<GxEPD2_270c, GxEPD2_270c::HEIGHT> display(GxEPD2_270c(/*CS=*/ 15, /*DC=*/ 27, /*RST=*/ 26, /*BUSY=*/ 25)); // GDEW027C44 176x264, IL91874
//GxEPD2_3C<GxEPD2_290c, GxEPD2_290c::HEIGHT> display(GxEPD2_290c(/*CS=*/ 15, /*DC=*/ 27, /*RST=*/ 26, /*BUSY=*/ 25)); // GDEW029Z10 128x296, UC8151 (IL0373)
//GxEPD2_3C<GxEPD2_290_Z13c, GxEPD2_290_Z13c::HEIGHT> display(GxEPD2_290_Z13c(/*CS=*/ 15, /*DC=*/ 27, /*RST=*/ 26, /*BUSY=*/ 25)); // GDEH029Z13 128x296, UC8151D
//GxEPD2_3C<GxEPD2_290_C90c, GxEPD2_290_C90c::HEIGHT> display(GxEPD2_290_C90c(/*CS=*/ 15, /*DC=*/ 27, /*RST=*/ 26, /*BUSY=*/ 25)); // GDEM029C90 128x296, SSD1680
//GxEPD2_3C<GxEPD2_420c, GxEPD2_420c::HEIGHT> display(GxEPD2_420c(/*CS=*/ 15, /*DC=*/ 27, /*RST=*/ 26, /*BUSY=*/ 25)); // GDEW042Z15 400x300, UC8176 (IL0398)
//GxEPD2_3C<GxEPD2_420c_Z21, GxEPD2_420c_Z21::HEIGHT> display(GxEPD2_420c_Z21(/*CS=*/ 15, /*DC=*/ 27, /*RST=*/ 26, /*BUSY=*/ 25)); // GDEQ042Z21 400x300, UC8276
//GxEPD2_3C<GxEPD2_583c, GxEPD2_583c::HEIGHT> display(GxEPD2_583c(/*CS=*/ 15, /*DC=*/ 27, /*RST=*/ 26, /*BUSY=*/ 25)); // GDEW0583Z21 600x448, UC8179 (IL0371)
//GxEPD2_3C<GxEPD2_583c_Z83, GxEPD2_583c_Z83::HEIGHT> display(GxEPD2_583c_Z83(/*CS=*/ 15, /*DC=*/ 27, /*RST=*/ 26, /*BUSY=*/ 25)); // GDEW0583Z83 648x480, GD7965
//GxEPD2_3C<GxEPD2_750c, GxEPD2_750c::HEIGHT> display(GxEPD2_750c(/*CS=*/ 15, /*DC=*/ 27, /*RST=*/ 26, /*BUSY=*/ 25)); // GDEW075Z09 640x384, UC8179 (IL0371)
//GxEPD2_3C<GxEPD2_750c_Z08, GxEPD2_750c_Z08::HEIGHT> display(GxEPD2_750c_Z08(/*CS=*/ 15, /*DC=*/ 27, /*RST=*/ 26, /*BUSY=*/ 25)); // GDEW075Z08 800x480, GD7965
//GxEPD2_3C<GxEPD2_750c_Z90, GxEPD2_750c_Z90::HEIGHT / 2> display(GxEPD2_750c_Z90(/*CS=*/ 15, /*DC=*/ 27, /*RST=*/ 26, /*BUSY=*/ 25)); // GDEH075Z90 880x528, SSD1677
// 4-color e-paper
//GxEPD2_4C<GxEPD2_266c_GDEY0266F51H, GxEPD2_266c_GDEY0266F51H::HEIGHT> display(GxEPD2_266c_GDEY0266F51H(/*CS=*/ 15, /*DC=*/ 27, /*RST=*/ 26, /*BUSY=*/ 25)); // GDEY0266F51H 184x360, JD79667 (FPC-H006 22.04.02)
//GxEPD2_4C<GxEPD2_290c_GDEY029F51H, GxEPD2_290c_GDEY029F51H::HEIGHT> display(GxEPD2_290c_GDEY029F51H(/*CS=*/ 15, /*DC=*/ 27, /*RST=*/ 26, /*BUSY=*/ 25)); // GDEY029F51H 168x384, JD79667 (FPC-H004 22.03.24)
//GxEPD2_4C<GxEPD2_300c, GxEPD2_300c::HEIGHT> display(GxEPD2_300c(/*CS=*/ 15, /*DC=*/ 27, /*RST=*/ 26, /*BUSY=*/ 25)); // Waveshare 3.00" 4-color
//GxEPD2_4C<GxEPD2_420c_GDEY0420F51, GxEPD2_420c_GDEY0420F51::HEIGHT> display(GxEPD2_420c_GDEY0420F51(/*CS=*/ 15, /*DC=*/ 27, /*RST=*/ 26, /*BUSY=*/ 25)); // GDEY0420F51 400x300, HX8717 (no inking)
//GxEPD2_4C < GxEPD2_437c, GxEPD2_437c::HEIGHT / 4 > display(GxEPD2_437c(/*CS=*/ 15, /*DC=*/ 27, /*RST=*/ 26, /*BUSY=*/ 25)); // Waveshare 4.37" 4-color
// 7-color e-paper
//GxEPD2_3C < GxEPD2_565c, GxEPD2_565c::HEIGHT / 2 > display(GxEPD2_565c(/*CS=*/ 15, /*DC=*/ 27, /*RST=*/ 26, /*BUSY=*/ 25)); // Waveshare 5.65" 7-color (3C graphics)
//GxEPD2_7C < GxEPD2_565c, GxEPD2_565c::HEIGHT / 2 > display(GxEPD2_565c(/*CS=*/ 15, /*DC=*/ 27, /*RST=*/ 26, /*BUSY=*/ 25)); // Waveshare 5.65" 7-color
//GxEPD2_7C < GxEPD2_730c_GDEY073D46, GxEPD2_730c_GDEY073D46::HEIGHT / 4 > display(GxEPD2_730c_GDEY073D46(/*CS=*/ 15, /*DC=*/ 27, /*RST=*/ 26, /*BUSY=*/ 25)); // GDEY073D46 800x480 7-color, (N-FPC-001 2021.11.26)
#endif

// can't use package "STMF1 Boards (STM32Duino.com)" (Roger Clark) anymore with Adafruit_GFX, use "STM32 Boards (selected from submenu)" (STMicroelectronics)
#if defined(ARDUINO_ARCH_STM32)
#define MAX_DISPLAY_BUFFER_SIZE 15000ul // ~15k is a good compromise
#define MAX_HEIGHT(EPD) (EPD::HEIGHT <= MAX_DISPLAY_BUFFER_SIZE / (EPD::WIDTH / 8) ? EPD::HEIGHT : MAX_DISPLAY_BUFFER_SIZE / (EPD::WIDTH / 8))
// select one and adapt to your mapping
//GxEPD2_BW<GxEPD2_102, MAX_HEIGHT(GxEPD2_102)> display(GxEPD2_102(/*CS=PA4*/ SS, /*DC=*/ PA3, /*RST=*/ PA2, /*BUSY=*/ PA1)); // GDEW0102T4 80x128, UC8175
//GxEPD2_BW<GxEPD2_150_BN, GxEPD2_150_BN::HEIGHT> display(GxEPD2_150_BN(/*CS=PA4*/ SS, /*DC=*/ PA3, /*RST=*/ PA2, /*BUSY=*/ PA1)); // DEPG0150BN 200x200, SSD1681, TTGO T5 V2.4.1
//GxEPD2_BW<GxEPD2_154, MAX_HEIGHT(GxEPD2_154)> display(GxEPD2_154(/*CS=PA4*/ SS, /*DC=*/ PA3, /*RST=*/ PA2, /*BUSY=*/ PA1)); // GDEP015OC1 200x200, IL3829, no longer available
//GxEPD2_BW<GxEPD2_154_D67, MAX_HEIGHT(GxEPD2_154_D67)> display(GxEPD2_154_D67(/*CS=PA4*/ SS, /*DC=*/ PA3, /*RST=*/ PA2, /*BUSY=*/ PA1)); // GDEH0154D67 200x200, SSD1681
//GxEPD2_BW<GxEPD2_154_T8, MAX_HEIGHT(GxEPD2_154_T8)> display(GxEPD2_154_T8(/*CS=PA4*/ SS, /*DC=*/ PA3, /*RST=*/ PA2, /*BUSY=*/ PA1)); // GDEW0154T8  152x152, UC8151 (IL0373)
//GxEPD2_BW<GxEPD2_154_M09, MAX_HEIGHT(GxEPD2_154_M09)> display(GxEPD2_154_M09(/*CS=PA4*/ SS, /*DC=*/ PA3, /*RST=*/ PA2, /*BUSY=*/ PA1)); // GDEW0154M09 200x200, JD79653A
//GxEPD2_BW<GxEPD2_154_M10, MAX_HEIGHT(GxEPD2_154_M10)> display(GxEPD2_154_M10(/*CS=PA4*/ SS, /*DC=*/ PA3, /*RST=*/ PA2, /*BUSY=*/ PA1)); // GDEW0154M10 152x152, UC8151D
//GxEPD2_BW<GxEPD2_154_GDEY0154D67, MAX_HEIGHT(GxEPD2_154_GDEY0154D67)> display(GxEPD2_154_GDEY0154D67(/*CS=PA4*/ SS, /*DC=*/ PA3, /*RST=*/ PA2, /*BUSY=*/ PA1)); // GDEY0154D67 200x200, SSD1681, (FPC-B001 20.05.21)
//GxEPD2_BW<GxEPD2_213, MAX_HEIGHT(GxEPD2_213)> display(GxEPD2_213(/*CS=PA4*/ SS, /*DC=*/ PA3, /*RST=*/ PA2, /*BUSY=*/ PA1)); // GDE0213B1 122x250, IL3895, phased out
//GxEPD2_BW<GxEPD2_213_B72, MAX_HEIGHT(GxEPD2_213_B72)> display(GxEPD2_213_B72(/*CS=PA4*/ SS, /*DC=*/ PA3, /*RST=*/ PA2, /*BUSY=*/ PA1)); // GDEH0213B72 122x250, SSD1675A (IL3897)
//GxEPD2_BW<GxEPD2_213_B73, MAX_HEIGHT(GxEPD2_213_B73)> display(GxEPD2_213_B73(/*CS=PA4*/ SS, /*DC=*/ PA3, /*RST=*/ PA2, /*BUSY=*/ PA1)); // GDEH0213B73 122x250, SSD1675B
//GxEPD2_BW<GxEPD2_213_B74, MAX_HEIGHT(GxEPD2_213_B74)> display(GxEPD2_213_B74(/*CS=PA4*/ SS, /*DC=*/ PA3, /*RST=*/ PA2, /*BUSY=*/ PA1)); // GDEM0213B74 122x250, SSD1680
//GxEPD2_BW<GxEPD2_213_flex, MAX_HEIGHT(GxEPD2_213_flex)> display(GxEPD2_213_flex(/*CS=PA4*/ SS, /*DC=*/ PA3, /*RST=*/ PA2, /*BUSY=*/ PA1)); // GDEW0213I5F 104x212, UC8151 (IL0373)
//GxEPD2_BW<GxEPD2_213_M21, MAX_HEIGHT(GxEPD2_213_M21)> display(GxEPD2_213_M21(/*CS=PA4*/ SS, /*DC=*/ PA3, /*RST=*/ PA2, /*BUSY=*/ PA1)); // GDEW0213M21 104x212, UC8151 (IL0373)
//GxEPD2_BW<GxEPD2_213_T5D, MAX_HEIGHT(GxEPD2_213_T5D)> display(GxEPD2_213_T5D(/*CS=PA4*/ SS, /*DC=*/ PA3, /*RST=*/ PA2, /*BUSY=*/ PA1)); // GDEW0213T5D 104x212, UC8151D
//GxEPD2_BW<GxEPD2_213_BN, MAX_HEIGHT(GxEPD2_213_BN)> display(GxEPD2_213_BN(/*CS=PA4*/ SS, /*DC=*/ PA3, /*RST=*/ PA2, /*BUSY=*/ PA1)); // DEPG0213BN 122x250, SSD1680, TTGO T5 V2.4.1, V2.3.1
//GxEPD2_BW<GxEPD2_213_GDEY0213B74, MAX_HEIGHT(GxEPD2_213_GDEY0213B74)> display(GxEPD2_213_GDEY0213B74(/*CS=PA4*/ SS, /*DC=*/ PA3, /*RST=*/ PA2, /*BUSY=*/ PA1)); // GDEY0213B74 122x250, SSD1680, (FPC-A002 20.04.08)
//GxEPD2_BW<GxEPD2_260, MAX_HEIGHT(GxEPD2_260)> display(GxEPD2_260(/*CS=PA4*/ SS, /*DC=*/ PA3, /*RST=*/ PA2, /*BUSY=*/ PA1)); // GDEW026T0 152x296, UC8151 (IL0373)
//GxEPD2_BW<GxEPD2_260_M01, MAX_HEIGHT(GxEPD2_260_M01)> display(GxEPD2_260_M01(/*CS=PA4*/ SS, /*DC=*/ PA3, /*RST=*/ PA2, /*BUSY=*/ PA1)); // GDEW026M01 152x296, UC8151 (IL0373)
//GxEPD2_BW<GxEPD2_266_BN, MAX_HEIGHT(GxEPD2_266_BN)> display(GxEPD2_266_BN(/*CS=PA4*/ SS, /*DC=*/ PA3, /*RST=*/ PA2, /*BUSY=*/ PA1)); // DEPG0266BN 152x296, SSD1680, TTGO T5 V2.66 / T92_V1.0
//GxEPD2_BW<GxEPD2_270, MAX_HEIGHT(GxEPD2_270)> display(GxEPD2_270(/*CS=PA4*/ SS, /*DC=*/ PA3, /*RST=*/ PA2, /*BUSY=*/ PA1)); // GDEW027W3 176x264, EK79652 (IL91874)
//GxEPD2_BW<GxEPD2_270_GDEY027T91, MAX_HEIGHT(GxEPD2_270_GDEY027T91)> display(GxEPD2_270_GDEY027T91(/*CS=PA4*/ SS, /*DC=*/ PA3, /*RST=*/ PA2, /*BUSY=*/ PA1)); // GDEY027T91 176x264, SSD1680
//GxEPD2_BW<GxEPD2_290, MAX_HEIGHT(GxEPD2_290)> display(GxEPD2_290(/*CS=PA4*/ SS, /*DC=*/ PA3, /*RST=*/ PA2, /*BUSY=*/ PA1)); // GDEH029A1 128x296, SSD1608 (IL3820)
//GxEPD2_BW<GxEPD2_290_T5, MAX_HEIGHT(GxEPD2_290_T5)> display(GxEPD2_290_T5(/*CS=PA4*/ SS, /*DC=*/ PA3, /*RST=*/ PA2, /*BUSY=*/ PA1)); // GDEW029T5 128x296, UC8151 (IL0373)
//GxEPD2_BW<GxEPD2_290_T5D, MAX_HEIGHT(GxEPD2_290_T5D)> display(GxEPD2_290_T5D(/*CS=PA4*/ SS, /*DC=*/ PA3, /*RST=*/ PA2, /*BUSY=*/ PA1)); // GDEW029T5D 128x296, UC8151D
//GxEPD2_BW<GxEPD2_290_I6FD, MAX_HEIGHT(GxEPD2_290_I6FD)> display(GxEPD2_290_I6FD(/*CS=PA4*/ SS, /*DC=*/ PA3, /*RST=*/ PA2, /*BUSY=*/ PA1)); // GDEW029I6FD 128x296, UC8151D
//GxEPD2_BW<GxEPD2_290_T94, MAX_HEIGHT(GxEPD2_290_T94)> display(GxEPD2_290_T94(/*CS=PA4*/ SS, /*DC=*/ PA3, /*RST=*/ PA2, /*BUSY=*/ PA1)); // GDEM029T94 128x296, SSD1680
//GxEPD2_BW<GxEPD2_290_T94_V2, MAX_HEIGHT(GxEPD2_290_T94_V2)> display(GxEPD2_290_T94_V2(/*CS=PA4*/ SS, /*DC=*/ PA3, /*RST=*/ PA2, /*BUSY=*/ PA1)); // GDEM029T94 128x296, SSD1680, Waveshare 2.9" V2 variant
//GxEPD2_BW<GxEPD2_290_BS, MAX_HEIGHT(GxEPD2_290_BS)> display(GxEPD2_290_BS(/*CS=PA4*/ SS, /*DC=*/ PA3, /*RST=*/ PA2, /*BUSY=*/ PA1)); // DEPG0290BS 128x296, SSD1680
//GxEPD2_BW<GxEPD2_290_M06, MAX_HEIGHT(GxEPD2_290_M06)> display(GxEPD2_290_M06(/*CS=PA4*/ SS, /*DC=*/ PA3, /*RST=*/ PA2, /*BUSY=*/ PA1)); // GDEW029M06  128x296, UC8151D
//GxEPD2_BW<GxEPD2_290_GDEY029T94, MAX_HEIGHT(GxEPD2_290_GDEY029T94)> display(GxEPD2_290_GDEY029T94(/*CS=PA4*/ SS, /*DC=*/ PA3, /*RST=*/ PA2, /*BUSY=*/ PA1)); // GDEY029T94  128x296, SSD1680, (FPC-A005 20.06.15)
//GxEPD2_BW<GxEPD2_371, MAX_HEIGHT(GxEPD2_371)> display(GxEPD2_371(/*CS=PA4*/ SS, /*DC=*/ PA3, /*RST=*/ PA2, /*BUSY=*/ PA1)); // GDEW0371W7 240x416, UC8171 (IL0324)
//GxEPD2_BW<GxEPD2_370_TC1, MAX_HEIGHT(GxEPD2_370_TC1)> display(GxEPD2_370_TC1(/*CS=PA4*/ SS, /*DC=*/ PA3, /*RST=*/ PA2, /*BUSY=*/ PA1)); // ED037TC1 280x480, SSD1677, Waveshare 3.7"
//GxEPD2_BW<GxEPD2_420, MAX_HEIGHT(GxEPD2_420)> display(GxEPD2_420(/*CS=PA4*/ SS, /*DC=*/ PA3, /*RST=*/ PA2, /*BUSY=*/ PA1)); // GDEW042T2 400x300, UC8176 (IL0398)
//GxEPD2_BW<GxEPD2_420_M01, MAX_HEIGHT(GxEPD2_420_M01)> display(GxEPD2_420_M01(/*CS=PA4*/ SS, /*DC=*/ PA3, /*RST=*/ PA2, /*BUSY=*/ PA1)); // GDEW042M01 400x300, UC8176 (IL0398)
//GxEPD2_BW<GxEPD2_420_GDEY042T81, MAX_HEIGHT(GxEPD2_420_GDEY042T81)> display(GxEPD2_420_GDEY042T81(/*CS=PA4*/ SS, /*DC=*/ PA3, /*RST=*/ PA2, /*BUSY=*/ PA1)); GDEY042T81, 400x300, SSD1683 (no inking)
//GxEPD2_BW<GxEPD2_426_GDEQ0426T82, MAX_HEIGHT(GxEPD2_426_GDEQ0426T82)> display(GxEPD2_426_GDEQ0426T82(/*CS=PA4*/ SS, /*DC=*/ PA3, /*RST=*/ PA2, /*BUSY=*/ PA1)); // GDEQ0426T82 480x800, SSD1677 (P426010-MF1-A)
//GxEPD2_BW<GxEPD2_583, MAX_HEIGHT(GxEPD2_583)> display(GxEPD2_583(/*CS=PA4*/ SS, /*DC=*/ PA3, /*RST=*/ PA2, /*BUSY=*/ PA1)); // GDEW0583T7 600x448, UC8159c (IL0371)
//GxEPD2_BW <GxEPD2_583_T8,  MAX_HEIGHT(GxEPD2_583_T8)> display(GxEPD2_583_T8(/*CS=PA4*/ SS, /*DC=*/ PA3, /*RST=*/ PA2, /*BUSY=*/ PA1)); // GDEW0583T8 648x480, EK79655 (GD7965)
//GxEPD2_BW<GxEPD2_583_GDEQ0583T31, MAX_HEIGHT(GxEPD2_583_GDEQ0583T31)> display(GxEPD2_583_GDEQ0583T31(/*CS=PA4*/ SS, /*DC=*/ PA3, /*RST=*/ PA2, /*BUSY=*/ PA1)); // GDEQ0583T31 648x480, UC8179, (P583010-MF1-B)
//GxEPD2_BW<GxEPD2_750, MAX_HEIGHT(GxEPD2_750)> display(GxEPD2_750(/*CS=PA4*/ SS, /*DC=*/ PA3, /*RST=*/ PA2, /*BUSY=*/ PA1)); // GDEW075T8 640x384, UC8159c (IL0371)
//GxEPD2_BW<GxEPD2_750_T7, MAX_HEIGHT(GxEPD2_750_T7)> display(GxEPD2_750_T7(/*CS=PA4*/ SS, /*DC=*/ PA3, /*RST=*/ PA2, /*BUSY=*/ PA1)); // GDEW075T7 800x480, EK79655 (GD7965)
//GxEPD2_BW<GxEPD2_750_YT7, MAX_HEIGHT(GxEPD2_750_YT7)> display(GxEPD2_750_YT7(/*CS=PA4*/ SS, /*DC=*/ PA3, /*RST=*/ PA2, /*BUSY=*/ PA1)); // GDEY075T7 800x480, UC8179 (GD7965)
//GxEPD2_BW < GxEPD2_1160_T91, MAX_HEIGHT(GxEPD2_1160_T91)> display(GxEPD2_1160_T91(/*CS=PA4*/ SS, /*DC=*/ PA3, /*RST=*/ PA2, /*BUSY=*/ PA1)); // GDEH116T91 960x640, SSD1677
// 3-color e-papers
#define MAX_HEIGHT_3C(EPD) (EPD::HEIGHT <= (MAX_DISPLAY_BUFFER_SIZE / 2) / (EPD::WIDTH / 8) ? EPD::HEIGHT : (MAX_DISPLAY_BUFFER_SIZE / 2) / (EPD::WIDTH / 8))
//GxEPD2_3C<GxEPD2_154c, MAX_HEIGHT_3C(GxEPD2_154c)> display(GxEPD2_154c(/*CS=PA4*/ SS, /*DC=*/ PA3, /*RST=*/ PA2, /*BUSY=*/ PA1)); // GDEW0154Z04 200x200, IL0376F, no longer available
//GxEPD2_3C<GxEPD2_154_Z90c, MAX_HEIGHT_3C(GxEPD2_154_Z90c)> display(GxEPD2_154_Z90c(/*CS=PA4*/ SS, /*DC=*/ PA3, /*RST=*/ PA2, /*BUSY=*/ PA1)); // GDEH0154Z90 200x200, SSD1681
//GxEPD2_3C<GxEPD2_213c, MAX_HEIGHT_3C(GxEPD2_213c)> display(GxEPD2_213c(/*CS=PA4*/ SS, /*DC=*/ PA3, /*RST=*/ PA2, /*BUSY=*/ PA1)); // GDEW0213Z16 104x212, UC8151 (IL0373)
//GxEPD2_3C<GxEPD2_213_Z19c, MAX_HEIGHT_3C(GxEPD2_213_Z19c)> display(GxEPD2_213_Z19c(/*CS=PA4*/ SS, /*DC=*/ PA3, /*RST=*/ PA2, /*BUSY=*/ PA1)); // GDEH0213Z19 104x212, UC8151D
//GxEPD2_3C<GxEPD2_213_Z98c, MAX_HEIGHT_3C(GxEPD2_213_Z98c)> display(GxEPD2_213_Z98c(/*CS=PA4*/ SS, /*DC=*/ PA3, /*RST=*/ PA2, /*BUSY=*/ PA1)); // GDEY0213Z98 122x250, SSD1680
//GxEPD2_3C<GxEPD2_266c, MAX_HEIGHT_3C(GxEPD2_266c)> display(GxEPD2_266c(/*CS=PA4*/ SS, /*DC=*/ PA3, /*RST=*/ PA2, /*BUSY=*/ PA1)); // GDEY0266Z90 152x296, SSD1680
//GxEPD2_3C<GxEPD2_270c, MAX_HEIGHT_3C(GxEPD2_270c)> display(GxEPD2_270c(/*CS=PA4*/ SS, /*DC=*/ PA3, /*RST=*/ PA2, /*BUSY=*/ PA1)); // GDEW027C44 176x264, IL91874
//GxEPD2_3C<GxEPD2_290c, MAX_HEIGHT_3C(GxEPD2_290c)> display(GxEPD2_290c(/*CS=PA4*/ SS, /*DC=*/ PA3, /*RST=*/ PA2, /*BUSY=*/ PA1)); // GDEW029Z10 128x296, UC8151 (IL0373)
//GxEPD2_3C<GxEPD2_290_Z13c, MAX_HEIGHT_3C(GxEPD2_290_Z13c)> display(GxEPD2_290_Z13c(/*CS=PA4*/ SS, /*DC=*/ PA3, /*RST=*/ PA2, /*BUSY=*/ PA1)); // GDEH029Z13 128x296, UC8151D
//GxEPD2_3C<GxEPD2_290_C90c, MAX_HEIGHT_3C(GxEPD2_290_C90c)> display(GxEPD2_290_C90c(/*CS=PA4*/ SS, /*DC=*/ PA3, /*RST=*/ PA2, /*BUSY=*/ PA1)); // GDEM029C90 128x296, SSD1680
//GxEPD2_3C<GxEPD2_420c, MAX_HEIGHT_3C(GxEPD2_420c)> display(GxEPD2_420c(/*CS=PA4*/ SS, /*DC=*/ PA3, /*RST=*/ PA2, /*BUSY=*/ PA1)); // GDEW042Z15 400x300, UC8176 (IL0398)
//GxEPD2_3C<GxEPD2_420c_Z21, MAX_HEIGHT_3C(GxEPD2_420c_Z21)> display(GxEPD2_420c_Z21(/*CS=PA4*/ SS, /*DC=*/ PA3, /*RST=*/ PA2, /*BUSY=*/ PA1)); // GDEQ042Z21 400x300, UC8276
//GxEPD2_3C<GxEPD2_583c, MAX_HEIGHT_3C(GxEPD2_583c)> display(GxEPD2_583c(/*CS=PA4*/ SS, /*DC=*/ PA3, /*RST=*/ PA2, /*BUSY=*/ PA1)); // GDEW0583Z21 600x448, UC8179 (IL0371)
//GxEPD2_3C<GxEPD2_583c_Z83, MAX_HEIGHT_3C(GxEPD2_583c_Z83)> display(GxEPD2_583c_Z83(/*CS=PA4*/ SS, /*DC=*/ PA3, /*RST=*/ PA2, /*BUSY=*/ PA1)); // GDEW0583Z83 648x480, GD7965
//GxEPD2_3C<GxEPD2_750c, MAX_HEIGHT_3C(GxEPD2_750c)> display(GxEPD2_750c(/*CS=PA4*/ SS, /*DC=*/ PA3, /*RST=*/ PA2, /*BUSY=*/ PA1)); // GDEW075Z09 640x384, UC8179 (IL0371)
//GxEPD2_3C<GxEPD2_750c_Z08, MAX_HEIGHT_3C(GxEPD2_750c_Z08)> display(GxEPD2_750c_Z08(/*CS=PA4*/ SS, /*DC=*/ PA3, /*RST=*/ PA2, /*BUSY=*/ PA1)); // GDEW075Z08 800x480, GD7965
//GxEPD2_3C<GxEPD2_750c_Z90, MAX_HEIGHT_3C(GxEPD2_750c_Z90)> display(GxEPD2_750c_Z90(/*CS=PA4*/ SS, /*DC=*/ PA3, /*RST=*/ PA2, /*BUSY=*/ PA1)); // GDEH075Z90 880x528, SSD1677
// 4-color e-paper
//GxEPD2_4C<GxEPD2_266c_GDEY0266F51H, MAX_HEIGHT_3C(GxEPD2_266c_GDEY0266F51H)> display(GxEPD2_266c_GDEY0266F51H(/*CS=PA4*/ SS, /*DC=*/ PA3, /*RST=*/ PA2, /*BUSY=*/ PA1)); // GDEY0266F51H 184x360, JD79667 (FPC-H006 22.04.02)
//GxEPD2_4C<GxEPD2_290c_GDEY029F51H, MAX_HEIGHT_3C(GxEPD2_290c_GDEY029F51H)> display(GxEPD2_290c_GDEY029F51H(/*CS=PA4*/ SS, /*DC=*/ PA3, /*RST=*/ PA2, /*BUSY=*/ PA1)); // GDEY029F51H 168x384, JD79667 (FPC-H004 22.03.24)
//GxEPD2_4C<GxEPD2_300c, MAX_HEIGHT_3C(GxEPD2_300c)> display(GxEPD2_300c(/*CS=PA4*/ SS, /*DC=*/ PA3, /*RST=*/ PA2, /*BUSY=*/ PA1)); // Waveshare 3.00" 4-color
//GxEPD2_4C<GxEPD2_420c_GDEY0420F51, MAX_HEIGHT_3C(GxEPD2_420c_GDEY0420F51)> display(GxEPD2_420c_GDEY0420F51(/*CS=PA4*/ SS, /*DC=*/ PA3, /*RST=*/ PA2, /*BUSY=*/ PA1)); // GDEY0420F51 400x300, HX8717 (no inking)
//GxEPD2_4C <GxEPD2_437c, MAX_HEIGHT_3C(GxEPD2_437c)> display(GxEPD2_437c(/*CS=PA4*/ SS, /*DC=*/ PA3, /*RST=*/ PA2, /*BUSY=*/ PA1)); // Waveshare 4.37" 4-color
// 7-color e-paper
#define MAX_HEIGHT_7C(EPD) (EPD::HEIGHT <= (MAX_DISPLAY_BUFFER_SIZE) / (EPD::WIDTH / 2) ? EPD::HEIGHT : (MAX_DISPLAY_BUFFER_SIZE) / (EPD::WIDTH / 2)) // 2 pixel per byte
//GxEPD2_7C<GxEPD2_565c, MAX_HEIGHT_7C(GxEPD2_565c)> display(GxEPD2_565c(/*CS=PA4*/ SS, /*DC=*/ PA3, /*RST=*/ PA2, /*BUSY=*/ PA1)); // Waveshare 5.65" 7-color
//GxEPD2_7C<GxEPD2_730c_GDEY073D46, MAX_HEIGHT_7C(GxEPD2_730c_GDEY073D46)> display(GxEPD2_730c_GDEY073D46(/*CS=PA4*/ SS, /*DC=*/ PA3, /*RST=*/ PA2, /*BUSY=*/ PA1)); // GDEY073D46 800x480 7-color, (N-FPC-001 2021.11.26)
#undef MAX_DISPLAY_BUFFER_SIZE
#undef MAX_HEIGHT
#undef MAX_HEIGHT_3C
#undef MAX_HEIGHT_7C
#endif

#if defined(__AVR)
#if defined (ARDUINO_AVR_MEGA2560) // Note: SS is on 53 on MEGA
#define MAX_DISPLAY_BUFFER_SIZE 5000 // e.g. full height for 200x200
#else // Note: SS is on 10 on UNO, NANO
#define MAX_DISPLAY_BUFFER_SIZE 800
#endif
#define MAX_HEIGHT(EPD) (EPD::HEIGHT <= MAX_DISPLAY_BUFFER_SIZE / (EPD::WIDTH / 8) ? EPD::HEIGHT : MAX_DISPLAY_BUFFER_SIZE / (EPD::WIDTH / 8))
// select one and adapt to your mapping
//GxEPD2_BW<GxEPD2_102, MAX_HEIGHT(GxEPD2_102)> display(GxEPD2_102(/*CS=*/ SS, /*DC=*/ 8, /*RST=*/ 9, /*BUSY=*/ 7)); // GDEW0102T4 80x128, UC8175
//GxEPD2_BW<GxEPD2_150_BN, MAX_HEIGHT(GxEPD2_150_BN)> display(GxEPD2_150_BN(/*CS=*/ SS, /*DC=*/ 8, /*RST=*/ 9, /*BUSY=*/ 7)); // DEPG0150BN 200x200, SSD1681, TTGO T5 V2.4.1
//GxEPD2_BW<GxEPD2_154, MAX_HEIGHT(GxEPD2_154)> display(GxEPD2_154(/*CS=*/ SS, /*DC=*/ 8, /*RST=*/ 9, /*BUSY=*/ 7)); // GDEP015OC1 200x200, IL3829, no longer available
//GxEPD2_BW<GxEPD2_154_D67, MAX_HEIGHT(GxEPD2_154_D67)> display(GxEPD2_154_D67(/*CS=*/ SS, /*DC=*/ 8, /*RST=*/ 9, /*BUSY=*/ 7)); // GDEH0154D67 200x200, SSD1681
//GxEPD2_BW<GxEPD2_154_T8, MAX_HEIGHT(GxEPD2_154_T8)> display(GxEPD2_154_T8(/*CS=*/ SS, /*DC=*/ 8, /*RST=*/ 9, /*BUSY=*/ 7)); // GDEW0154T8  152x152, UC8151 (IL0373)
//GxEPD2_BW<GxEPD2_154_M09, MAX_HEIGHT(GxEPD2_154_M09)> display(GxEPD2_154_M09(/*CS=*/ SS, /*DC=*/ 8, /*RST=*/ 9, /*BUSY=*/ 7)); // GDEW0154M09 200x200, JD79653A
//GxEPD2_BW<GxEPD2_154_M10, MAX_HEIGHT(GxEPD2_154_M10)> display(GxEPD2_154_M10(/*CS=*/ SS, /*DC=*/ 8, /*RST=*/ 9, /*BUSY=*/ 7)); // GDEW0154M10 152x152, UC8151D
//GxEPD2_BW<GxEPD2_154_GDEY0154D67, MAX_HEIGHT(GxEPD2_154_GDEY0154D67)> display(GxEPD2_154_GDEY0154D67(/*CS=*/ SS, /*DC=*/ 8, /*RST=*/ 9, /*BUSY=*/ 7)); // GDEY0154D67 200x200, SSD1681, (FPC-B001 20.05.21)
//GxEPD2_BW<GxEPD2_213, MAX_HEIGHT(GxEPD2_213)> display(GxEPD2_213(/*CS=*/ SS, /*DC=*/ 8, /*RST=*/ 9, /*BUSY=*/ 7)); // GDE0213B1 122x250, IL3895, phased out
//GxEPD2_BW<GxEPD2_213_B72, MAX_HEIGHT(GxEPD2_213_B72)> display(GxEPD2_213_B72(/*CS=*/ SS, /*DC=*/ 8, /*RST=*/ 9, /*BUSY=*/ 7)); // GDEH0213B72 122x250, SSD1675A (IL3897)
//GxEPD2_BW<GxEPD2_213_B73, MAX_HEIGHT(GxEPD2_213_B73)> display(GxEPD2_213_B73(/*CS=*/ SS, /*DC=*/ 8, /*RST=*/ 9, /*BUSY=*/ 7)); // GDEH0213B73 122x250, SSD1675B
//GxEPD2_BW<GxEPD2_213_B74, MAX_HEIGHT(GxEPD2_213_B74)> display(GxEPD2_213_B74(/*CS=*/ SS, /*DC=*/ 8, /*RST=*/ 9, /*BUSY=*/ 7)); // GDEM0213B74 122x250, SSD1680
//GxEPD2_BW<GxEPD2_213_flex, MAX_HEIGHT(GxEPD2_213_flex)> display(GxEPD2_213_flex(/*CS=*/ SS, /*DC=*/ 8, /*RST=*/ 9, /*BUSY=*/ 7)); // GDEW0213I5F 104x212, UC8151 (IL0373)
//GxEPD2_BW<GxEPD2_213_M21, MAX_HEIGHT(GxEPD2_213_M21)> display(GxEPD2_213_M21(/*CS=*/ SS, /*DC=*/ 8, /*RST=*/ 9, /*BUSY=*/ 7)); // GDEW0213M21 104x212, UC8151 (IL0373)
//GxEPD2_BW<GxEPD2_213_T5D, MAX_HEIGHT(GxEPD2_213_T5D)> display(GxEPD2_213_T5D(/*CS=*/ SS, /*DC=*/ 8, /*RST=*/ 9, /*BUSY=*/ 7)); // GDEW0213T5D 104x212, UC8151D
//GxEPD2_BW<GxEPD2_213_BN, MAX_HEIGHT(GxEPD2_213_BN)> display(GxEPD2_213_BN(/*CS=*/ SS, /*DC=*/ 8, /*RST=*/ 9, /*BUSY=*/ 7)); // DEPG0213BN 122x250, SSD1680, TTGO T5 V2.4.1, V2.3.1
//GxEPD2_BW<GxEPD2_213_GDEY0213B74, MAX_HEIGHT(GxEPD2_213_GDEY0213B74)> display(GxEPD2_213_GDEY0213B74(/*CS=*/ SS, /*DC=*/ 8, /*RST=*/ 9, /*BUSY=*/ 7)); // GDEY0213B74 122x250, SSD1680, (FPC-A002 20.04.08)
//GxEPD2_BW<GxEPD2_260, MAX_HEIGHT(GxEPD2_260)> display(GxEPD2_260(/*CS=*/ SS, /*DC=*/ 8, /*RST=*/ 9, /*BUSY=*/ 7)); // GDEW026T0 152x296, UC8151 (IL0373)
//GxEPD2_BW<GxEPD2_260_M01, MAX_HEIGHT(GxEPD2_260_M01)> display(GxEPD2_260_M01(/*CS=*/ SS, /*DC=*/ 8, /*RST=*/ 9, /*BUSY=*/ 7)); // GDEW026M01 152x296, UC8151 (IL0373)
//GxEPD2_BW<GxEPD2_266_BN, MAX_HEIGHT(GxEPD2_266_BN)> display(GxEPD2_266_BN(/*CS=*/ SS, /*DC=*/ 8, /*RST=*/ 9, /*BUSY=*/ 7)); // DEPG0266BN 152x296, SSD1680, TTGO T5 V2.66 / T92_V1.0
//GxEPD2_BW<GxEPD2_270, MAX_HEIGHT(GxEPD2_270)> display(GxEPD2_270(/*CS=*/ SS, /*DC=*/ 8, /*RST=*/ 9, /*BUSY=*/ 7)); // GDEW027W3 176x264, EK79652 (IL91874)
//GxEPD2_BW<GxEPD2_270_GDEY027T91, MAX_HEIGHT(GxEPD2_270_GDEY027T91)> display(GxEPD2_270_GDEY027T91(/*CS=*/ SS, /*DC=*/ 8, /*RST=*/ 9, /*BUSY=*/ 7)); // GDEY027T91 176x264, SSD1680
//GxEPD2_BW<GxEPD2_290, MAX_HEIGHT(GxEPD2_290)> display(GxEPD2_290(/*CS=*/ SS, /*DC=*/ 8, /*RST=*/ 9, /*BUSY=*/ 7)); // GDEH029A1 128x296, SSD1608 (IL3820)
//GxEPD2_BW<GxEPD2_290_T5, MAX_HEIGHT(GxEPD2_290_T5)> display(GxEPD2_290_T5(/*CS=*/ SS, /*DC=*/ 8, /*RST=*/ 9, /*BUSY=*/ 7)); // GDEW029T5 128x296, UC8151 (IL0373)
//GxEPD2_BW<GxEPD2_290_T5D, MAX_HEIGHT(GxEPD2_290_T5D)> display(GxEPD2_290_T5D(/*CS=*/ SS, /*DC=*/ 8, /*RST=*/ 9, /*BUSY=*/ 7)); // GDEW029T5D 128x296, UC8151D
//GxEPD2_BW<GxEPD2_290_I6FD, MAX_HEIGHT(GxEPD2_290_I6FD)> display(GxEPD2_290_I6FD(/*CS=*/ SS, /*DC=*/ 8, /*RST=*/ 9, /*BUSY=*/ 7)); // GDEW029I6FD 128x296, UC8151D
//GxEPD2_BW<GxEPD2_290_T94, MAX_HEIGHT(GxEPD2_290_T94)> display(GxEPD2_290_T94(/*CS=*/ SS, /*DC=*/ 8, /*RST=*/ 9, /*BUSY=*/ 7)); // GDEM029T94 128x296, SSD1680
//GxEPD2_BW<GxEPD2_290_T94_V2, MAX_HEIGHT(GxEPD2_290_T94_V2)> display(GxEPD2_290_T94_V2(/*CS=*/ SS, /*DC=*/ 8, /*RST=*/ 9, /*BUSY=*/ 7)); // GDEM029T94 128x296, SSD1680, Waveshare 2.9" V2 variant
//GxEPD2_BW<GxEPD2_290_BS, MAX_HEIGHT(GxEPD2_290_BS)> display(GxEPD2_290_BS(/*CS=*/ SS, /*DC=*/ 8, /*RST=*/ 9, /*BUSY=*/ 7)); // DEPG0290BS 128x296, SSD1680
//GxEPD2_BW<GxEPD2_290_M06, MAX_HEIGHT(GxEPD2_290_M06)> display(GxEPD2_290_M06(/*CS=*/ SS, /*DC=*/ 8, /*RST=*/ 9, /*BUSY=*/ 7)); // GDEW029M06  128x296, UC8151D
//GxEPD2_BW<GxEPD2_290_GDEY029T94, MAX_HEIGHT(GxEPD2_290_GDEY029T94)> display(GxEPD2_290_GDEY029T94(/*CS=*/ SS, /*DC=*/ 8, /*RST=*/ 9, /*BUSY=*/ 7)); // GDEY029T94  128x296, SSD1680, (FPC-A005 20.06.15)
//GxEPD2_BW<GxEPD2_371, MAX_HEIGHT(GxEPD2_371)> display(GxEPD2_371(/*CS=*/ SS, /*DC=*/ 8, /*RST=*/ 9, /*BUSY=*/ 7)); // GDEW0371W7 240x416, UC8171 (IL0324)
//GxEPD2_BW<GxEPD2_370_TC1, MAX_HEIGHT(GxEPD2_370_TC1)> display(GxEPD2_370_TC1(/*CS=*/ SS, /*DC=*/ 8, /*RST=*/ 9, /*BUSY=*/ 7)); // ED037TC1 280x480, SSD1677, Waveshare 3.7"
//GxEPD2_BW<GxEPD2_420, MAX_HEIGHT(GxEPD2_420)> display(GxEPD2_420(/*CS=*/ SS, /*DC=*/ 8, /*RST=*/ 9, /*BUSY=*/ 7)); // GDEW042T2 400x300, UC8176 (IL0398)
//GxEPD2_BW<GxEPD2_420_M01, MAX_HEIGHT(GxEPD2_420_M01)> display(GxEPD2_420_M01(/*CS=*/ SS, /*DC=*/ 8, /*RST=*/ 9, /*BUSY=*/ 7)); // GDEW042M01 400x300, UC8176 (IL0398)
//GxEPD2_BW<GxEPD2_420_GDEY042T81, MAX_HEIGHT(GxEPD2_420_GDEY042T81)> display(GxEPD2_420_GDEY042T81(/*CS=*/ SS, /*DC=*/ 8, /*RST=*/ 9, /*BUSY=*/ 7)); GDEY042T81, 400x300, SSD1683 (no inking)
//GxEPD2_BW<GxEPD2_426_GDEQ0426T82, MAX_HEIGHT(GxEPD2_426_GDEQ0426T82)> display(GxEPD2_426_GDEQ0426T82(/*CS=*/ SS, /*DC=*/ 8, /*RST=*/ 9, /*BUSY=*/ 7)); // GDEQ0426T82 480x800, SSD1677 (P426010-MF1-A)
//GxEPD2_BW<GxEPD2_583, MAX_HEIGHT(GxEPD2_583)> display(GxEPD2_583(/*CS=*/ SS, /*DC=*/ 8, /*RST=*/ 9, /*BUSY=*/ 7)); // GDEW0583T7 600x448, UC8159c (IL0371)
//GxEPD2_BW<GxEPD2_583_T8, MAX_HEIGHT(GxEPD2_583_T8)> display(GxEPD2_583_T8(/*CS=*/ SS, /*DC=*/ 8, /*RST=*/ 9, /*BUSY=*/ 7)); // GDEW0583T8 648x480, EK79655 (GD7965)
//GxEPD2_BW<GxEPD2_583_GDEQ0583T31, MAX_HEIGHT(GxEPD2_583_GDEQ0583T31)> display(GxEPD2_583_GDEQ0583T31(/*CS=*/ SS, /*DC=*/ 8, /*RST=*/ 9, /*BUSY=*/ 7)); // GDEQ0583T31 648x480, UC8179, (P583010-MF1-B)
//GxEPD2_BW<GxEPD2_750, MAX_HEIGHT(GxEPD2_750)> display(GxEPD2_750(/*CS=*/ SS, /*DC=*/ 8, /*RST=*/ 9, /*BUSY=*/ 7)); // GDEW075T8 640x384, UC8159c (IL0371)
//GxEPD2_BW<GxEPD2_750_T7, MAX_HEIGHT(GxEPD2_750_T7)> display(GxEPD2_750_T7(/*CS=*/ SS, /*DC=*/ 8, /*RST=*/ 9, /*BUSY=*/ 7)); // GDEW075T7 800x480, EK79655 (GD7965)
//GxEPD2_BW<GxEPD2_750_YT7, MAX_HEIGHT(GxEPD2_750_YT7)> display(GxEPD2_750_YT7(/*CS=*/ SS, /*DC=*/ 8, /*RST=*/ 9, /*BUSY=*/ 7)); // GDEY075T7 800x480, UC8179 (GD7965)
//GxEPD2_BW < GxEPD2_1160_T91, MAX_HEIGHT(GxEPD2_1160_T91)> display(GxEPD2_1160_T91(/*CS=*/ SS, /*DC=*/ 8, /*RST=*/ 9, /*BUSY=*/ 7)); // GDEH116T91 960x640, SSD1677
// 3-color e-papers
#define MAX_HEIGHT_3C(EPD) (EPD::HEIGHT <= (MAX_DISPLAY_BUFFER_SIZE / 2) / (EPD::WIDTH / 8) ? EPD::HEIGHT : (MAX_DISPLAY_BUFFER_SIZE / 2) / (EPD::WIDTH / 8))
//GxEPD2_3C<GxEPD2_154c, MAX_HEIGHT_3C(GxEPD2_154c)> display(GxEPD2_154c(/*CS=*/ SS, /*DC=*/ 8, /*RST=*/ 9, /*BUSY=*/ 7)); // GDEW0154Z04 200x200, IL0376F, no longer available
//GxEPD2_3C<GxEPD2_154_Z90c, MAX_HEIGHT_3C(GxEPD2_154_Z90c)> display(GxEPD2_154_Z90c(/*CS=*/ SS, /*DC=*/ 8, /*RST=*/ 9, /*BUSY=*/ 7)); // GDEH0154Z90 200x200, SSD1681
//GxEPD2_3C<GxEPD2_213c, MAX_HEIGHT_3C(GxEPD2_213c)> display(GxEPD2_213c(/*CS=*/ SS, /*DC=*/ 8, /*RST=*/ 9, /*BUSY=*/ 7)); // GDEW0213Z16 104x212, UC8151 (IL0373)
//GxEPD2_3C<GxEPD2_213_Z19c, MAX_HEIGHT_3C(GxEPD2_213_Z19c)> display(GxEPD2_213_Z19c(/*CS=*/ SS, /*DC=*/ 8, /*RST=*/ 9, /*BUSY=*/ 7)); // GDEH0213Z19 104x212, UC8151D
//GxEPD2_3C<GxEPD2_213_Z98c, MAX_HEIGHT_3C(GxEPD2_213_Z98c)> display(GxEPD2_213_Z98c(/*CS=*/ SS, /*DC=*/ 8, /*RST=*/ 9, /*BUSY=*/ 7)); // GDEY0213Z98 122x250, SSD1680
//GxEPD2_3C<GxEPD2_266c, MAX_HEIGHT_3C(GxEPD2_266c)> display(GxEPD2_266c(/*CS=*/ SS, /*DC=*/ 8, /*RST=*/ 9, /*BUSY=*/ 7)); // GDEY0266Z90 152x296, SSD1680
//GxEPD2_3C<GxEPD2_270c, MAX_HEIGHT_3C(GxEPD2_270c)> display(GxEPD2_270c(/*CS=*/ SS, /*DC=*/ 8, /*RST=*/ 9, /*BUSY=*/ 7)); // GDEW027C44 176x264, IL91874
//GxEPD2_3C<GxEPD2_290c, MAX_HEIGHT_3C(GxEPD2_290c)> display(GxEPD2_290c(/*CS=*/ SS, /*DC=*/ 8, /*RST=*/ 9, /*BUSY=*/ 7)); // GDEW029Z10 128x296, UC8151 (IL0373)
//GxEPD2_3C<GxEPD2_290_Z13c, MAX_HEIGHT_3C(GxEPD2_290_Z13c)> display(GxEPD2_290_Z13c(/*CS=*/ SS, /*DC=*/ 8, /*RST=*/ 9, /*BUSY=*/ 7)); // GDEH029Z13 128x296, UC8151D
//GxEPD2_3C<GxEPD2_290_C90c, MAX_HEIGHT_3C(GxEPD2_290_C90c)> display(GxEPD2_290_C90c(/*CS=*/ SS, /*DC=*/ 8, /*RST=*/ 9, /*BUSY=*/ 7)); // GDEM029C90 128x296, SSD1680
//GxEPD2_3C<GxEPD2_420c, MAX_HEIGHT_3C(GxEPD2_420c)> display(GxEPD2_420c(/*CS=*/ SS, /*DC=*/ 8, /*RST=*/ 9, /*BUSY=*/ 7)); // GDEW042Z15 400x300, UC8176 (IL0398)
//GxEPD2_3C<GxEPD2_420c_Z21, MAX_HEIGHT_3C(GxEPD2_420c_Z21)> display(GxEPD2_420c_Z21(/*CS=*/ SS, /*DC=*/ 8, /*RST=*/ 9, /*BUSY=*/ 7)); // GDEQ042Z21 400x300, UC8276
//GxEPD2_3C<GxEPD2_583c, MAX_HEIGHT_3C(GxEPD2_583c)> display(GxEPD2_583c(/*CS=*/ SS, /*DC=*/ 8, /*RST=*/ 9, /*BUSY=*/ 7)); // GDEW0583Z21 600x448, UC8179 (IL0371)
//GxEPD2_3C<GxEPD2_583c_Z83, MAX_HEIGHT_3C(GxEPD2_583c_Z83)> display(GxEPD2_583c_Z83(/*CS=*/ SS, /*DC=*/ 8, /*RST=*/ 9, /*BUSY=*/ 7)); // GDEW0583Z83 648x480, GD7965
//GxEPD2_3C<GxEPD2_750c, MAX_HEIGHT_3C(GxEPD2_750c)> display(GxEPD2_750c(/*CS=*/ SS, /*DC=*/ 8, /*RST=*/ 9, /*BUSY=*/ 7)); // GDEW075Z09 640x384, UC8179 (IL0371)
//GxEPD2_3C<GxEPD2_750c_Z08, MAX_HEIGHT_3C(GxEPD2_750c_Z08)> display(GxEPD2_750c_Z08(/*CS=*/ SS, /*DC=*/ 8, /*RST=*/ 9, /*BUSY=*/ 7)); // GDEW075Z08 800x480, GD7965
//GxEPD2_3C<GxEPD2_750c_Z90, MAX_HEIGHT_3C(GxEPD2_750c_Z90)> display(GxEPD2_750c_Z90(/*CS=*/ SS, /*DC=*/ 8, /*RST=*/ 9, /*BUSY=*/ 7)); // GDEH075Z90 880x528, SSD1677
// 4-color e-paper
//GxEPD2_4C<GxEPD2_266c_GDEY0266F51H, MAX_HEIGHT_3C(GxEPD2_266c_GDEY0266F51H)> display(GxEPD2_266c_GDEY0266F51H(/*CS=*/ SS, /*DC=*/ 8, /*RST=*/ 9, /*BUSY=*/ 7)); // GDEY0266F51H 184x360, JD79667 (FPC-H006 22.04.02)
//GxEPD2_4C<GxEPD2_290c_GDEY029F51H, MAX_HEIGHT_3C(GxEPD2_290c_GDEY029F51H)> display(GxEPD2_290c_GDEY029F51H(/*CS=*/ SS, /*DC=*/ 8, /*RST=*/ 9, /*BUSY=*/ 7)); // GDEY029F51H 168x384, JD79667 (FPC-H004 22.03.24)
//GxEPD2_4C<GxEPD2_300c, MAX_HEIGHT_3C(GxEPD2_300c)> display(GxEPD2_300c(/*CS=*/ SS, /*DC=*/ 8, /*RST=*/ 9, /*BUSY=*/ 7)); // Waveshare 3.00" 4-color
//GxEPD2_4C<GxEPD2_420c_GDEY0420F51, MAX_HEIGHT_3C(GxEPD2_420c_GDEY0420F51)> display(GxEPD2_420c_GDEY0420F51(/*CS=*/ SS, /*DC=*/ 8, /*RST=*/ 9, /*BUSY=*/ 7)); // GDEY0420F51 400x300, HX8717 (no inking)
//GxEPD2_4C <GxEPD2_437c, MAX_HEIGHT_3C(GxEPD2_437c)> display(GxEPD2_437c(/*CS=*/ SS, /*DC=*/ 8, /*RST=*/ 9, /*BUSY=*/ 7)); // Waveshare 4.37" 4-color
// 7-color e-paper
#define MAX_HEIGHT_7C(EPD) (EPD::HEIGHT <= (MAX_DISPLAY_BUFFER_SIZE) / (EPD::WIDTH / 2) ? EPD::HEIGHT : (MAX_DISPLAY_BUFFER_SIZE) / (EPD::WIDTH / 2)) // 2 pixel per byte
//GxEPD2_7C<GxEPD2_565c, MAX_HEIGHT_7C(GxEPD2_565c)> display(GxEPD2_565c(/*CS=*/ SS, /*DC=*/ 8, /*RST=*/ 9, /*BUSY=*/ 7)); // Waveshare 5.65" 7-color
//GxEPD2_7C<GxEPD2_730c_GDEY073D46, MAX_HEIGHT_7C(GxEPD2_730c_GDEY073D46)> display(GxEPD2_730c_GDEY073D46(/*CS=*/ SS, /*DC=*/ 8, /*RST=*/ 9, /*BUSY=*/ 7)); // GDEY073D46 800x480 7-color, (N-FPC-001 2021.11.26)

// ***** for mapping of Waveshare Universal e-Paper Raw Panel Driver Shield for Arduino / NUCLEO *****
// the RST line is not connected through level converter, but has a pull up resistor and a pull down diode to the Arduino pin; this is safe for 5V Arduino
// NOTE: the 11-pinholes for pin connectors are not through level converter, and the VCC pin is ~4.2V, only FCP connector pins are through level converter
// NOTE: the VCC pin on the 11-pinholes for pin connectors shouldn't be used, it seems to get back-fed from Arduino data pins through protection diodes of the level converter
// NOTE: the VCC pin should be fed from Arduino 5V pin for use on any 5V Arduino (did they forget to add this connection or add a jumper?)
// select one and adapt to your mapping
//GxEPD2_BW<GxEPD2_150_BN, MAX_HEIGHT(GxEPD2_150_BN)> display(GxEPD2_150_BN(/*CS=10*/ SS, /*DC=*/ 9, /*RST=*/ 8, /*BUSY=*/ 7)); // DEPG0150BN 200x200, SSD1681, TTGO T5 V2.4.1
//GxEPD2_BW<GxEPD2_154, MAX_HEIGHT(GxEPD2_154)> display(GxEPD2_154(/*CS=10*/ SS, /*DC=*/ 9, /*RST=*/ 8, /*BUSY=*/ 7)); // GDEP015OC1 200x200, IL3829, no longer available
//GxEPD2_BW<GxEPD2_154_D67, MAX_HEIGHT(GxEPD2_154_D67)> display(GxEPD2_154_D67(/*CS=10*/ SS, /*DC=*/ 9, /*RST=*/ 8, /*BUSY=*/ 7)); // GDEH0154D67 200x200, SSD1681
//GxEPD2_BW<GxEPD2_154_T8, MAX_HEIGHT(GxEPD2_154_T8)> display(GxEPD2_154_T8(/*CS=10*/ SS, /*DC=*/ 9, /*RST=*/ 8, /*BUSY=*/ 7)); // GDEW0154T8  152x152, UC8151 (IL0373)
//GxEPD2_BW<GxEPD2_154_M09, MAX_HEIGHT(GxEPD2_154_M09)> display(GxEPD2_154_M09(/*CS=10*/ SS, /*DC=*/ 9, /*RST=*/ 8, /*BUSY=*/ 7)); // GDEW0154M09 200x200, JD79653A
//GxEPD2_BW<GxEPD2_154_M10, MAX_HEIGHT(GxEPD2_154_M10)> display(GxEPD2_154_M10(/*CS=10*/ SS, /*DC=*/ 9, /*RST=*/ 8, /*BUSY=*/ 7)); // GDEW0154M10 152x152, UC8151D
//GxEPD2_BW<GxEPD2_154_GDEY0154D67, MAX_HEIGHT(GxEPD2_154_GDEY0154D67)> display(GxEPD2_154_GDEY0154D67(/*CS=10*/ SS, /*DC=*/ 9, /*RST=*/ 8, /*BUSY=*/ 7)); // GDEY0154D67 200x200, SSD1681, (FPC-B001 20.05.21)
//GxEPD2_BW<GxEPD2_213, MAX_HEIGHT(GxEPD2_213)> display(GxEPD2_213(/*CS=10*/ SS, /*DC=*/ 9, /*RST=*/ 8, /*BUSY=*/ 7)); // GDE0213B1 122x250, IL3895, phased out
//GxEPD2_BW<GxEPD2_213_B72, MAX_HEIGHT(GxEPD2_213_B72)> display(GxEPD2_213_B72(/*CS=10*/ SS, /*DC=*/ 9, /*RST=*/ 8, /*BUSY=*/ 7)); // GDEH0213B72 122x250, SSD1675A (IL3897)
//GxEPD2_BW<GxEPD2_213_B73, MAX_HEIGHT(GxEPD2_213_B73)> display(GxEPD2_213_B73(/*CS=10*/ SS, /*DC=*/ 9, /*RST=*/ 8, /*BUSY=*/ 7)); // GDEH0213B73 122x250, SSD1675B
//GxEPD2_BW<GxEPD2_213_B74, MAX_HEIGHT(GxEPD2_213_B74)> display(GxEPD2_213_B74(/*CS=10*/ SS, /*DC=*/ 9, /*RST=*/ 8, /*BUSY=*/ 7)); // GDEM0213B74 122x250, SSD1680
//GxEPD2_BW<GxEPD2_213_flex, MAX_HEIGHT(GxEPD2_213_flex)> display(GxEPD2_213_flex(/*CS=10*/ SS, /*DC=*/ 9, /*RST=*/ 8, /*BUSY=*/ 7)); // GDEW0213I5F 104x212, UC8151 (IL0373)
//GxEPD2_BW<GxEPD2_213_M21, MAX_HEIGHT(GxEPD2_213_M21)> display(GxEPD2_213_M21(/*CS=10*/ SS, /*DC=*/ 9, /*RST=*/ 8, /*BUSY=*/ 7)); // GDEW0213M21 104x212, UC8151 (IL0373)
//GxEPD2_BW<GxEPD2_213_T5D, MAX_HEIGHT(GxEPD2_213_T5D)> display(GxEPD2_213_T5D(/*CS=10*/ SS, /*DC=*/ 9, /*RST=*/ 8, /*BUSY=*/ 7)); // GDEW0213T5D 104x212, UC8151D
//GxEPD2_BW<GxEPD2_213_BN, MAX_HEIGHT(GxEPD2_213_BN)> display(GxEPD2_213_BN(/*CS=10*/ SS, /*DC=*/ 9, /*RST=*/ 8, /*BUSY=*/ 7)); // DEPG0213BN 122x250, SSD1680, TTGO T5 V2.4.1, V2.3.1
//GxEPD2_BW<GxEPD2_213_GDEY0213B74, MAX_HEIGHT(GxEPD2_213_GDEY0213B74)> display(GxEPD2_213_GDEY0213B74(/*CS=10*/ SS, /*DC=*/ 9, /*RST=*/ 8, /*BUSY=*/ 7)); // GDEY0213B74 122x250, SSD1680, (FPC-A002 20.04.08)
//GxEPD2_BW<GxEPD2_260, MAX_HEIGHT(GxEPD2_260)> display(GxEPD2_260(/*CS=10*/ SS, /*DC=*/ 9, /*RST=*/ 8, /*BUSY=*/ 7)); // GDEW026T0 152x296, UC8151 (IL0373)
//GxEPD2_BW<GxEPD2_260_M01, MAX_HEIGHT(GxEPD2_260_M01)> display(GxEPD2_260_M01(/*CS=10*/ SS, /*DC=*/ 9, /*RST=*/ 8, /*BUSY=*/ 7)); // GDEW026M01 152x296, UC8151 (IL0373)
//GxEPD2_BW<GxEPD2_266_BN, MAX_HEIGHT(GxEPD2_266_BN)> display(GxEPD2_266_BN(/*CS=10*/ SS, /*DC=*/ 9, /*RST=*/ 8, /*BUSY=*/ 7)); // DEPG0266BN 152x296, SSD1680, TTGO T5 V2.66 / T92_V1.0
//GxEPD2_BW<GxEPD2_270, MAX_HEIGHT(GxEPD2_270)> display(GxEPD2_270(/*CS=10*/ SS, /*DC=*/ 9, /*RST=*/ 8, /*BUSY=*/ 7)); // GDEW027W3 176x264, EK79652 (IL91874)
//GxEPD2_BW<GxEPD2_270_GDEY027T91, MAX_HEIGHT(GxEPD2_270_GDEY027T91)> display(GxEPD2_270_GDEY027T91(/*CS=10*/ SS, /*DC=*/ 9, /*RST=*/ 8, /*BUSY=*/ 7)); // GDEY027T91 176x264, SSD1680
//GxEPD2_BW<GxEPD2_290, MAX_HEIGHT(GxEPD2_290)> display(GxEPD2_290(/*CS=10*/ SS, /*DC=*/ 9, /*RST=*/ 8, /*BUSY=*/ 7)); // GDEH029A1 128x296, SSD1608 (IL3820)
//GxEPD2_BW<GxEPD2_290_T5, MAX_HEIGHT(GxEPD2_290_T5)> display(GxEPD2_290_T5(/*CS=10*/ SS, /*DC=*/ 9, /*RST=*/ 8, /*BUSY=*/ 7)); // GDEW029T5 128x296, UC8151 (IL0373)
//GxEPD2_BW<GxEPD2_290_T5D, MAX_HEIGHT(GxEPD2_290_T5D)> display(GxEPD2_290_T5D(/*CS=10*/ SS, /*DC=*/ 9, /*RST=*/ 8, /*BUSY=*/ 7)); // GDEW029T5D 128x296, UC8151D
//GxEPD2_BW<GxEPD2_290_I6FD, MAX_HEIGHT(GxEPD2_290_I6FD)> display(GxEPD2_290_I6FD(/*CS=10*/ SS, /*DC=*/ 9, /*RST=*/ 8, /*BUSY=*/ 7)); // GDEW029I6FD 128x296, UC8151D
//GxEPD2_BW<GxEPD2_290_T94, MAX_HEIGHT(GxEPD2_290_T94)> display(GxEPD2_290_T94(/*CS=10*/ SS, /*DC=*/ 9, /*RST=*/ 8, /*BUSY=*/ 7)); // GDEM029T94 128x296, SSD1680
//GxEPD2_BW<GxEPD2_290_T94_V2, MAX_HEIGHT(GxEPD2_290_T94_V2)> display(GxEPD2_290_T94_V2(/*CS=10*/ SS, /*DC=*/ 9, /*RST=*/ 8, /*BUSY=*/ 7)); // GDEM029T94 128x296, SSD1680, Waveshare 2.9" V2 variant
//GxEPD2_BW<GxEPD2_290_BS, MAX_HEIGHT(GxEPD2_290_BS)> display(GxEPD2_290_BS(/*CS=10*/ SS, /*DC=*/ 9, /*RST=*/ 8, /*BUSY=*/ 7)); // DEPG0290BS 128x296, SSD1680
//GxEPD2_BW<GxEPD2_290_M06, MAX_HEIGHT(GxEPD2_290_M06)> display(GxEPD2_290_M06(/*CS=10*/ SS, /*DC=*/ 9, /*RST=*/ 8, /*BUSY=*/ 7)); // GDEW029M06  128x296, UC8151D
//GxEPD2_BW<GxEPD2_290_GDEY029T94, MAX_HEIGHT(GxEPD2_290_GDEY029T94)> display(GxEPD2_290_GDEY029T94(/*CS=10*/ SS, /*DC=*/ 9, /*RST=*/ 8, /*BUSY=*/ 7)); // GDEY029T94  128x296, SSD1680, (FPC-A005 20.06.15)
//GxEPD2_BW<GxEPD2_371, MAX_HEIGHT(GxEPD2_371)> display(GxEPD2_371(/*CS=10*/ SS, /*DC=*/ 9, /*RST=*/ 8, /*BUSY=*/ 7)); // GDEW0371W7 240x416, UC8171 (IL0324)
//GxEPD2_BW<GxEPD2_370_TC1, MAX_HEIGHT(GxEPD2_370_TC1)> display(GxEPD2_370_TC1(/*CS=10*/ SS, /*DC=*/ 9, /*RST=*/ 8, /*BUSY=*/ 7)); // ED037TC1 280x480, SSD1677, Waveshare 3.7"
//GxEPD2_BW<GxEPD2_420, MAX_HEIGHT(GxEPD2_420)> display(GxEPD2_420(/*CS=10*/ SS, /*DC=*/ 9, /*RST=*/ 8, /*BUSY=*/ 7)); // GDEW042T2 400x300, UC8176 (IL0398)
//GxEPD2_BW<GxEPD2_420_M01, MAX_HEIGHT(GxEPD2_420_M01)> display(GxEPD2_420_M01(/*CS=10*/ SS, /*DC=*/ 9, /*RST=*/ 8, /*BUSY=*/ 7)); // GDEW042M01 400x300, UC8176 (IL0398)
//GxEPD2_BW<GxEPD2_420_GDEY042T81, MAX_HEIGHT(GxEPD2_420_GDEY042T81)> display(GxEPD2_420_GDEY042T81(/*CS=10*/ SS, /*DC=*/ 9, /*RST=*/ 8, /*BUSY=*/ 7)); GDEY042T81, 400x300, SSD1683 (no inking)
//GxEPD2_BW<GxEPD2_426_GDEQ0426T82, MAX_HEIGHT(GxEPD2_426_GDEQ0426T82)> display(GxEPD2_426_GDEQ0426T82(/*CS=10*/ SS, /*DC=*/ 9, /*RST=*/ 8, /*BUSY=*/ 7)); // GDEQ0426T82 480x800, SSD1677 (P426010-MF1-A)
//GxEPD2_BW<GxEPD2_583, MAX_HEIGHT(GxEPD2_583)> display(GxEPD2_583(/*CS=10*/ SS, /*DC=*/ 9, /*RST=*/ 8, /*BUSY=*/ 7)); // GDEW0583T7 600x448, UC8159c (IL0371)
//GxEPD2_BW<GxEPD2_583_T8, MAX_HEIGHT(GxEPD2_583_T8)> display(GxEPD2_583_T8(/*CS=10*/ SS, /*DC=*/ 9, /*RST=*/ 8, /*BUSY=*/ 7)); // GDEW0583T8 648x480, EK79655 (GD7965)
//GxEPD2_BW<GxEPD2_583_GDEQ0583T31, MAX_HEIGHT(GxEPD2_583_GDEQ0583T31)> display(GxEPD2_583_GDEQ0583T31(/*CS=10*/ SS, /*DC=*/ 9, /*RST=*/ 8, /*BUSY=*/ 7)); // GDEQ0583T31 648x480, UC8179, (P583010-MF1-B)
//GxEPD2_BW<GxEPD2_750, MAX_HEIGHT(GxEPD2_750)> display(GxEPD2_750(/*CS=10*/ SS, /*DC=*/ 9, /*RST=*/ 8, /*BUSY=*/ 7)); // GDEW075T8 640x384, UC8159c (IL0371)
//GxEPD2_BW<GxEPD2_750_T7, MAX_HEIGHT(GxEPD2_750_T7)> display(GxEPD2_750_T7(/*CS=10*/ SS, /*DC=*/ 9, /*RST=*/ 8, /*BUSY=*/ 7)); // GDEW075T7 800x480, EK79655 (GD7965)
//GxEPD2_BW<GxEPD2_750_YT7, MAX_HEIGHT(GxEPD2_750_YT7)> display(GxEPD2_750_YT7(/*CS=10*/ SS, /*DC=*/ 9, /*RST=*/ 8, /*BUSY=*/ 7)); // GDEY075T7 800x480, UC8179 (GD7965)
//GxEPD2_BW < GxEPD2_1160_T91, MAX_HEIGHT(GxEPD2_1160_T91)> display(GxEPD2_1160_T91(/*CS=10*/ SS, /*DC=*/ 9, /*RST=*/ 8, /*BUSY=*/ 7)); // GDEH116T91 960x640, SSD1677
// 3-color e-papers
//GxEPD2_3C<GxEPD2_154c, MAX_HEIGHT_3C(GxEPD2_154c)> display(GxEPD2_154c(/*CS=10*/ SS, /*DC=*/ 9, /*RST=*/ 8, /*BUSY=*/ 7)); // GDEW0154Z04 200x200, IL0376F, no longer available
//GxEPD2_3C<GxEPD2_154_Z90c, MAX_HEIGHT_3C(GxEPD2_154_Z90c)> display(GxEPD2_154_Z90c(/*CS=10*/ SS, /*DC=*/ 9, /*RST=*/ 8, /*BUSY=*/ 7)); // GDEH0154Z90 200x200, SSD1681
//GxEPD2_3C<GxEPD2_213c, MAX_HEIGHT_3C(GxEPD2_213c)> display(GxEPD2_213c(/*CS=10*/ SS, /*DC=*/ 9, /*RST=*/ 8, /*BUSY=*/ 7)); // GDEW0213Z16 104x212, UC8151 (IL0373)
//GxEPD2_3C<GxEPD2_213_Z19c, MAX_HEIGHT_3C(GxEPD2_213_Z19c)> display(GxEPD2_213_Z19c(/*CS=10*/ SS, /*DC=*/ 9, /*RST=*/ 8, /*BUSY=*/ 7)); // GDEH0213Z19 104x212, UC8151D
//GxEPD2_3C<GxEPD2_213_Z98c, MAX_HEIGHT_3C(GxEPD2_213_Z98c)> display(GxEPD2_213_Z98c(/*CS=10*/ SS, /*DC=*/ 9, /*RST=*/ 8, /*BUSY=*/ 7)); // GDEY0213Z98 122x250, SSD1680
//GxEPD2_3C<GxEPD2_266c, MAX_HEIGHT_3C(GxEPD2_266c)> display(GxEPD2_266c(/*CS=10*/ SS, /*DC=*/ 9, /*RST=*/ 8, /*BUSY=*/ 7)); // GDEY0266Z90 152x296, SSD1680
//GxEPD2_3C<GxEPD2_270c, MAX_HEIGHT_3C(GxEPD2_270c)> display(GxEPD2_270c(/*CS=10*/ SS, /*DC=*/ 9, /*RST=*/ 8, /*BUSY=*/ 7)); // GDEW027C44 176x264, IL91874
//GxEPD2_3C<GxEPD2_290c, MAX_HEIGHT_3C(GxEPD2_290c)> display(GxEPD2_290c(/*CS=10*/ SS, /*DC=*/ 9, /*RST=*/ 8, /*BUSY=*/ 7)); // GDEW029Z10 128x296, UC8151 (IL0373)
//GxEPD2_3C<GxEPD2_290_Z13c, MAX_HEIGHT_3C(GxEPD2_290_Z13c)> display(GxEPD2_290_Z13c(/*CS=10*/ SS, /*DC=*/ 9, /*RST=*/ 8, /*BUSY=*/ 7)); // GDEH029Z13 128x296, UC8151D
//GxEPD2_3C<GxEPD2_290_C90c, MAX_HEIGHT_3C(GxEPD2_290_C90c)> display(GxEPD2_290_C90c(/*CS=10*/ SS, /*DC=*/ 9, /*RST=*/ 8, /*BUSY=*/ 7)); // GDEM029C90 128x296, SSD1680
//GxEPD2_3C<GxEPD2_420c, MAX_HEIGHT_3C(GxEPD2_420c)> display(GxEPD2_420c(/*CS=10*/ SS, /*DC=*/ 9, /*RST=*/ 8, /*BUSY=*/ 7)); // GDEW042Z15 400x300, UC8176 (IL0398)
//GxEPD2_3C<GxEPD2_420c_Z21, MAX_HEIGHT_3C(GxEPD2_420c_Z21)> display(GxEPD2_420c_Z21(/*CS=10*/ SS, /*DC=*/ 9, /*RST=*/ 8, /*BUSY=*/ 7)); // GDEQ042Z21 400x300, UC8276
//GxEPD2_3C<GxEPD2_583c, MAX_HEIGHT_3C(GxEPD2_583c)> display(GxEPD2_583c(/*CS=10*/ SS, /*DC=*/ 9, /*RST=*/ 8, /*BUSY=*/ 7)); // GDEW0583Z21 600x448, UC8179 (IL0371)
//GxEPD2_3C<GxEPD2_583c_Z83, MAX_HEIGHT_3C(GxEPD2_583c_Z83)> display(GxEPD2_583c_Z83(/*CS=10*/ SS, /*DC=*/ 9, /*RST=*/ 8, /*BUSY=*/ 7)); // GDEW0583Z83 648x480, GD7965
//GxEPD2_3C<GxEPD2_750c, MAX_HEIGHT_3C(GxEPD2_750c)> display(GxEPD2_750c(/*CS=10*/ SS, /*DC=*/ 9, /*RST=*/ 8, /*BUSY=*/ 7)); // GDEW075Z09 640x384, UC8179 (IL0371)
//GxEPD2_3C<GxEPD2_750c_Z08, MAX_HEIGHT_3C(GxEPD2_750c_Z08)> display(GxEPD2_750c_Z08(/*CS=10*/ SS, /*DC=*/ 9, /*RST=*/ 8, /*BUSY=*/ 7)); // GDEW075Z08 800x480, GD7965
//GxEPD2_3C<GxEPD2_750c_Z90, MAX_HEIGHT_3C(GxEPD2_750c_Z90)> display(GxEPD2_750c_Z90(/*CS=10*/ SS, /*DC=*/ 9, /*RST=*/ 8, /*BUSY=*/ 7)); //GDEH075Z90 880x528, SSD1677
// 4-color e-paper
//GxEPD2_4C<GxEPD2_266c_GDEY0266F51H, MAX_HEIGHT_3C(GxEPD2_266c_GDEY0266F51H)> display(GxEPD2_266c_GDEY0266F51H(/*CS=10*/ SS, /*DC=*/ 9, /*RST=*/ 8, /*BUSY=*/ 7)); // GDEY0266F51H 184x360, JD79667 (FPC-H006 22.04.02)
//GxEPD2_4C<GxEPD2_290c_GDEY029F51H, MAX_HEIGHT_3C(GxEPD2_290c_GDEY029F51H)> display(GxEPD2_290c_GDEY029F51H(/*CS=10*/ SS, /*DC=*/ 9, /*RST=*/ 8, /*BUSY=*/ 7)); // GDEY029F51H 168x384, JD79667 (FPC-H004 22.03.24)
//GxEPD2_4C<GxEPD2_300c, MAX_HEIGHT_3C(GxEPD2_300c)> display(GxEPD2_300c(/*CS=10*/ SS, /*DC=*/ 9, /*RST=*/ 8, /*BUSY=*/ 7)); // Waveshare 3.00" 4-color
//GxEPD2_4C<GxEPD2_420c_GDEY0420F51, MAX_HEIGHT_3C(GxEPD2_420c_GDEY0420F51)> display(GxEPD2_420c_GDEY0420F51(/*CS=10*/ SS, /*DC=*/ 9, /*RST=*/ 8, /*BUSY=*/ 7)); // GDEY0420F51 400x300, HX8717 (no inking)
//GxEPD2_4C <GxEPD2_437c, MAX_HEIGHT_3C(GxEPD2_437c)> display(GxEPD2_437c(/*CS=10*/ SS, /*DC=*/ 9, /*RST=*/ 8, /*BUSY=*/ 7)); // Waveshare 4.37" 4-color
// 7-color e-paper
//GxEPD2_7C<GxEPD2_565c, MAX_HEIGHT_7C(GxEPD2_565c)> display(GxEPD2_565c(/*CS=10*/ SS, /*DC=*/ 9, /*RST=*/ 8, /*BUSY=*/ 7)); // Waveshare 5.65" 7-color

// Waveshare 12.48 b/w SPI display board and frame or Good Display 12.48 b/w panel GDEW1248T3
// general constructor for use with standard SPI pins, default SCK, MISO and MOSI, for UNO on UNO connectors
//GxEPD2_BW < GxEPD2_1248, MAX_HEIGHT(GxEPD2_1248)>
//display(GxEPD2_1248(/*cs_m1=*/ 2, /*cs_s1=*/ 3, /*cs_m2=*/ A4, /*cs_s2=*/ A0, /*dc1=*/ 6, /*dc2=*/ A3, /*rst1=*/ 5, /*rst2=*/ A2,
//                               /*busy_m1=*/ 4, /*busy_s1=*/ 7, /*busy_m2=*/ A1, /*busy_s2=*/ A5));
#undef MAX_DISPLAY_BUFFER_SIZE
#undef MAX_HEIGHT
#undef MAX_HEIGHT_3C
#undef MAX_HEIGHT_7C
#endif
