gitberthe/BertheVario213/BertheVario213PlatformIO/src/VarioBeep/CVarioBeep.cpp

////////////////////////////////////////////////////////////////////////////////
/// \file CVarioBeep.cpp
///
/// \brief
///
/// \date creation     : 04/03/2024
/// \date modification : 22/03/2025
///

#include "../BertheVario213.h"

///////////////////////////////////////////////////////////////////////////////
/// \brief
void CVarioBeep::InitSpeaker()
{
//pinMode(PIN_AUDIO_AMP_ENA,OUTPUT);
//digitalWrite(PIN_AUDIO_AMP_ENA,HIGH);
//digitalWrite(PIN_AUDIO_AMP_ENA,LOW);

/*ESP32PWM::allocateTimer(0);
ESP32PWM::allocateTimer(1);
ESP32PWM::allocateTimer(2);
ESP32PWM::allocateTimer(3);*/
}

////////////////////////////////////////////////////////////////////////////////
/// \brief Lance la tache de gestion du Gps
void CVarioBeep::LanceTacheVarioBeep()
{
#ifdef G_DEBUG
 Serial.println("lancement tache vario beep");
#endif
// tache de port serie
xTaskCreatePinnedToCore(TacheVarioBeep, "TaskBeep", VARIOBEEP_STACK_SIZE, this, VARIOBEEP_PRIORITY,NULL, VARIOBEEP_CORE);
}

////////////////////////////////////////////////////////////////////////////////
/// \brief Fonction static core 0 qui calcul la Vz et gere les beep.
void CVarioBeep::TacheVarioBeep(void *param)
{
delay(3000) ;
const float LowFreq = 1100 ;
const float MinFreq = 1200 ;
const float MaxFreq = 8000 ;
const float SeuilVzMin = g_GlobalVar.m_Config.m_vz_seuil_haut ;
while (g_GlobalVar.m_TaskArr[VARIOBEEP_NUM_TASK].m_Run)
    {
    // desactivation du son cause TMA
    bool NotActive = g_GlobalVar.m_ZonesAerAll.m_DansDessousUneZone == ZONE_DEDANS ||
                     g_GlobalVar.m_ZonesAerAll.m_LimiteZone == ZONE_LIMITE_ALTI ||
                     g_GlobalVar.m_ZonesAerAll.m_LimiteZone == ZONE_LIMITE_FRONTIERE ;

    #ifdef XC_TRACK
    if ( g_GlobalVar.m_Config.m_xc_track )
        {
        delay( 500 ) ;
        continue ;
        }
    #endif

    // si alarme zone desactivé => son vario active
    if ( !g_GlobalVar.m_BeepAttenteGVZone )
        NotActive = false ;

    // si son vario desactive
    if ( NotActive )
        {
        delay( 500 ) ;
        continue ;
        }

    float LocalVitVertMS = g_GlobalVar.m_VitVertMS ;
    //LocalVitVertMS = 4 ;
    //float LocalVitVertMS = g_GlobalVar.m_Config.m_vz_seuil_haut ;
    #ifdef SOUND_DEBUG
     LocalVitVertMS = 6 ;
    #endif

    // si degueulante
    if ( LocalVitVertMS <= g_GlobalVar.m_Config.m_vz_seuil_bas )
        {
        g_GlobalVar.beeper( LowFreq , 200 ) ;
        delay( 400 ) ;
        continue ;
        }
    // descente normale
    else if ( LocalVitVertMS > g_GlobalVar.m_Config.m_vz_seuil_bas && LocalVitVertMS < 0. )
        {
        delay( 500 ) ;
        continue ;
        }
    // zerotage en vol (pas au sol)
    else if ( LocalVitVertMS >= 0. && LocalVitVertMS < SeuilVzMin )
        {
        static int BeepZerotage = 0 ;
        BeepZerotage++ ;
        BeepZerotage = BeepZerotage%9 ;
        // si le vol a debuté
        if ( g_GlobalVar.m_DureeVolMin >= 0 )
            {
            int MidFreq = (LowFreq + MinFreq) / 2 ;
            if ( BeepZerotage == 0 || BeepZerotage == 3 )
                g_GlobalVar.beeper( MinFreq , 100 ) ;
            else if ( BeepZerotage == 1 || BeepZerotage == 4 )
                g_GlobalVar.beeper( MidFreq , 100 ) ;
            else if ( BeepZerotage == 2 || BeepZerotage == 5 )
                g_GlobalVar.beeper( LowFreq , 100 ) ;
            else
                delay( 500 ) ;
            }
        else
            delay( 100 ) ;
        continue ;
        }

    // coefficient de Vz
    float Coef01 = (LocalVitVertMS-SeuilVzMin) / g_GlobalVar.m_Config.m_vz_seuil_max ;
    if ( Coef01 > 1 )
        Coef01 = 1. ;
    if ( Coef01 < 0 )
        Coef01 = 0. ;

    // calcul frequence son
    float Freq = MinFreq + Coef01 * ( MaxFreq - MinFreq ) ;

    // calcul de la recurrence
    float RecurrenceMs = 700 - Coef01 * 550 ;

    // calcul de la largeur du beep
    float LargeurBeepMs = 100 ;

    // attente
    delay(RecurrenceMs) ;

    // emmission son
    g_GlobalVar.beeper( Freq, LargeurBeepMs ) ;
    }

g_GlobalVar.m_TaskArr[VARIOBEEP_NUM_TASK].m_Stopped = true ;
while( true )
    vTaskDelete(NULL) ;
}
