gitberthe/BertheVario213/BertheVario213PlatformIO/src/SDCard/CSDCard.cpp

////////////////////////////////////////////////////////////////////////////////
/// \file CSDCard.cpp
///
/// \brief
///
/// \date creation     : 04/03/2024
/// \date modification : 16/02/2025
///

#include "../BertheVario213.h"

SPIClass SpiSdCard(HSPI);

////////////////////////////////////////////////////////////////////////////////
/// \brief Initialise la carte SD
void CSDCard::InitSDCard()
{
//pinMode(SS, OUTPUT);
delay( 200 ) ;
SpiSdCard.begin(SDCARD_SCK_PIN, SDCARD_MISO_PIN, SDCARD_MOSI_PIN, SDCARD_CS_PIN);
delay( 200 ) ;
if ( !SD.begin(SDCARD_CS_PIN, SpiSdCard) )
    {
    #ifdef G_DEBUG
     Serial.println("SDCard initialization failed!");
    #endif

    #ifndef MS5611_DEBUG
     //CGlobalVar::Reboot() ;
    #endif
     CGlobalVar::BeepError( false ) ;
    }
delay( 100 ) ;
}

////////////////////////////////////////////////////////////////////////////////
/// \brief liste des fichiers IGC avec leur temps respectif en secondes
void CSDCard::ListeIgc( std::vector<std::string> & VecNomIgc , std::vector<float> & VecTempsIgc )
{
// raz vecteur in out
VecNomIgc.clear() ;
VecTempsIgc.clear() ;

/*// ouverture carte
File root = SD.open("/");
if(!root)
    {
    Serial.println("Failed to open directory");
    return;
    }

if(!root.isDirectory())
    {
    Serial.println("Not a directory");
    return;
    }

// pour tous les fichier
File file = root.openNextFile();
while(file)
    {
    if(file.isDirectory())
        {
        //Serial.print("  DIR : ");
        //Serial.println(file.name());
        //if(levels){
            //listDir(fs, file.name(), levels -1);
            //}
        }
    else
        {
        // nom et taille
        VecNomIgc.push_back(file.name()) ;
        VecTempsIgc.push_back(((float)file.size()/36)) ;
        }
    file = root.openNextFile();
    }*/

// lecture histo
g_GlobalVar.m_HistoVol.LectureFichiers() ;

// remplissage vecteurs
for ( int ii = 0 ; ii < g_GlobalVar.m_HistoVol.m_HistoDir.size() ; ii++ )
    {
    VecNomIgc.push_back( g_GlobalVar.m_HistoVol.m_HistoDir[ii].m_NomIgc ) ;
    VecTempsIgc.push_back( g_GlobalVar.m_HistoVol.m_HistoDir[ii].m_TempsDeVol ) ;
    }

// delete histo dir
g_GlobalVar.m_HistoVol.m_HistoDir.clear() ;
}

////////////////////////////////////////////////////////////////////////////////
/// \brief Archive tous les fichiers IGC à la racine de la carte ayant un historique
/// d'au moins une minute.
void CSDCard::ArchiveIgc()
{
// lecture des fichiers historiques
g_GlobalVar.m_HistoVol.LectureFichiers() ;

const std::vector<CHistoVol> & VecHisto = g_GlobalVar.m_HistoVol.m_HistoDir ;

for ( int iv = 0 ; iv < VecHisto.size() ; iv++ )
    {
    const CHistoVol & HistoVol =  VecHisto[iv] ;

    // nouveau nom de fichier
    char NomFchArch[50] = "/arch" ;
    sprintf( NomFchArch ,"/arch/%04d/%s", (int)HistoVol.m_AnneeDuVol, HistoVol.m_NomIgc ) ;

    // creation nouvelle directorie annee
    char NomDirArch[50] ;
    sprintf( NomDirArch , "/arch/%04d" , (int)HistoVol.m_AnneeDuVol ) ;
    SD.mkdir( "/arch" ) ;
    SD.mkdir( NomDirArch ) ;

    // deplacement/destruction fichier
    if ( HistoVol.m_TempsDeVol < 1 )
        SD.remove( HistoVol.m_NomIgc ) ;
    else
        SD.rename( HistoVol.m_NomIgc , NomFchArch ) ;
    }


// destruction historique
g_GlobalVar.m_HistoVol.DeleteHisto() ;

// destruction des petits fichiers
File RootDir = SD.open("/") ;
if ( !RootDir )
    {
    Serial.println("Failed to open root dir");
    return;
    }

// pour toute la directorie
while( true )
    {
    // ouverture fichier
    File Fichier = RootDir.openNextFile() ;

    // si fin de liste
    if ( ! Fichier )
        break ;

    // si directorie
    if( Fichier.isDirectory() )
        {
        Fichier.close() ;
        continue ;
        }

    // si petit fichier
    if ( Fichier.size() < 37*30 )
       {
       std::string name = "/" ;
       name += Fichier.name() ;
       SD.remove( name.c_str() ) ;
       }

    Fichier.close() ;
    }


RootDir.close() ;
}
