gitberthe/BertheVario213/BertheVario213PlatformIO/src/Screen/CBoutons.h

////////////////////////////////////////////////////////////////////////////////
/// \file CBoutons.h
///
/// \brief
///
/// \date creation     : 09/03/2024
/// \date modification : 19/03/2025
///

#ifndef _BOUTONS_
#define _BOUTONS_

//#define DELAY_INTER_DOUBLE_APPUI    50
//#define DELAY_DOUBLE_APPUI          700
#define DELAY_APPUI_LONG            1500
#define DELAY_PURGE_LONG            2000
#define DELAY_ATTENTE_COURT          400

////////////////////////////////////////////////////////////////////////////////
/// \brief Permet l'utilisation des boutons. Scan 10hz avec beep.
class CBoutons
{
public :
    void InitButton() ;
    bool BoutonGauche() ;
    bool BoutonGaucheLong() ;
    //bool BoutonGaucheDoubleAppui() ;
    bool BoutonGaucheTousAppui() ;

    bool BoutonCentre() ;
    bool BoutonCentreLong() ;
    //bool BoutonCentreDoubleAppui() ;
    bool BoutonCentreTousAppui() ;

    bool BoutonDroit() ;
    bool BoutonDroitLong() ;
    //bool BoutonDroitDoubleAppui() ;
    bool BoutonDroitTousAppui() ;


    void RazBoutons() ;
    void RazBoutonDroit() ;
    void PurgeBoutons( unsigned long DelayMs )
            { m_DelayPurgeMs = DelayMs ; } ;
    void BootEffectue()
            { m_Boot = false ; } ;
    bool TestOta() ;

private :
    void TestReboot() ;

    bool m_Boot = true ;                ///< true jusqu'a la fin du boot pour eviter des boutons long

    bool m_BoutonGauche            = false ;
    bool m_BoutonGaucheLong        = false ;
    //bool m_BoutonGaucheDoubleAppui = false ;

    bool m_BoutonCentre            = false ;
    bool m_BoutonCentreLong        = false ;
    //bool m_BoutonCentreDoubleAppui = false ;

    bool m_BoutonDroit            = false ;
    bool m_BoutonDroitLong        = false ;
    //bool m_BoutonDroitDoubleAppui = false ;

    unsigned long m_DelayPurgeMs = 0 ;  ///< delay de purge des boutons en ms
    unsigned long m_DelayAttenteMs= 0 ; ///< delay d'attente avant nouvel appuy en ms



    static void TacheScanButton( void * param) ;
} ;

#endif
