gitberthe/BertheVario213/BertheVario213PlatformIO/src/GlobalVar/CMutex.cpp

////////////////////////////////////////////////////////////////////////////////
/// \file CMutex.cpp
///
/// \brief
///
/// \date creation     : 12/03/2024
/// \date modification : 12/03/2024
///

#include "../BertheVario213.h"

////////////////////////////////////////////////////////////////////////////////
/// \brief Init du mutex
CMutex::CMutex()
{
m_shared_var_mutex = xSemaphoreCreateMutex() ;
}

////////////////////////////////////////////////////////////////////////////////
/// \brief
void CMutex::PrendreMutex()
{
xSemaphoreTake(m_shared_var_mutex, portMAX_DELAY) ;
}

////////////////////////////////////////////////////////////////////////////////
/// \brief
void CMutex::RelacherMutex()
{
xSemaphoreGive(m_shared_var_mutex);
}
