gitberthe/BertheVario213/BertheVario213PlatformIO/src/Screen/CLocTermic.h

////////////////////////////////////////////////////////////////////////////////
/// \file CLocTermic.h
///
/// \brief
///
/// \date creation     : 14/03/2024
/// \date modification : 24/03/2024
///

#ifndef _LOCTERMIC_
#define _LOCTERMIC_

#define DistanceMaxMetres (9999)

////////////////////////////////////////////////////////////////////////////////
/// \brief Ihm de localisation de termic avec distance et direction.
class CLocTermic
{
public :
    void Affiche( float CapDeg , float DistMetres ) ;
} ;

#endif
